corygrant/dingoPDM/docs/images/DingoPDM_v7_1_Case.png

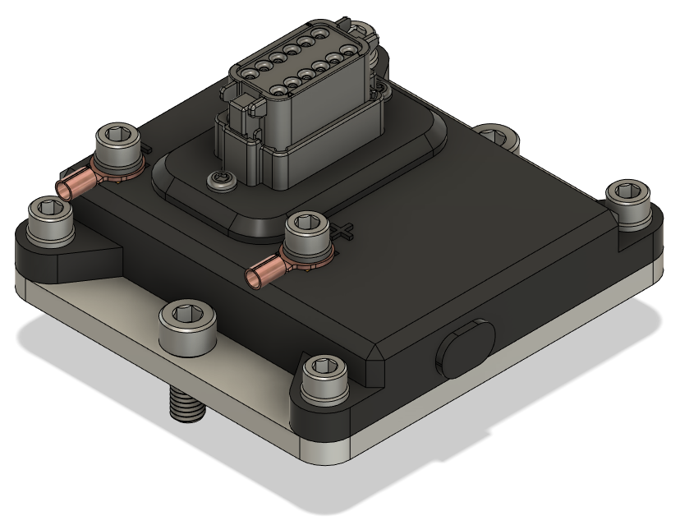
docs/images/DingoPDM_v7_1_Case.png
