corygrant/dingoPDM/docs/images/DingoPDM_v7_1_CaseBottom.png

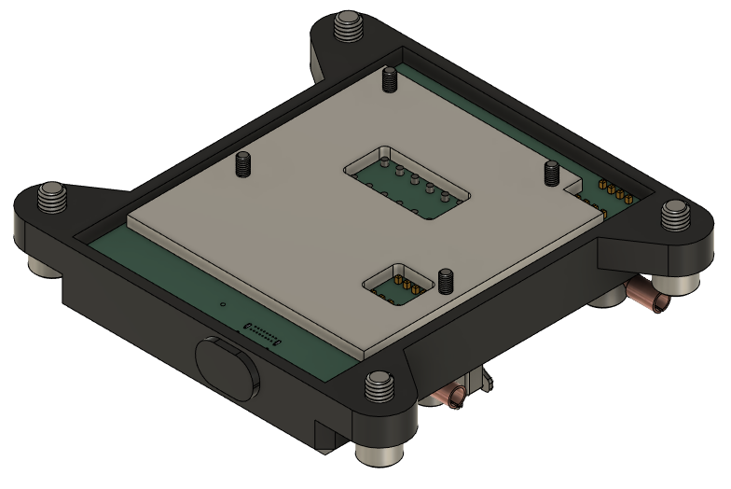
docs/images/DingoPDM_v7_1_CaseBottom.png
