corygrant/dingoPDM/docs/images/DingoPDMBottom_V7.png

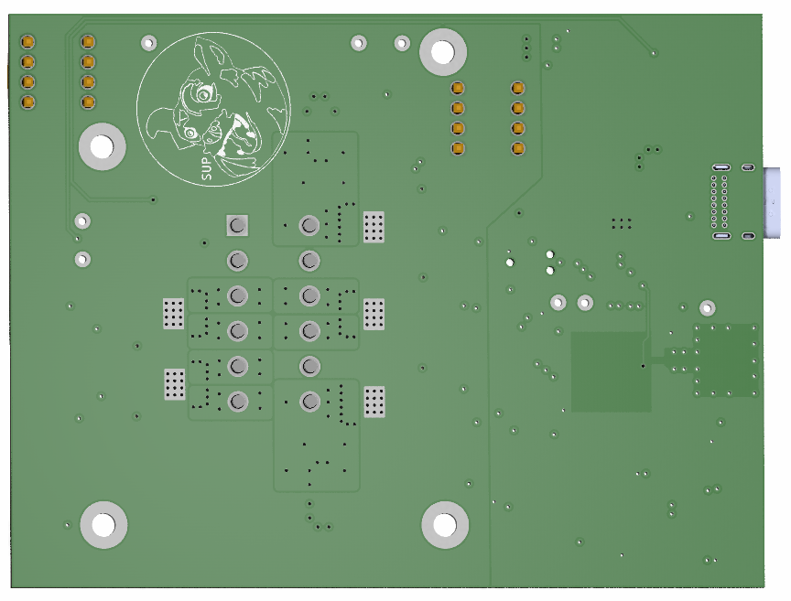
docs/images/DingoPDMBottom_V7.png
