corygrant/dingoPDM/docs/images/DingoPDMTop_V7_2.png

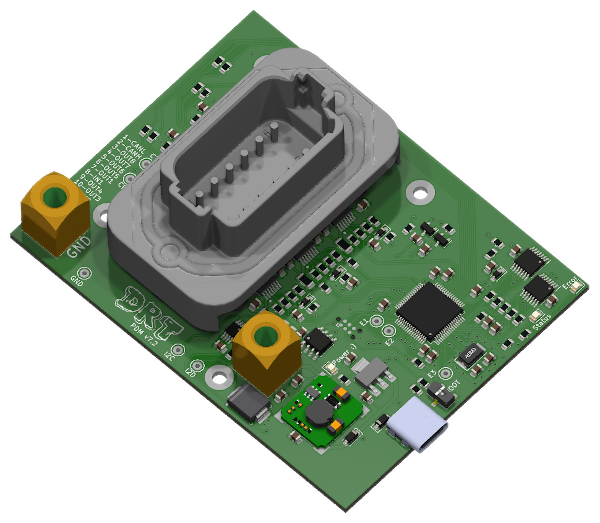
docs/images/DingoPDMTop_V7_2.png
