corygrant/dingoPDM/Export/V7.5/Case/Enclosure - paleppp/info.png

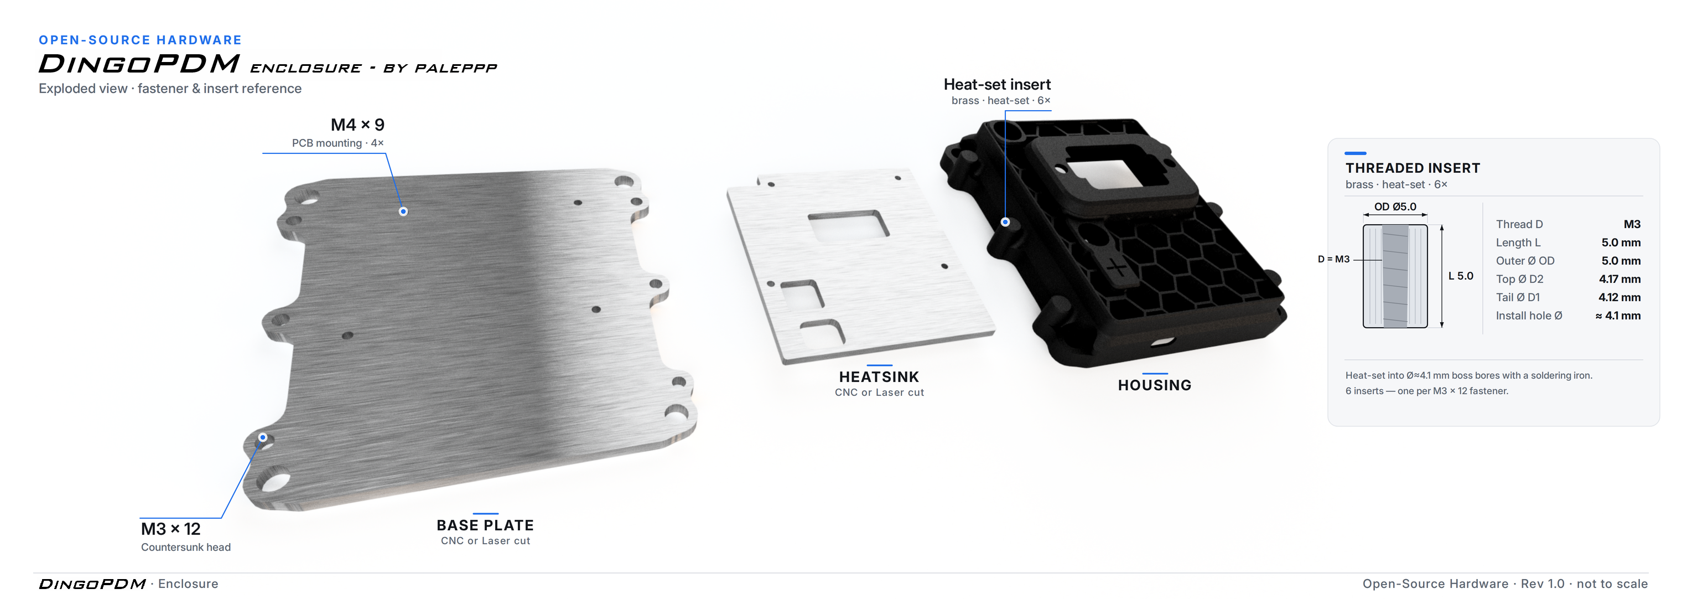
Export/V7.5/Case/Enclosure - paleppp/info.png
