corygrant/dingoPDM/DingoPDM/Models/User Library-DO-214AC SMA.STEP

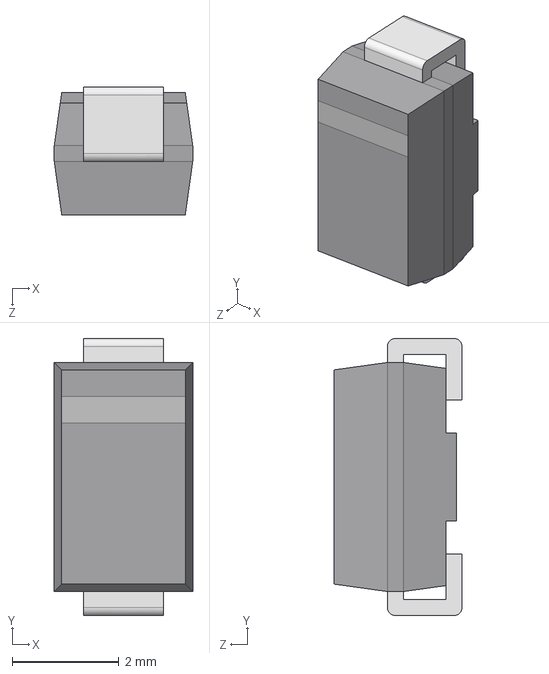
[picture p45: CAD file, 2023-09-12]
DingoPDM/Models/User Library-DO-214AC SMA.STEP
2.60 x 5.20 x 2.40 mm
