corygrant/dingoPDM/DingoPDM/Models/User Library-sot-223.STEP

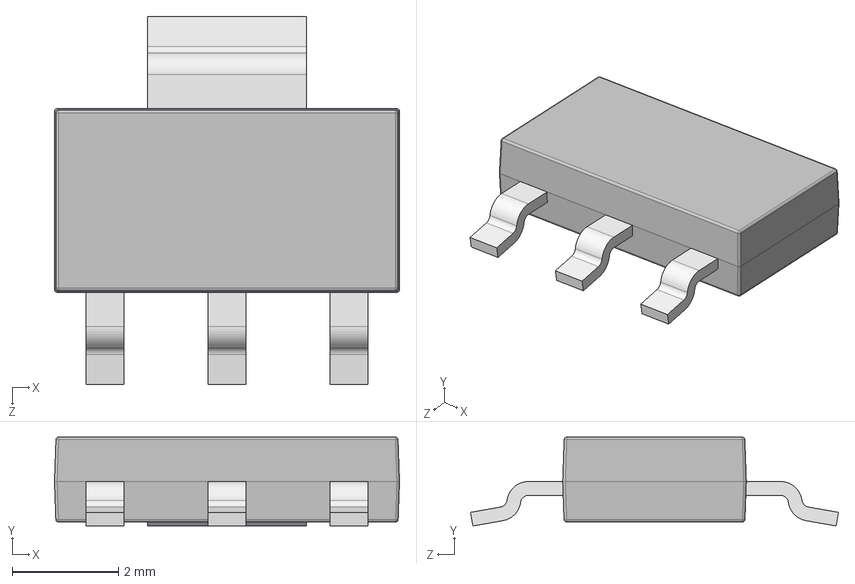
[picture p46: CAD file, 2023-09-12]
DingoPDM/Models/User Library-sot-223.STEP
6.50 x 1.67 x 6.93 mm
