corygrant/dingoPDM/DingoPDM/Models/USB4085-GF-A--3DModel-STEP-56544.STEP

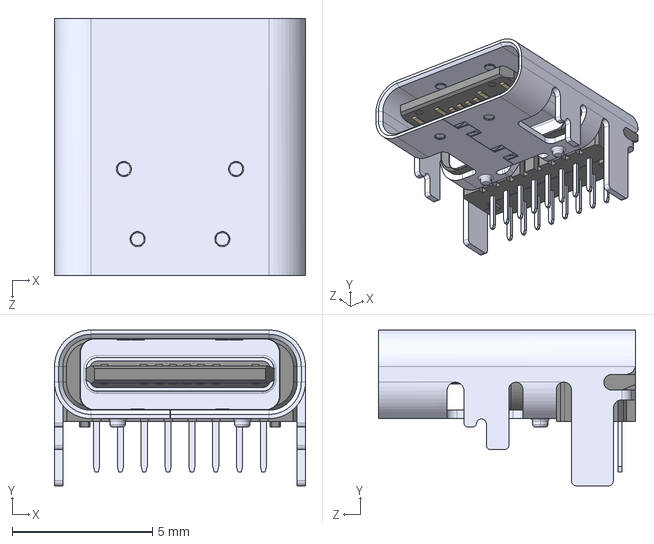
[picture p47: CAD file, 2023-09-12]
DingoPDM/Models/USB4085-GF-A--3DModel-STEP-56544.STEP
8.95 x 5.56 x 9.17 mm
