corygrant/dingoPDM/DingoPDM/Models/c-dt15-12pa-e-3d.stp

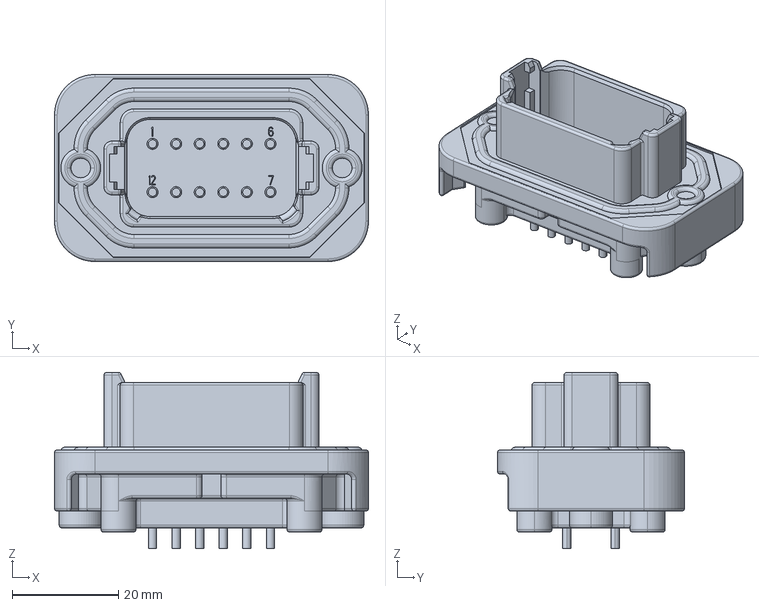
[picture p48: CAD file, 2023-09-12]
DingoPDM/Models/c-dt15-12pa-e-3d.stp
59.2 x 35.3 x 33.2 mm
