corygrant/dingoPDM/DingoPDM/Models/User Library-DO-214AB SMC.STEP

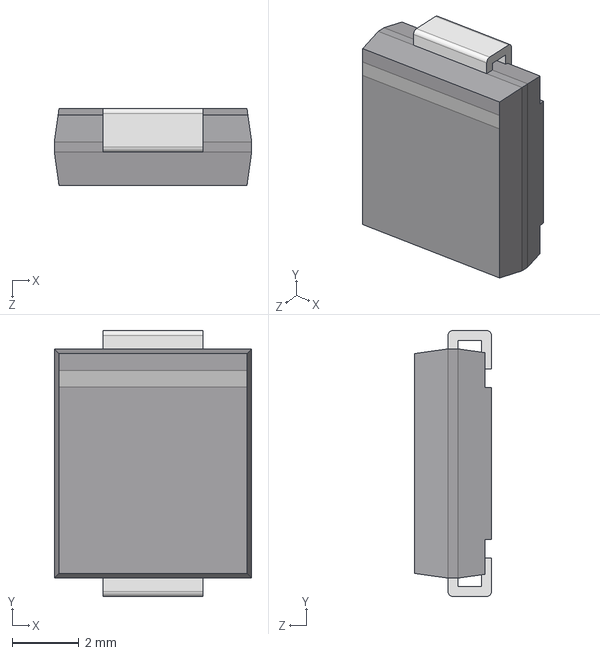
[picture p49: CAD file, 2023-09-12]
DingoPDM/Models/User Library-DO-214AB SMC.STEP
5.90 x 7.95 x 2.30 mm
