corygrant/dingoPDM/DingoPDM/Models/User Library-SOT23-3.step

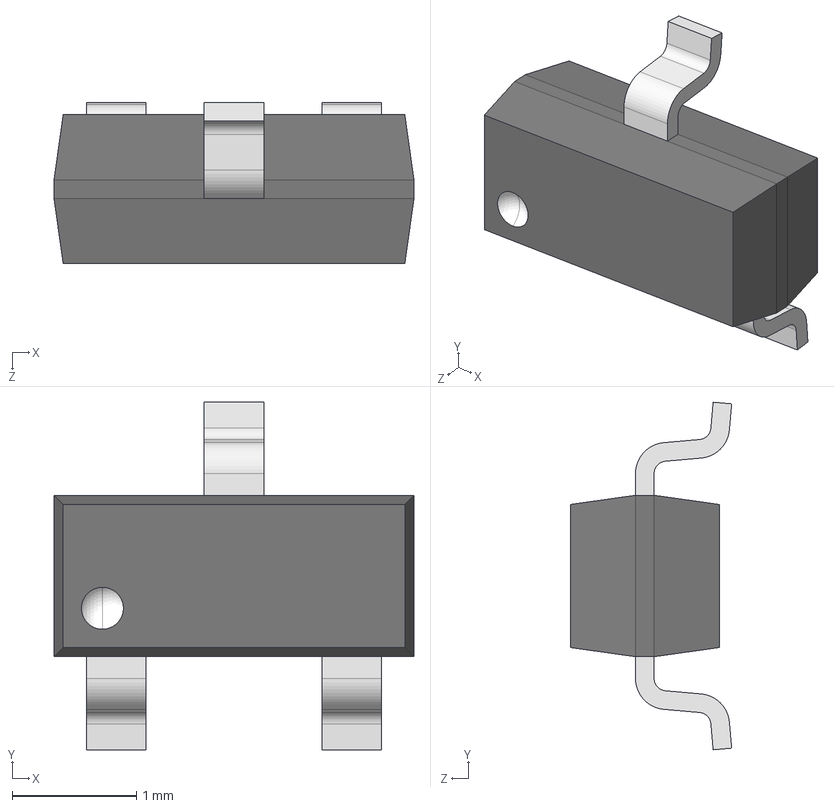
[picture p50: CAD file, 2023-09-12]
DingoPDM/Models/User Library-SOT23-3.step
2.90 x 2.80 x 1.30 mm
