corygrant/dingoPDM/Export/V7/DingoPDM_HW_V7_Dark.pdf

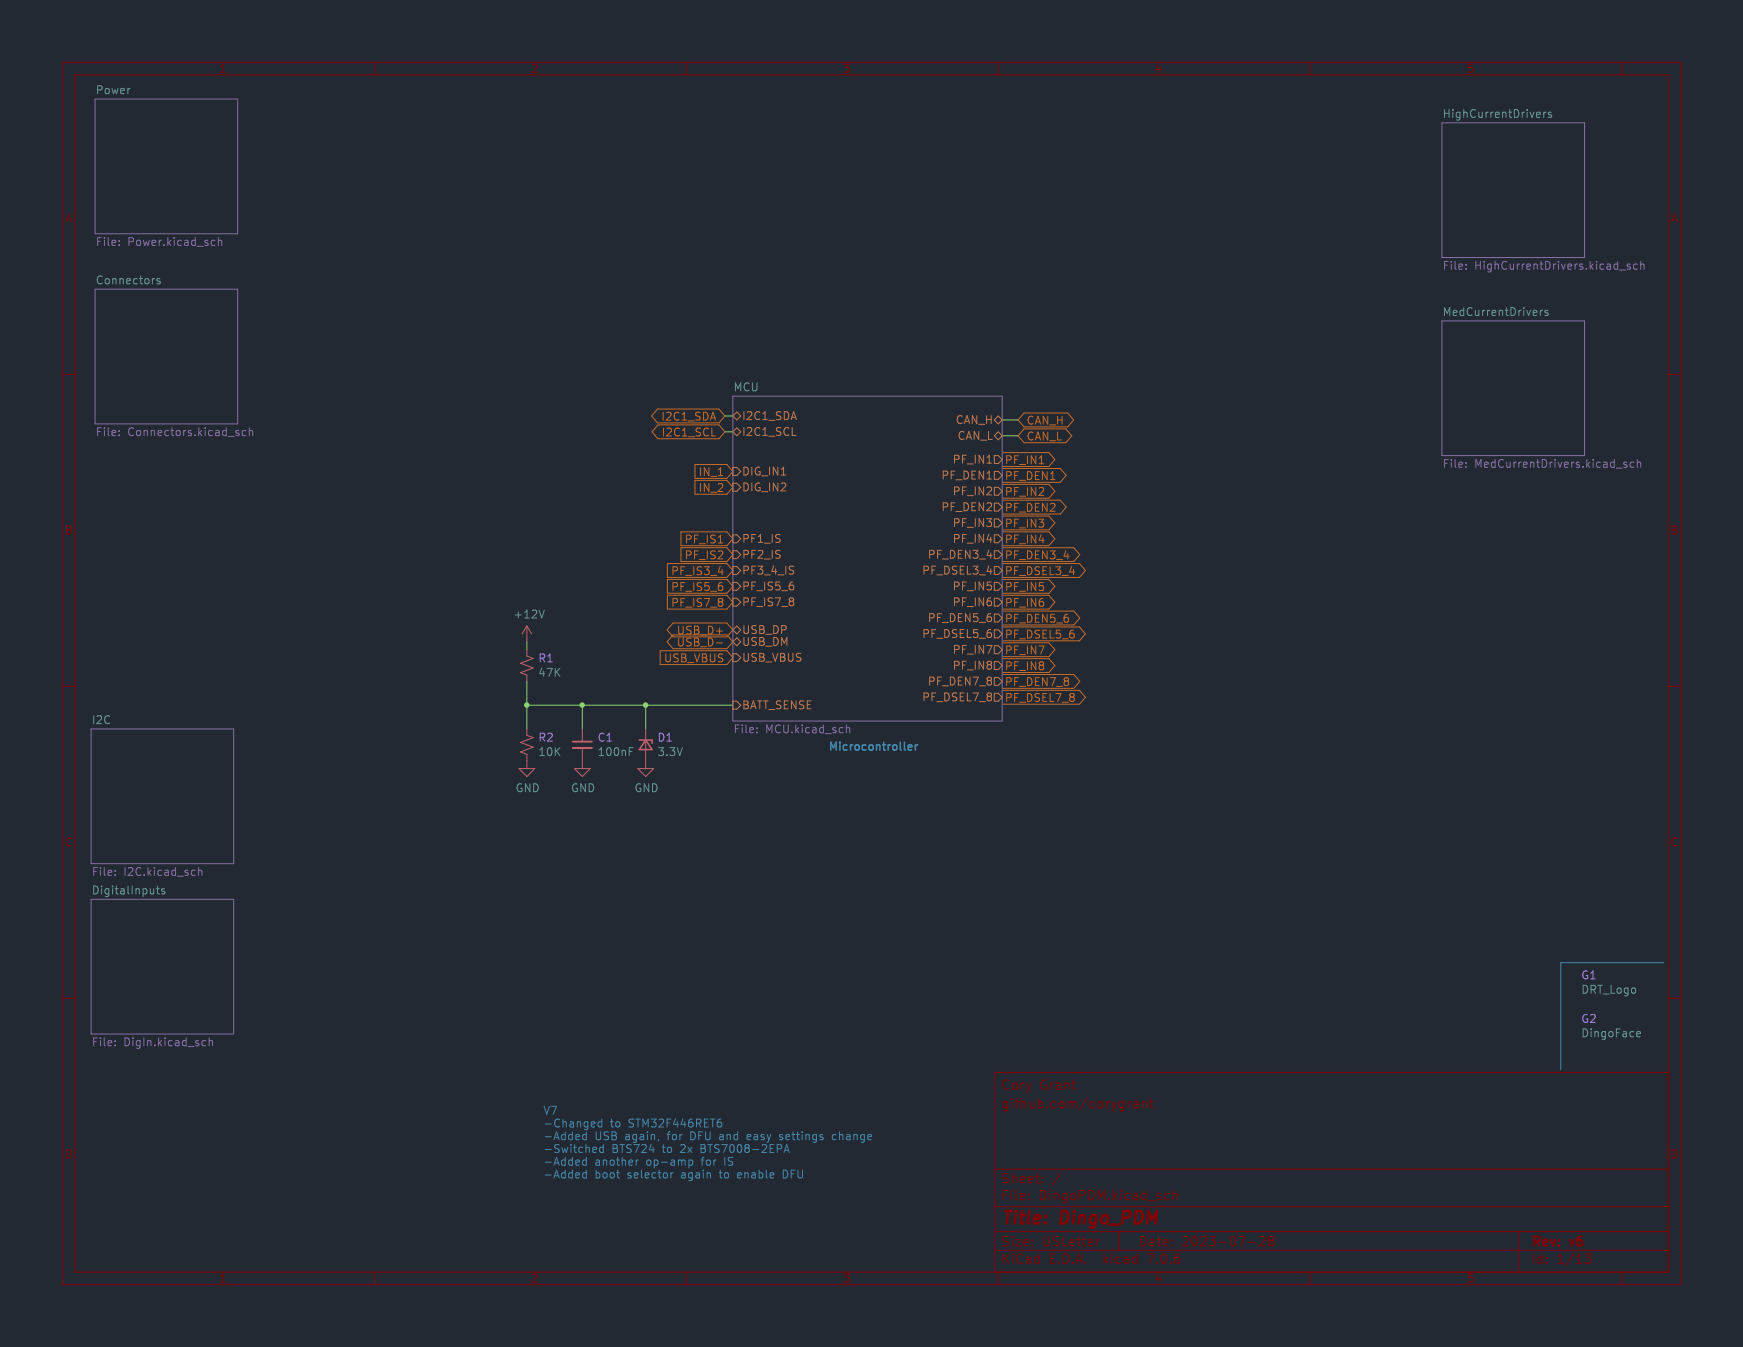
[picture p165: page 1]

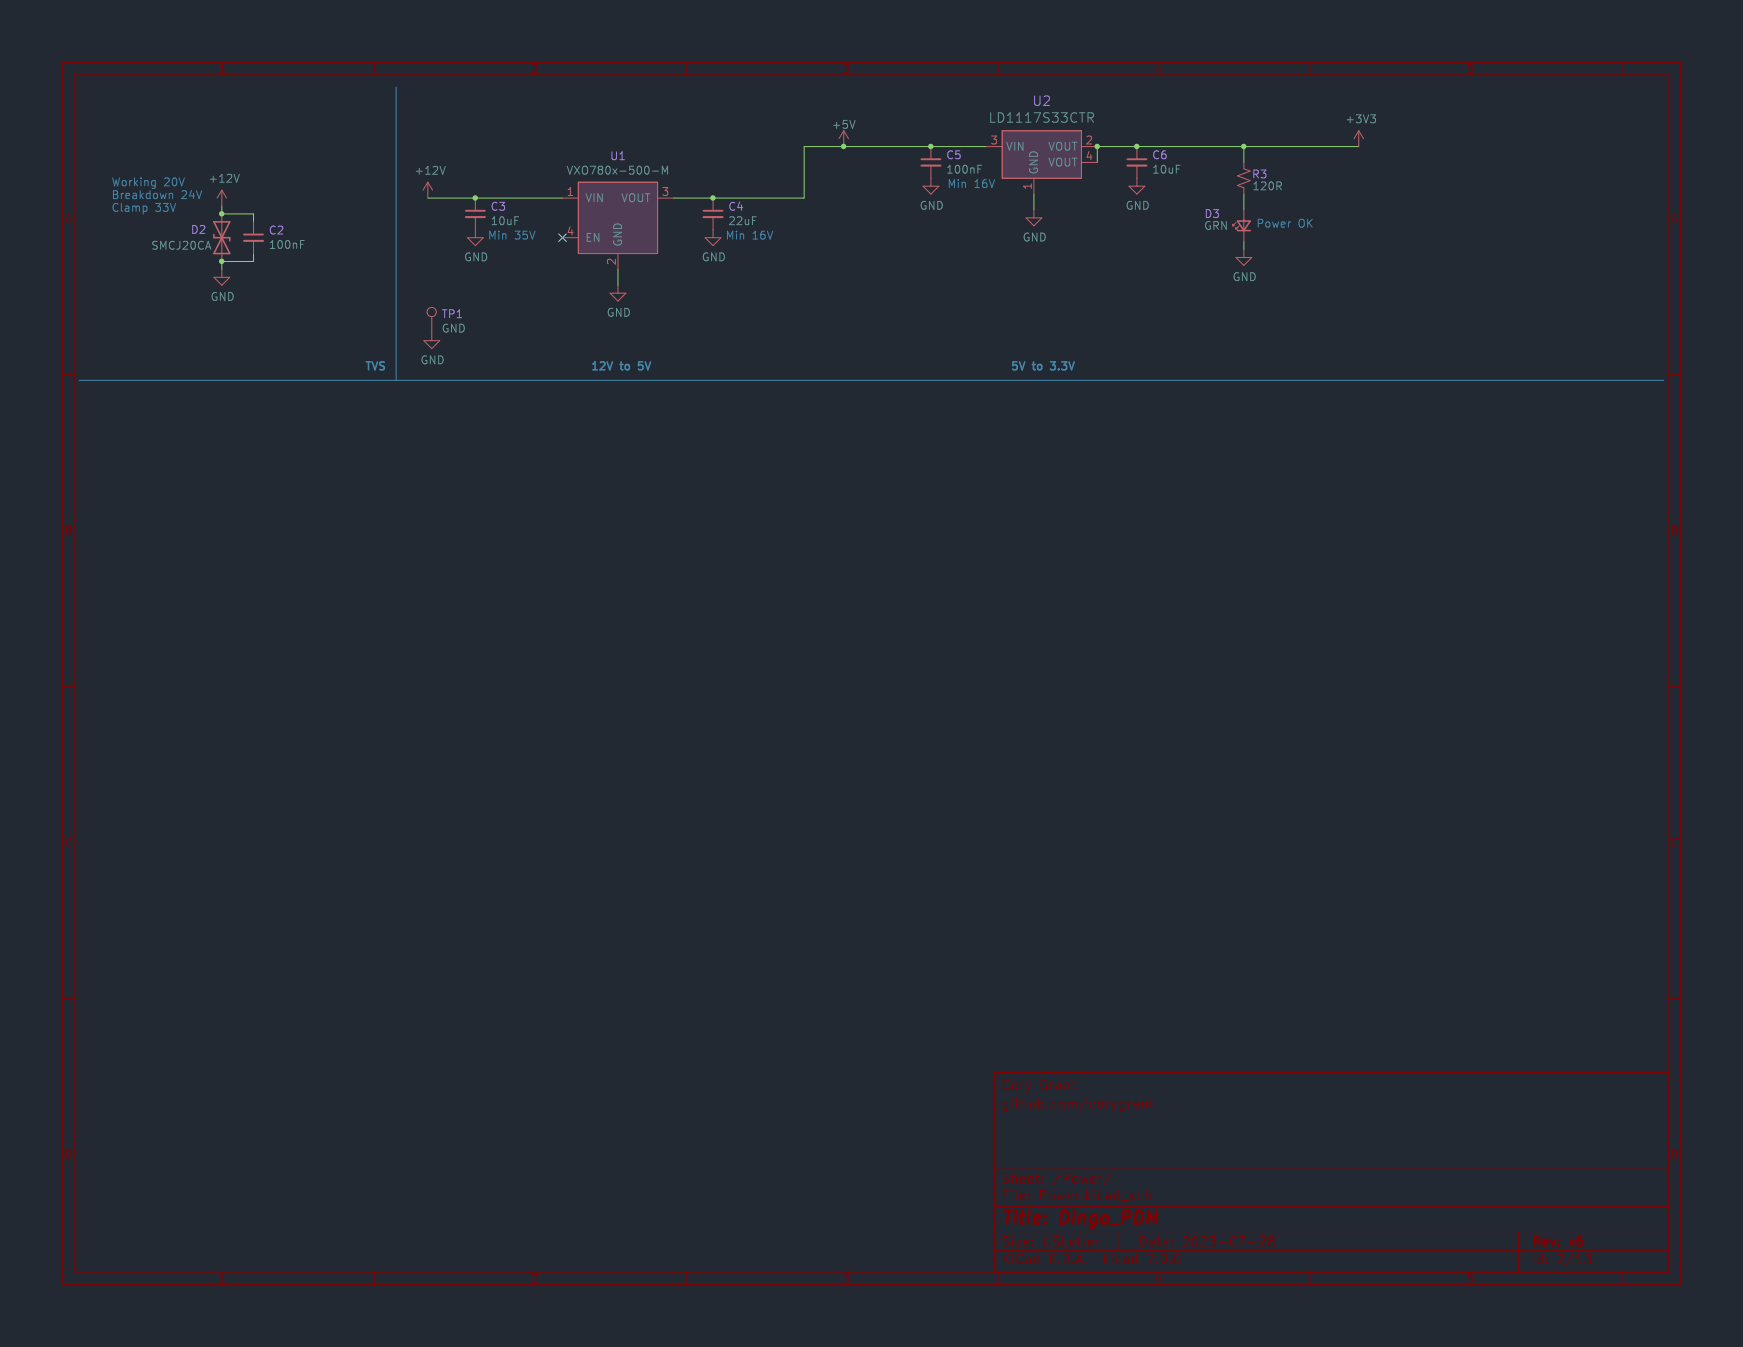
[picture p166: page 2]

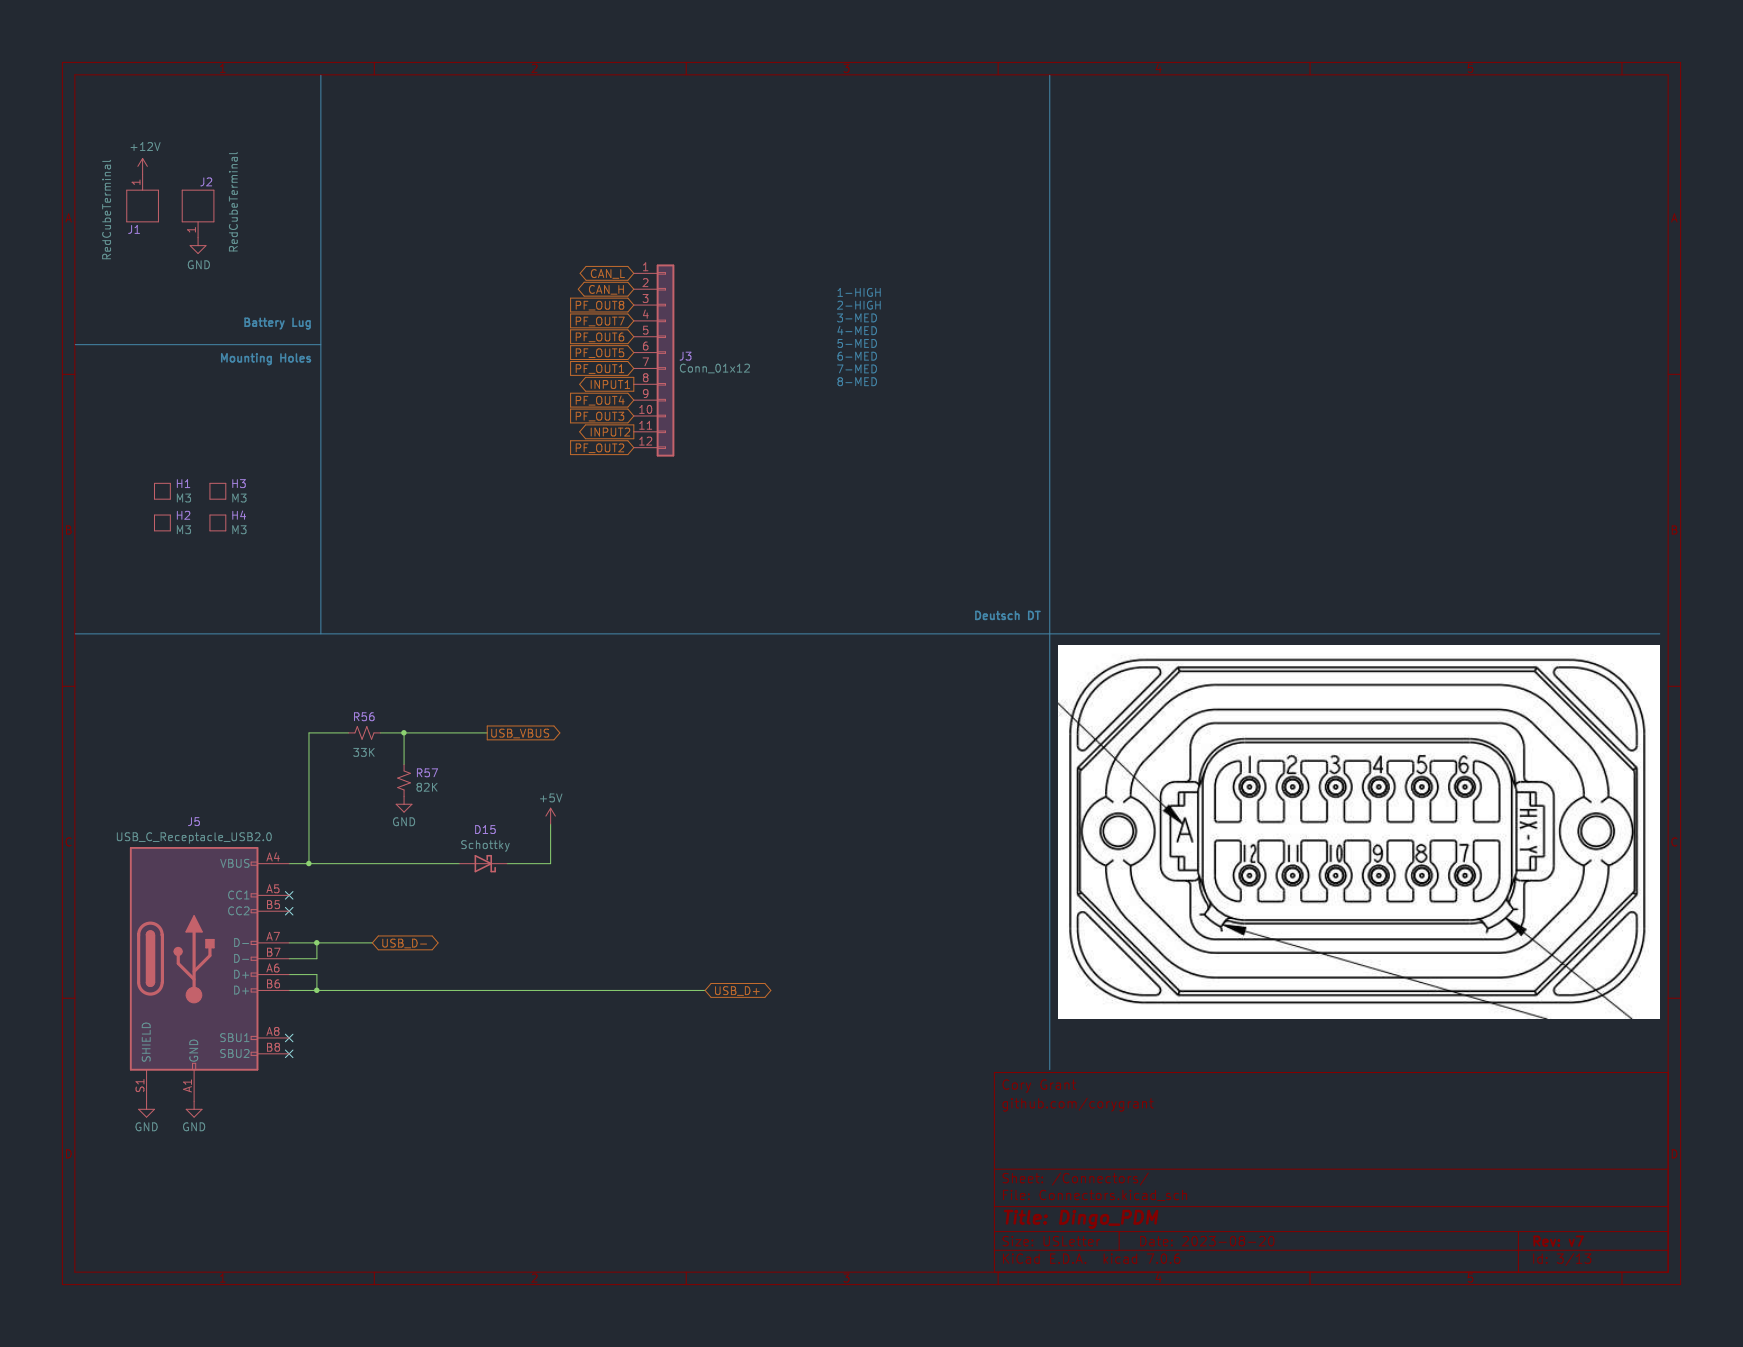
[picture p167: page 3]

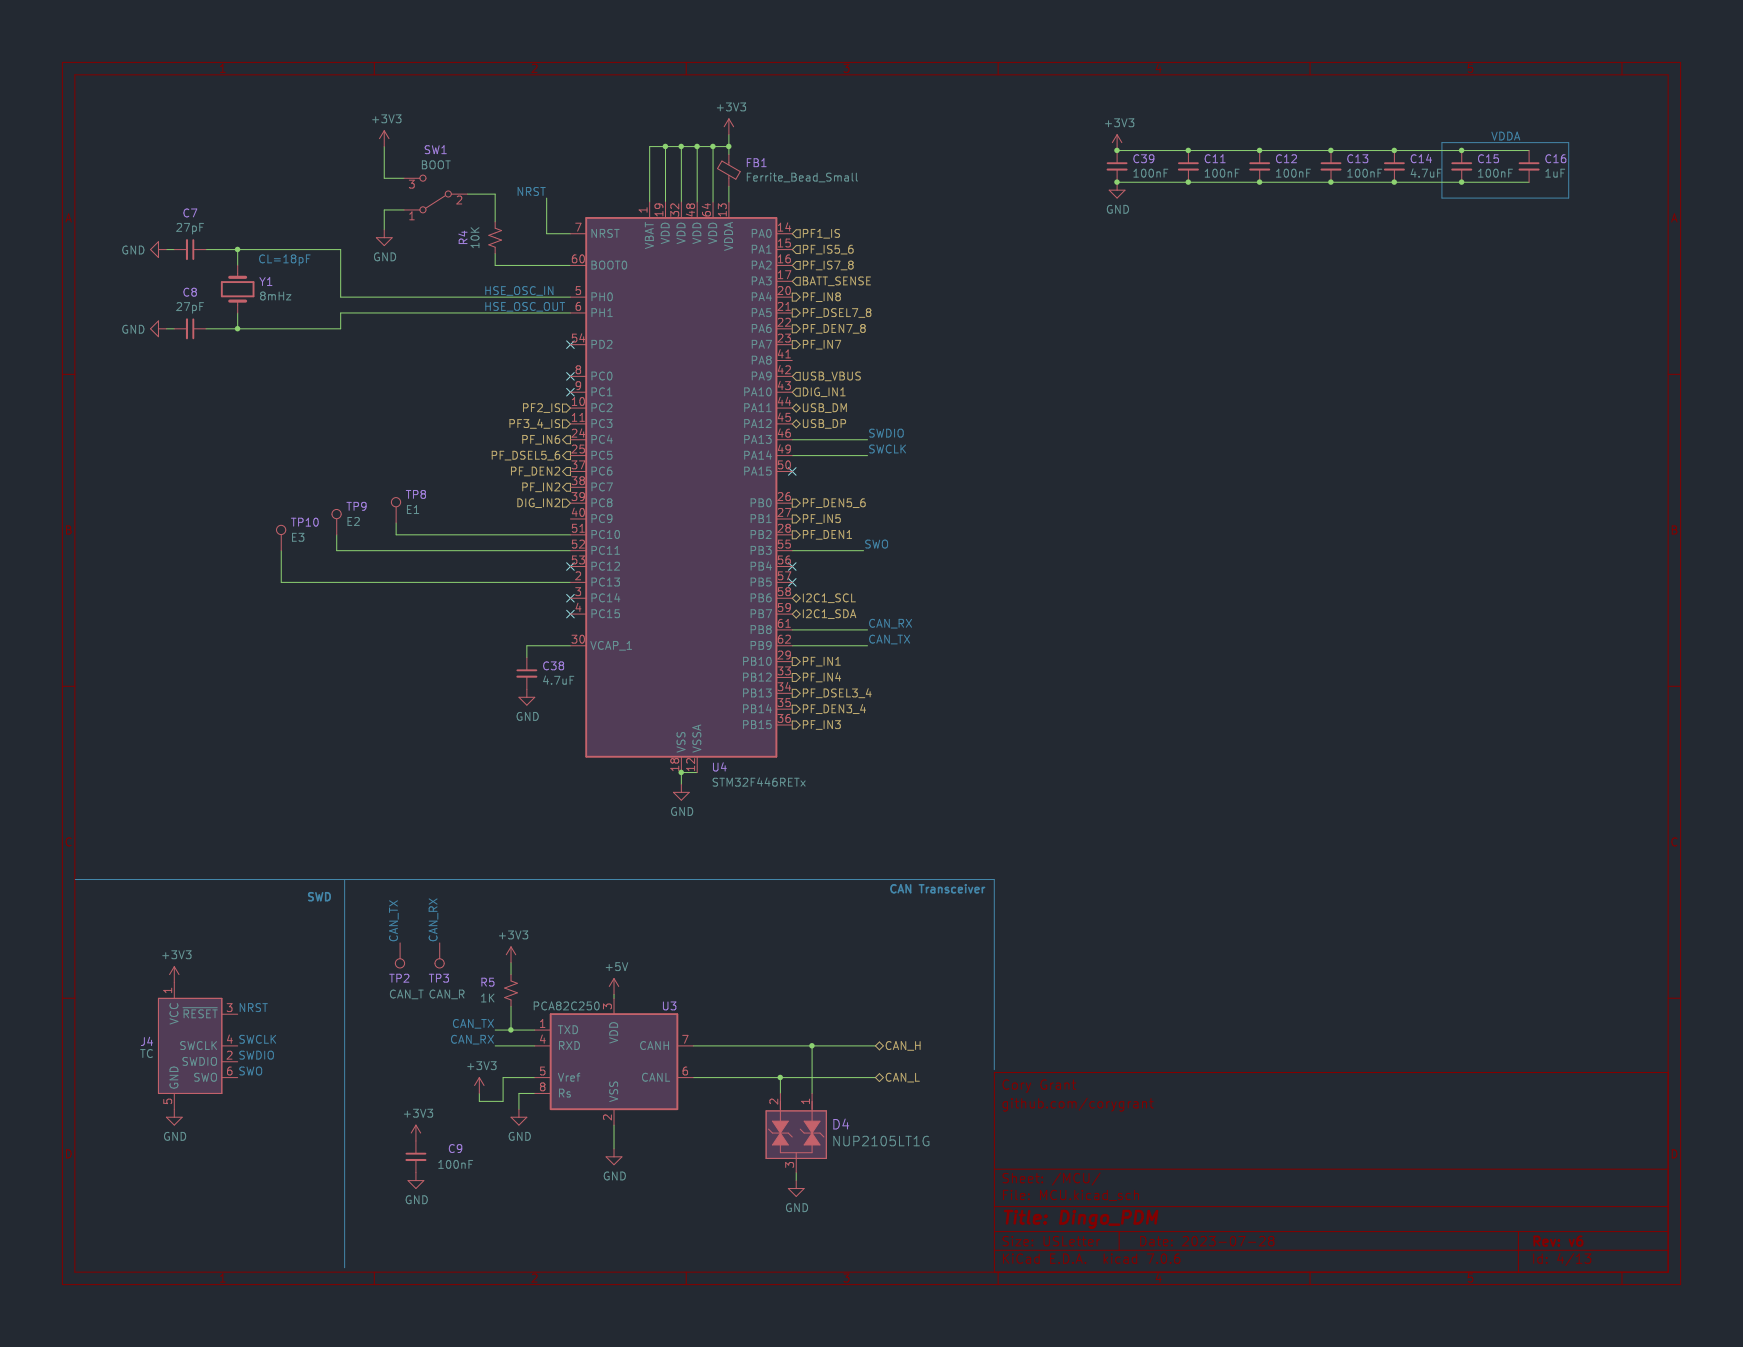
[picture p168: page 4]

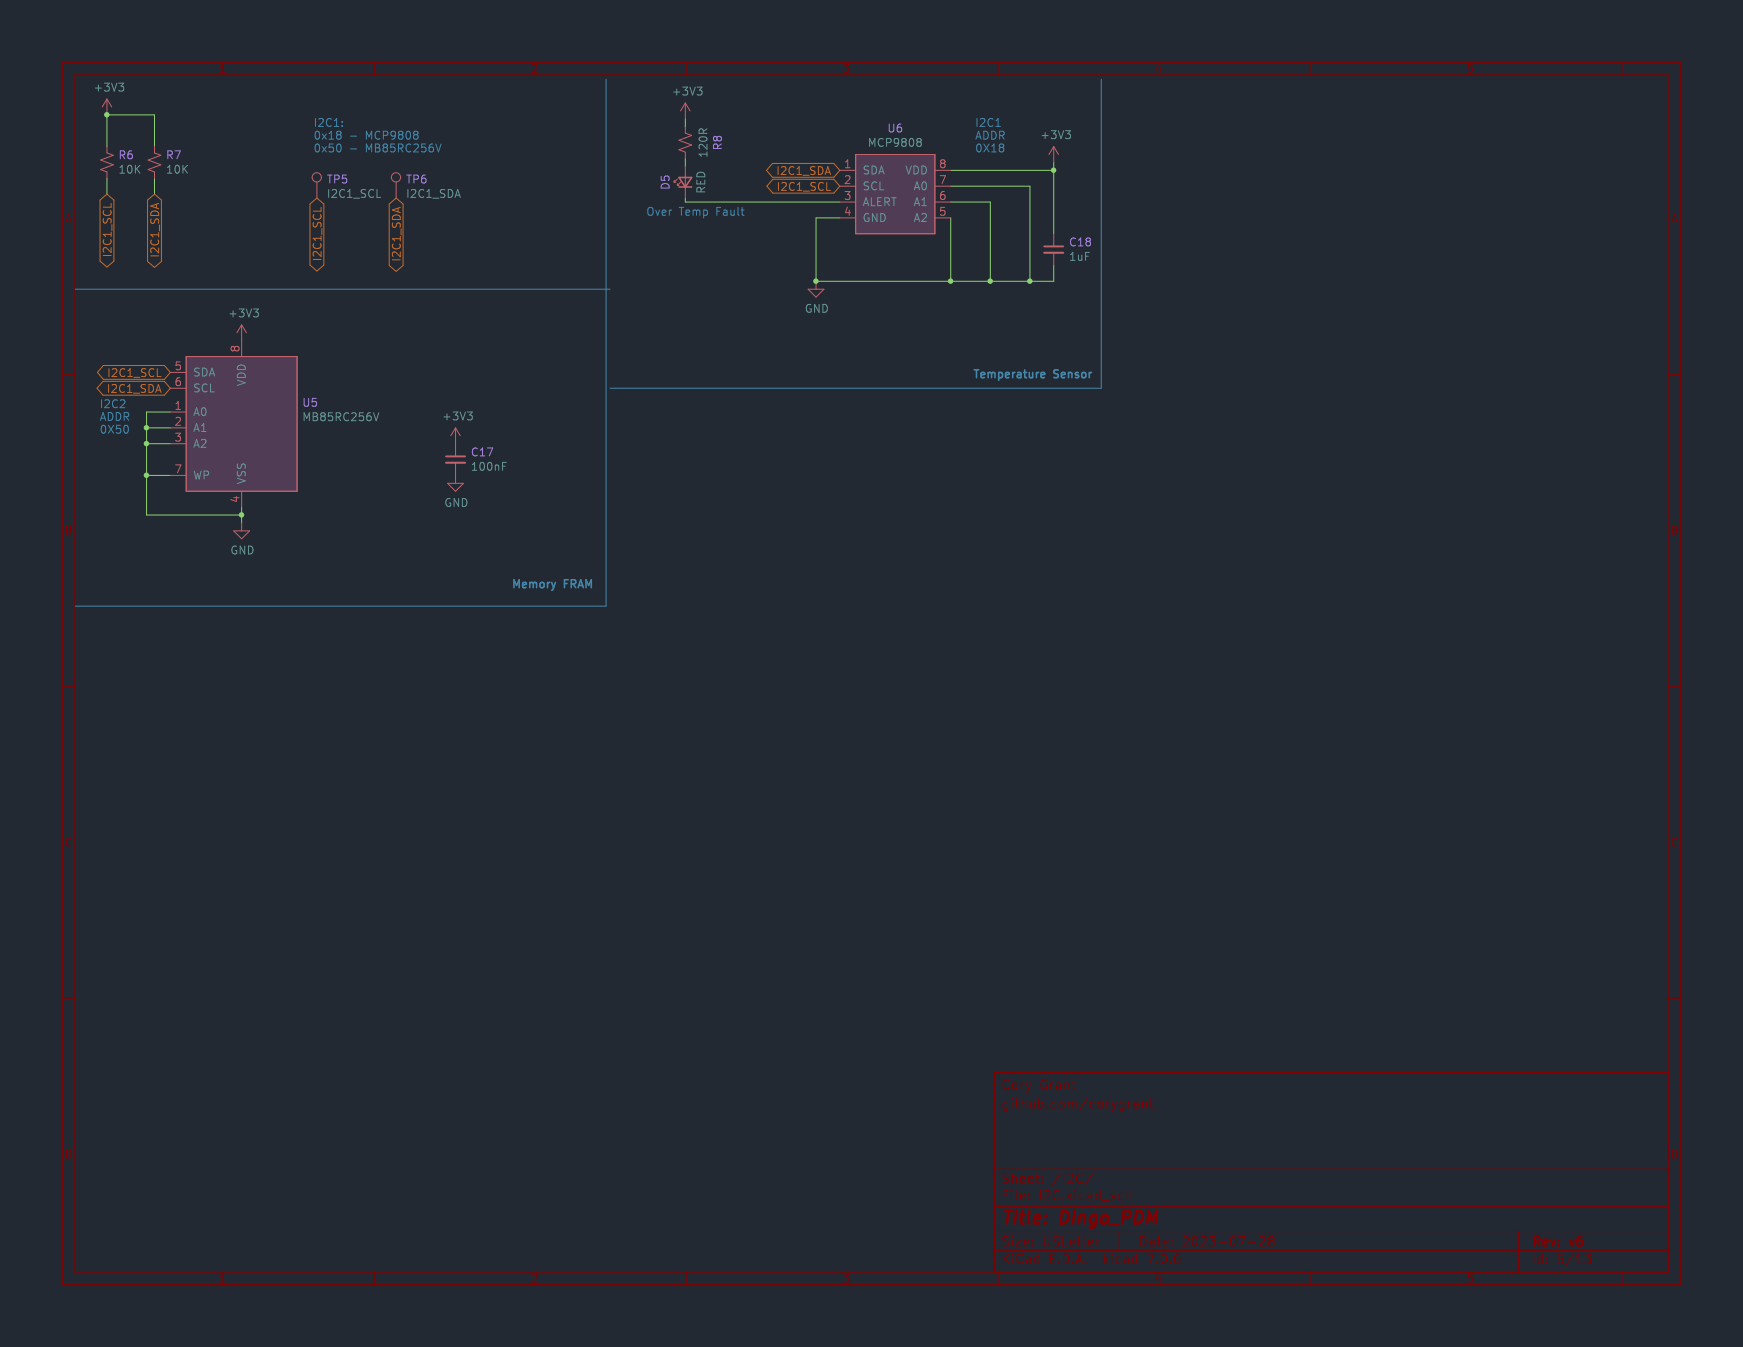
[picture p169: page 5]

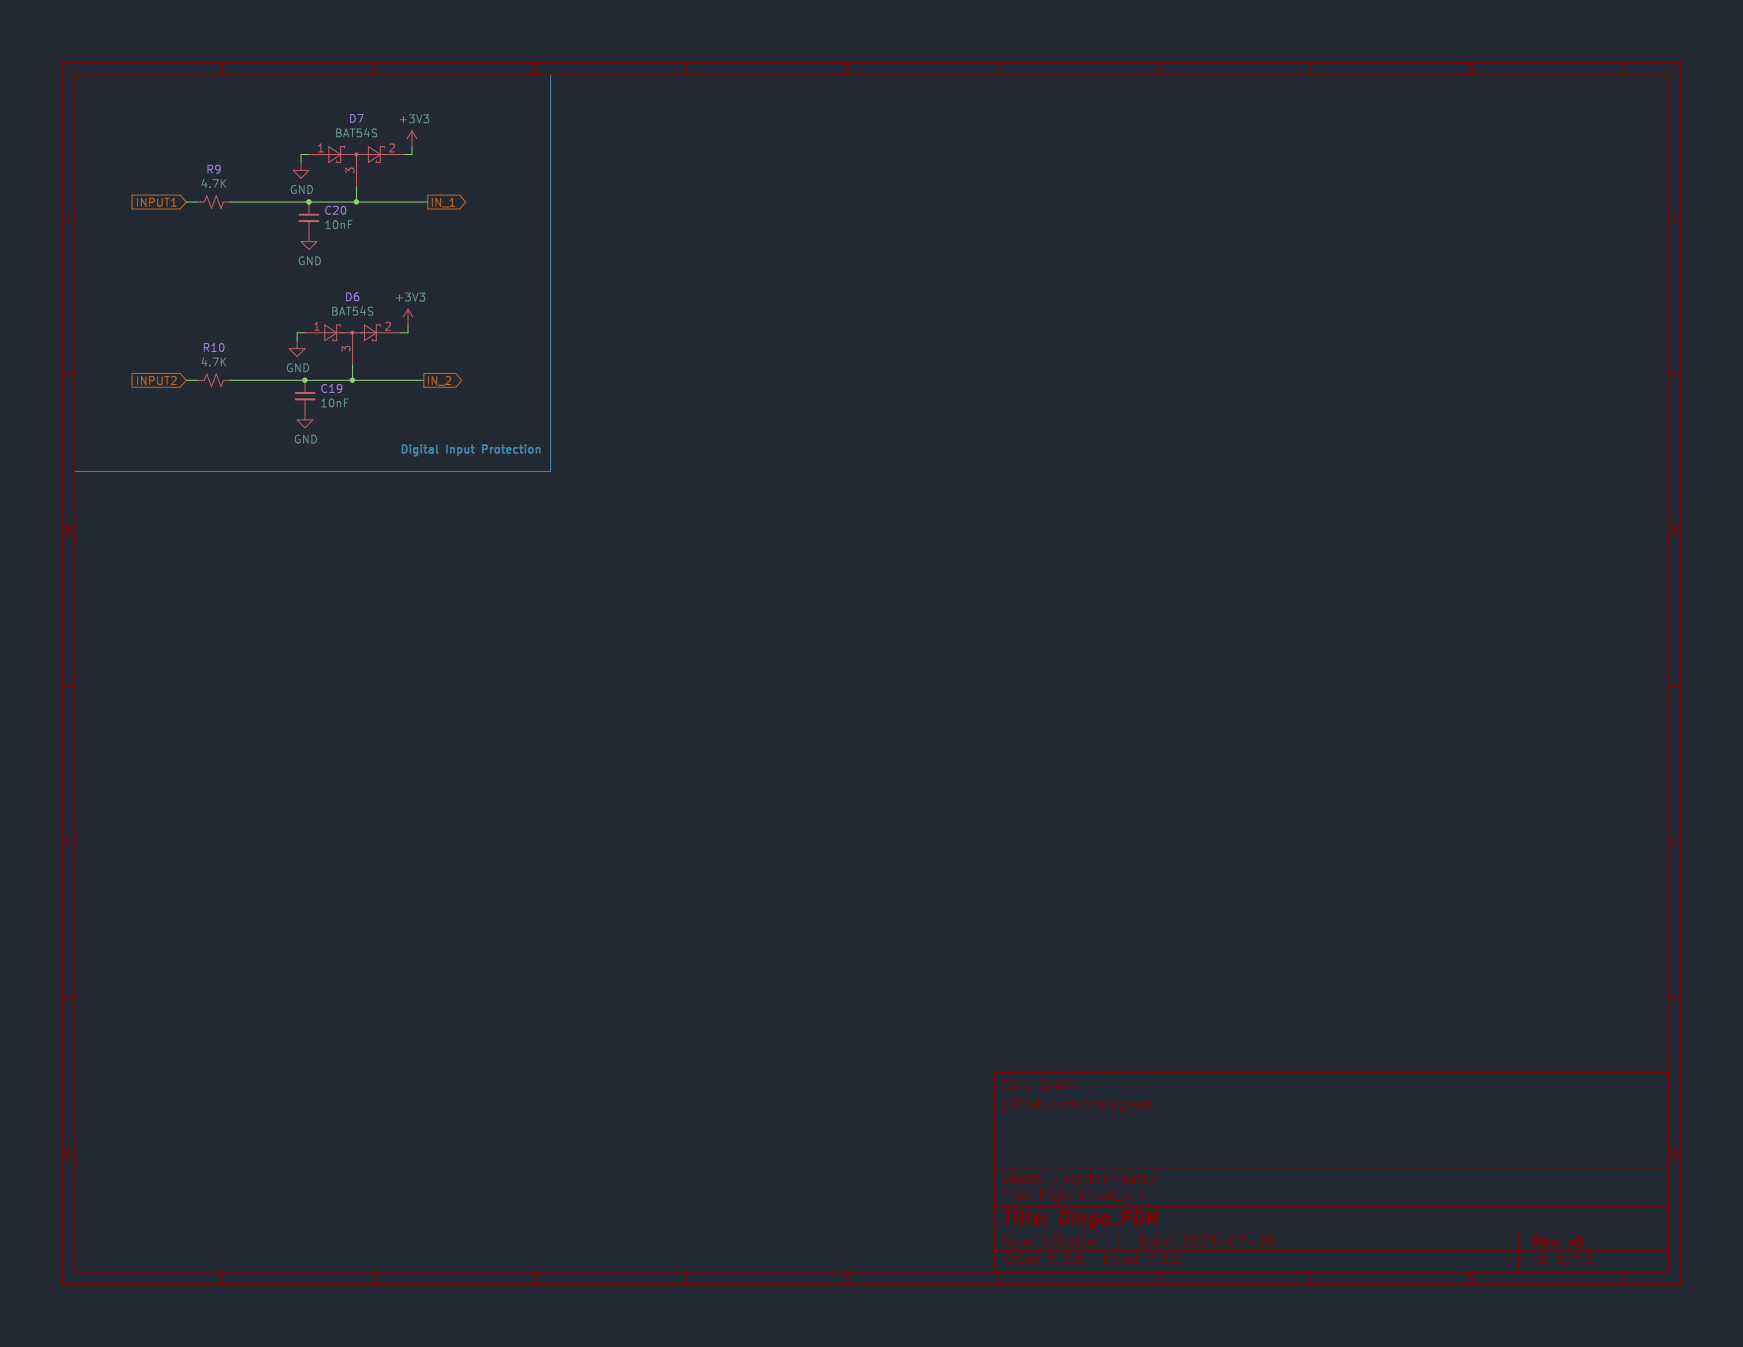
[picture p170: page 6]

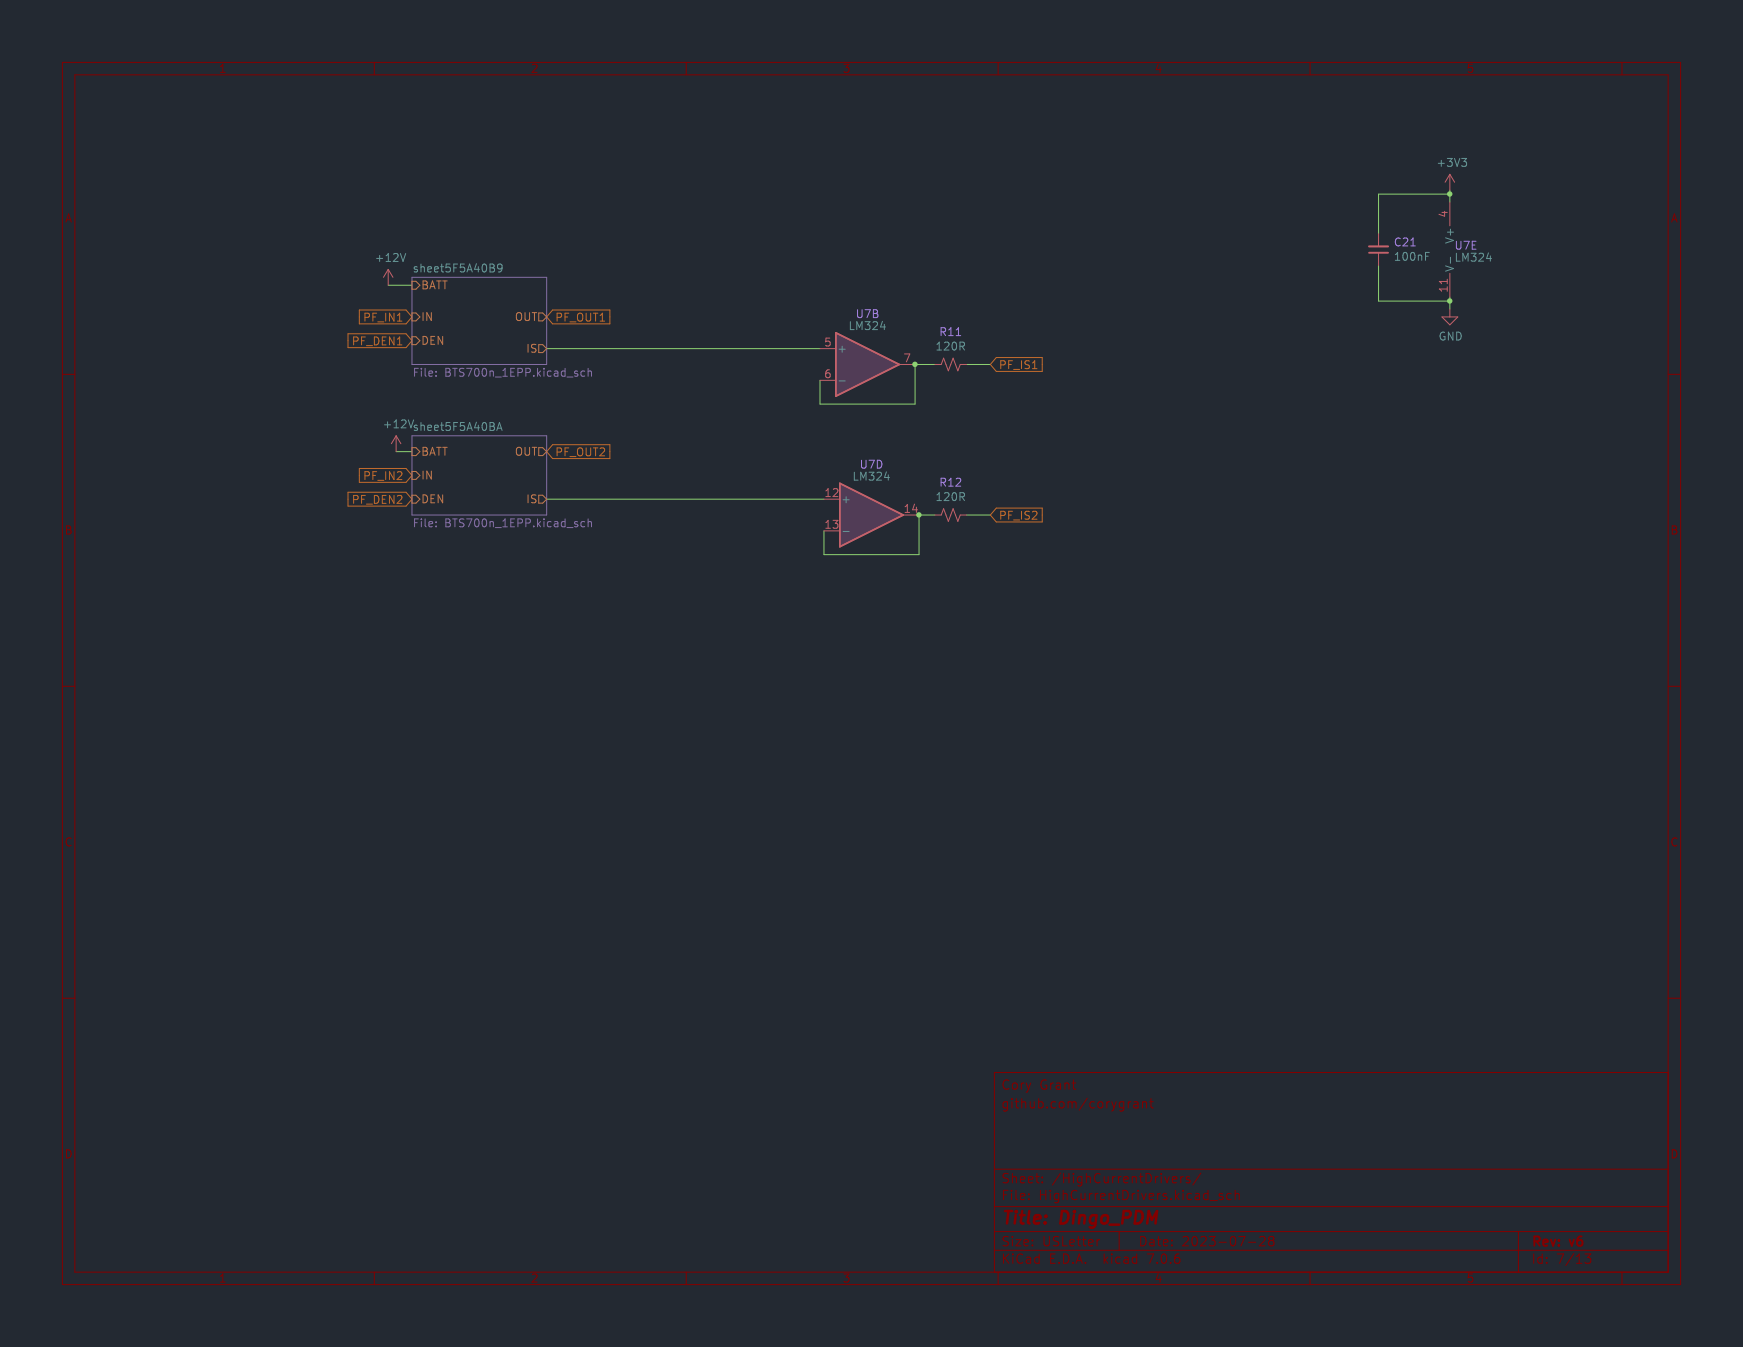
[picture p171: page 7]

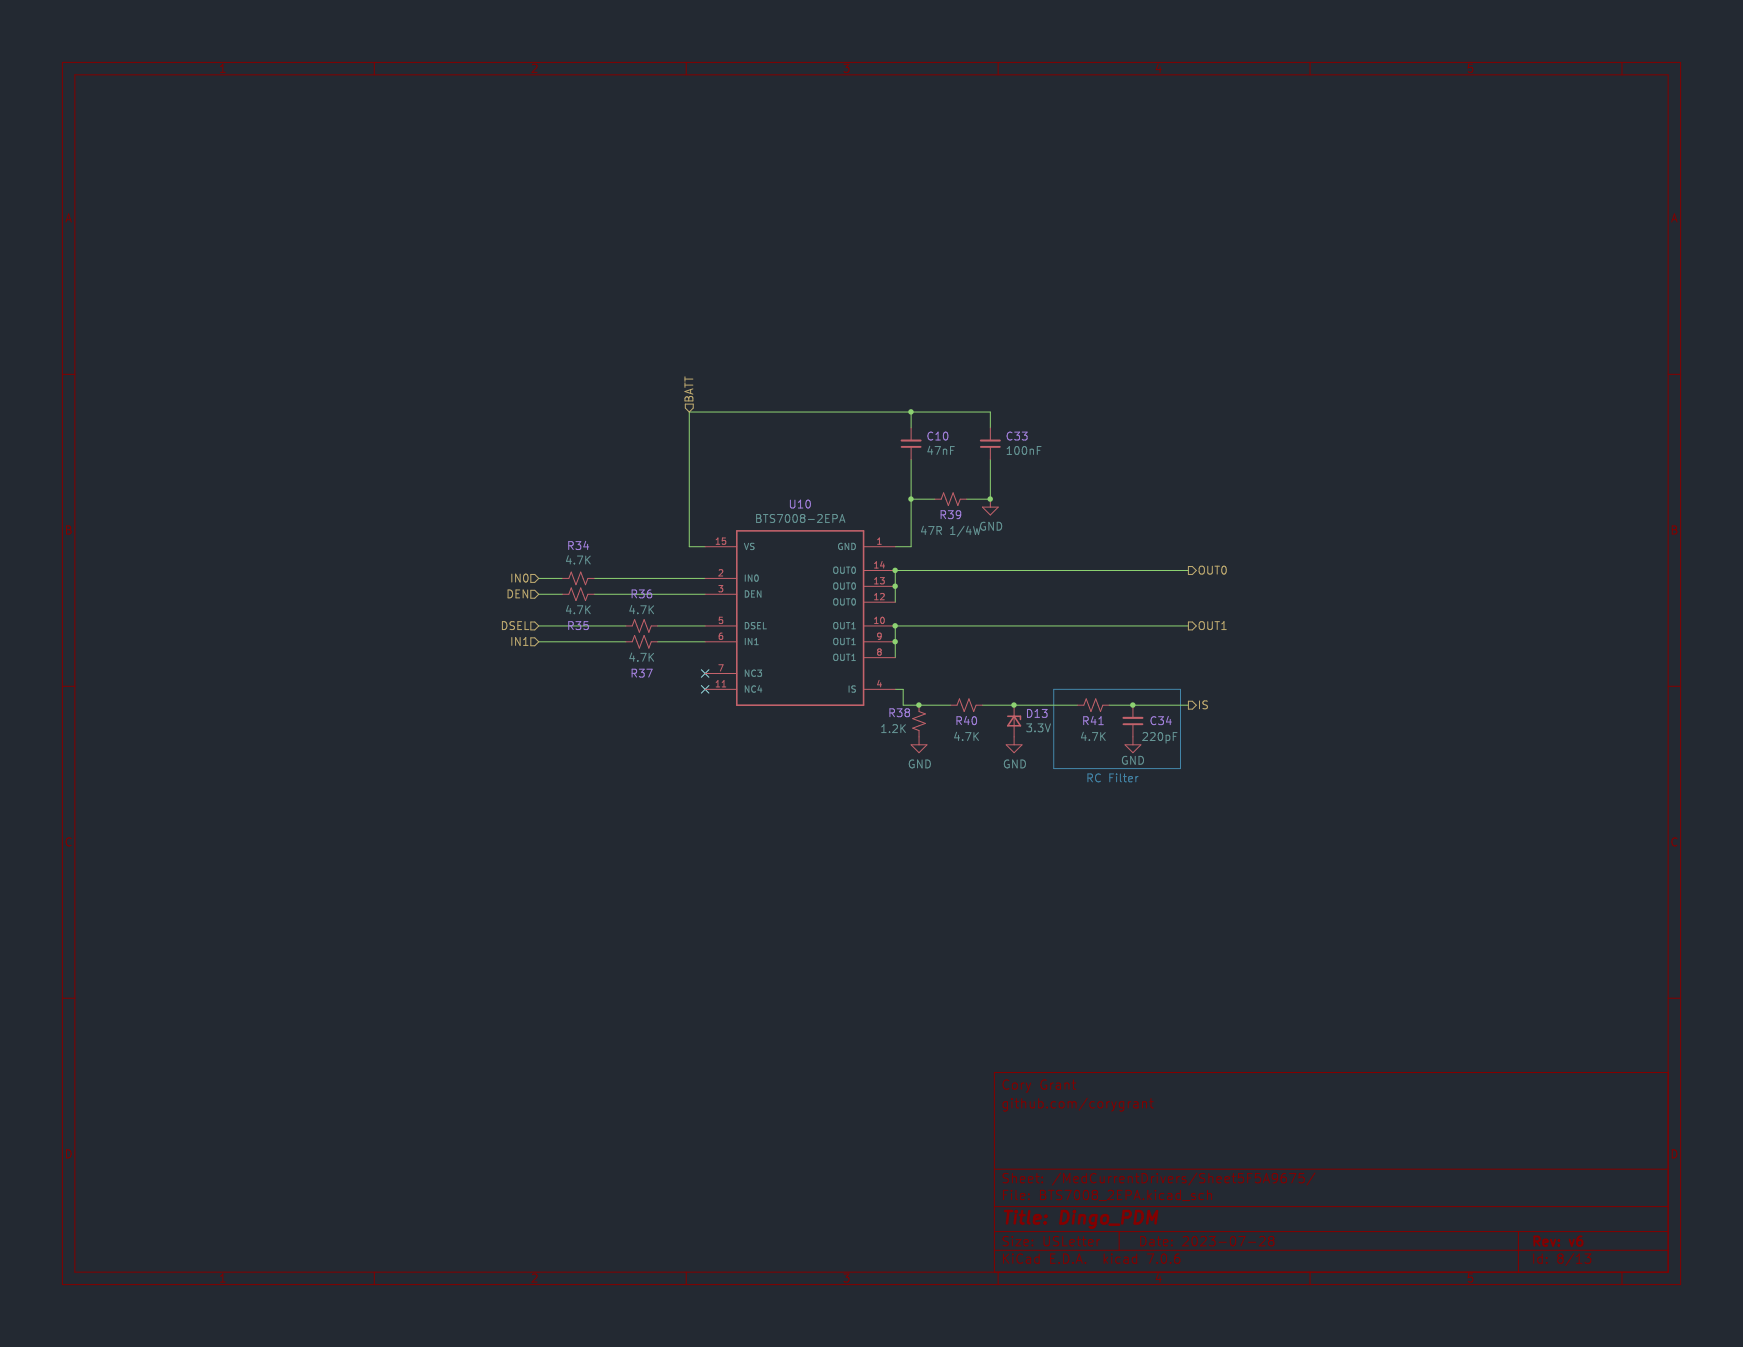
[picture p172: page 8]

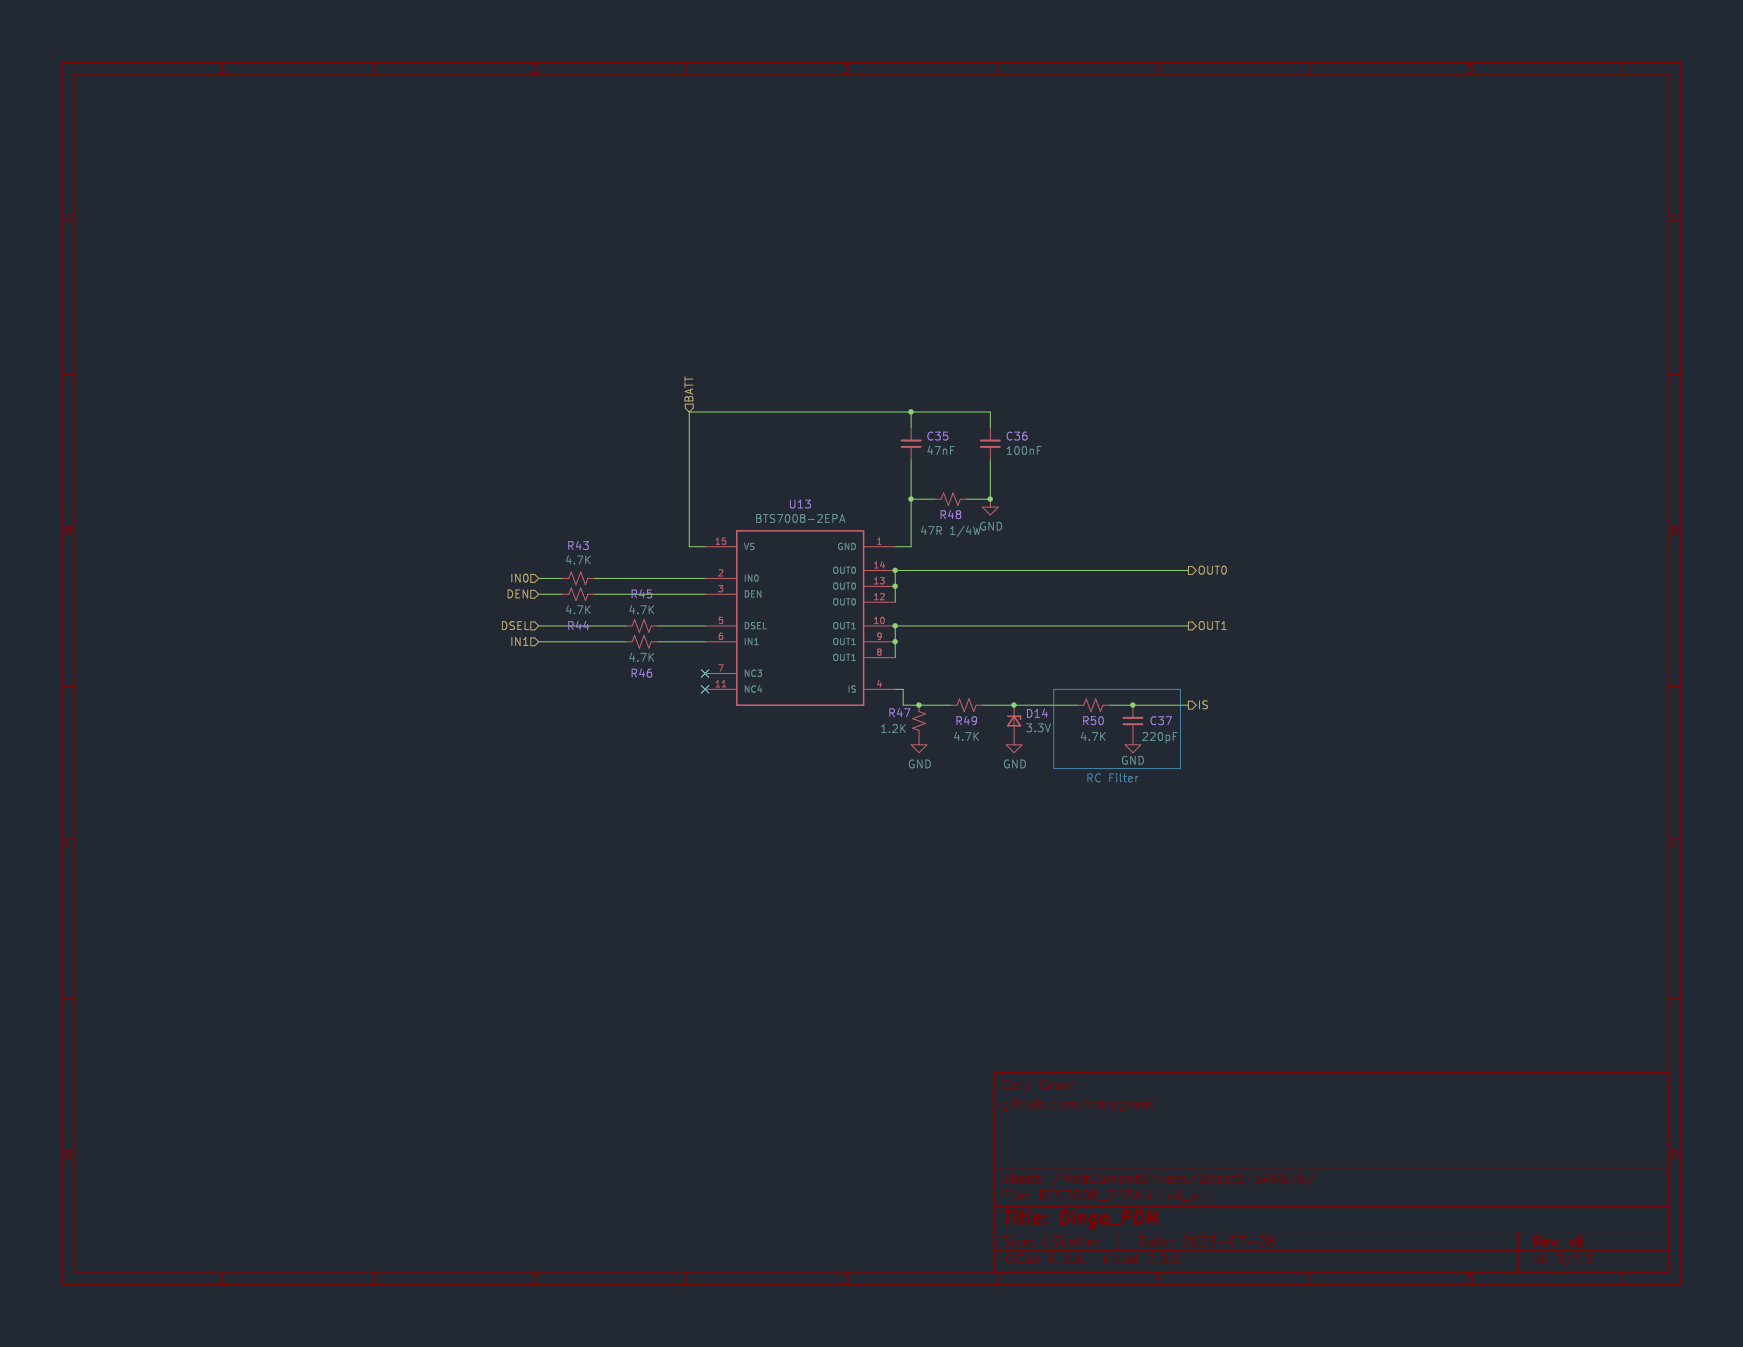
[picture p173: page 9]

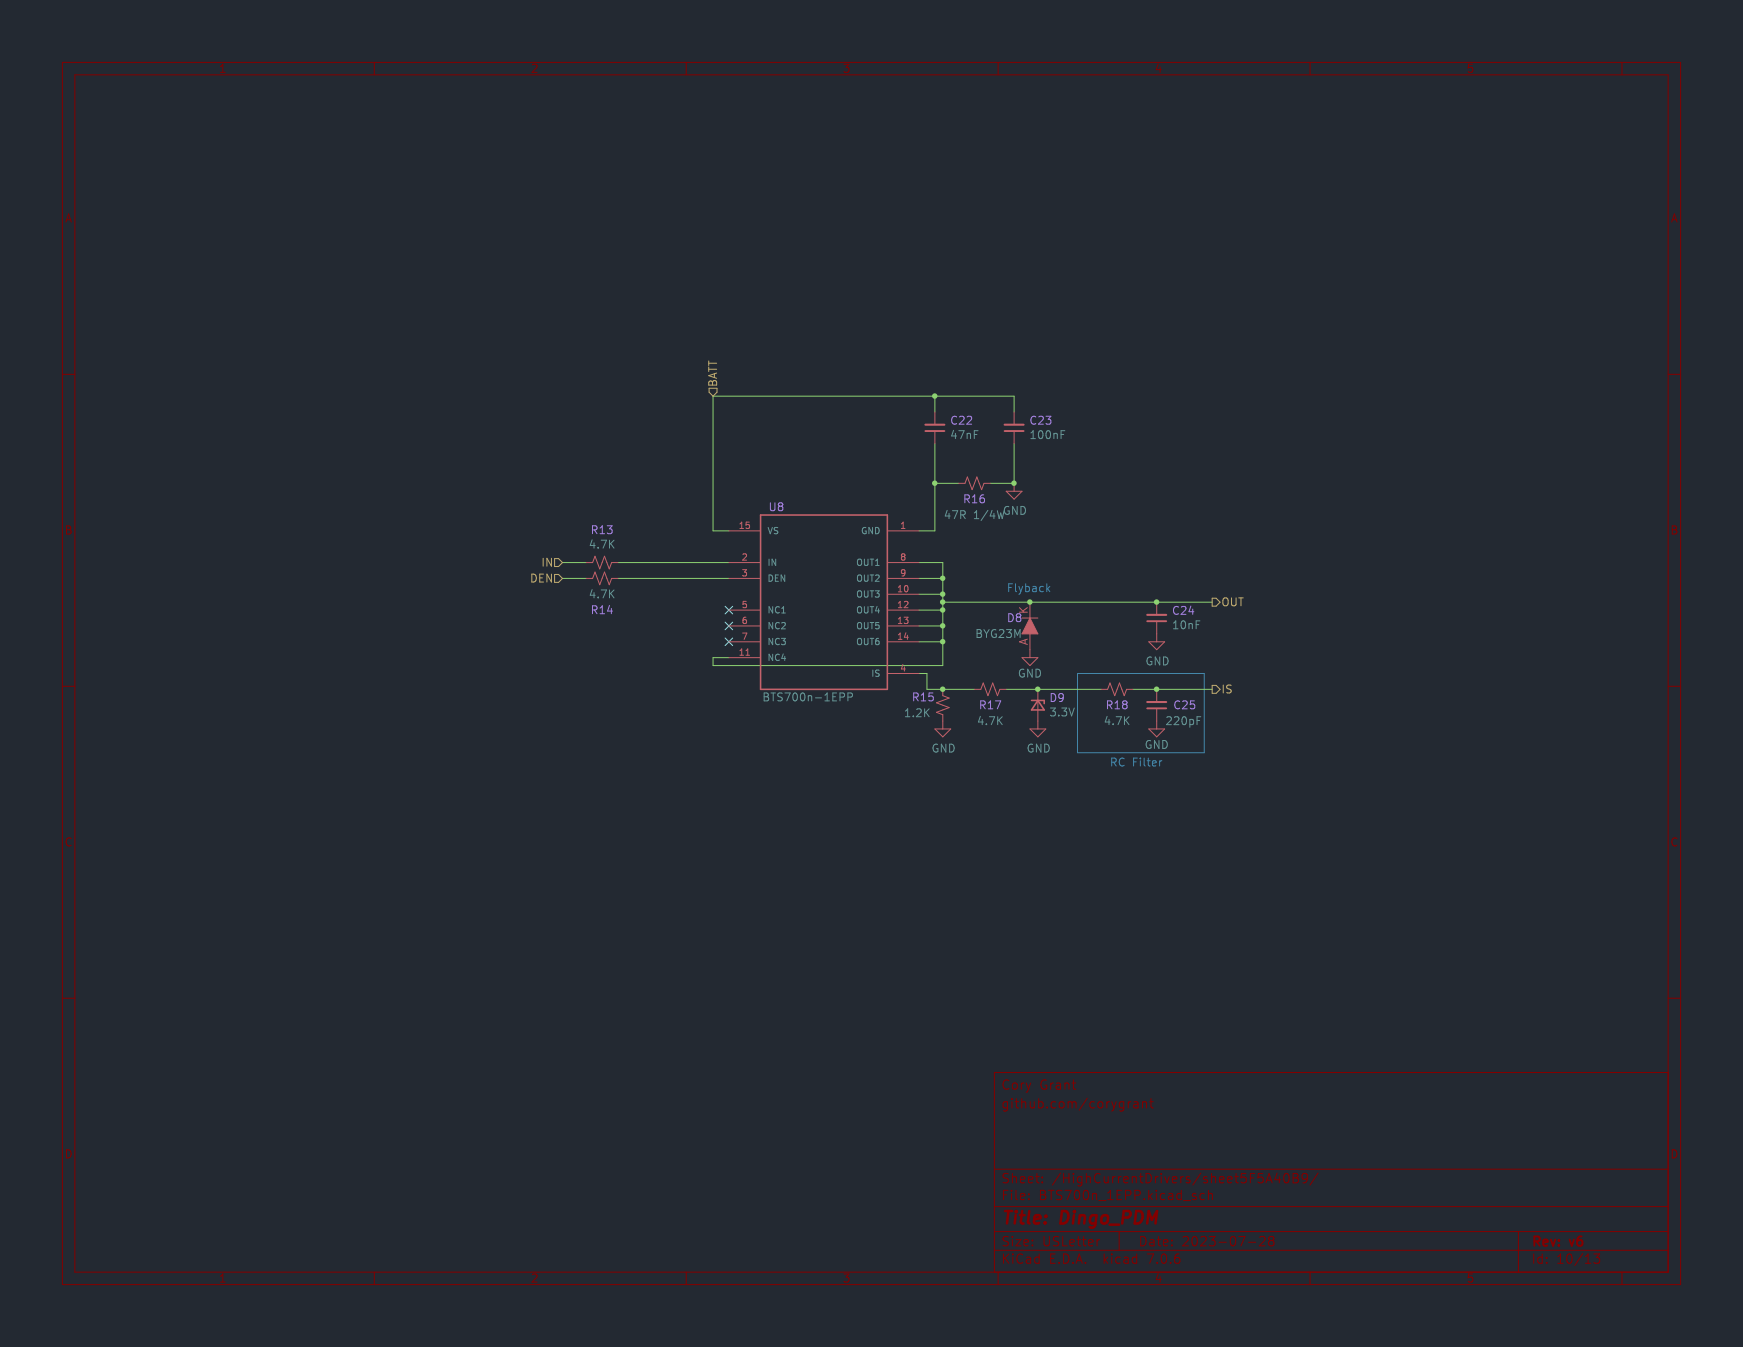
[picture p174: page 10]

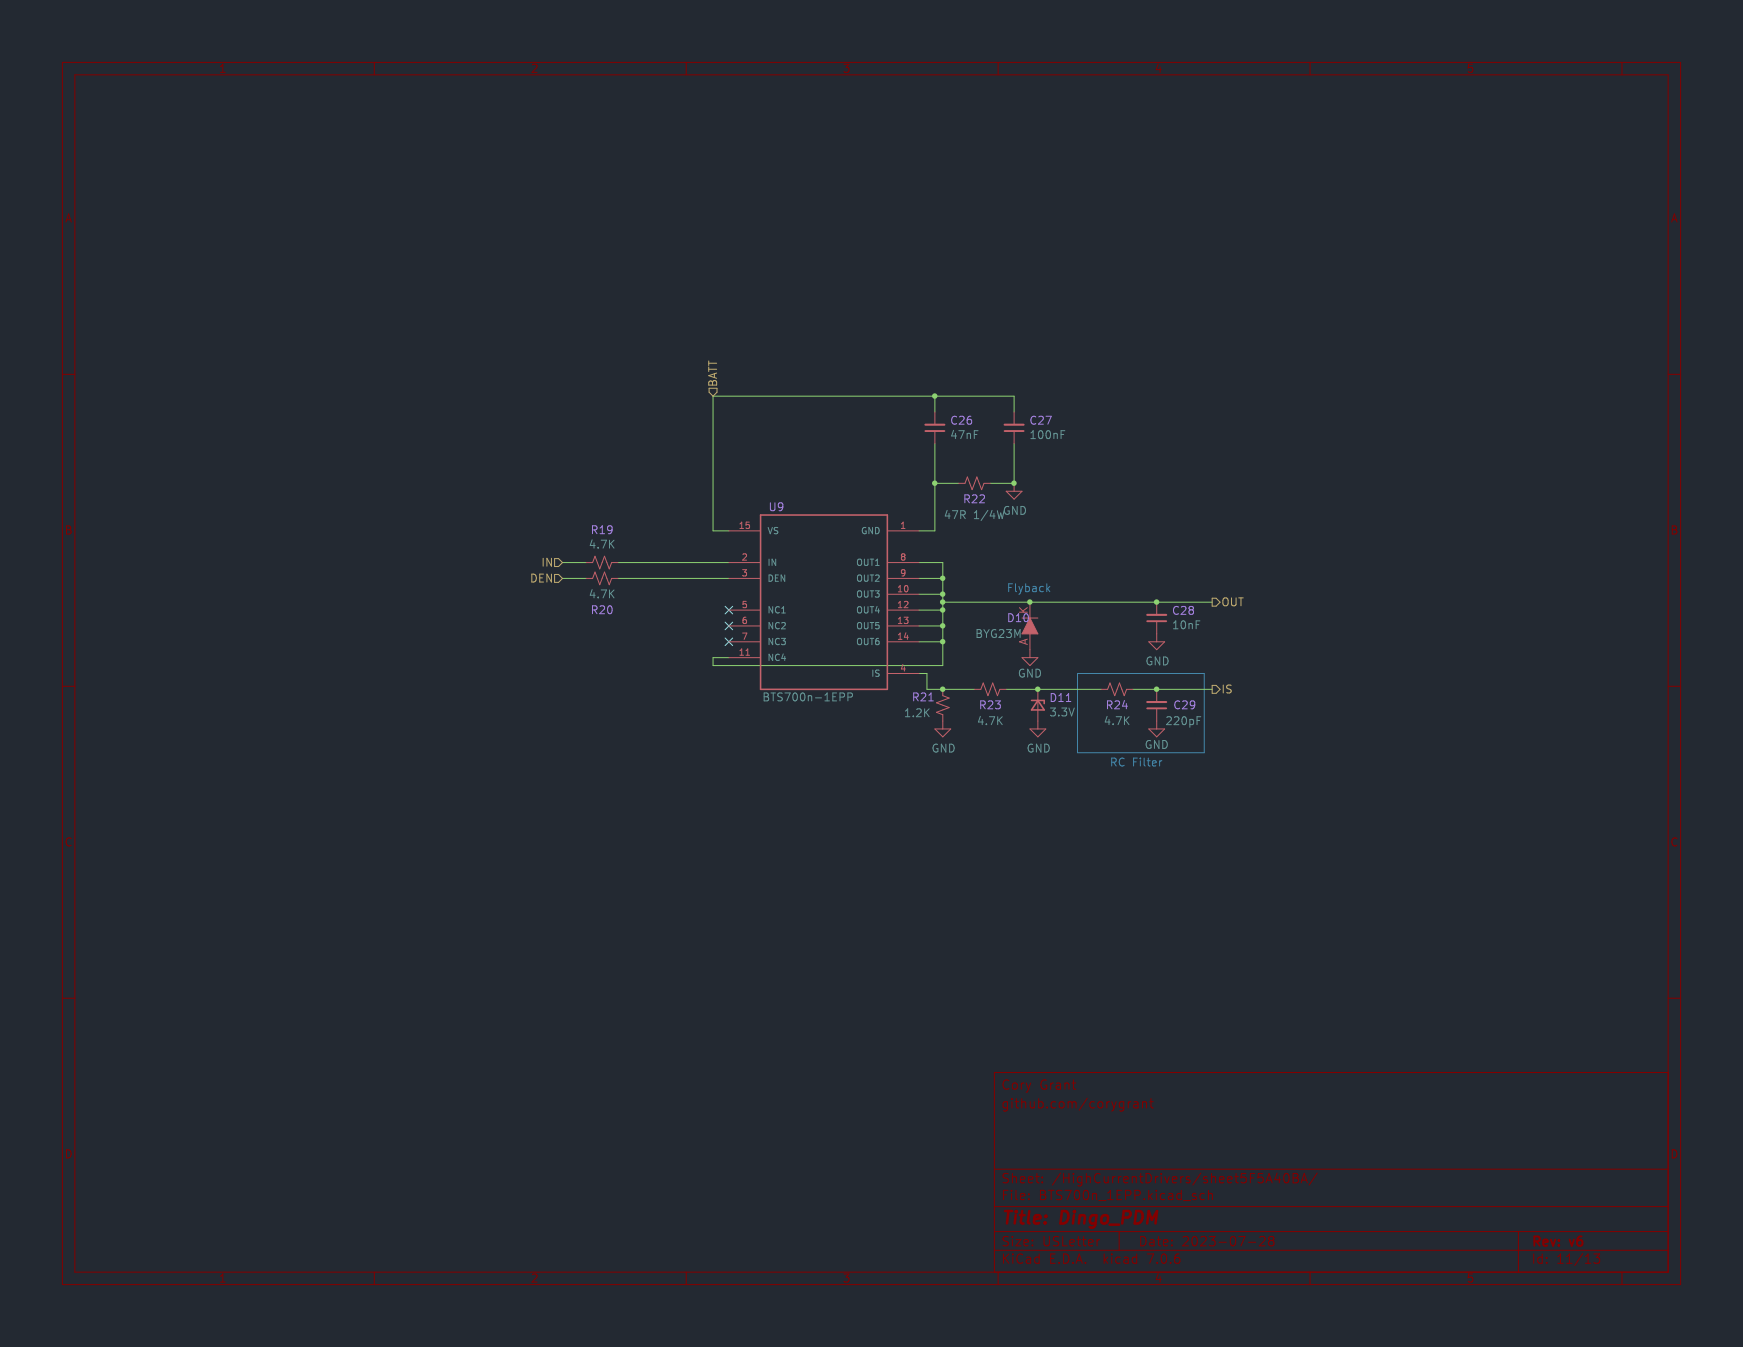
[picture p175: page 11]

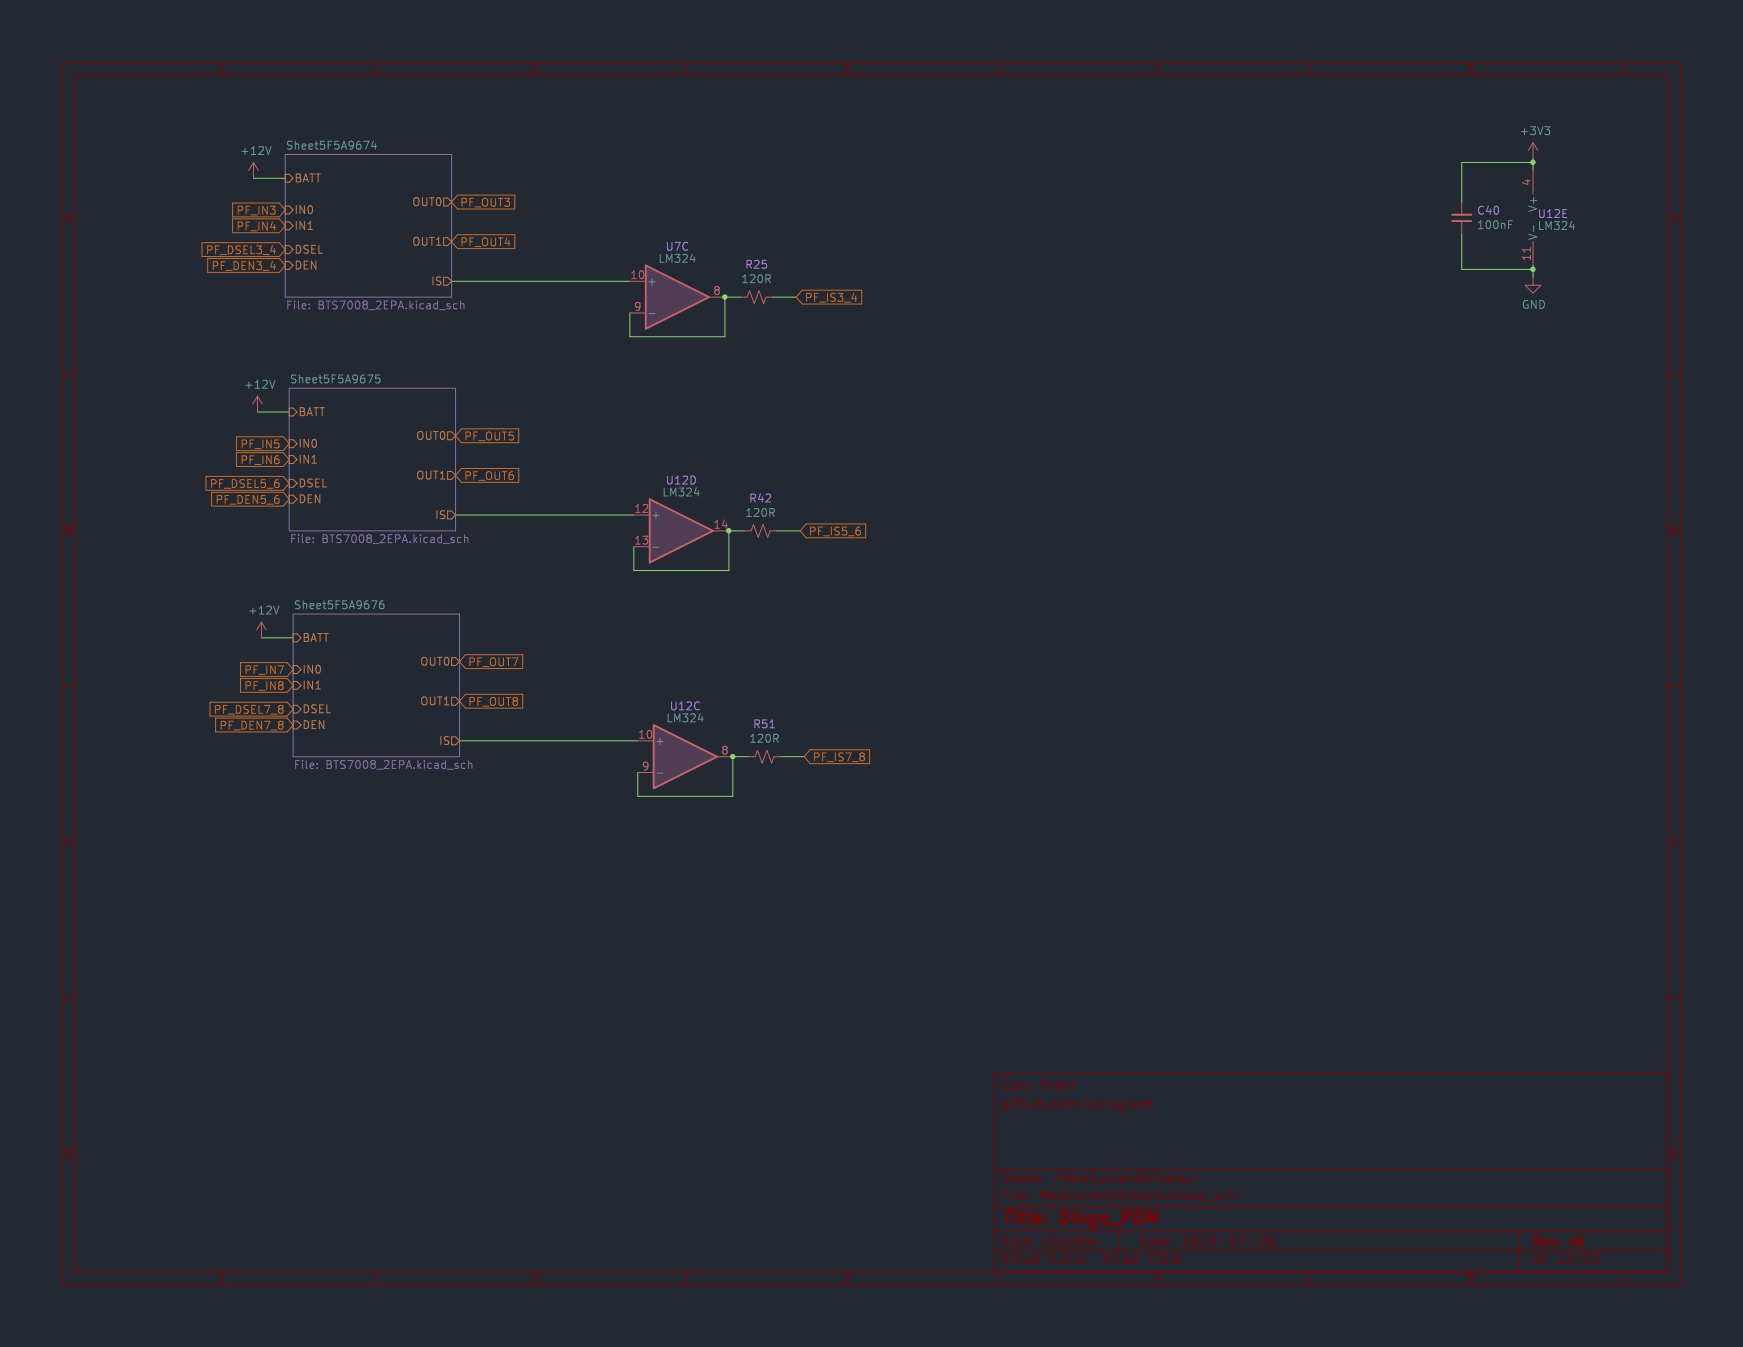
[picture p176: page 12]

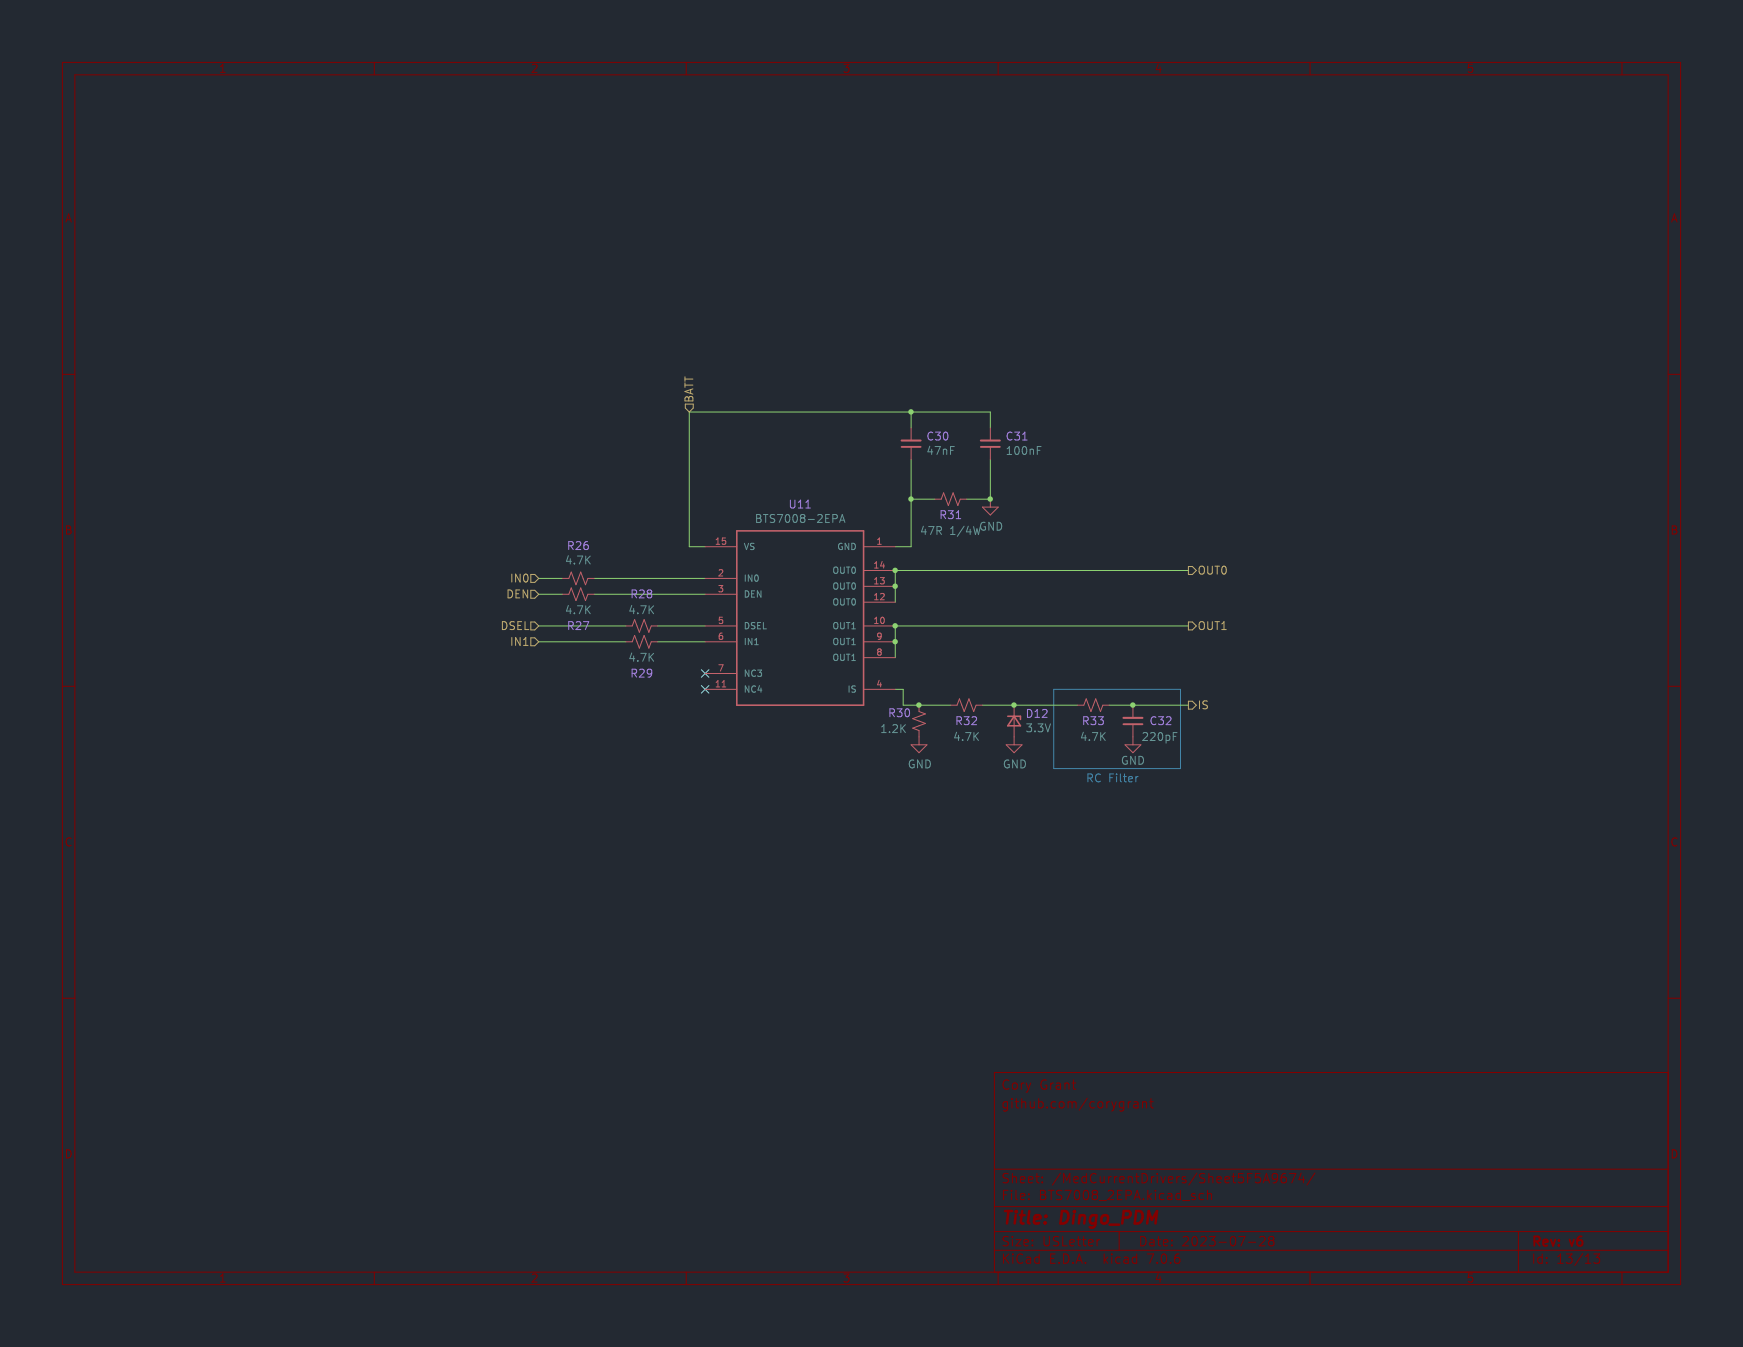
[picture p177: page 13]
