corygrant/dingoPDM/Export/V6/DingoPDM_HW_V6.pdf

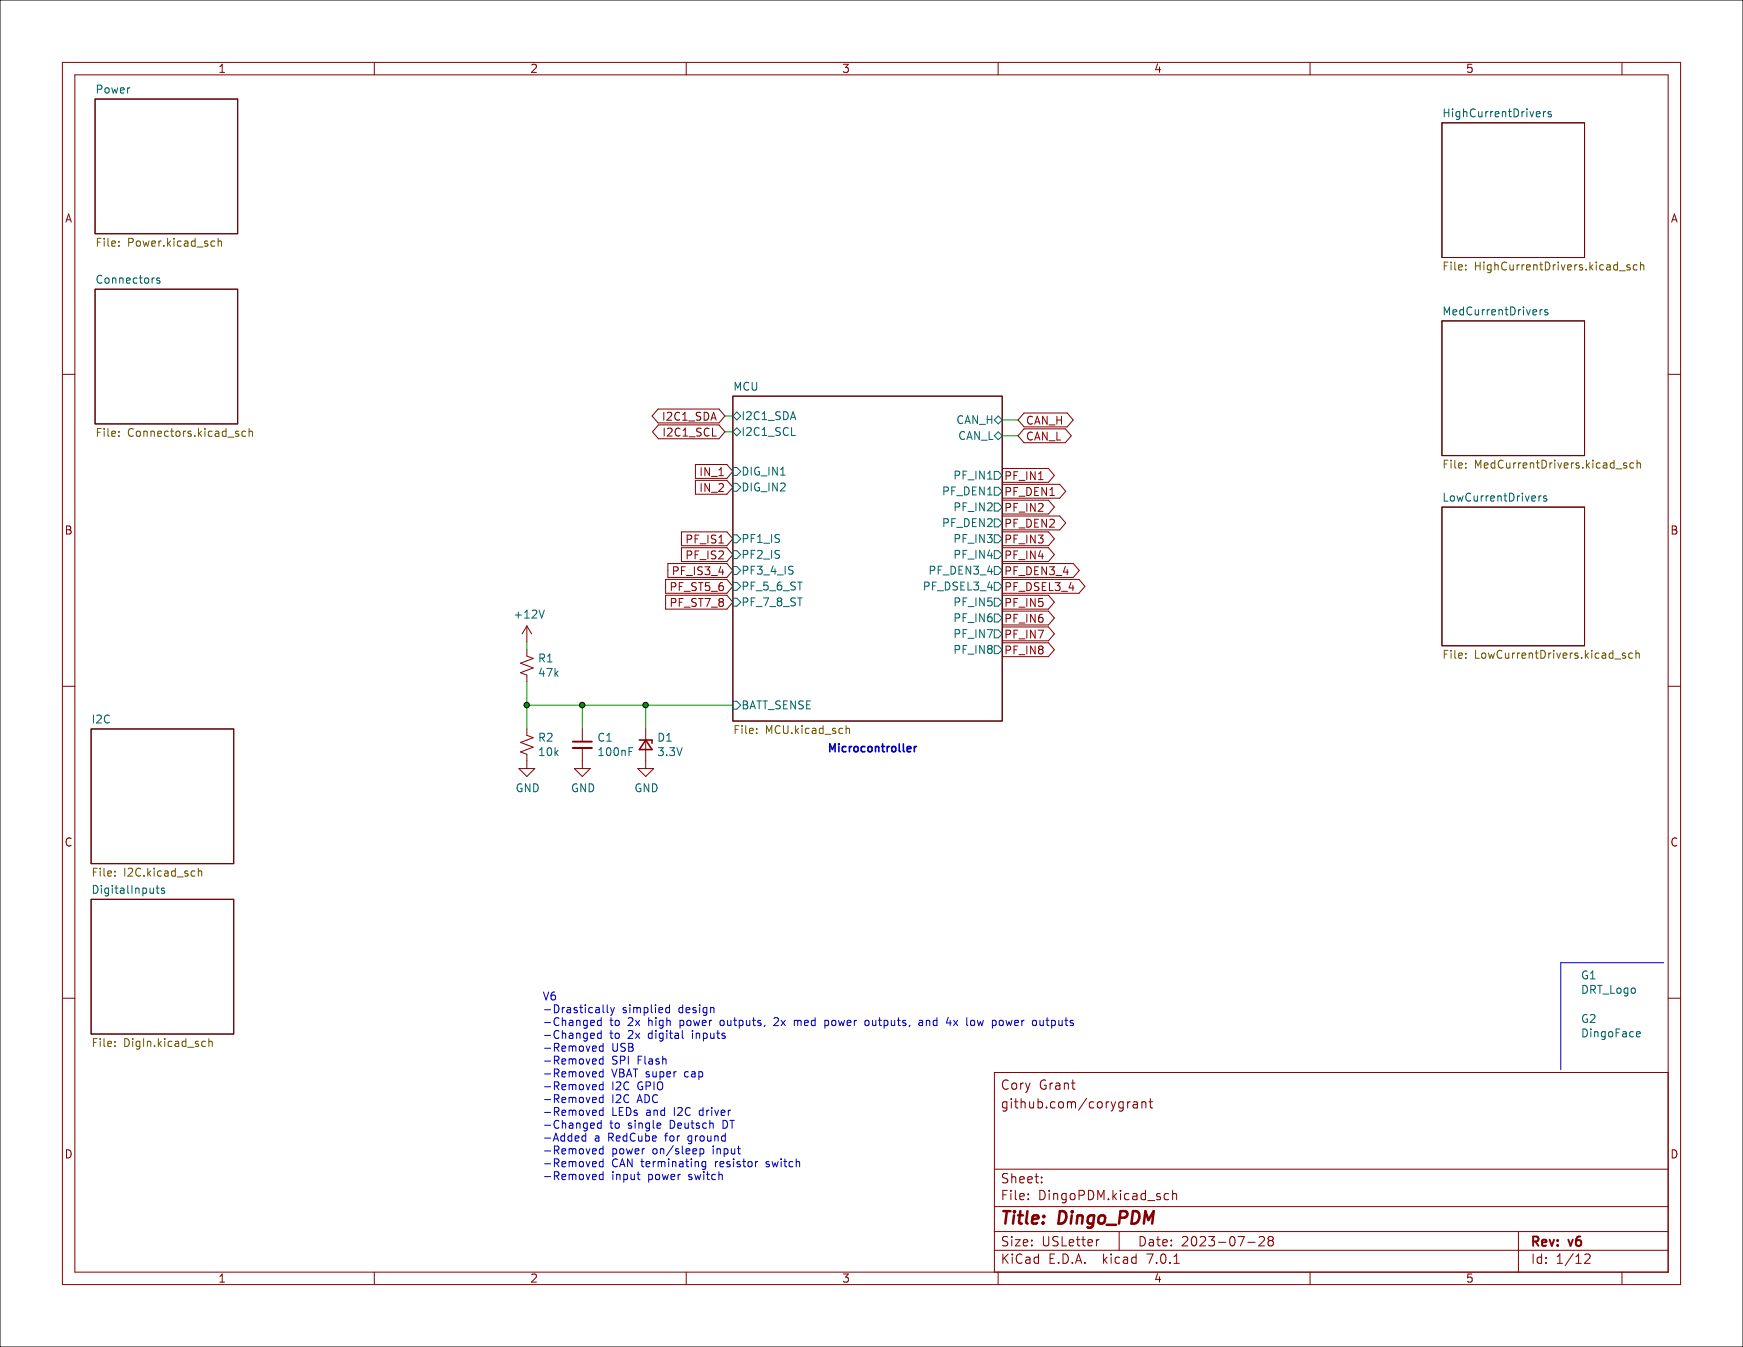
[picture p178: page 1]

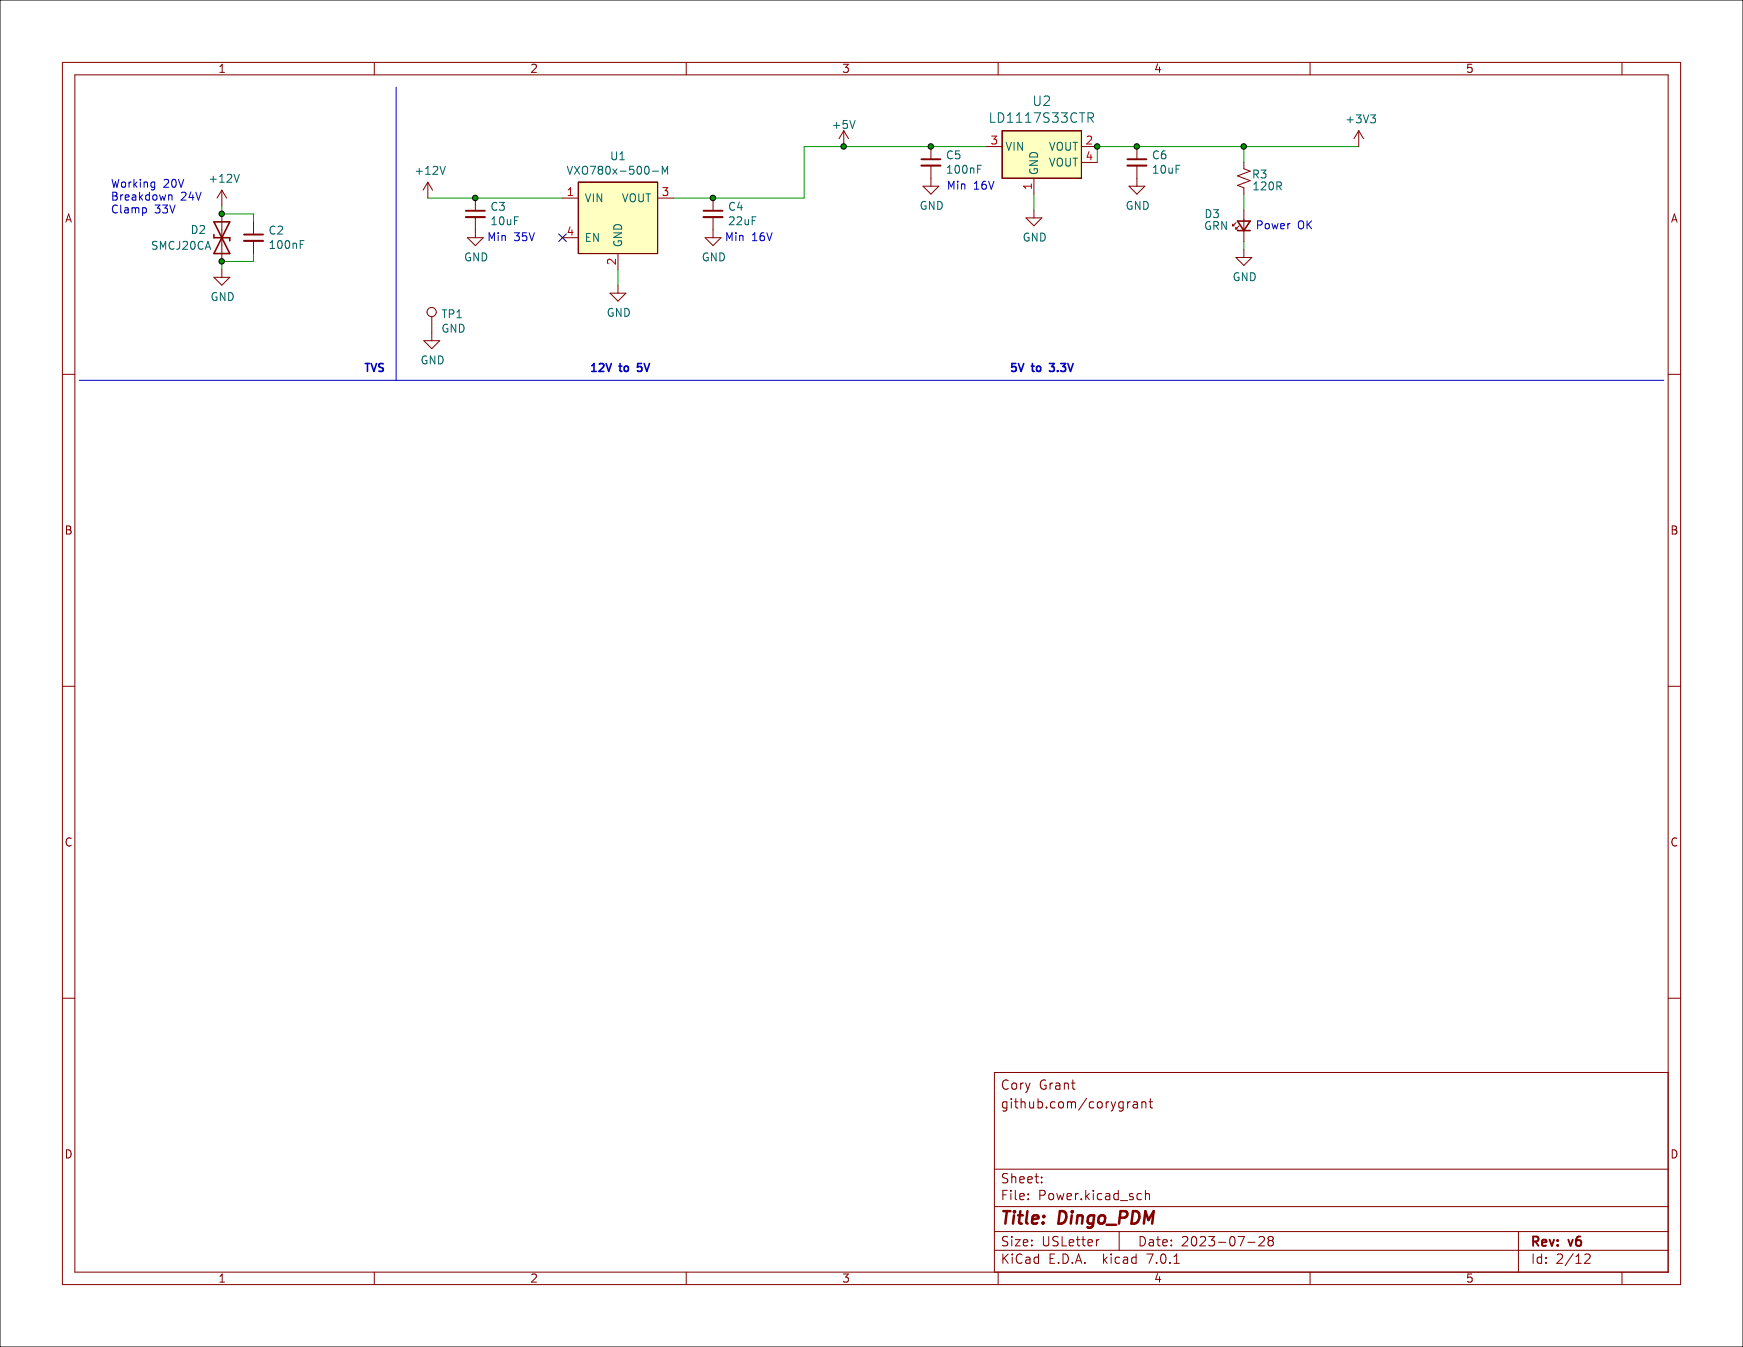
[picture p179: page 2]

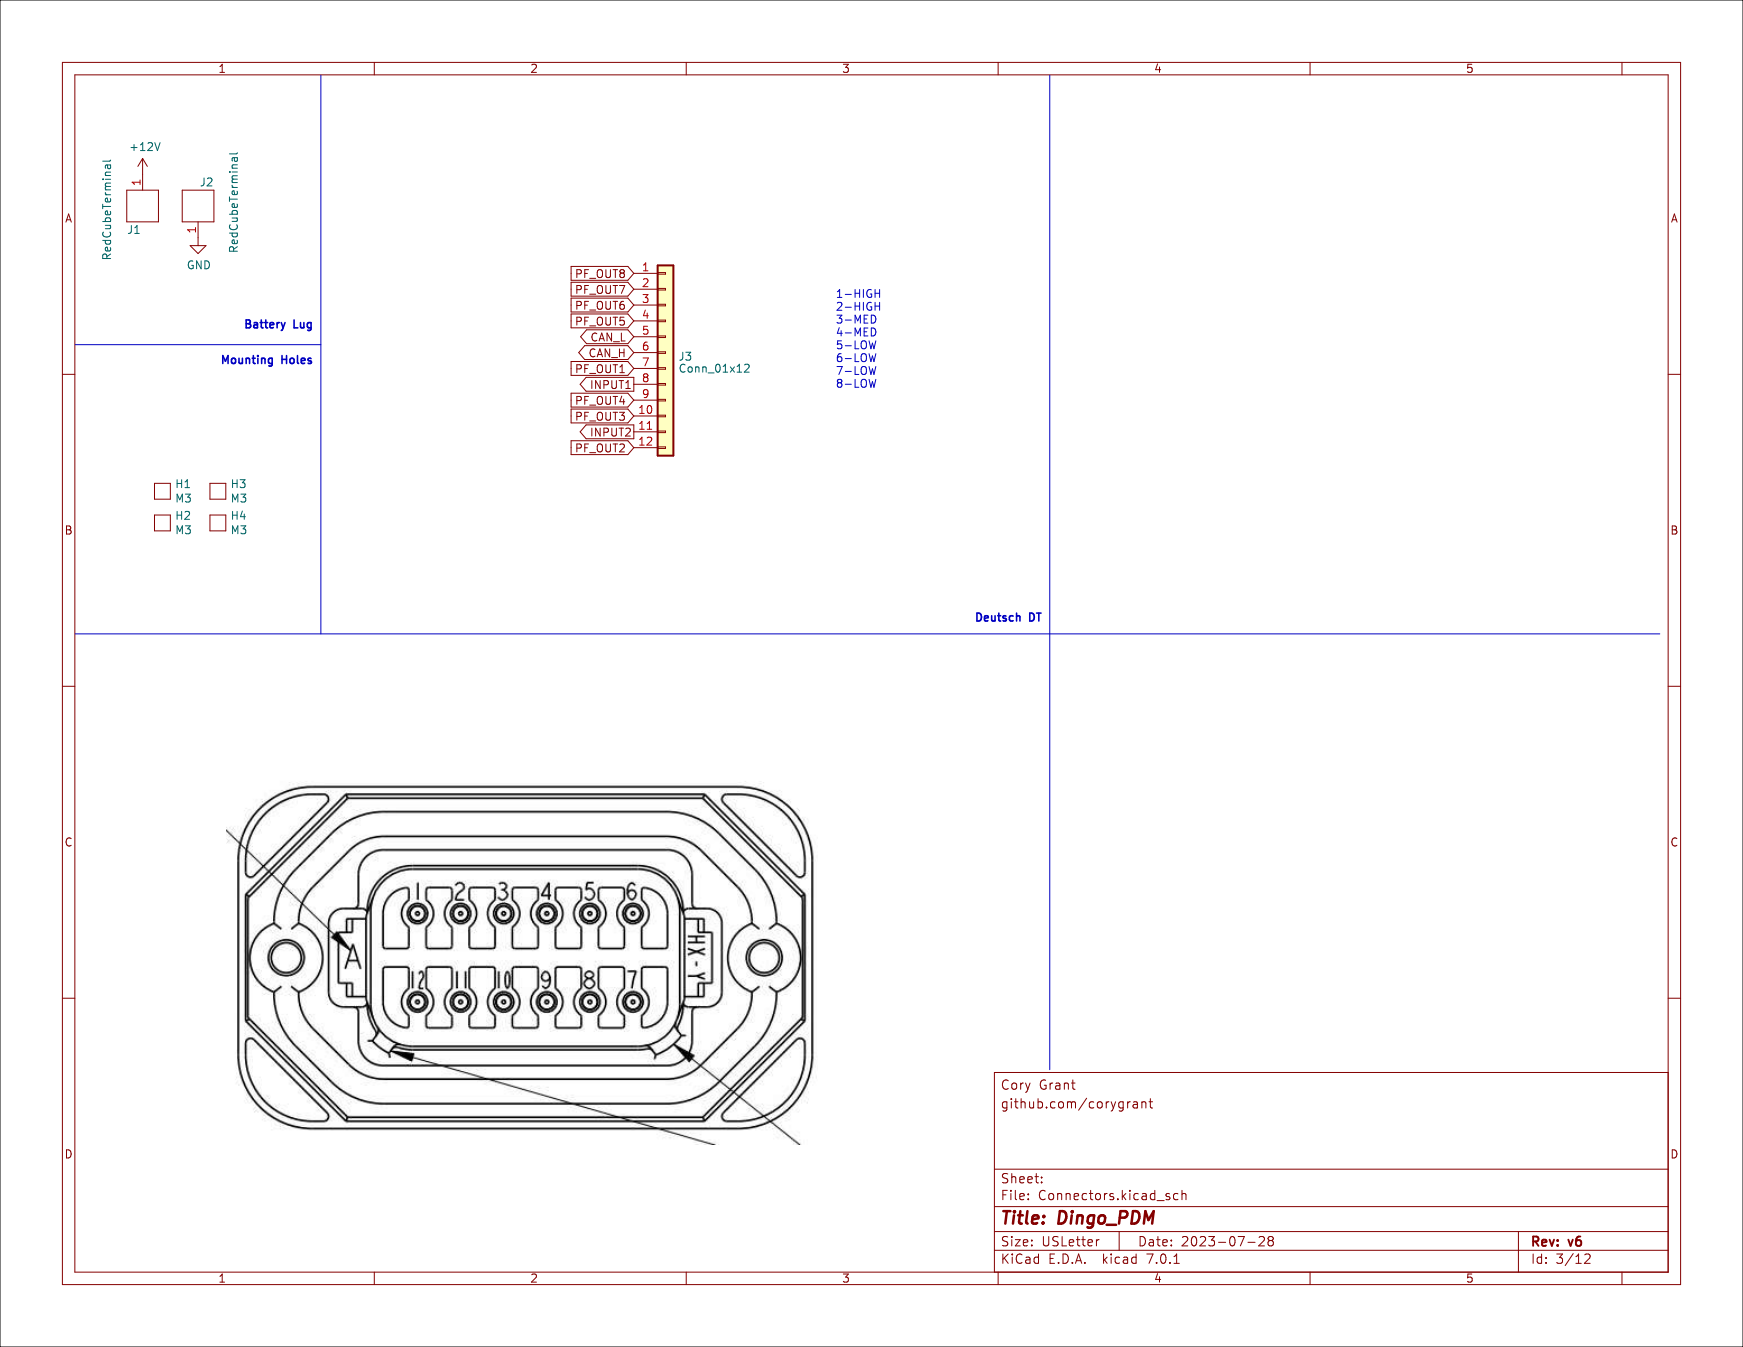
[picture p180: page 3]

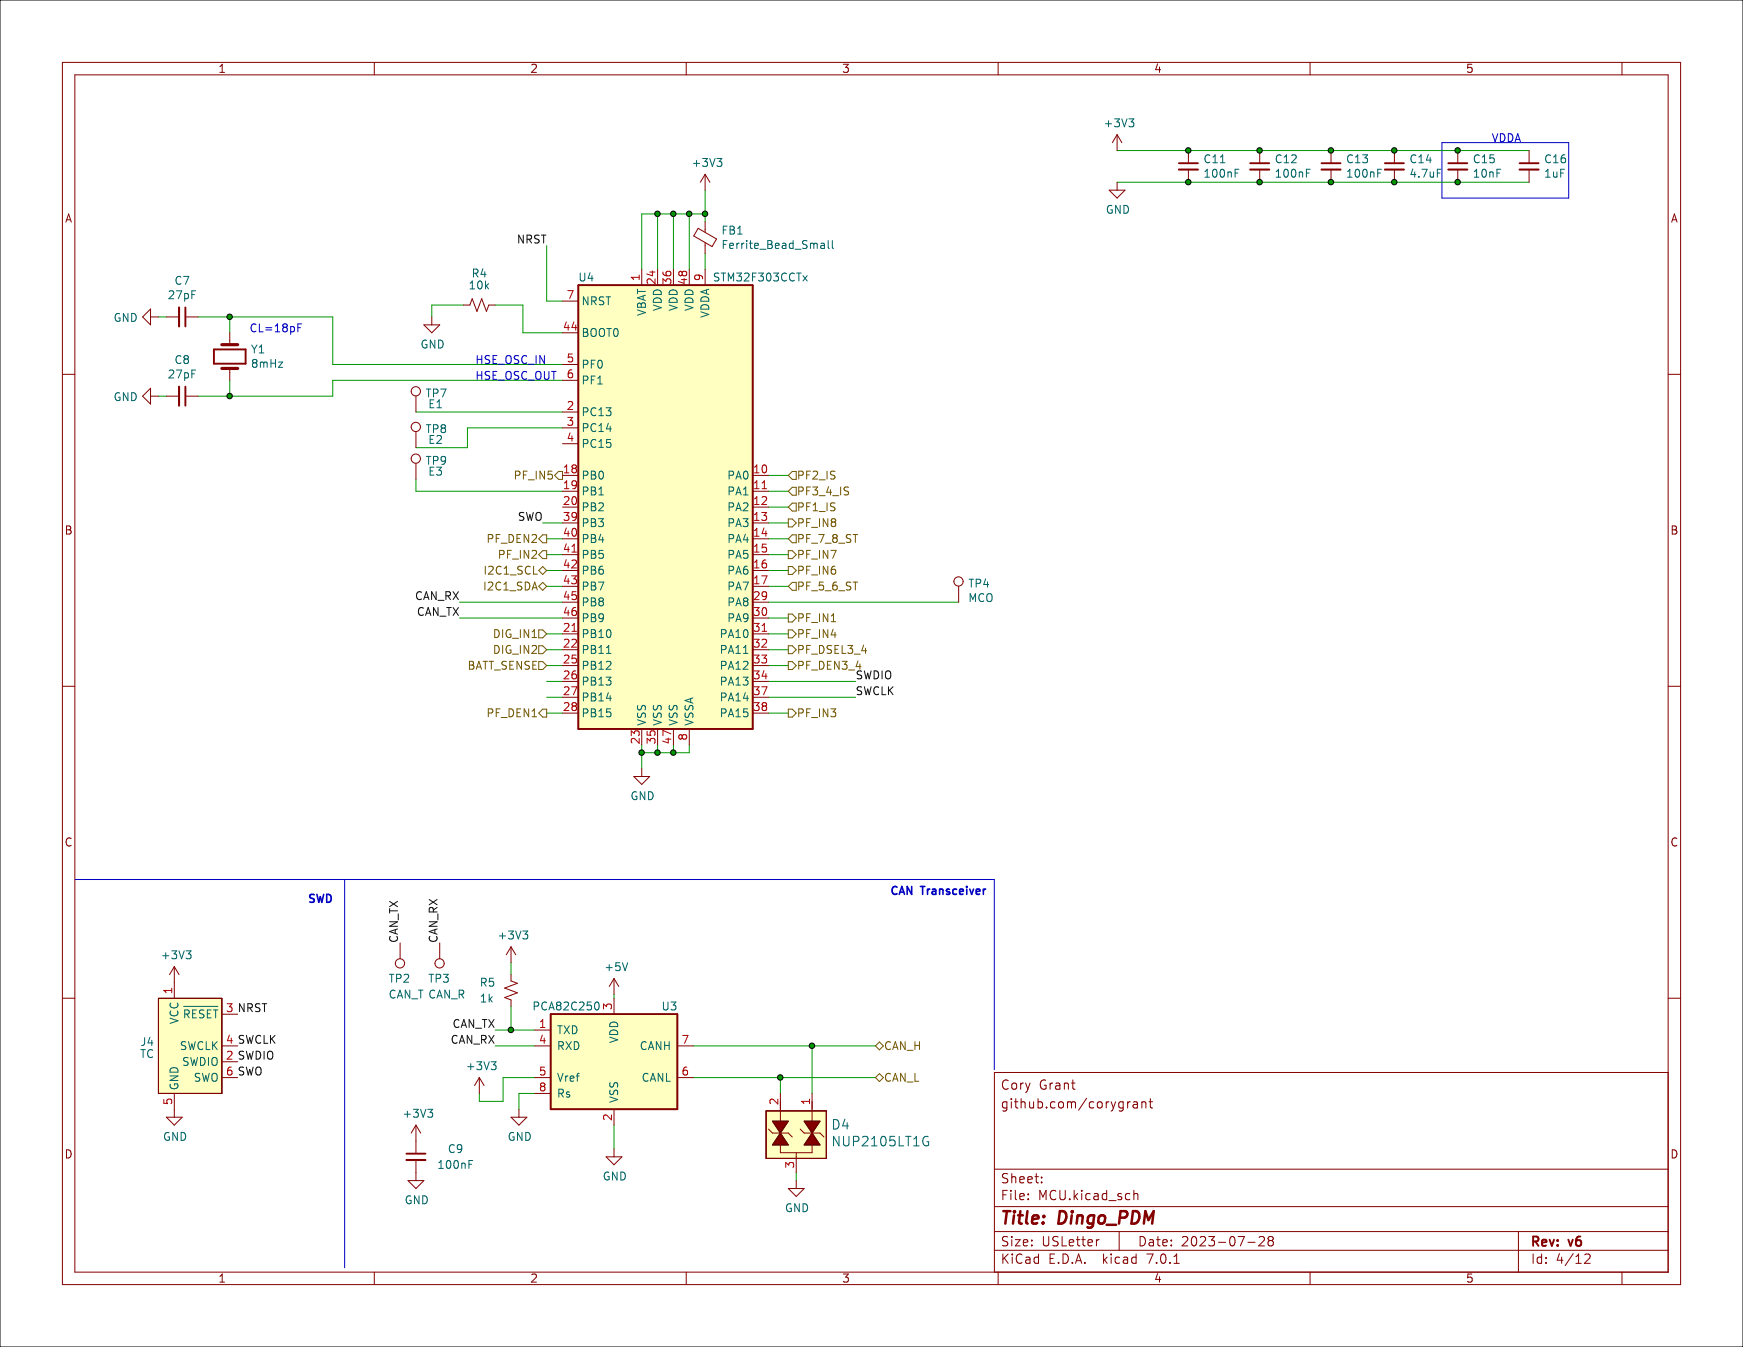
[picture p181: page 4]

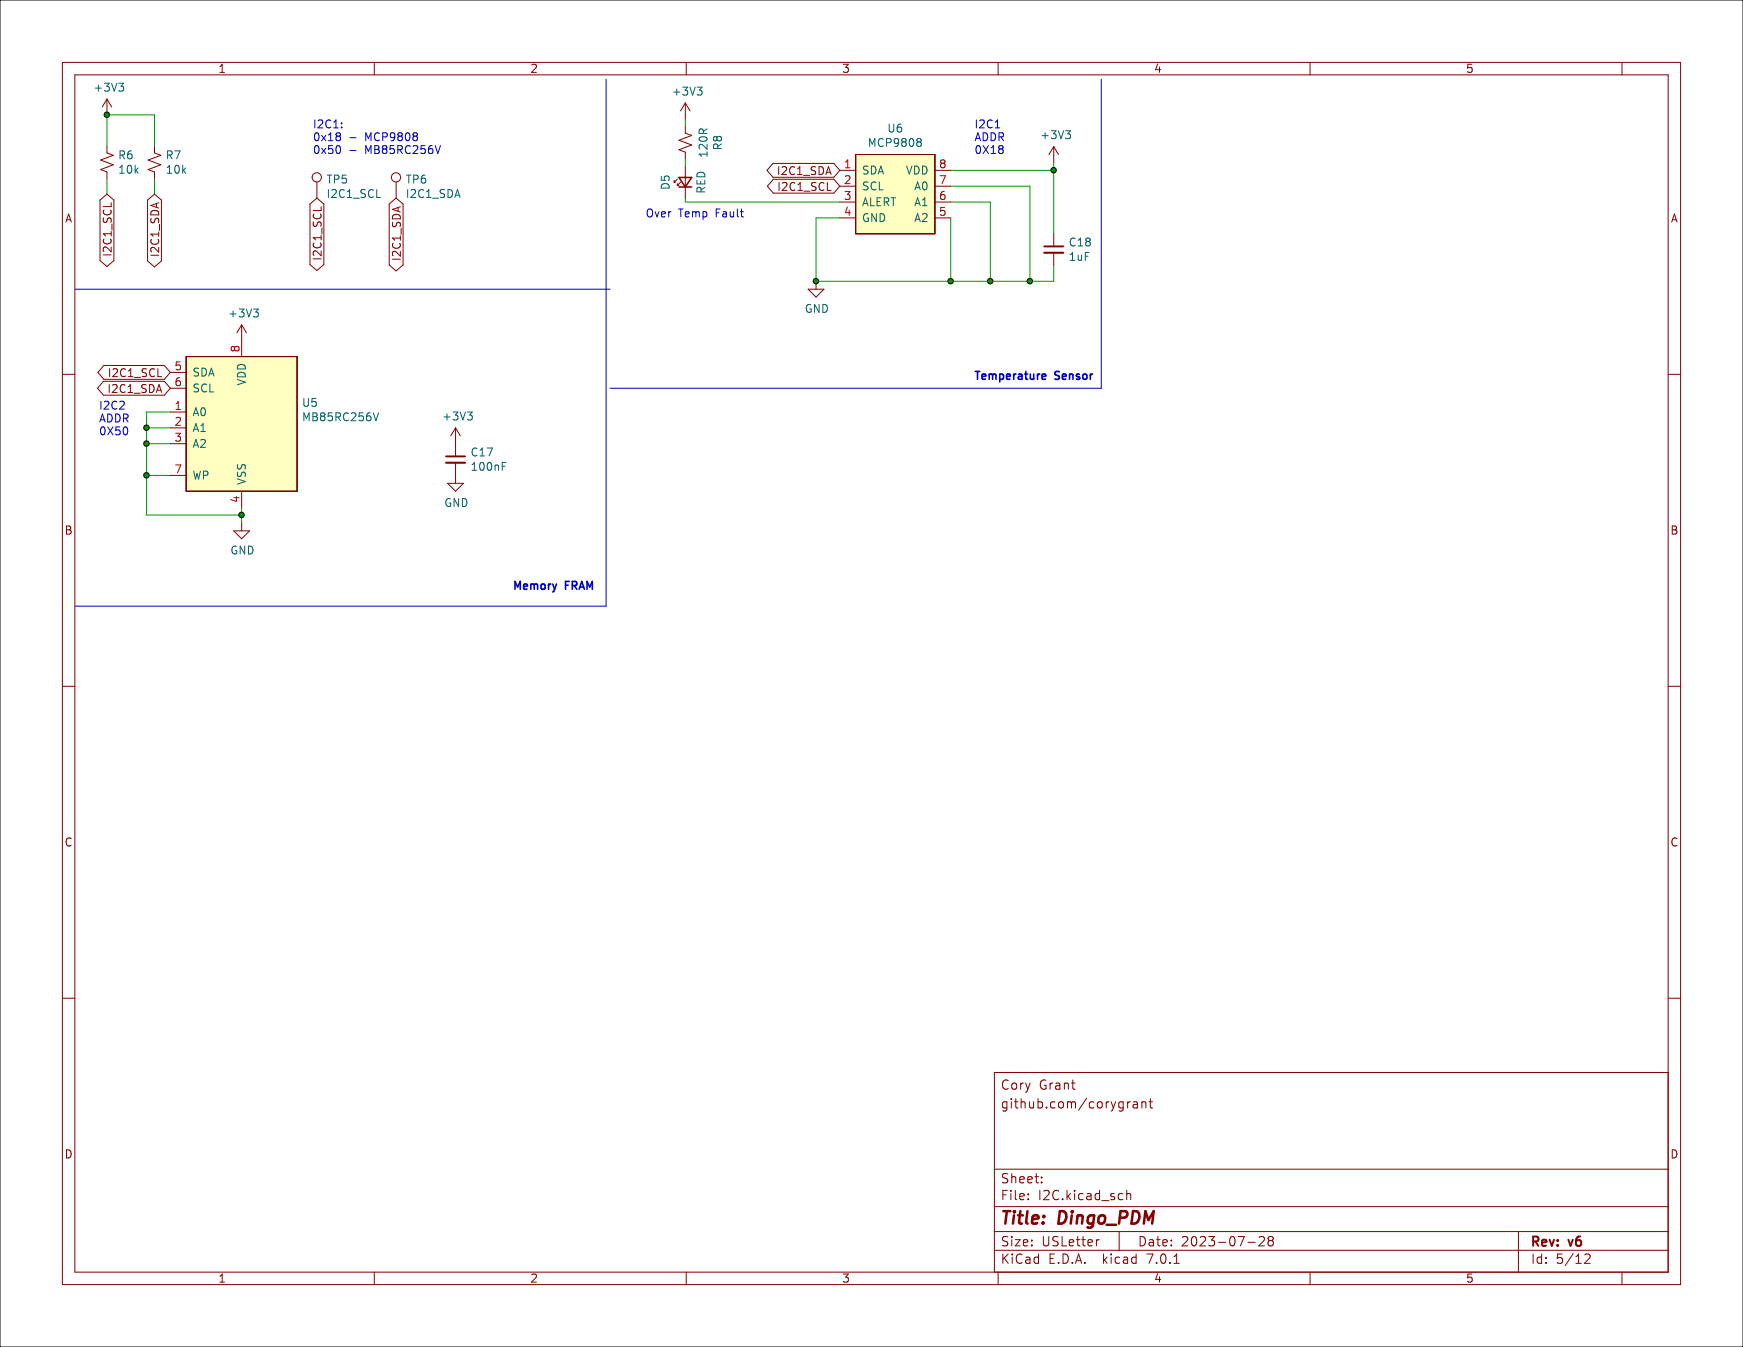
[picture p182: page 5]

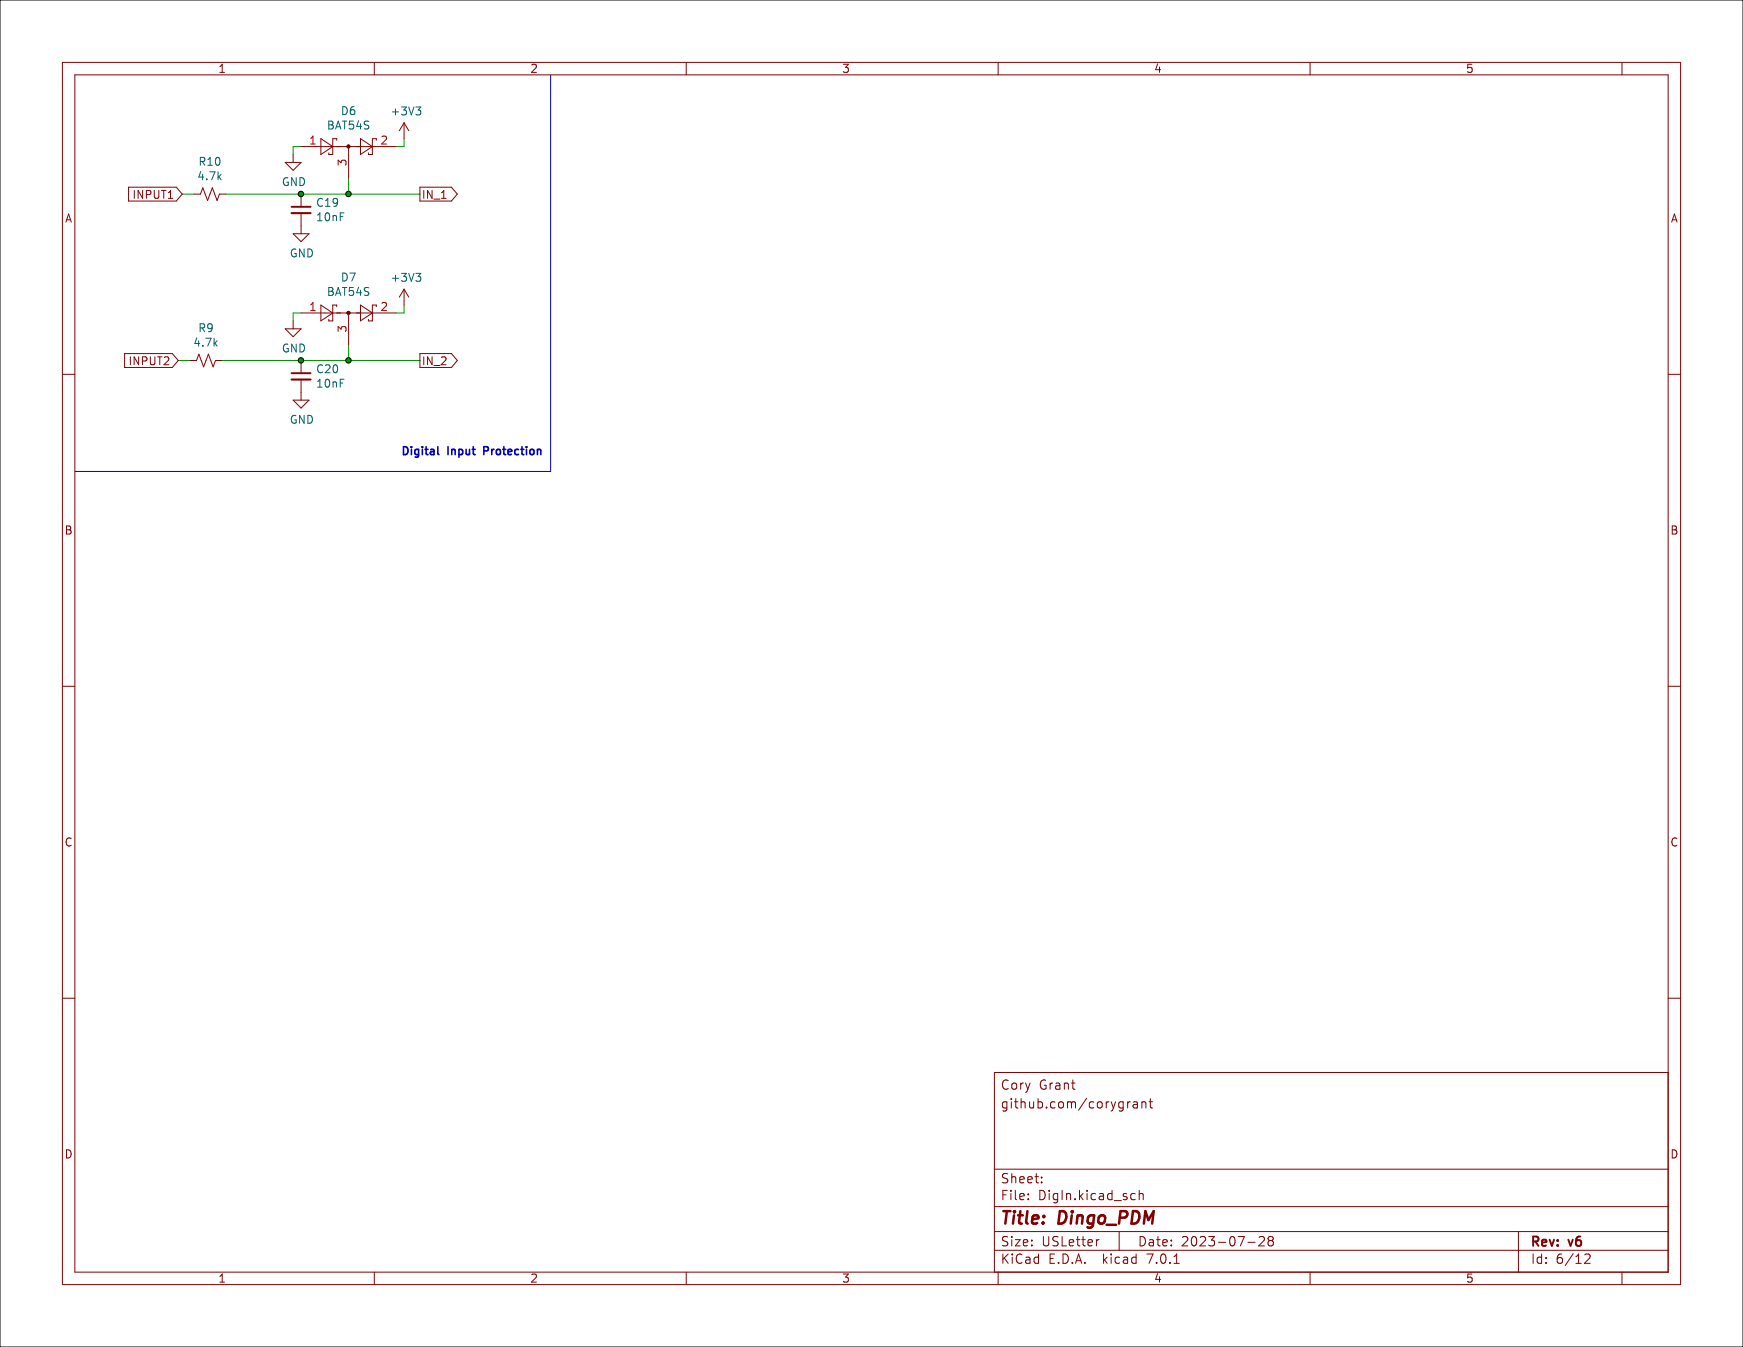
[picture p183: page 6]

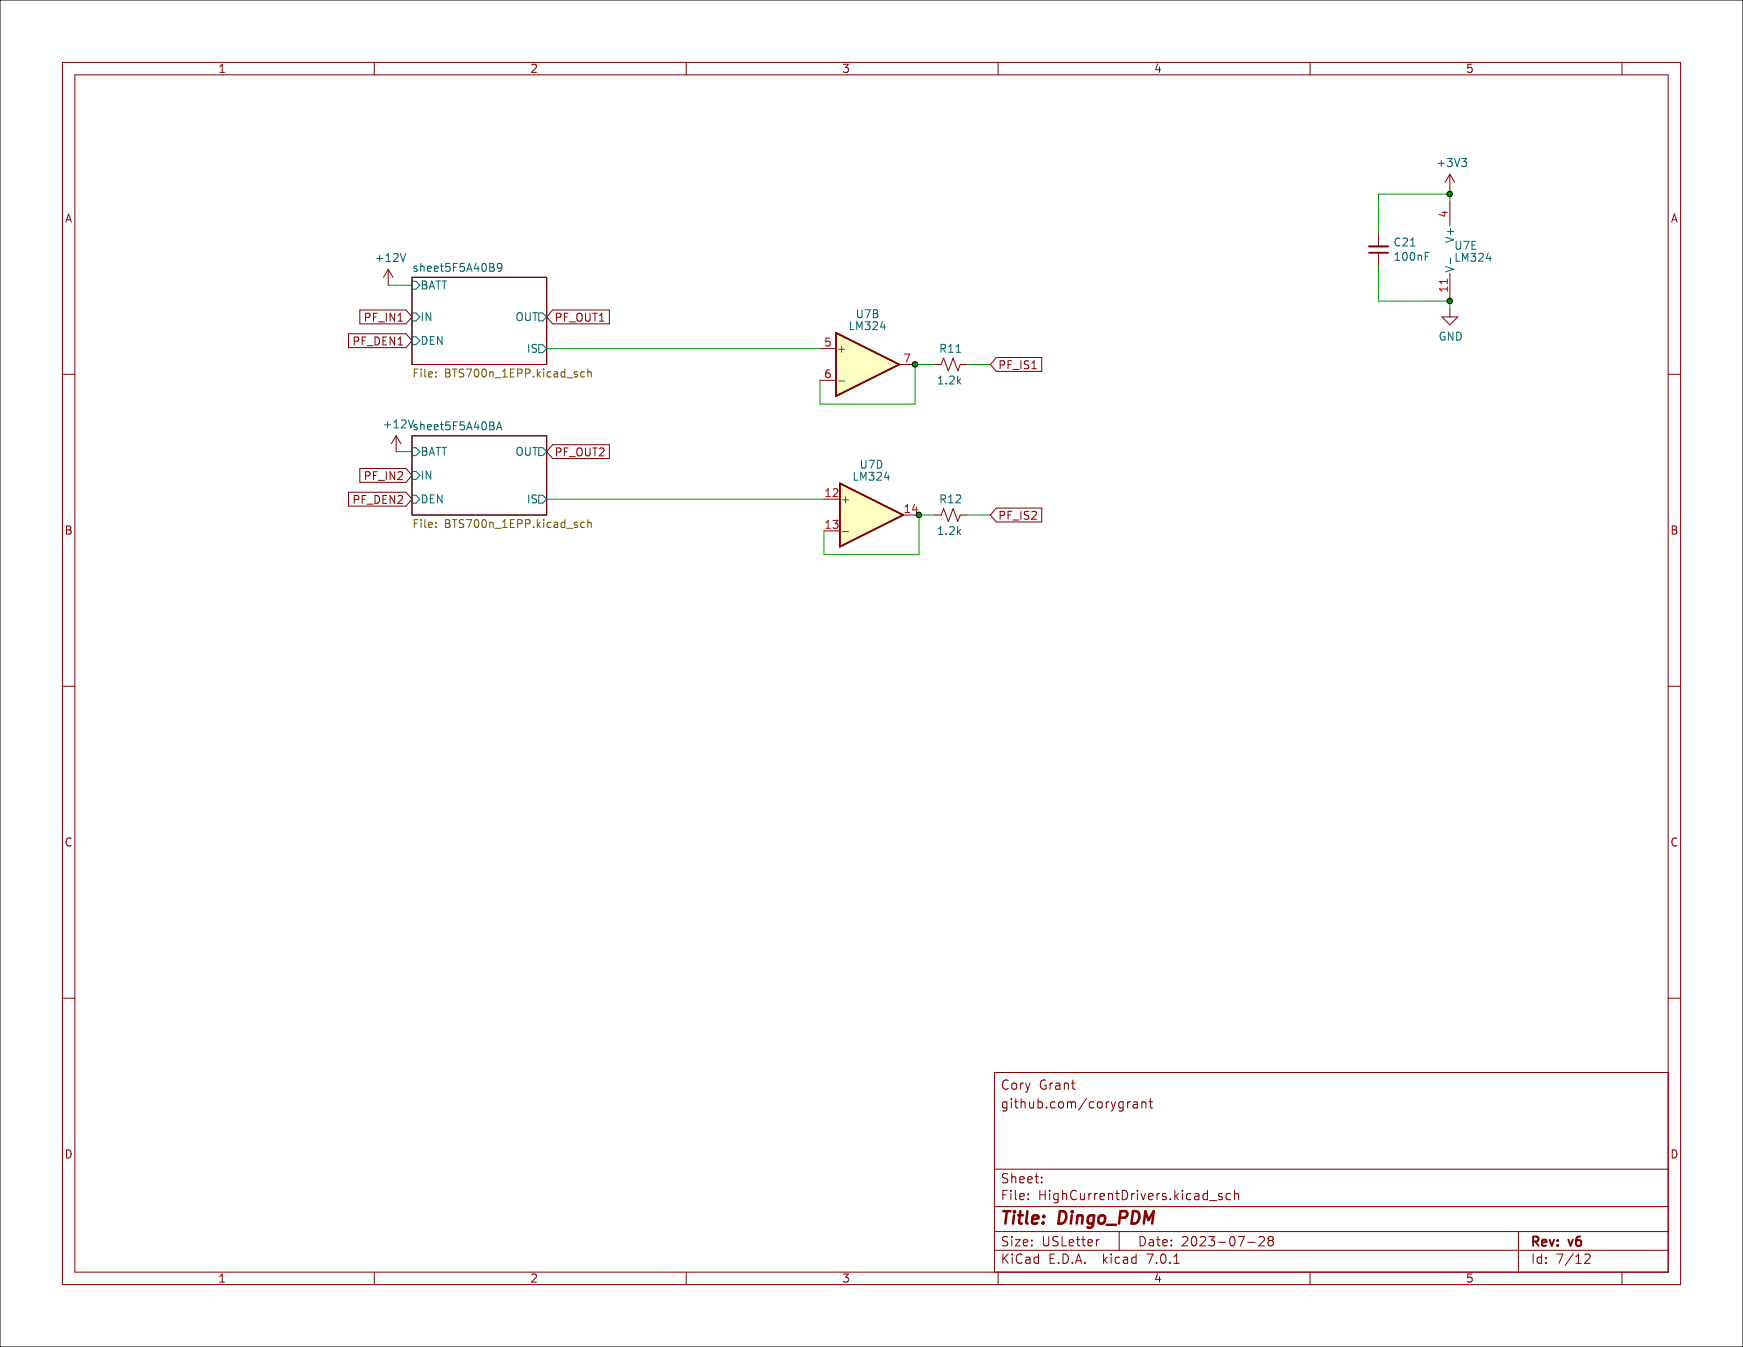
[picture p184: page 7]

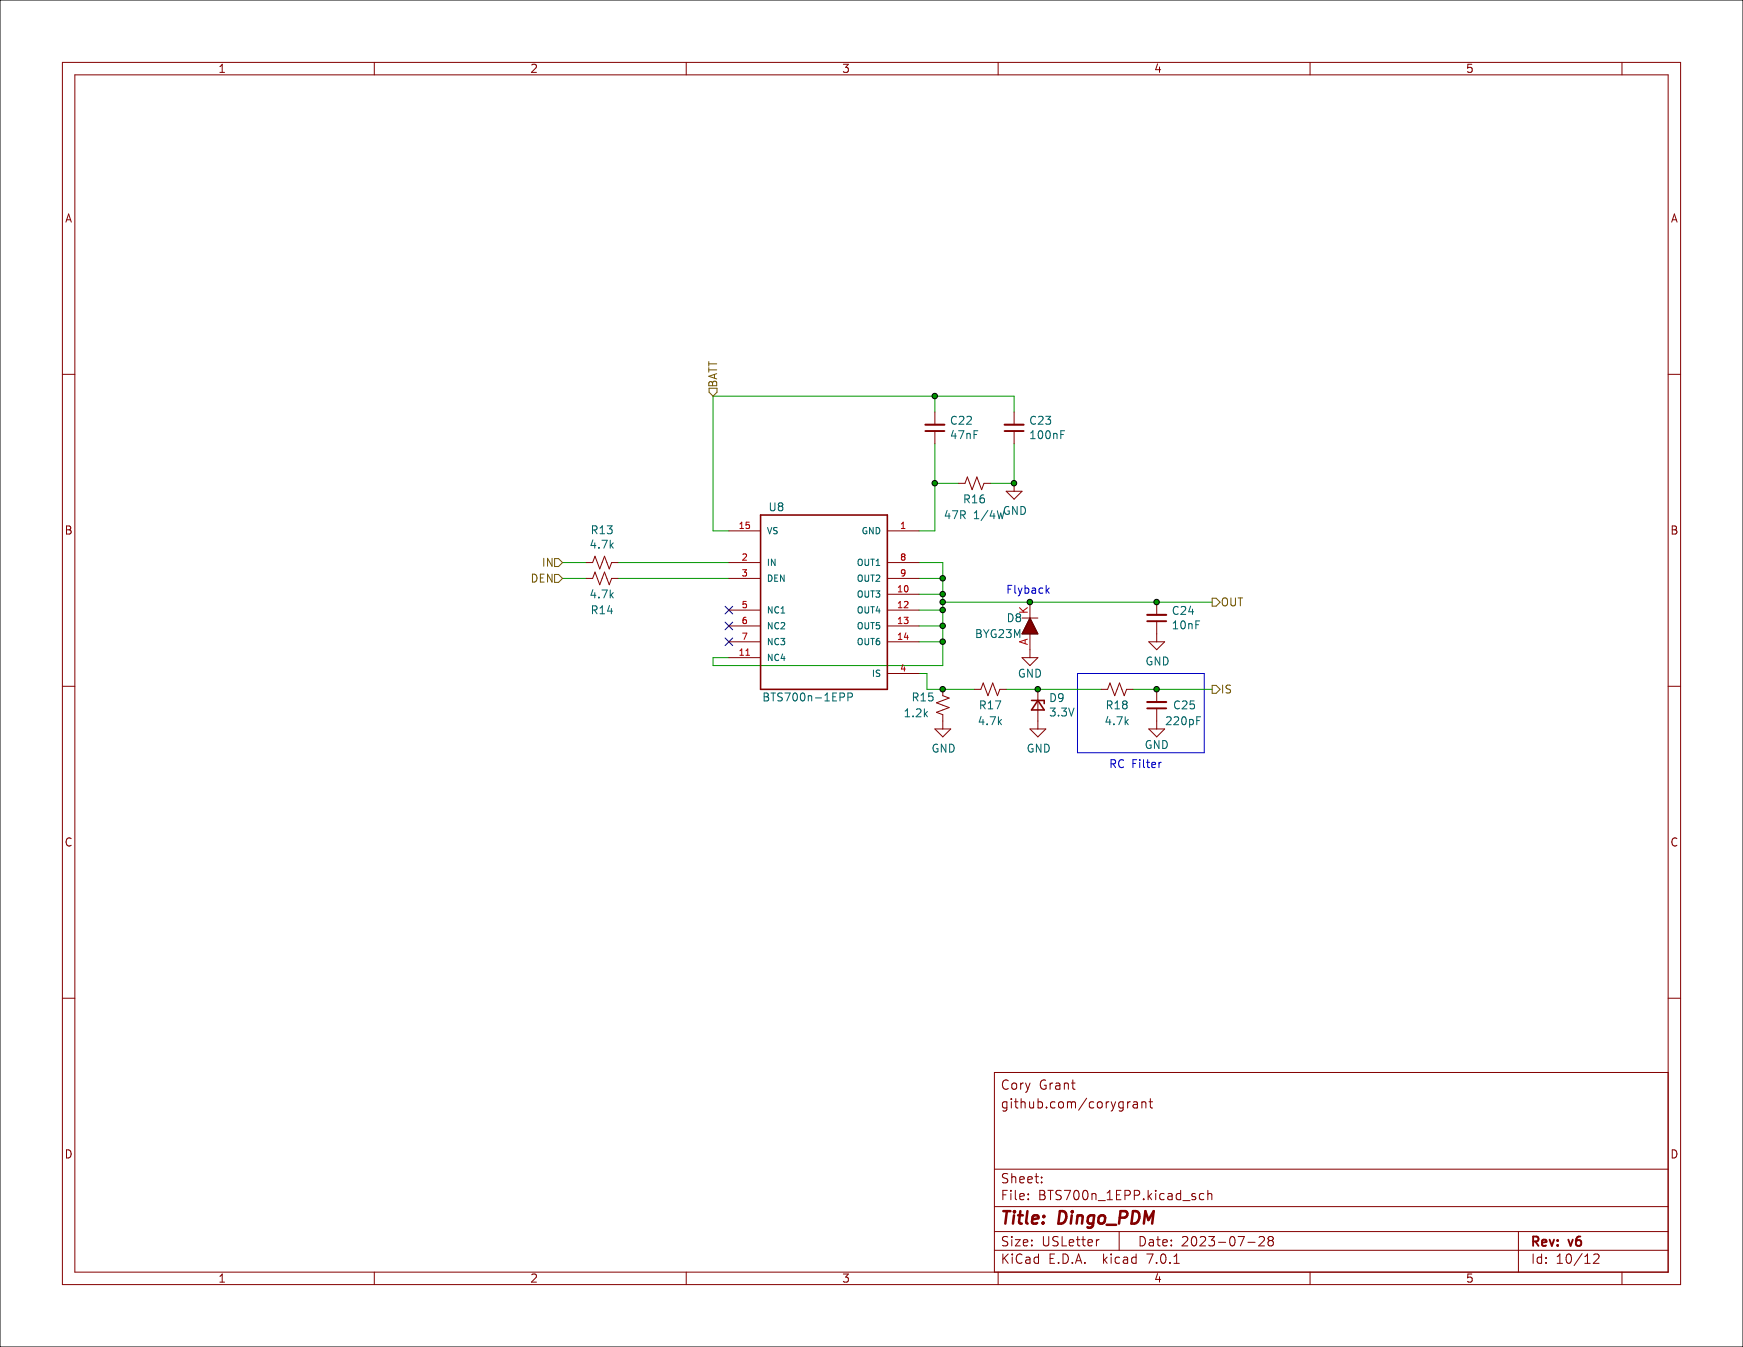
[picture p185: page 8]

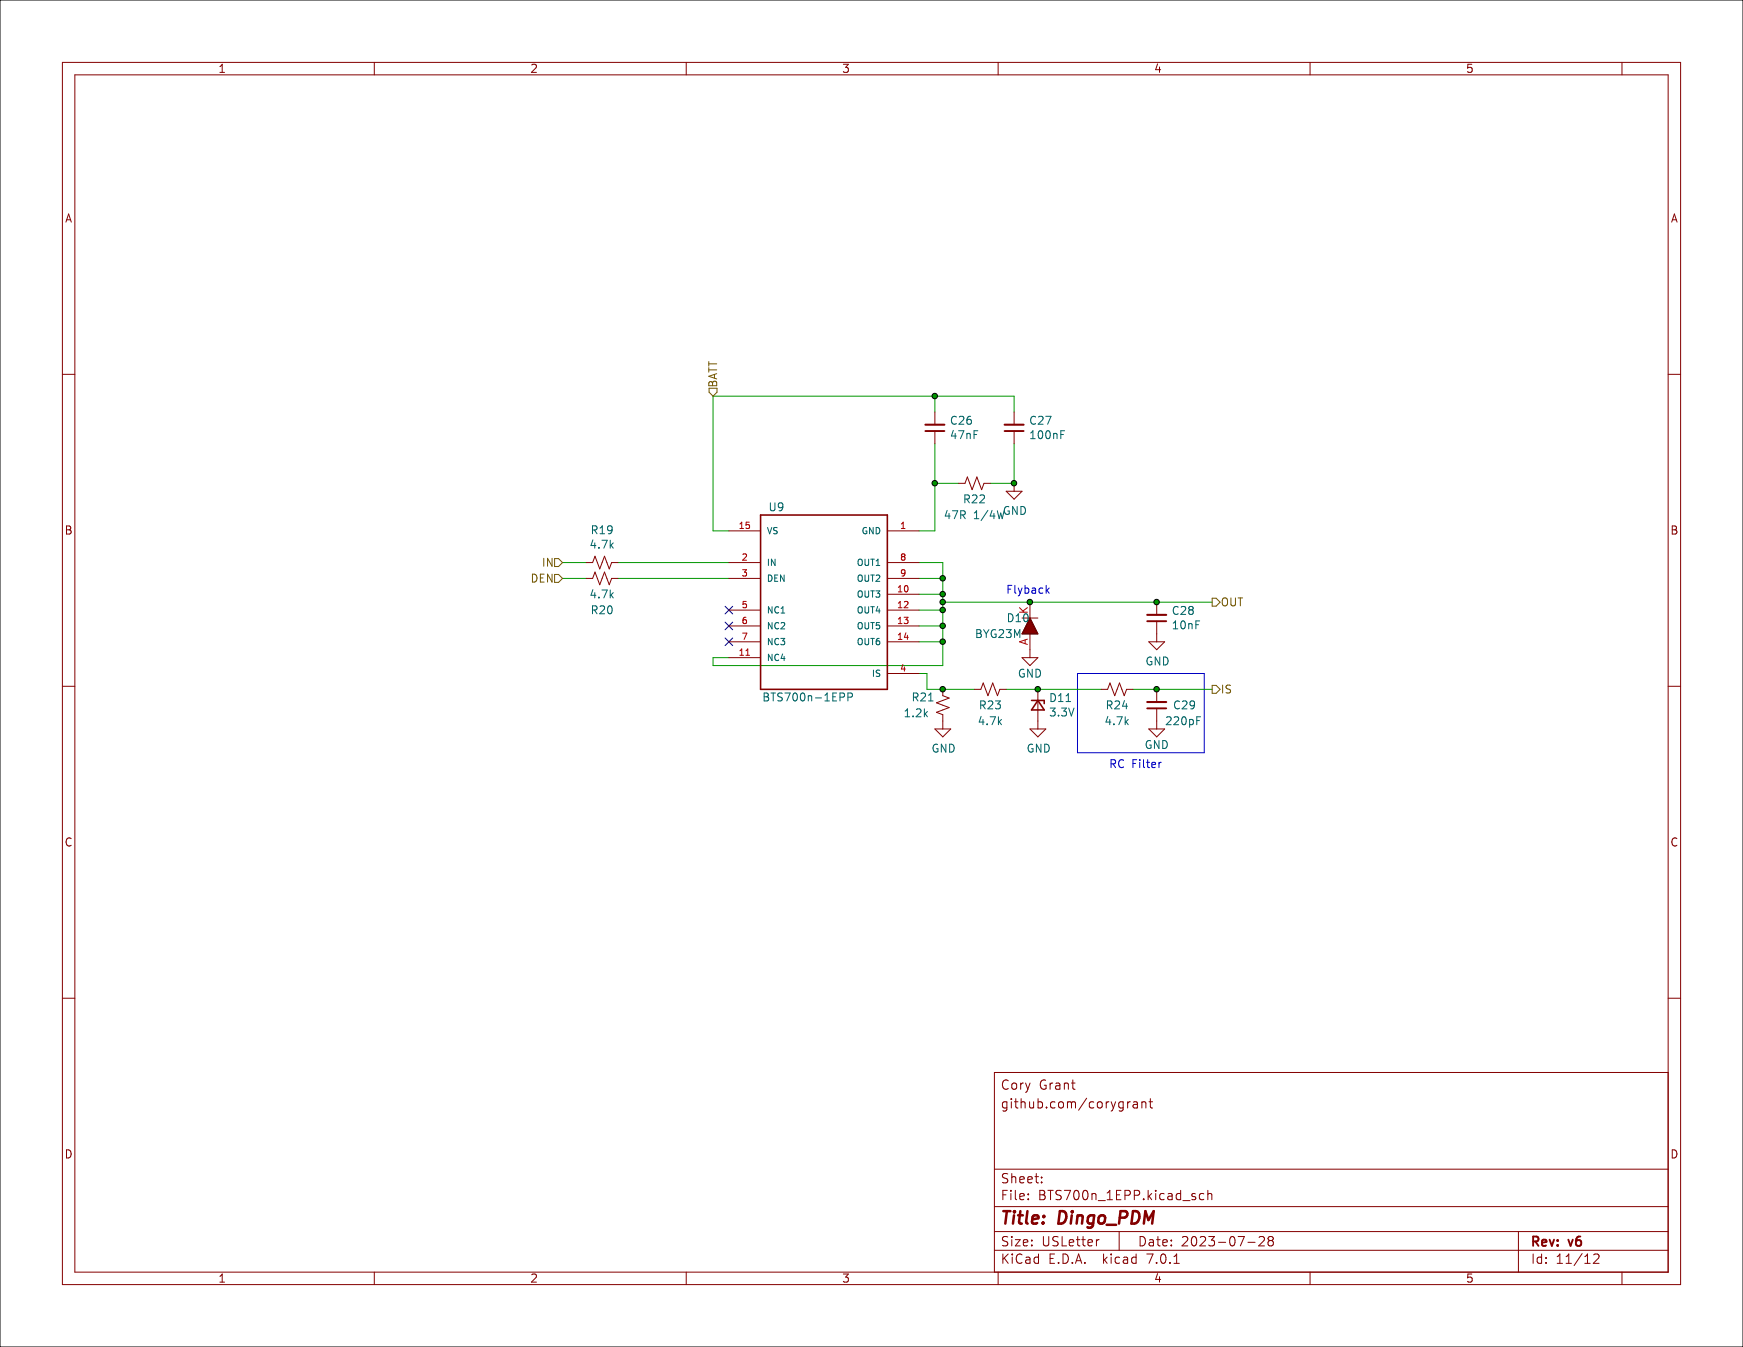
[picture p186: page 9]

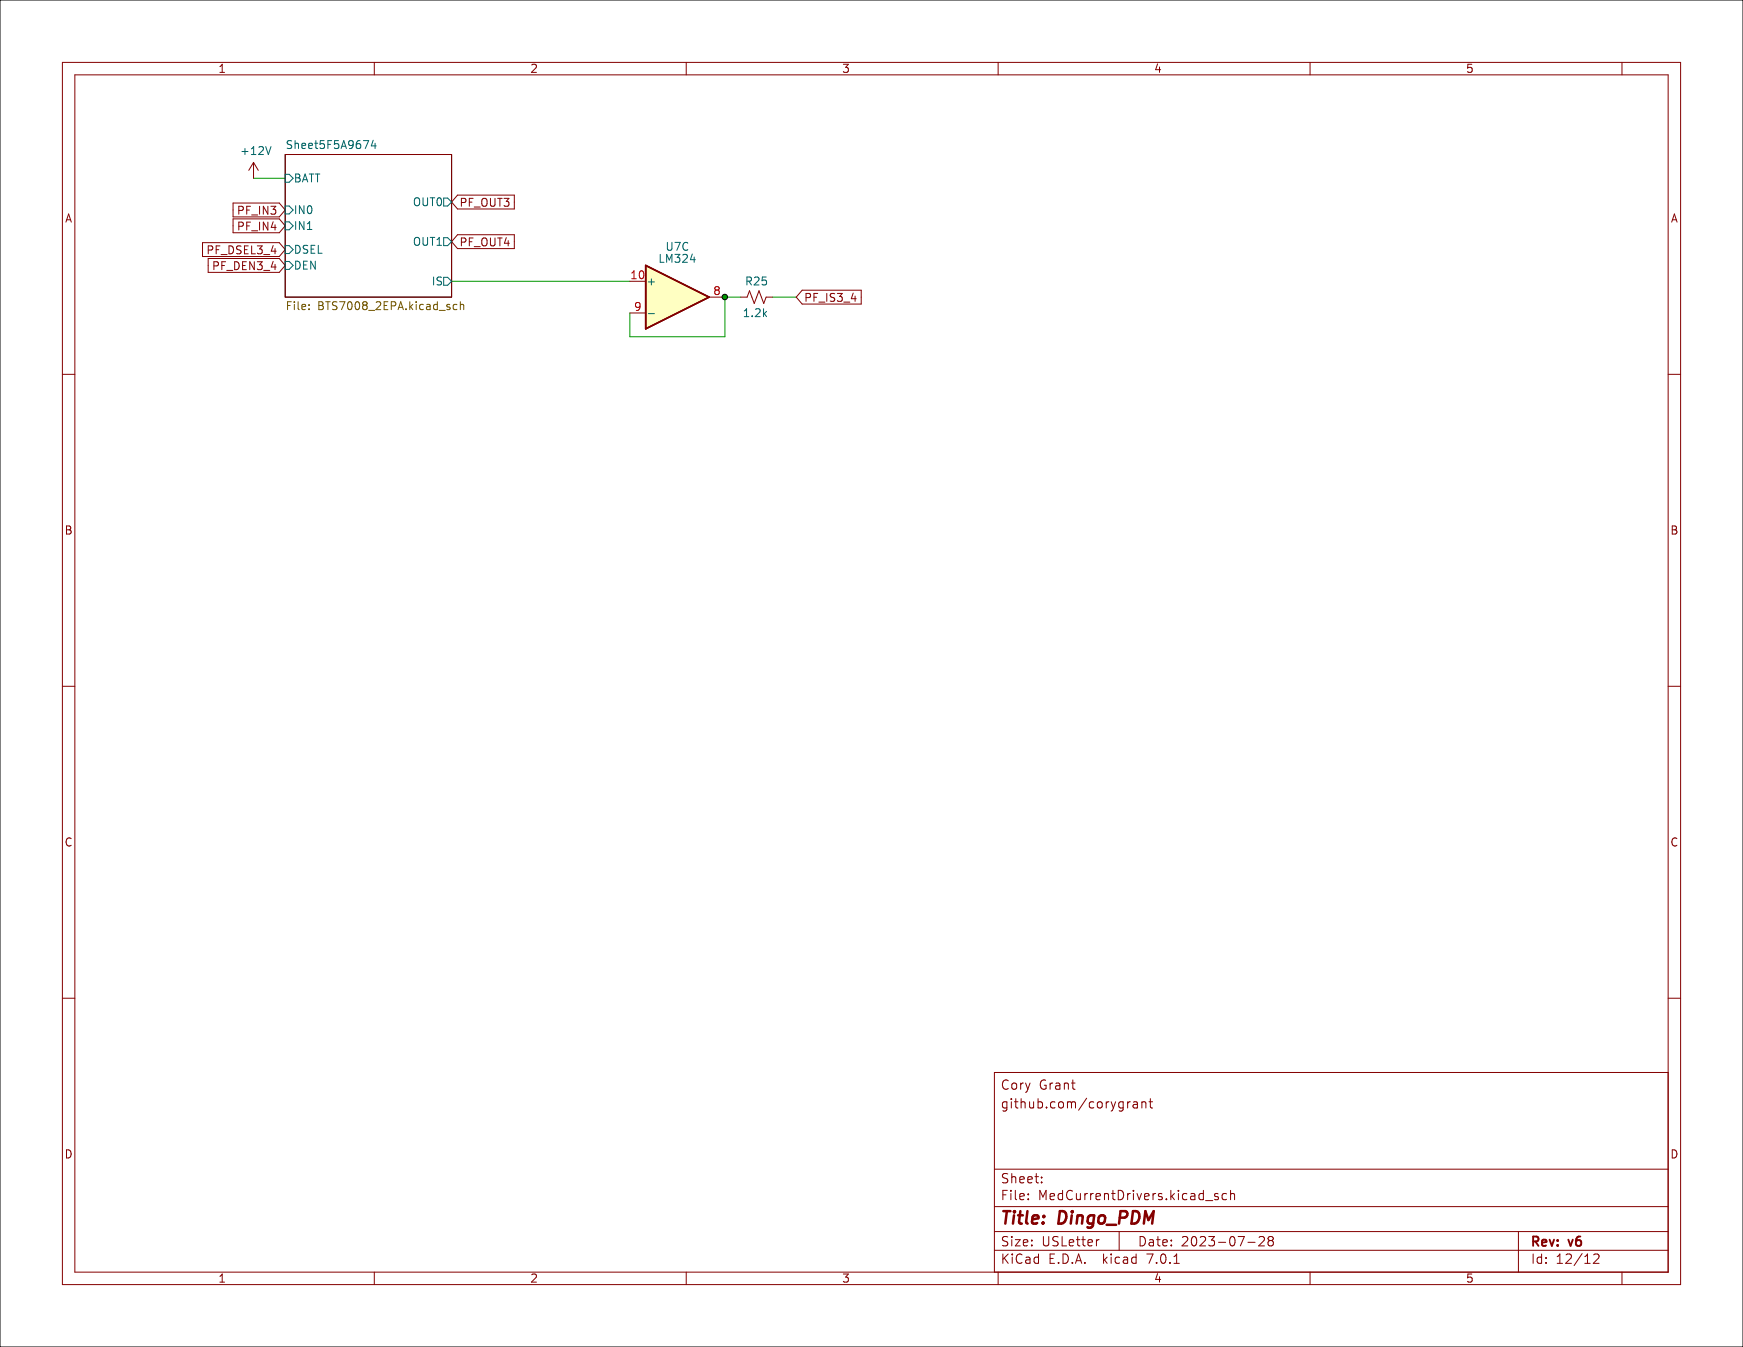
[picture p187: page 10]

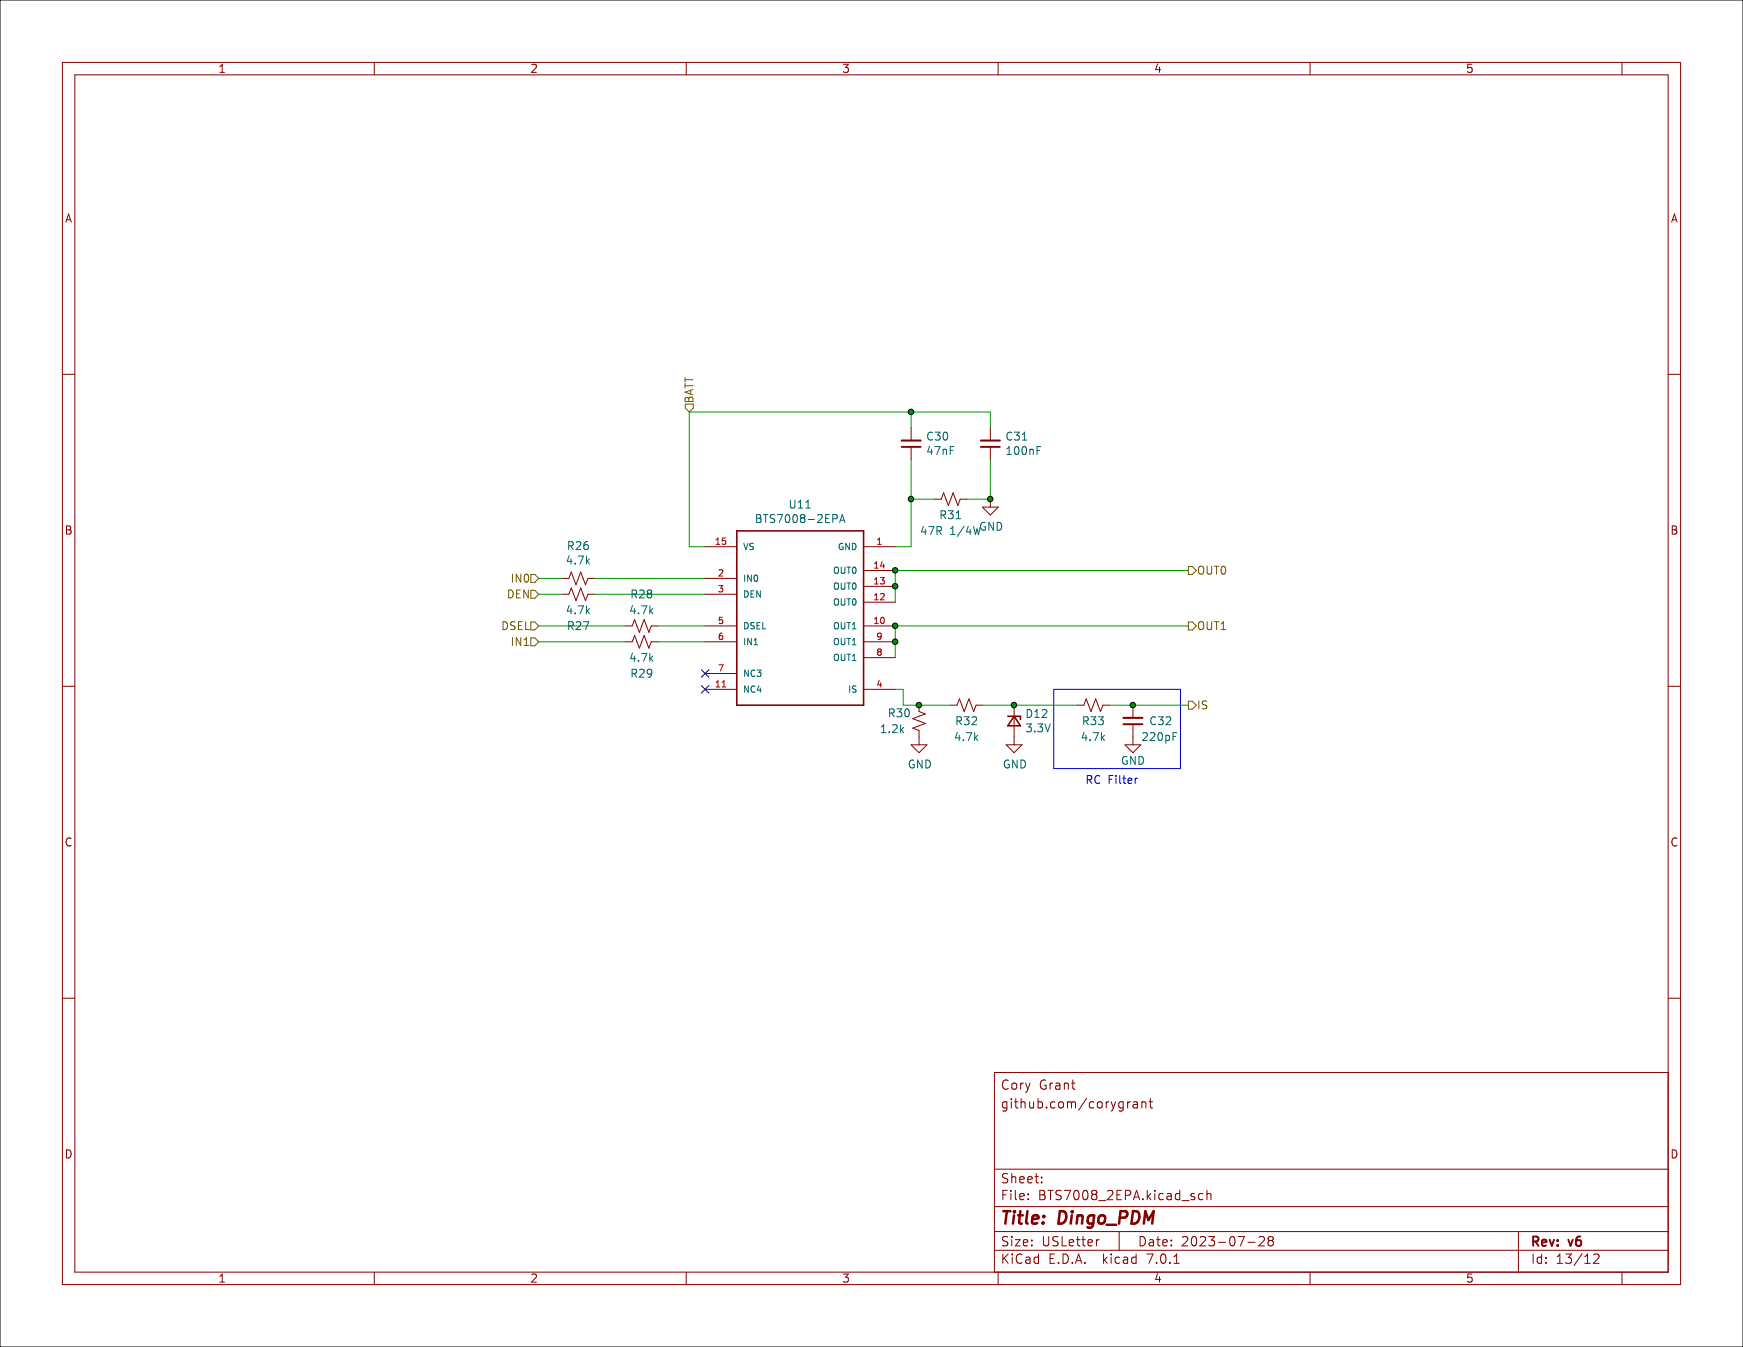
[picture p188: page 11]

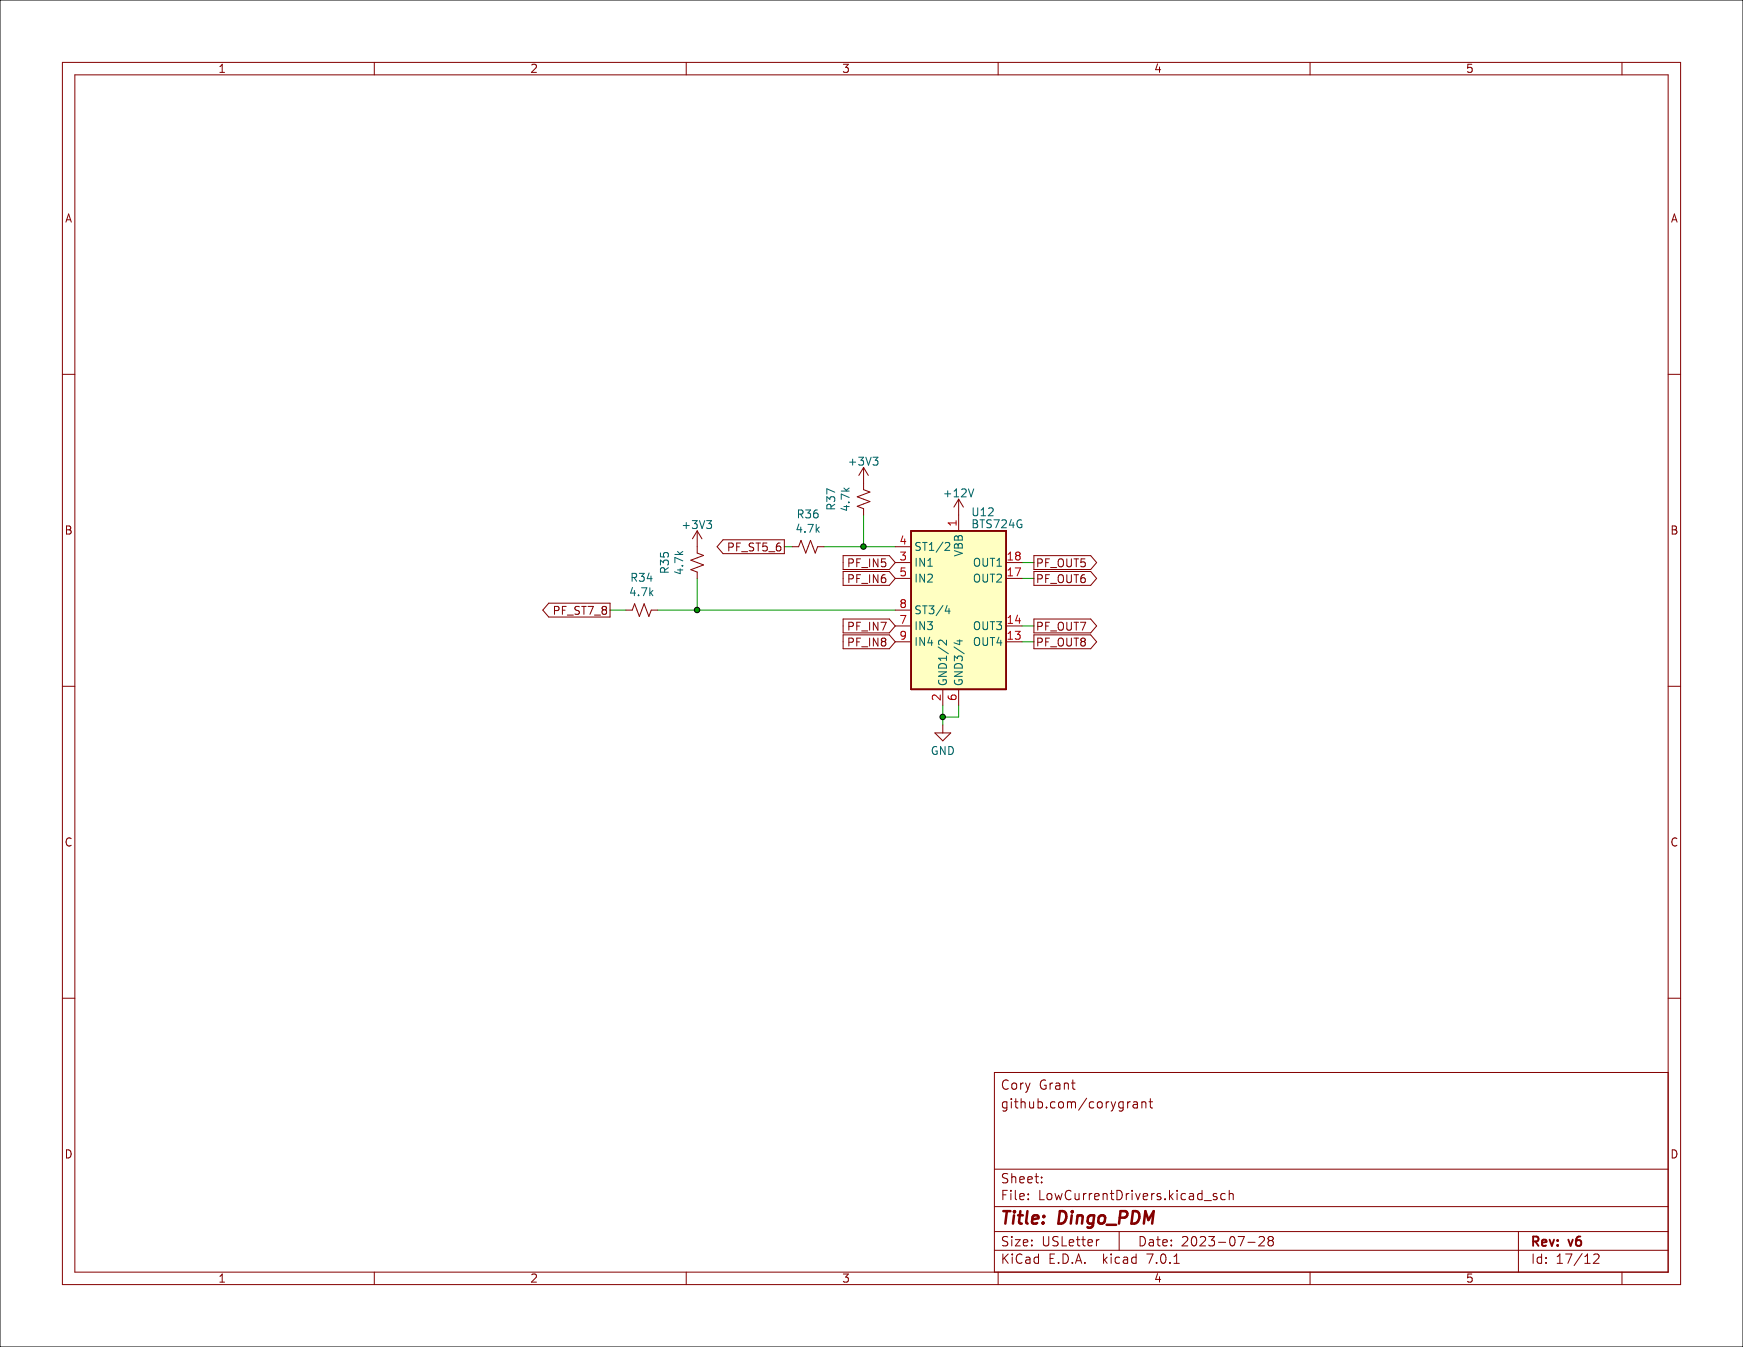
[picture p189: page 12]
