corygrant/dingoPDM/Export/V6/DingoPDM_HW_V6_Dark.pdf

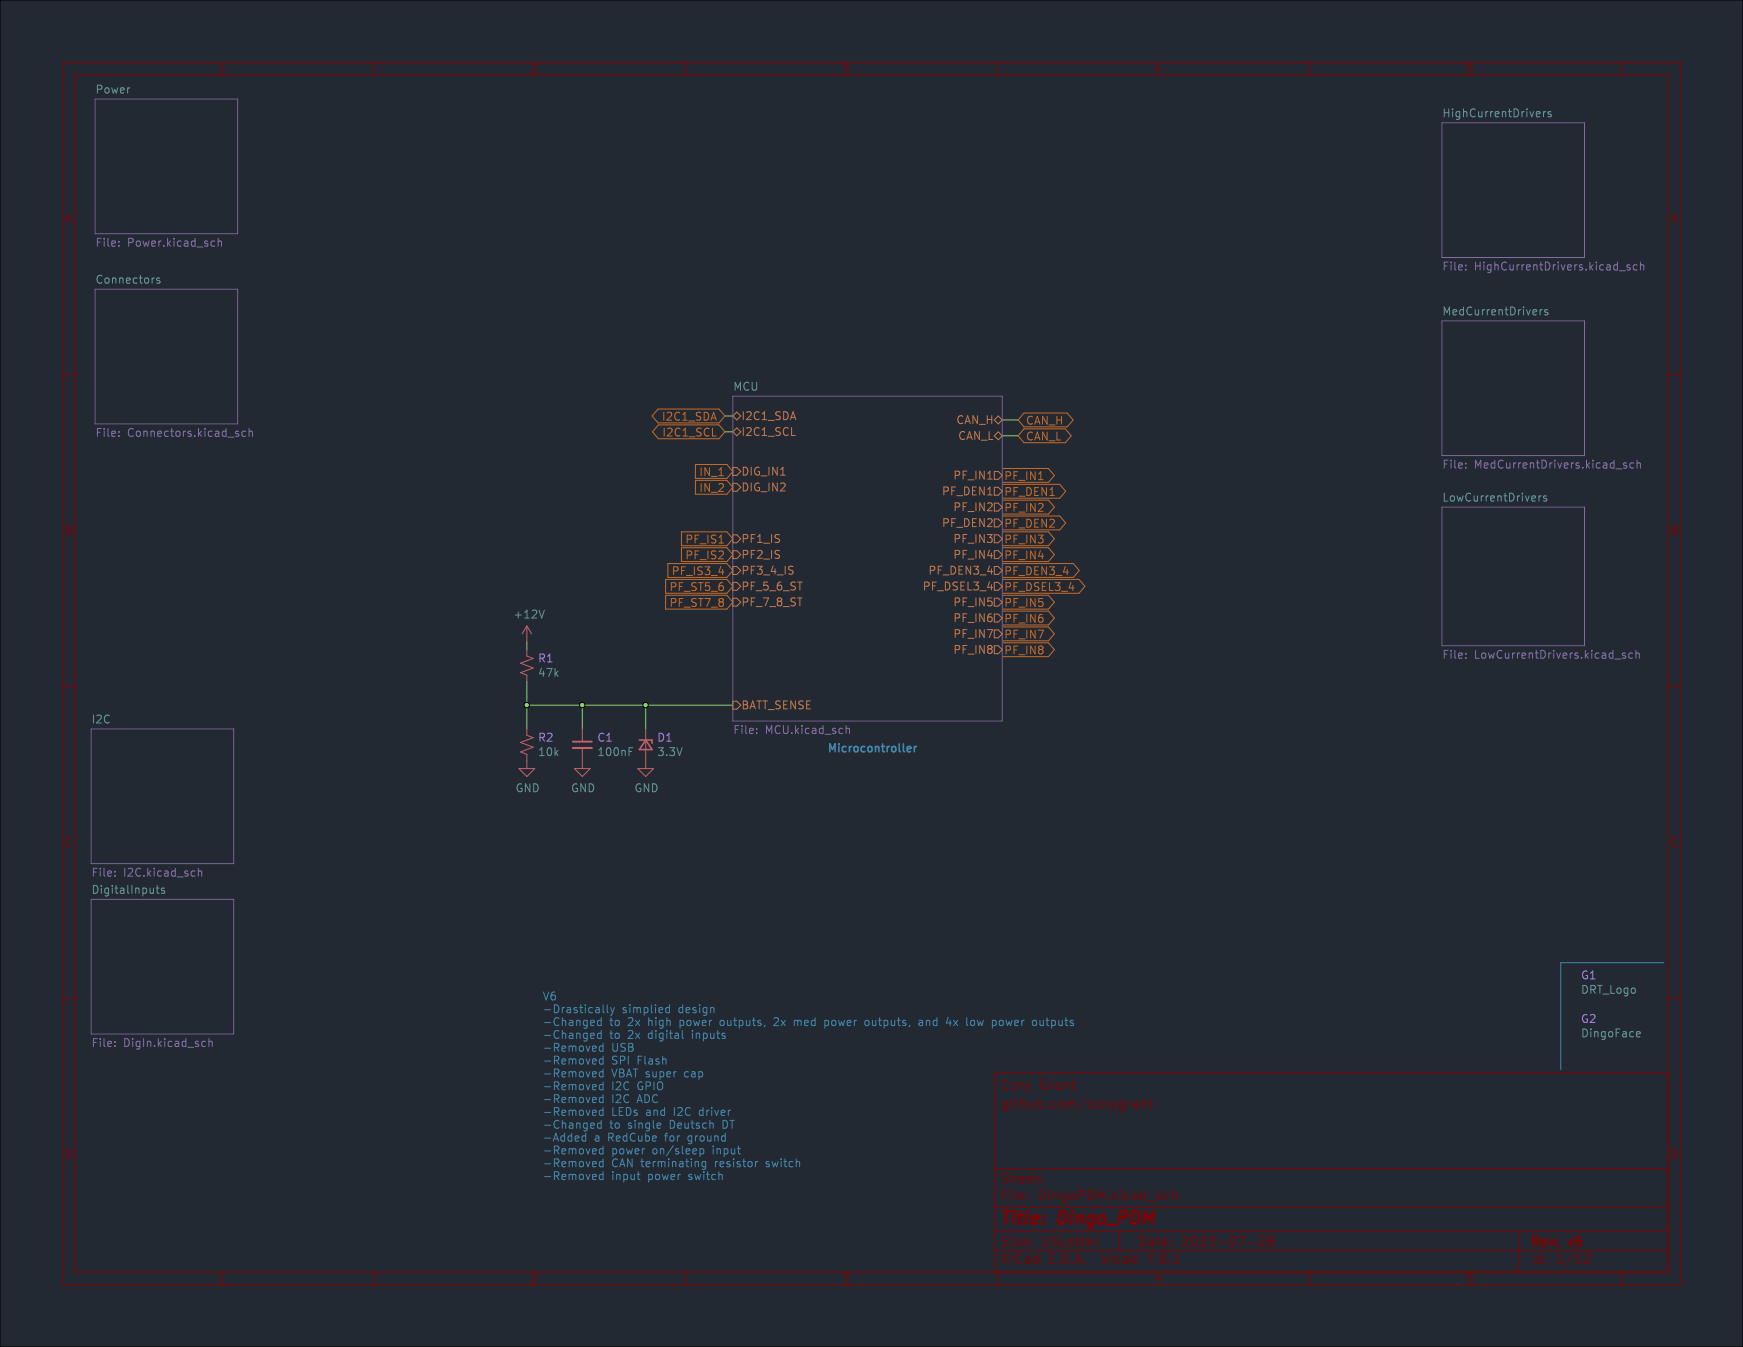
[picture p190: page 1]

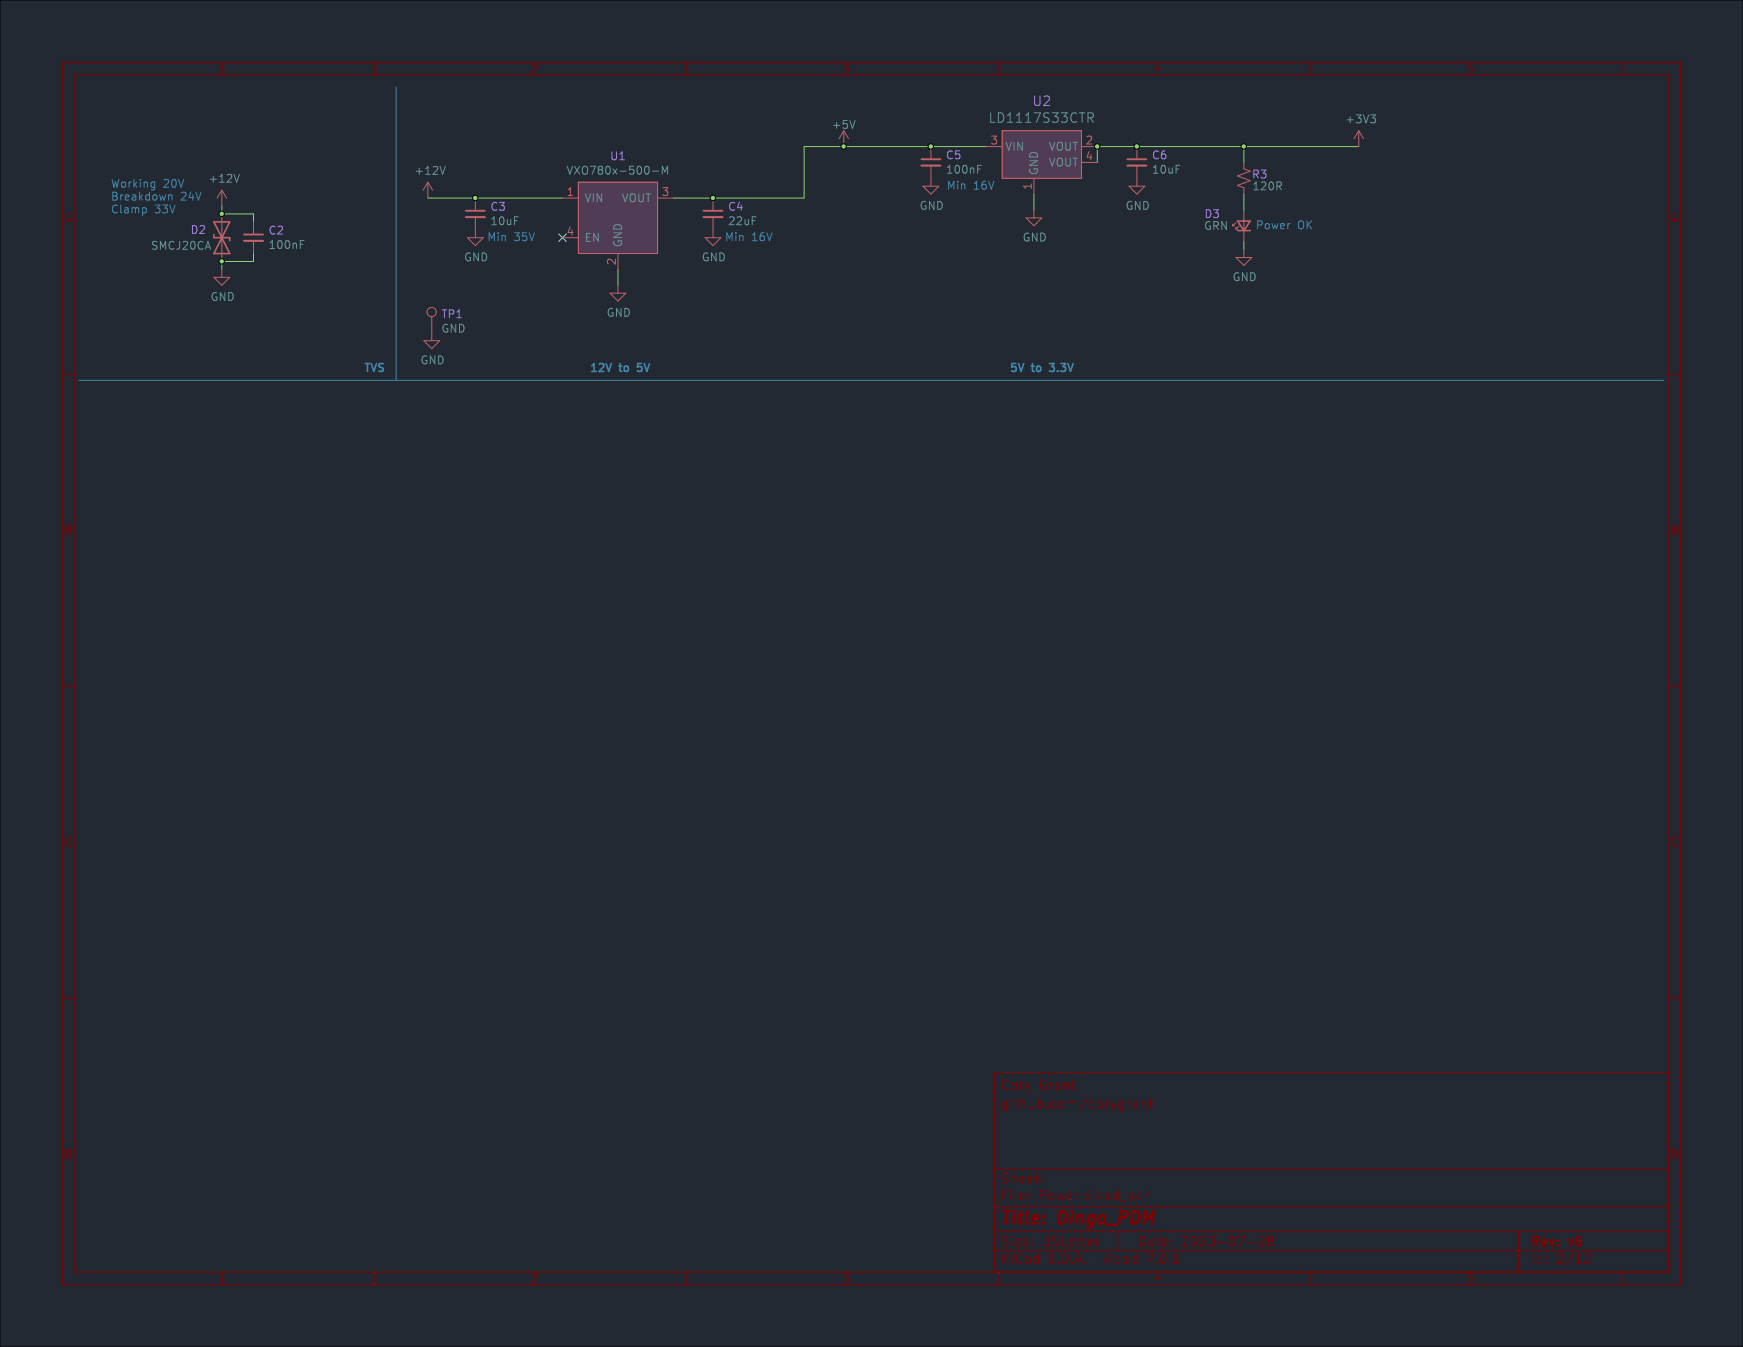
[picture p191: page 2]

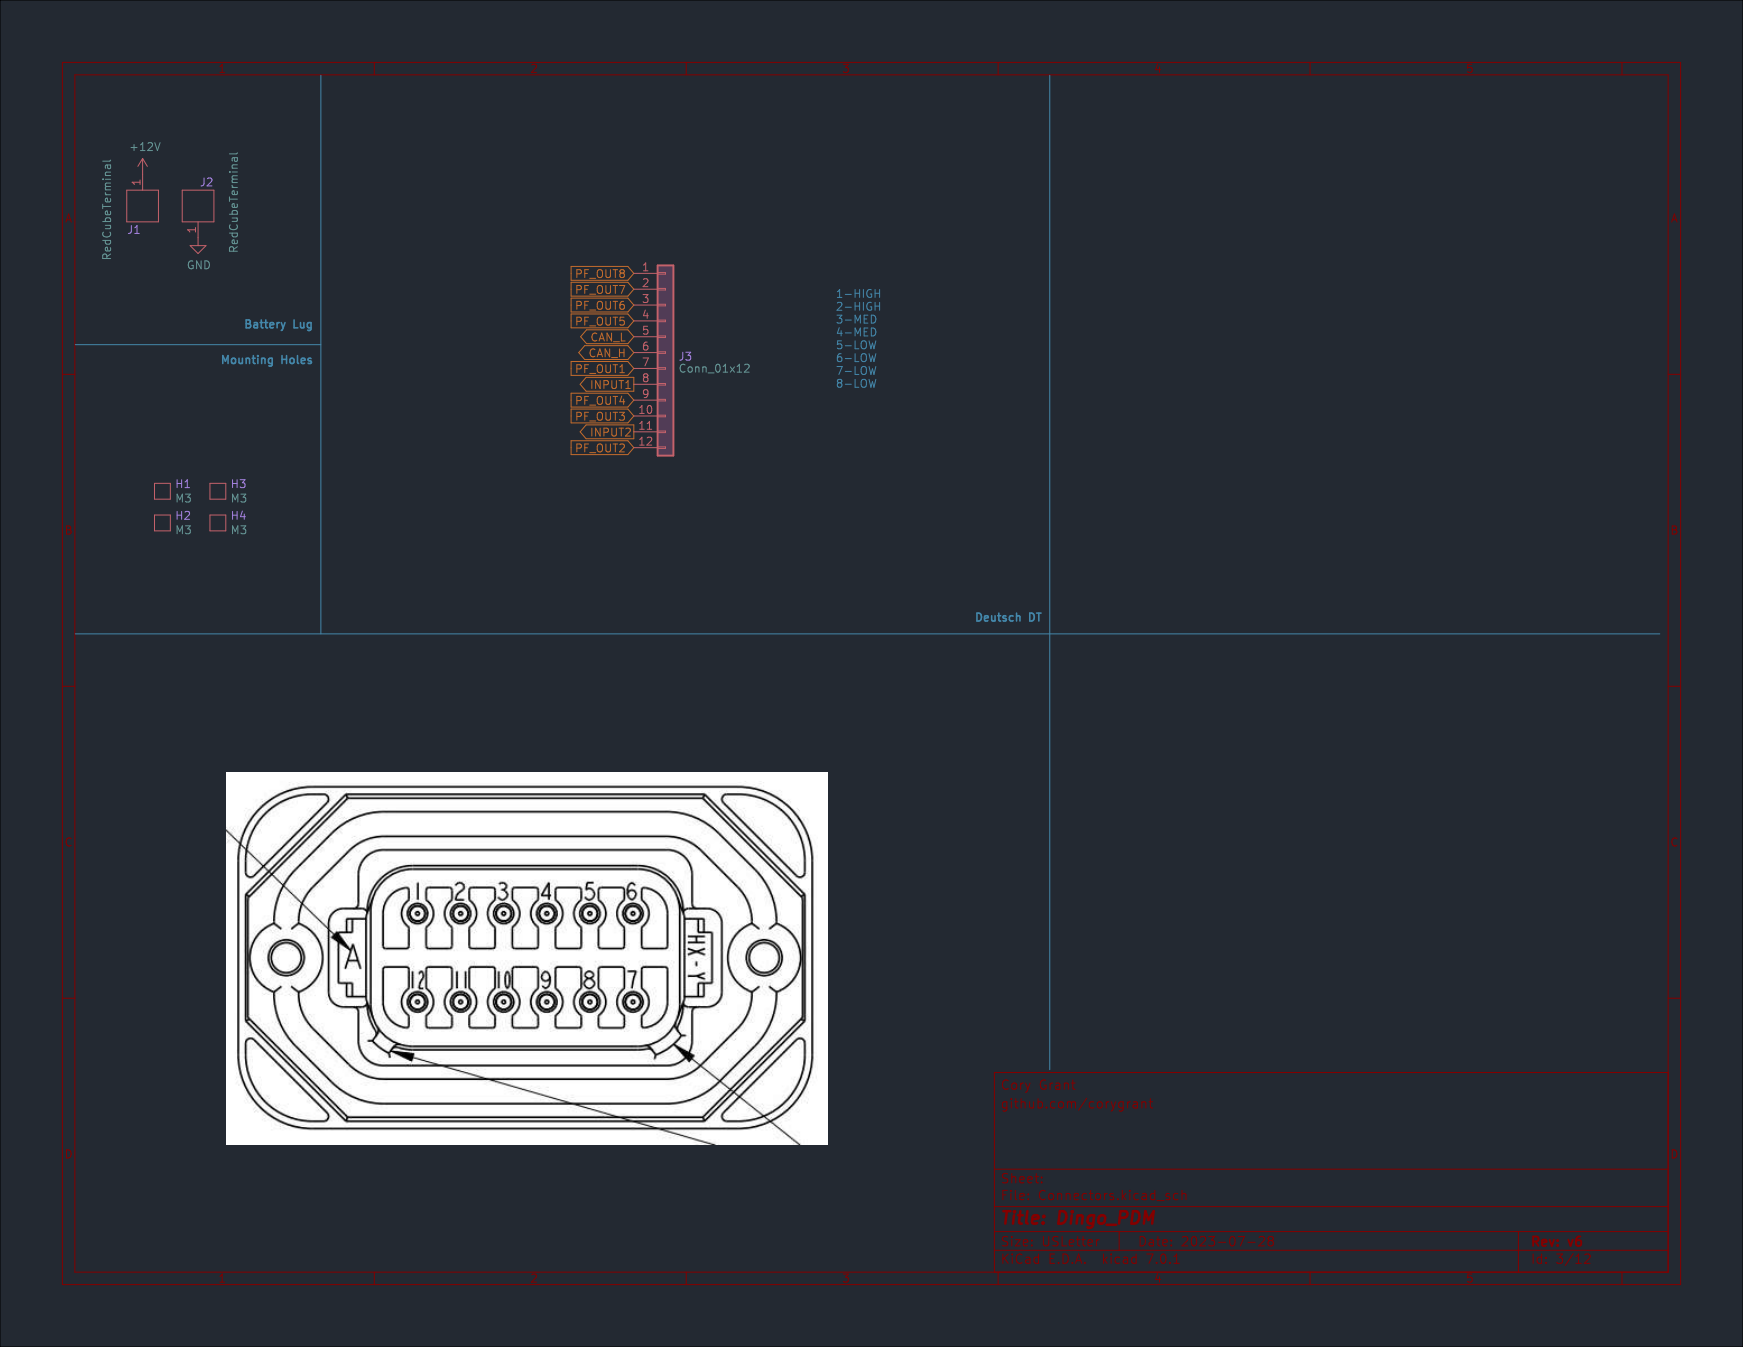
[picture p192: page 3]

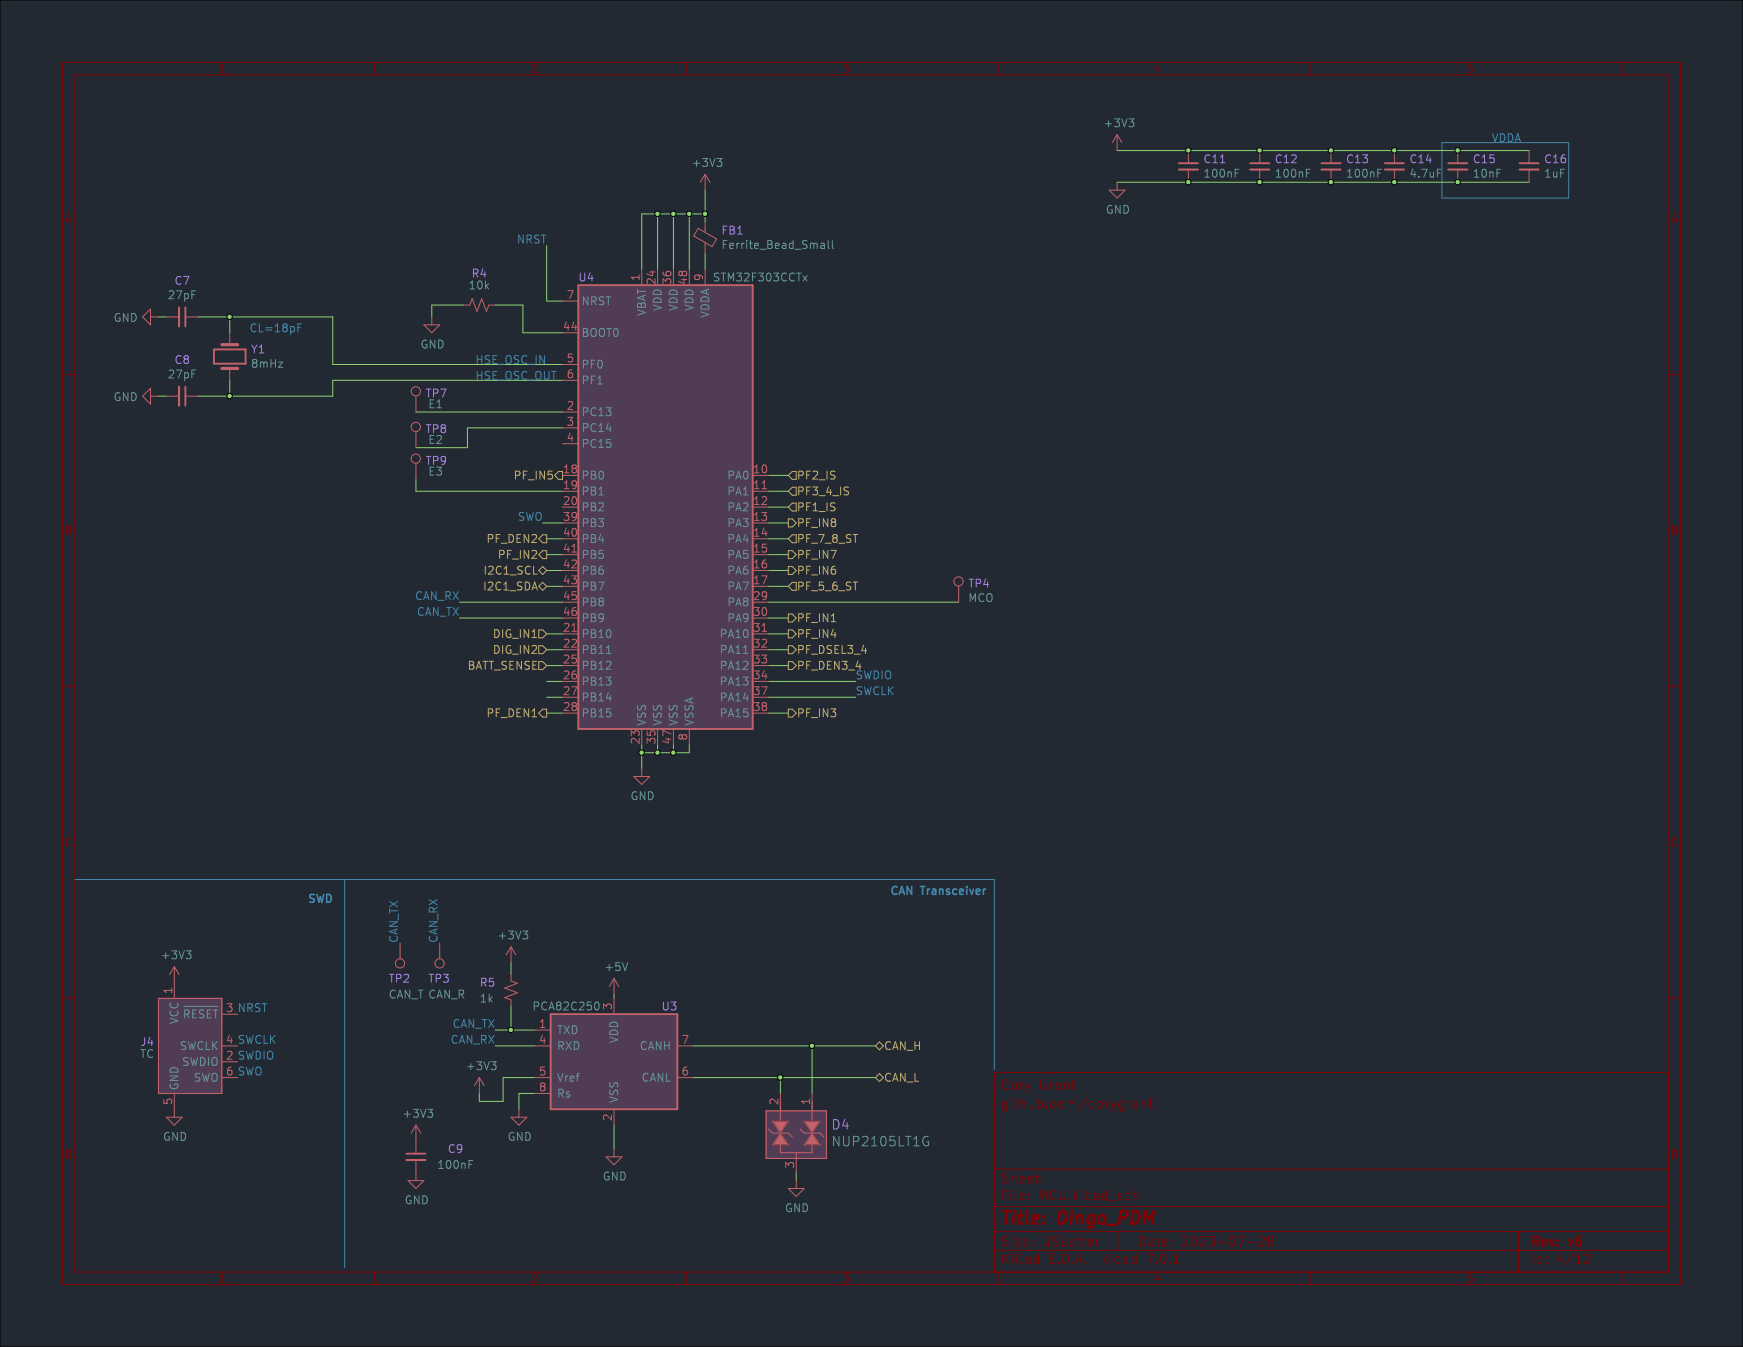
[picture p193: page 4]

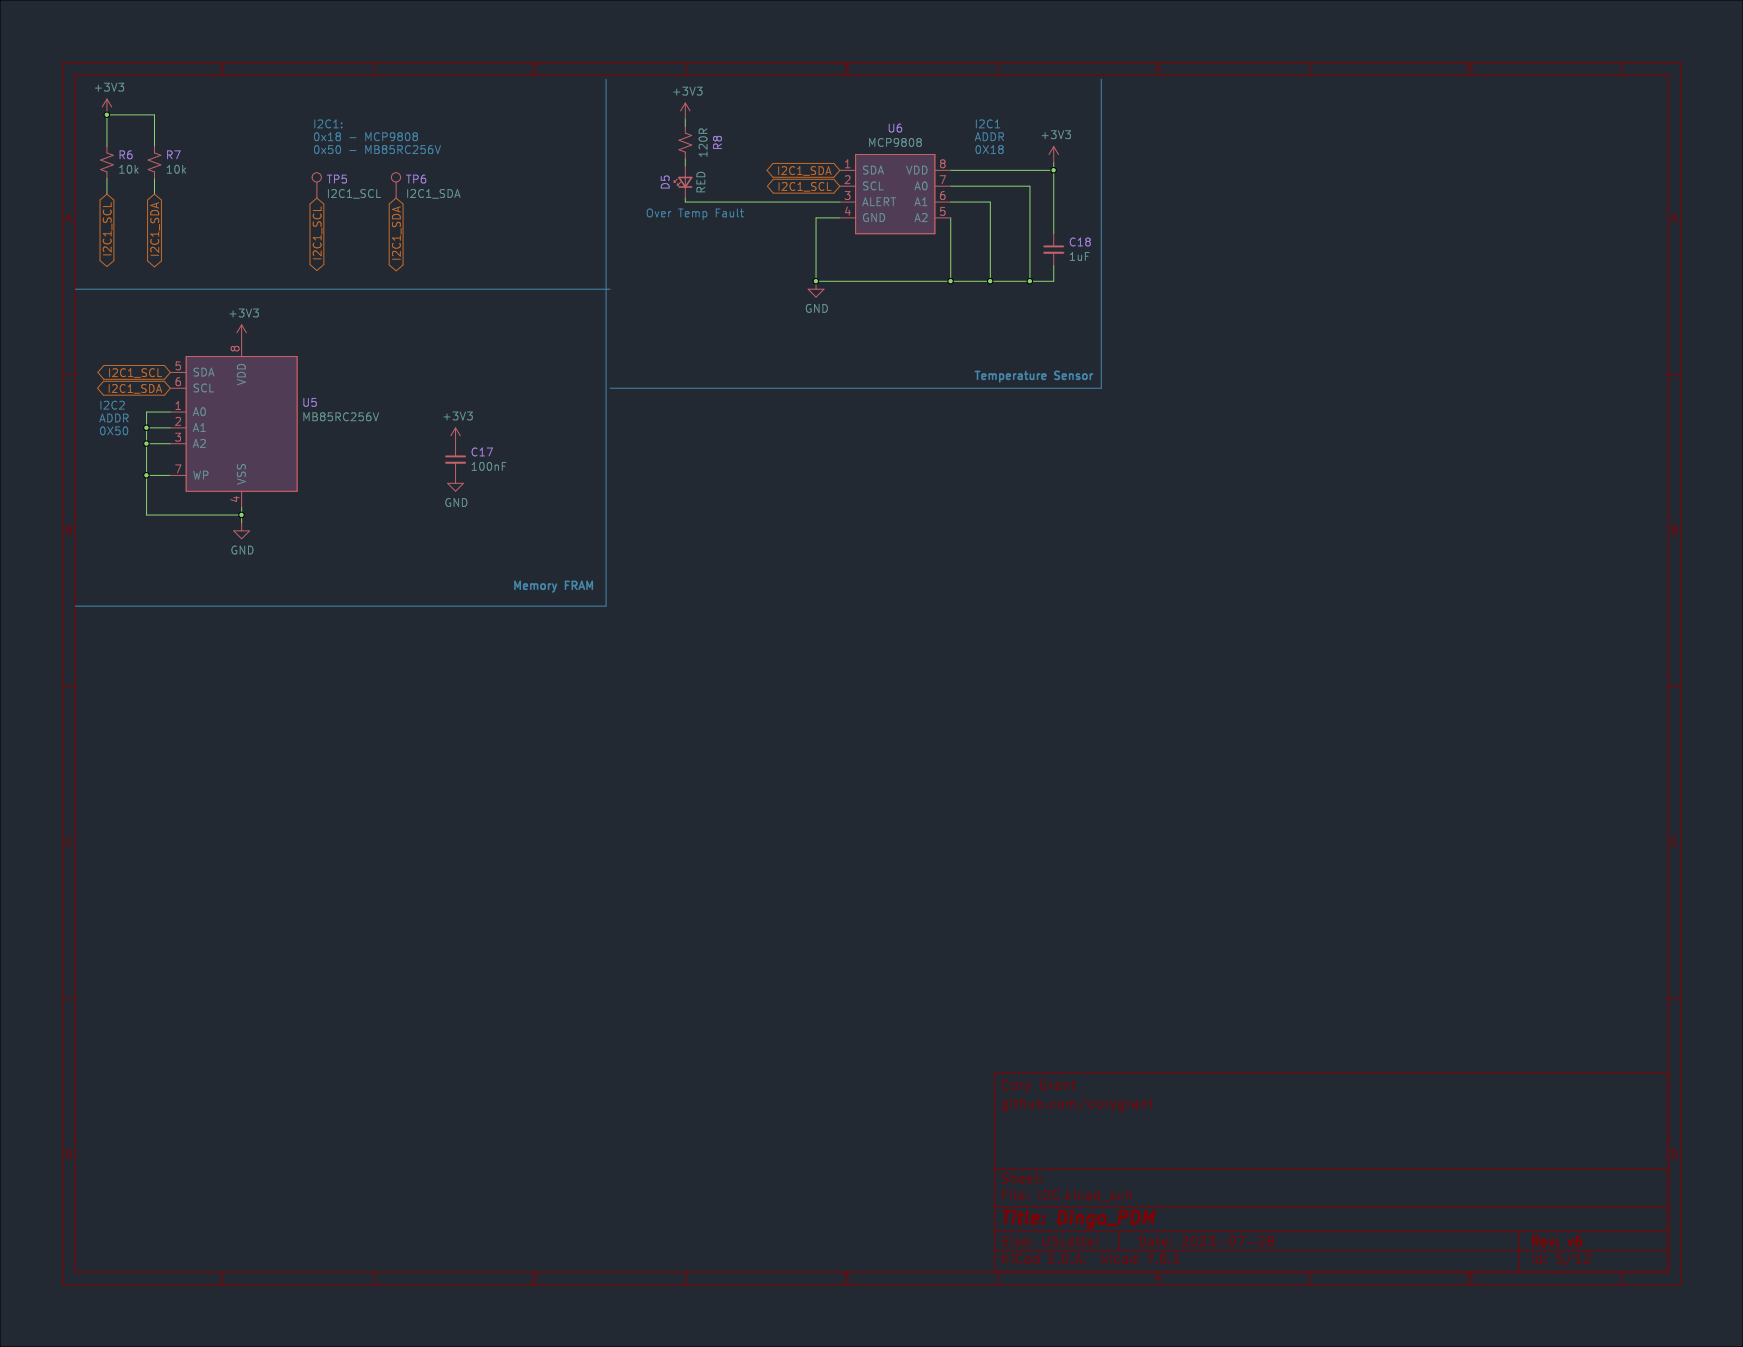
[picture p194: page 5]

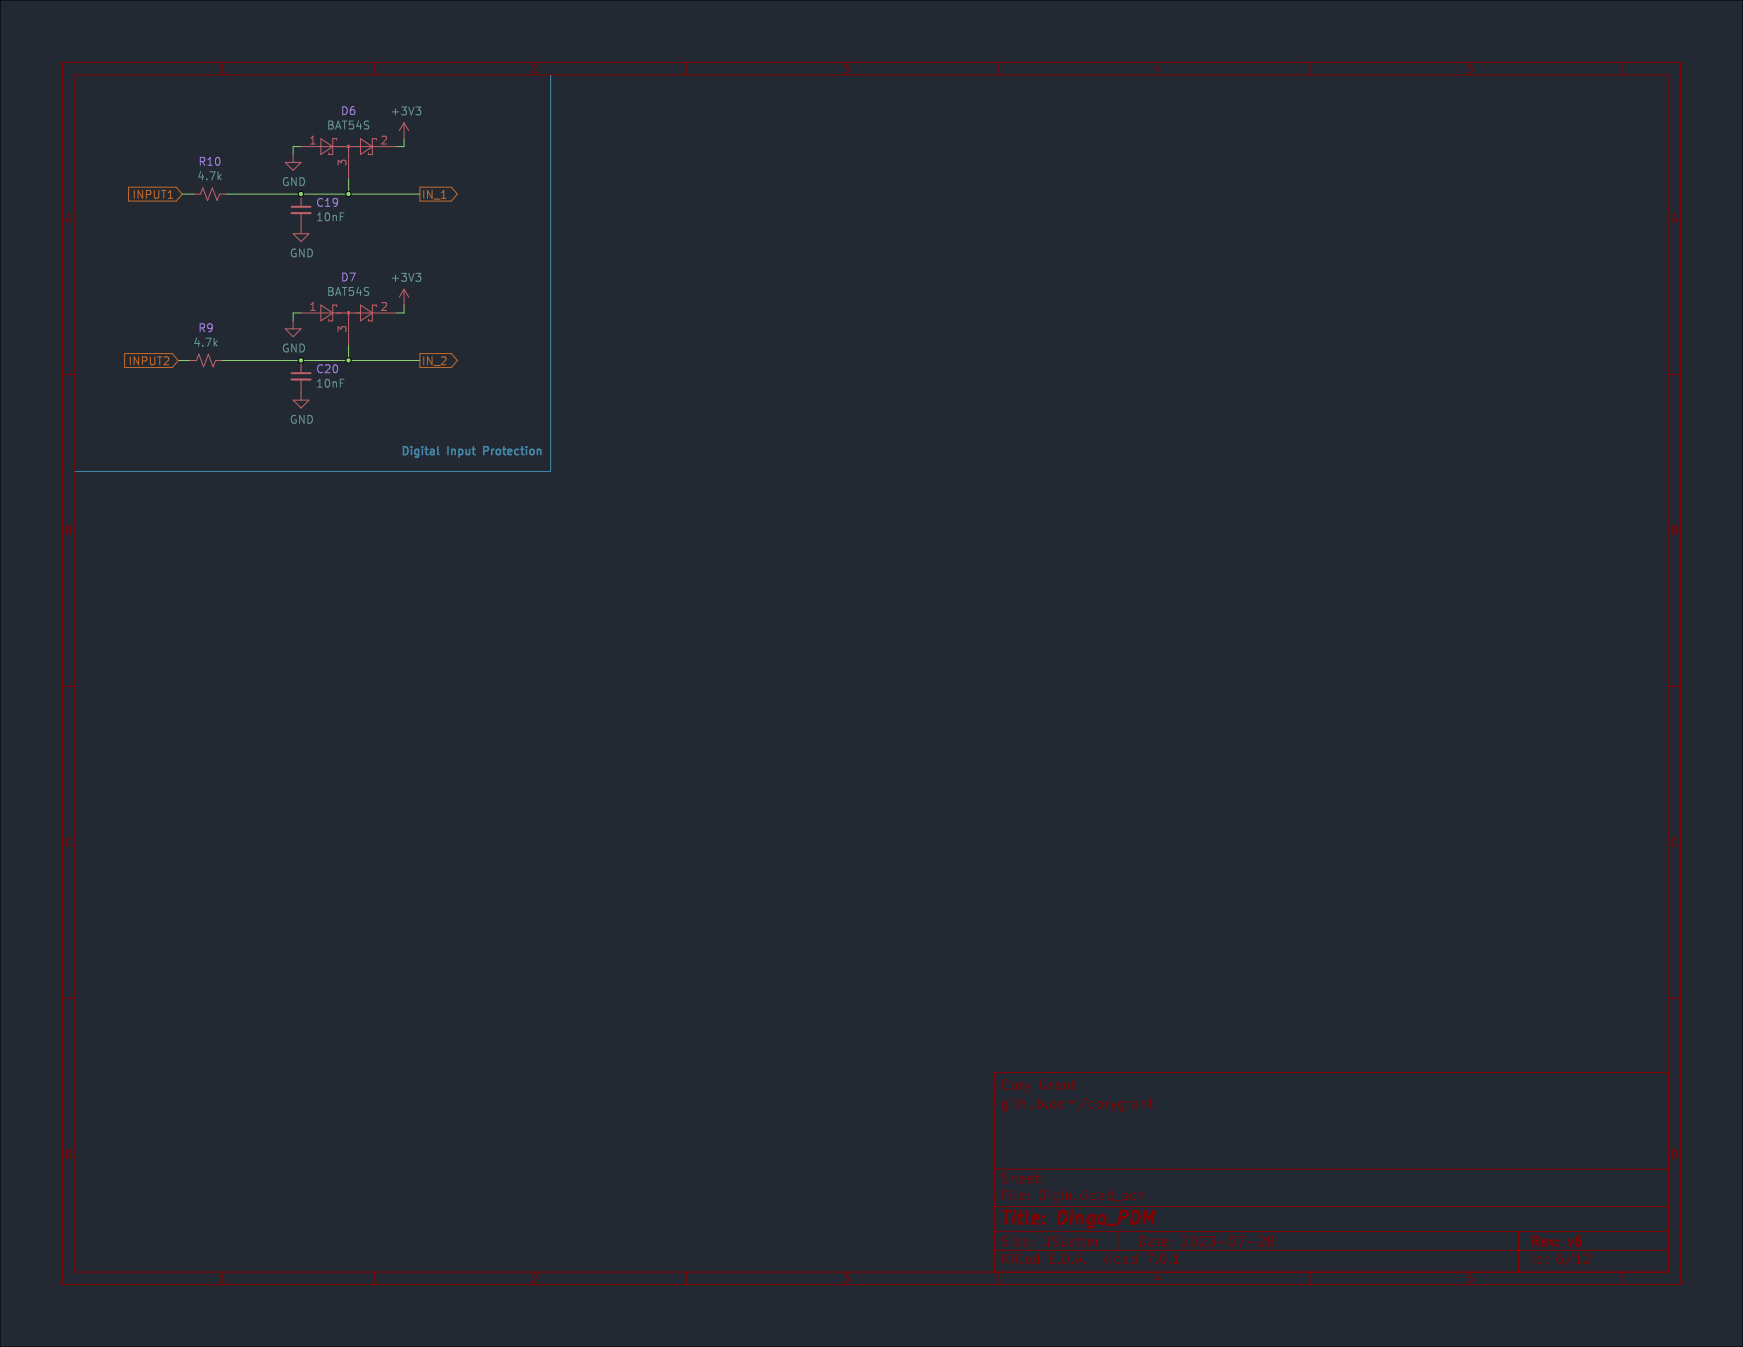
[picture p195: page 6]

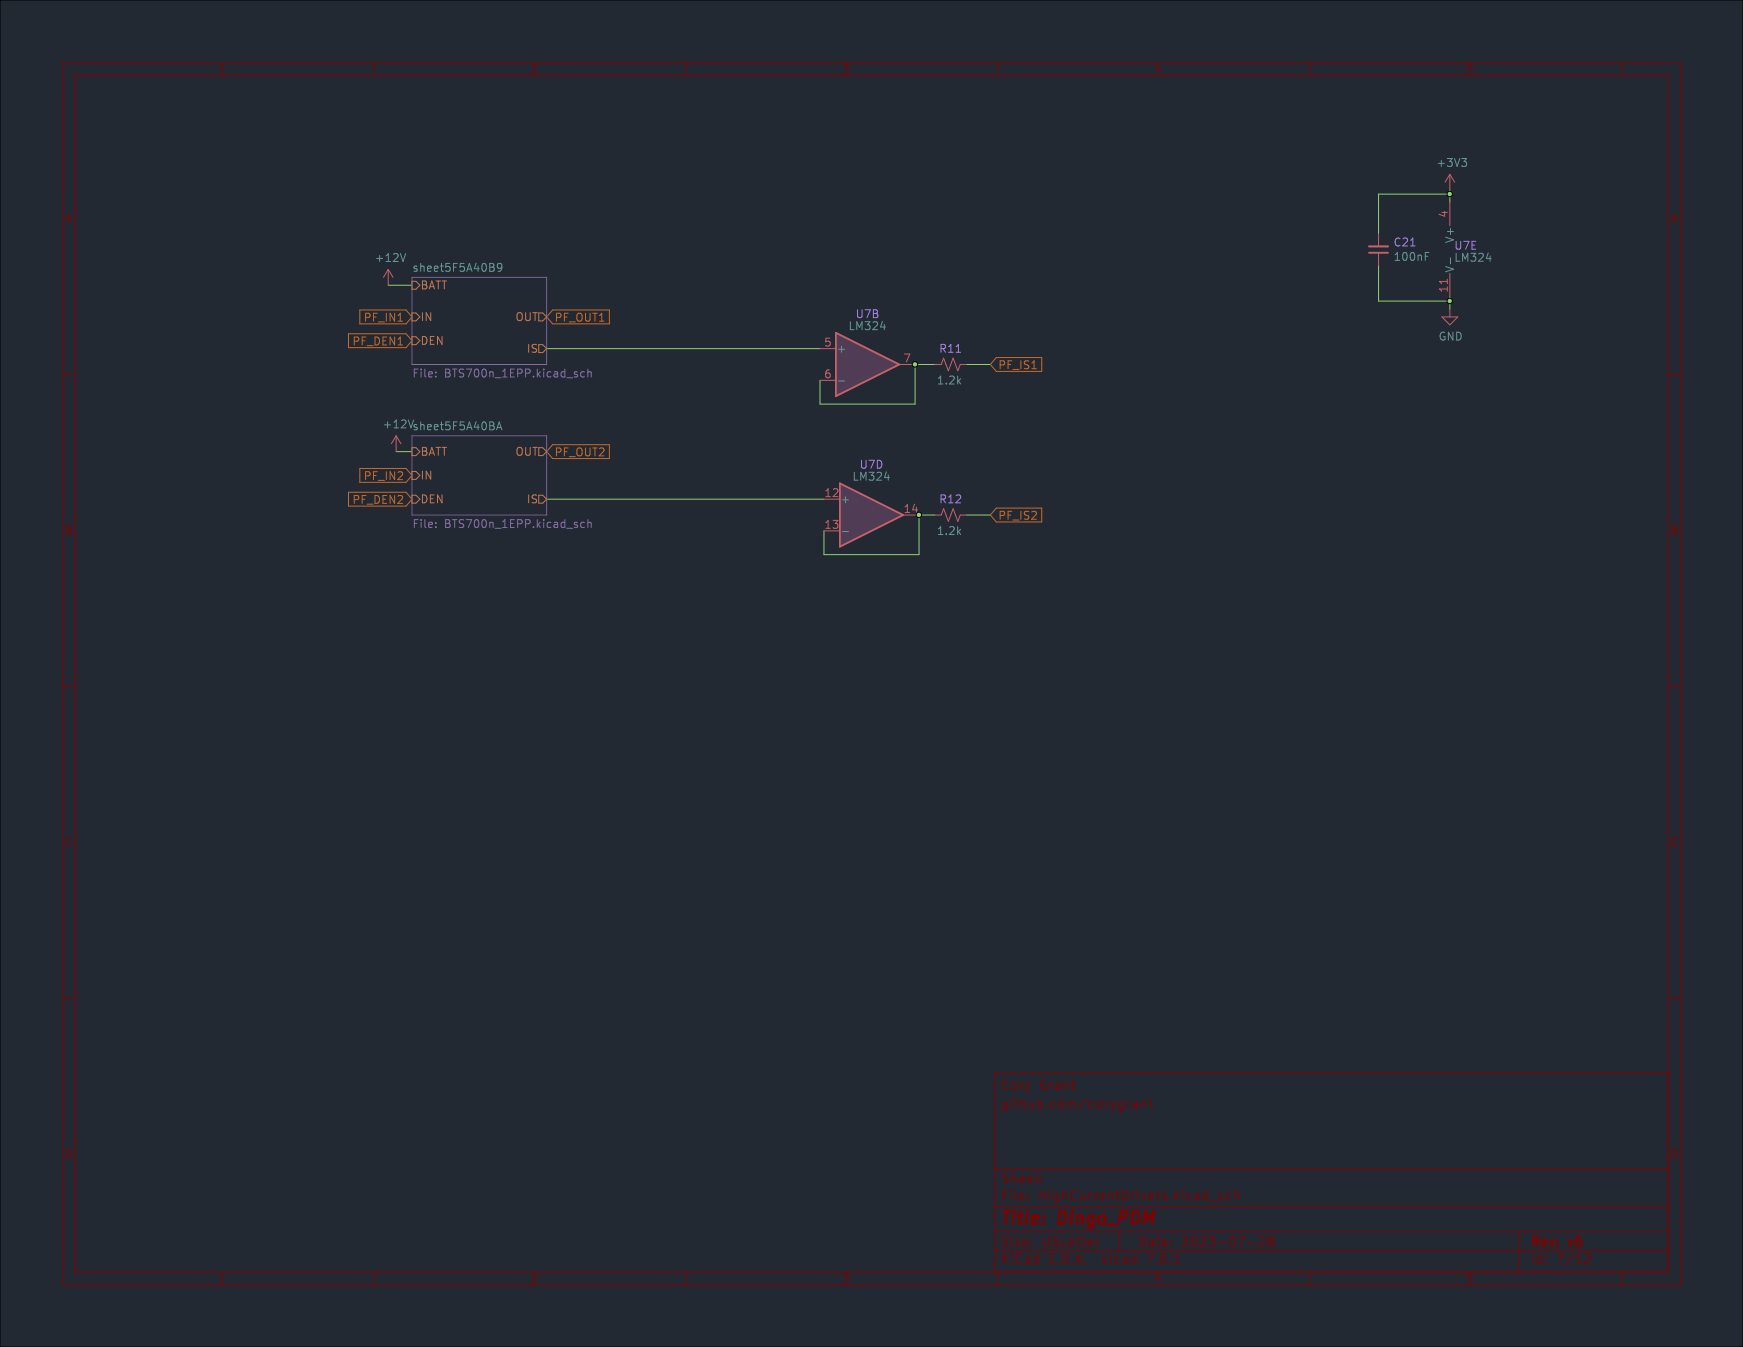
[picture p196: page 7]

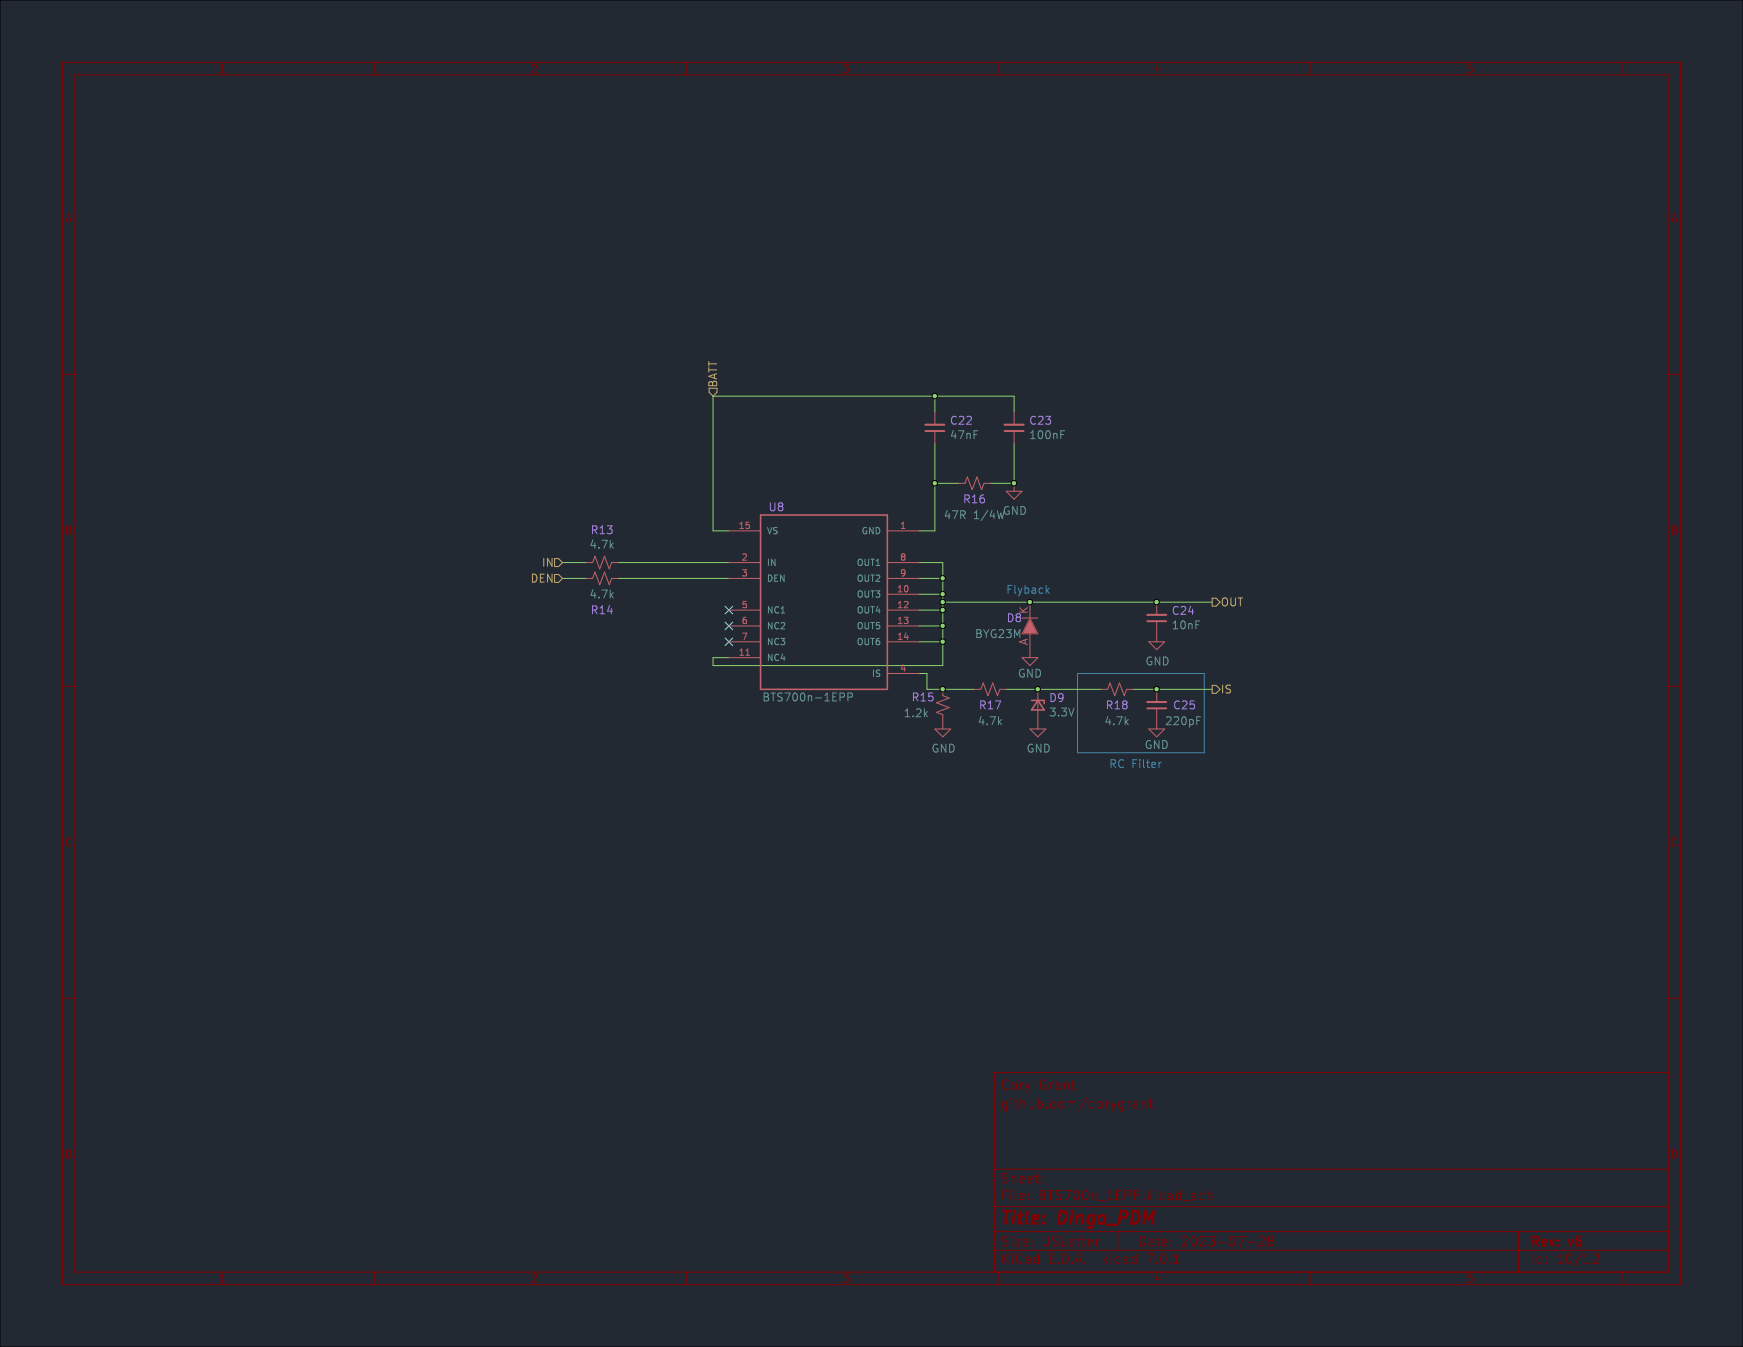
[picture p197: page 8]

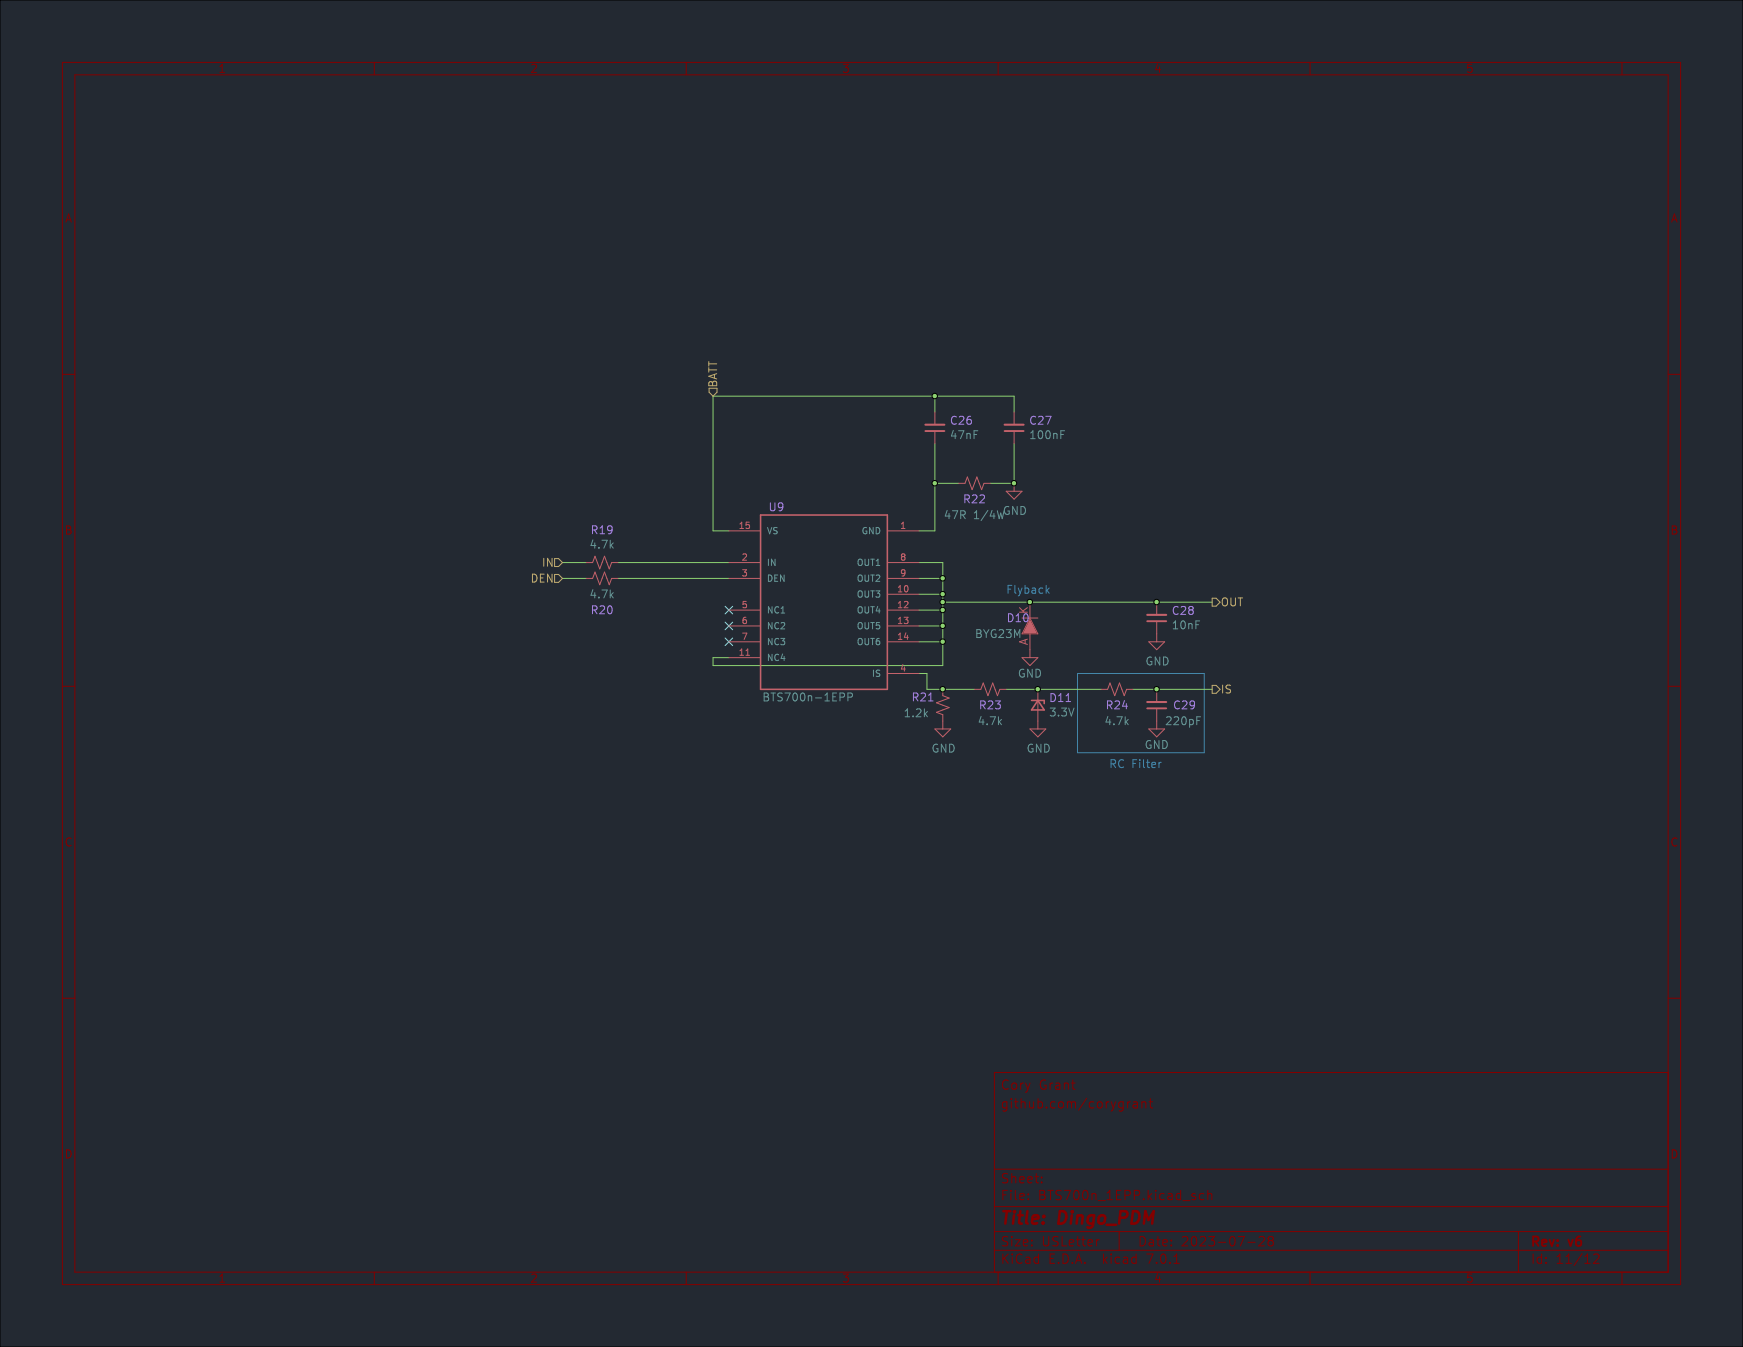
[picture p198: page 9]

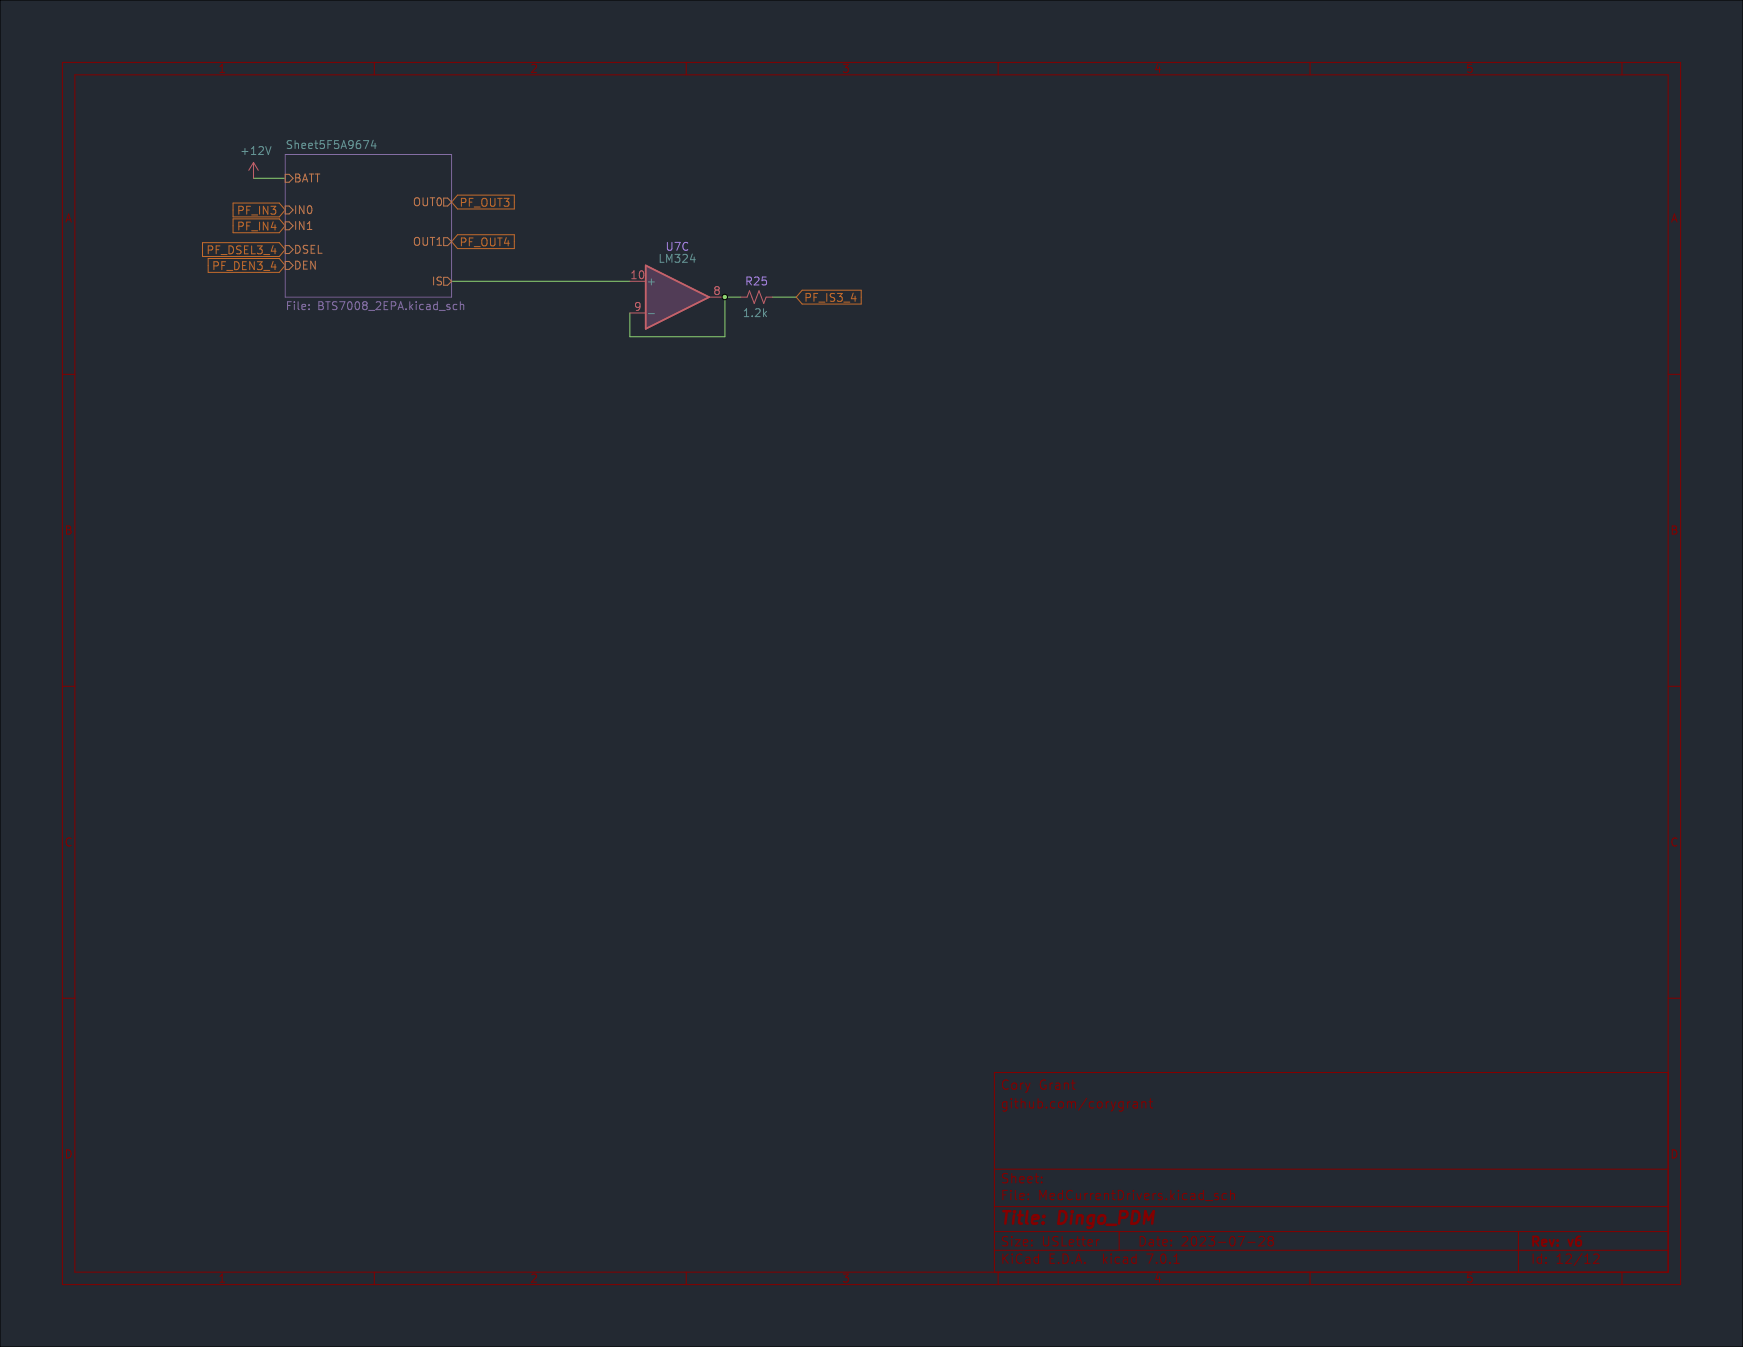
[picture p199: page 10]

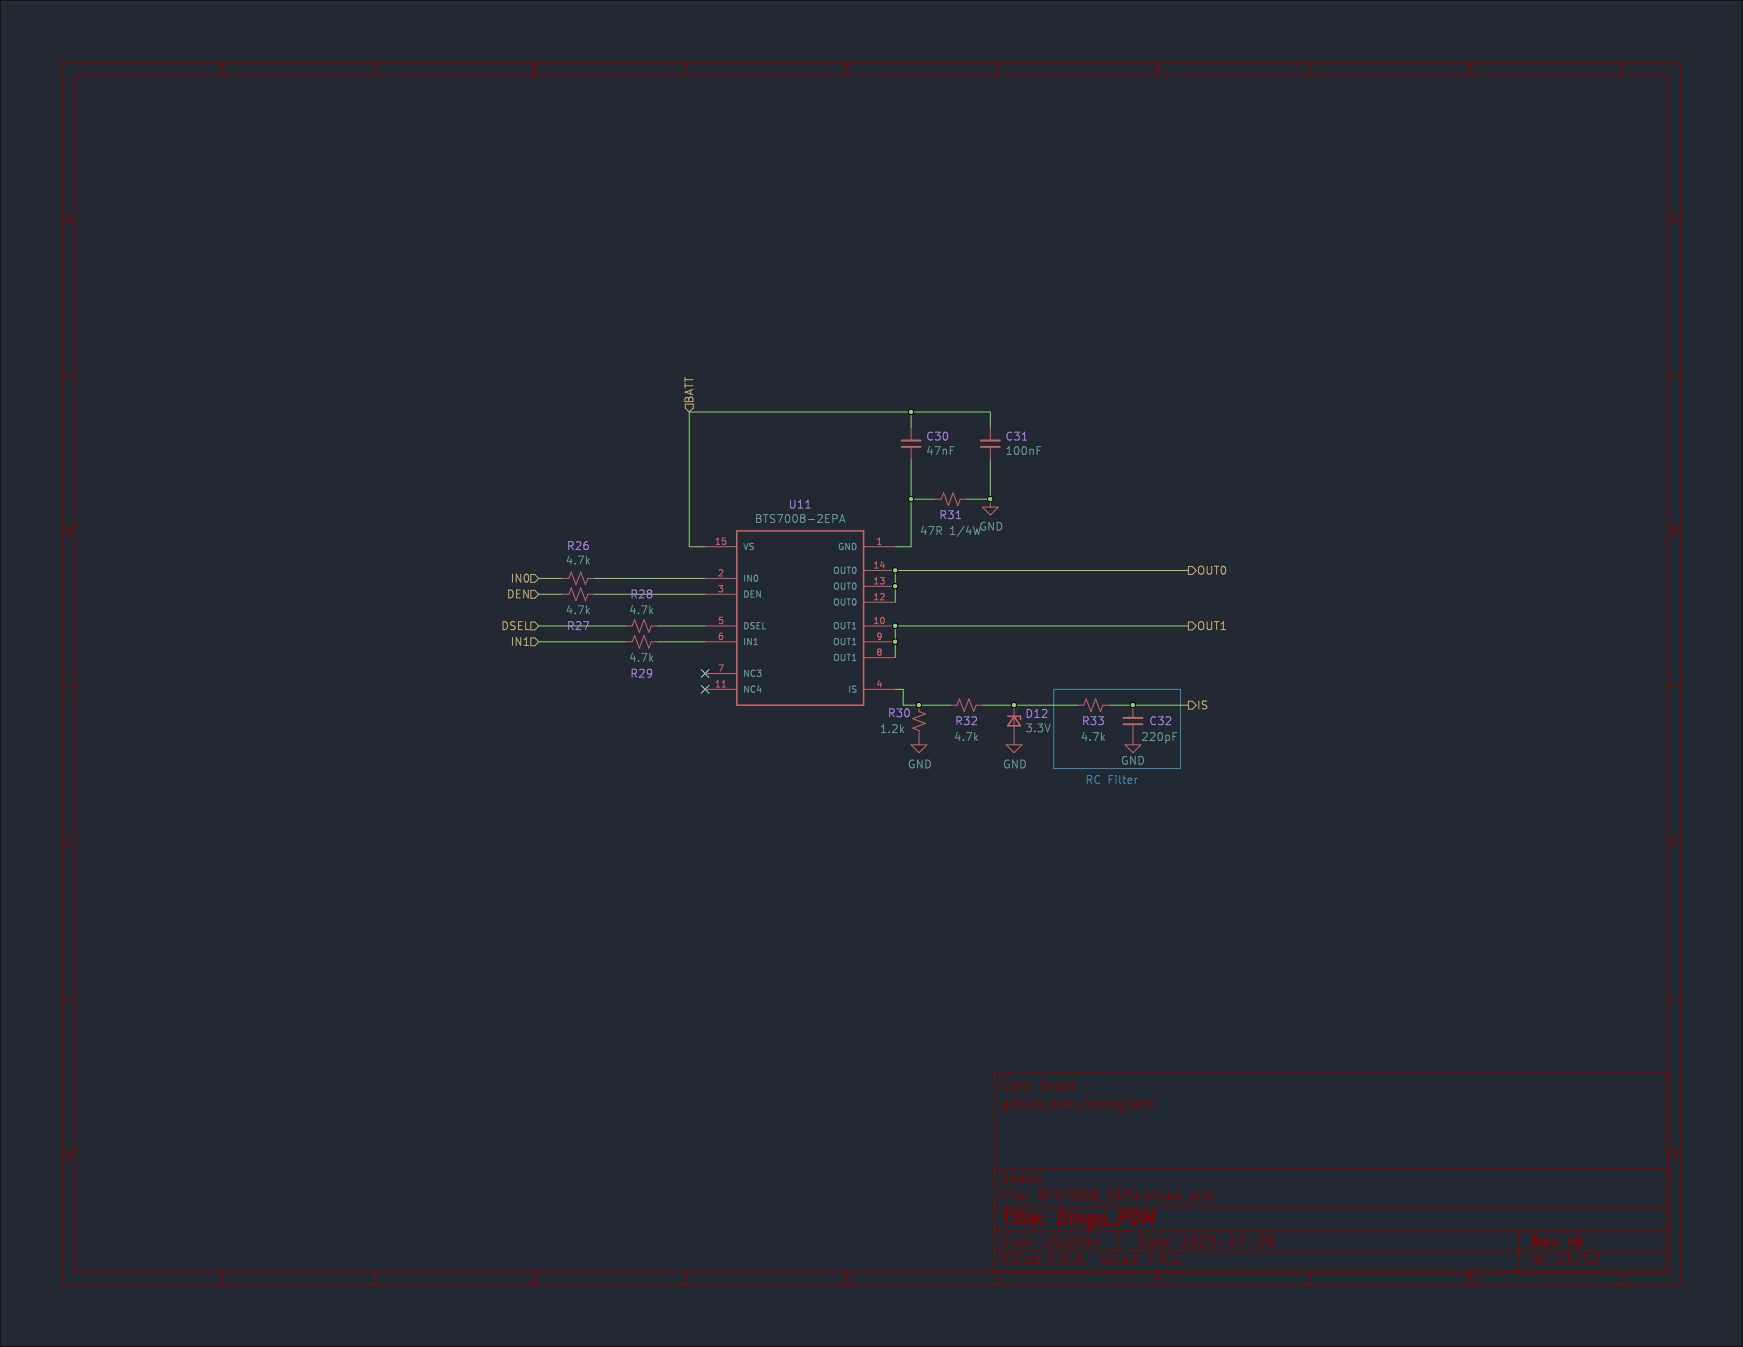
[picture p200: page 11]

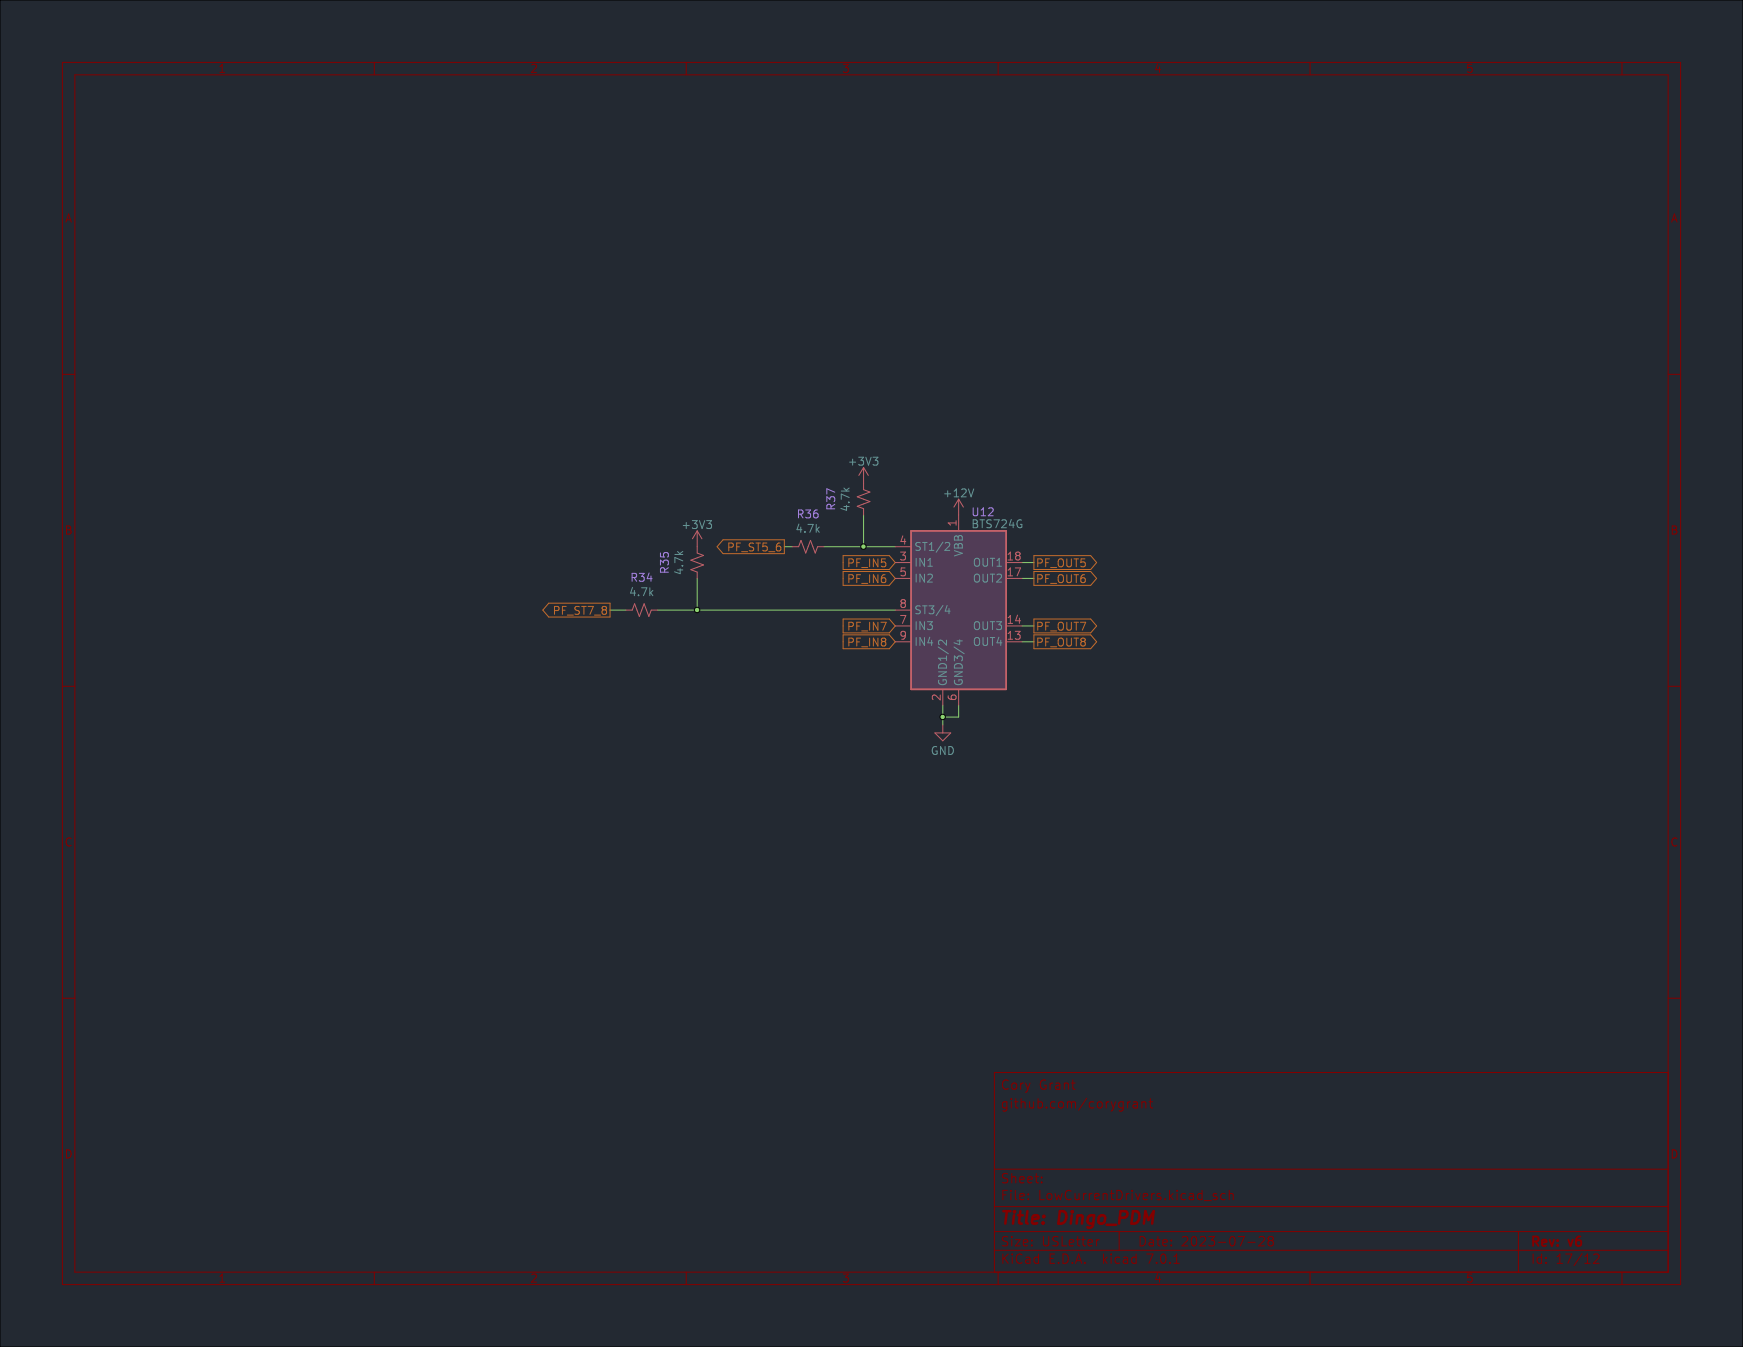
[picture p201: page 12]
