corygrant/dingoPDM/Export/V5/DingoPDM_HW_V5.pdf

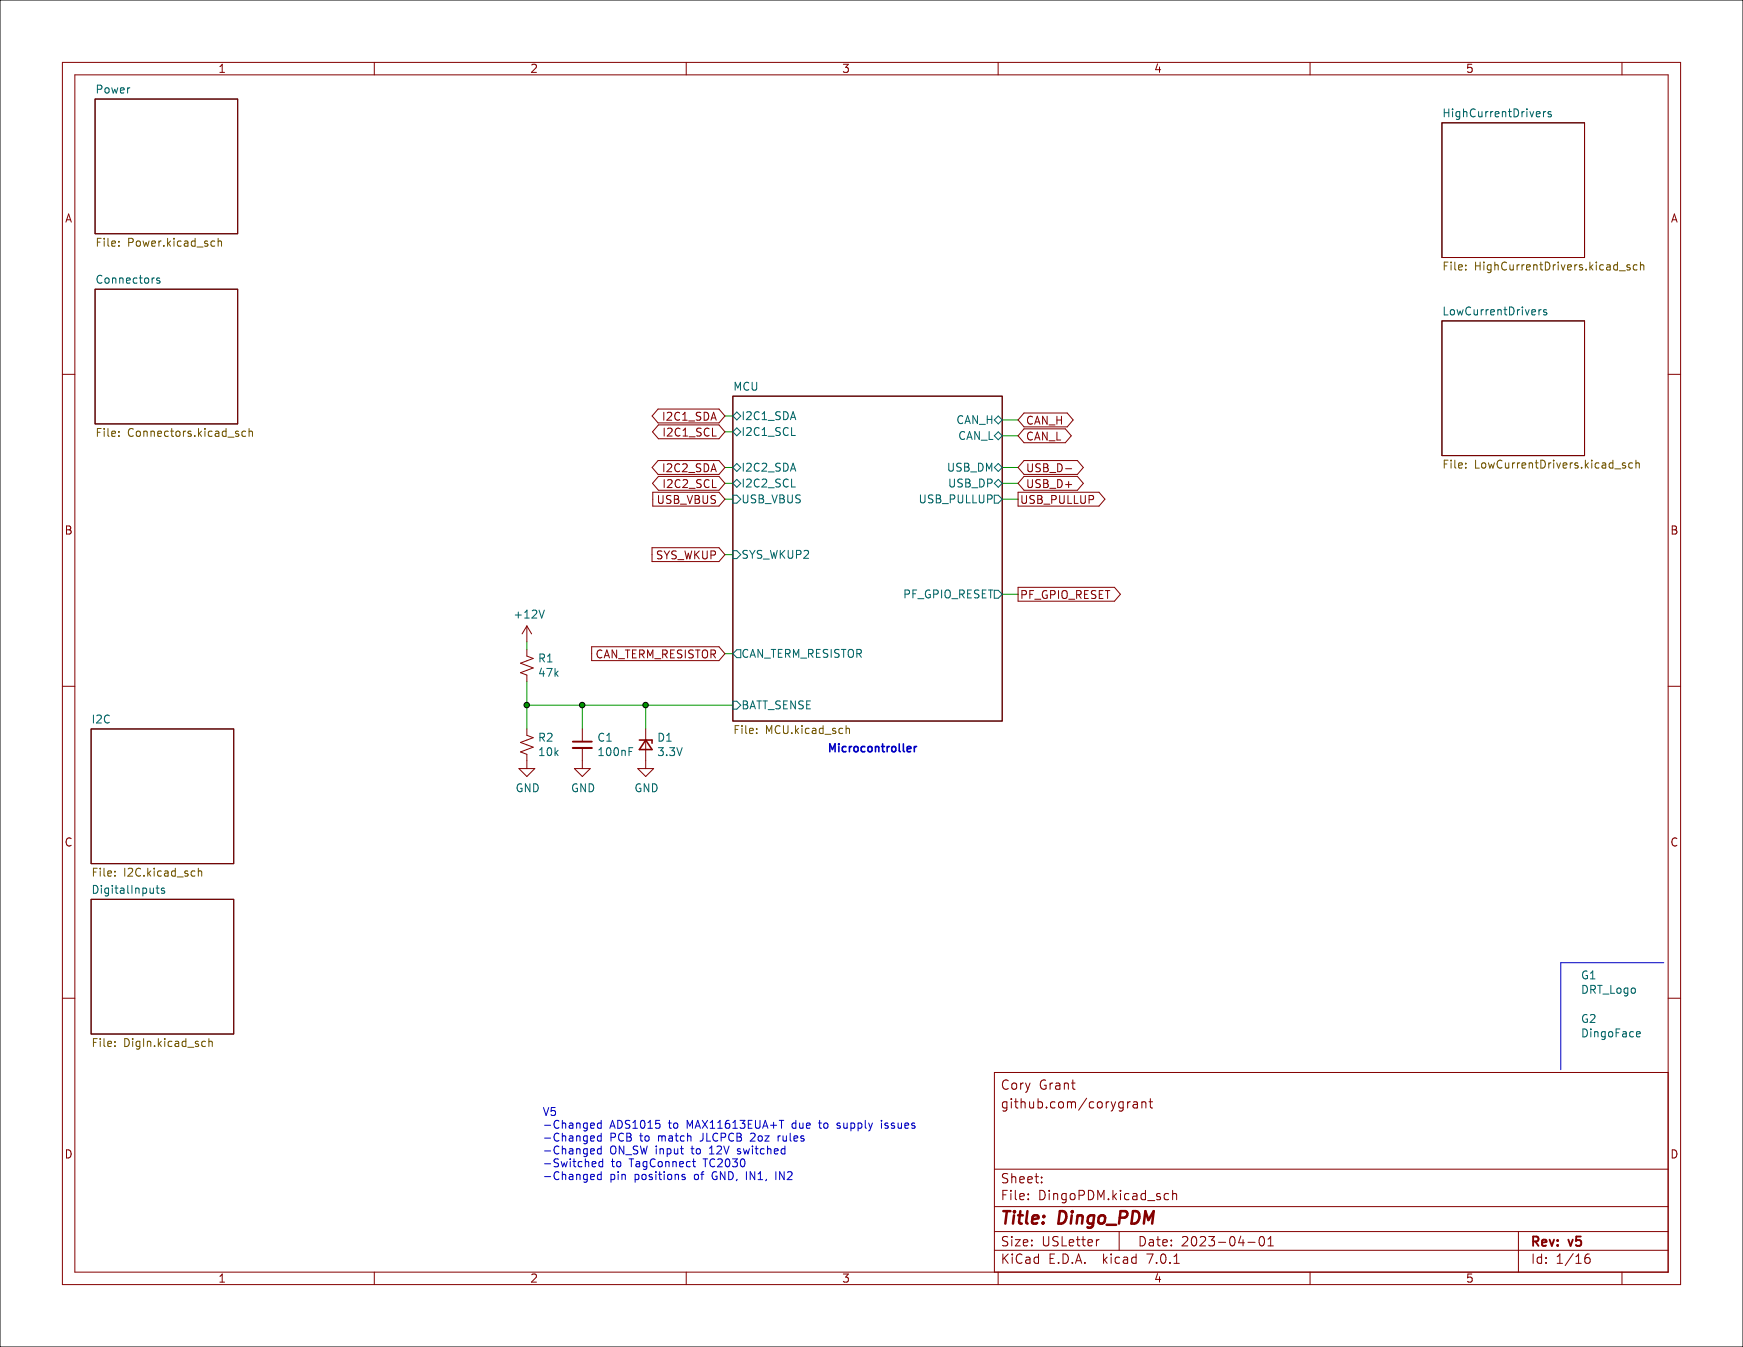
[picture p202: page 1]

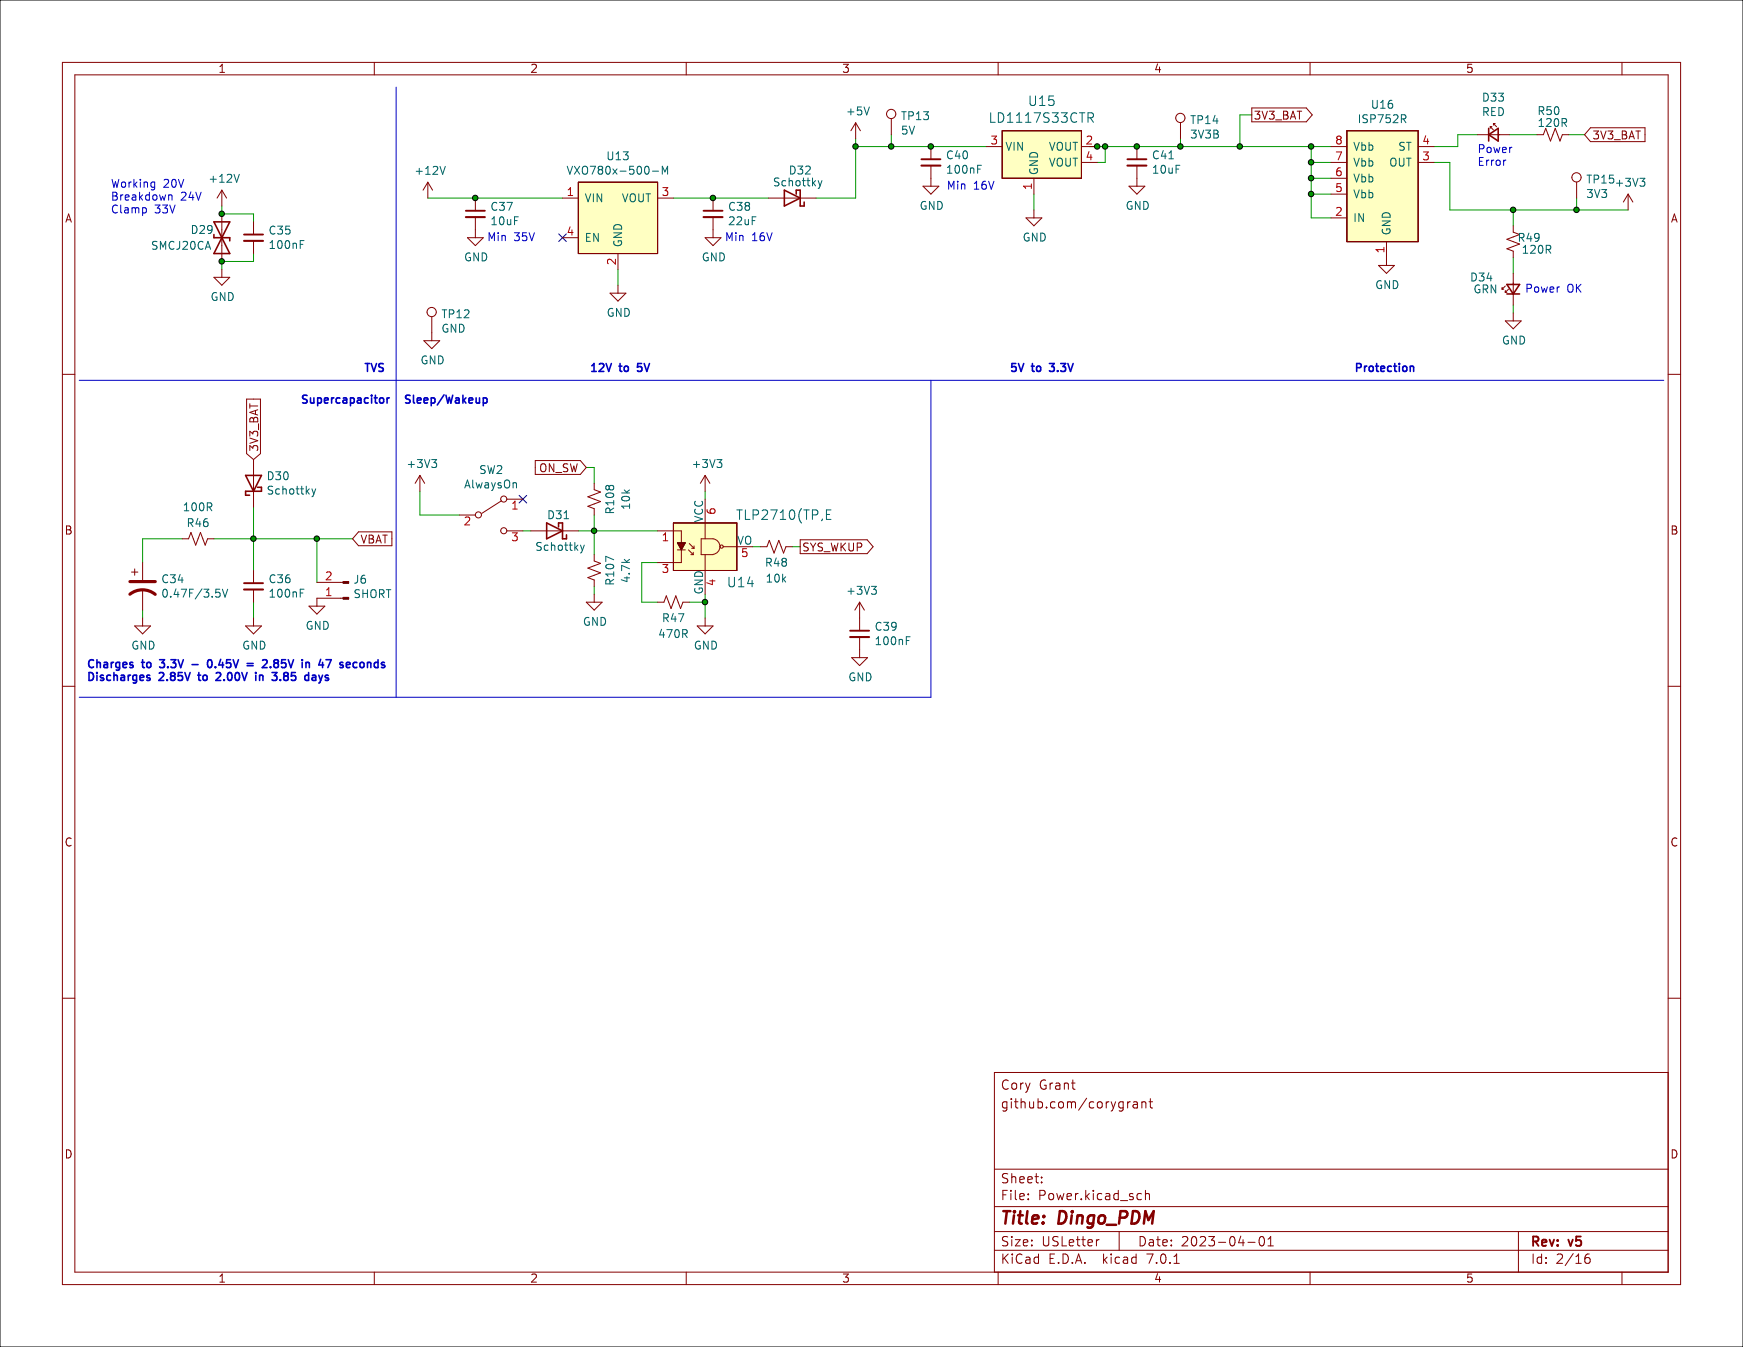
[picture p203: page 2]

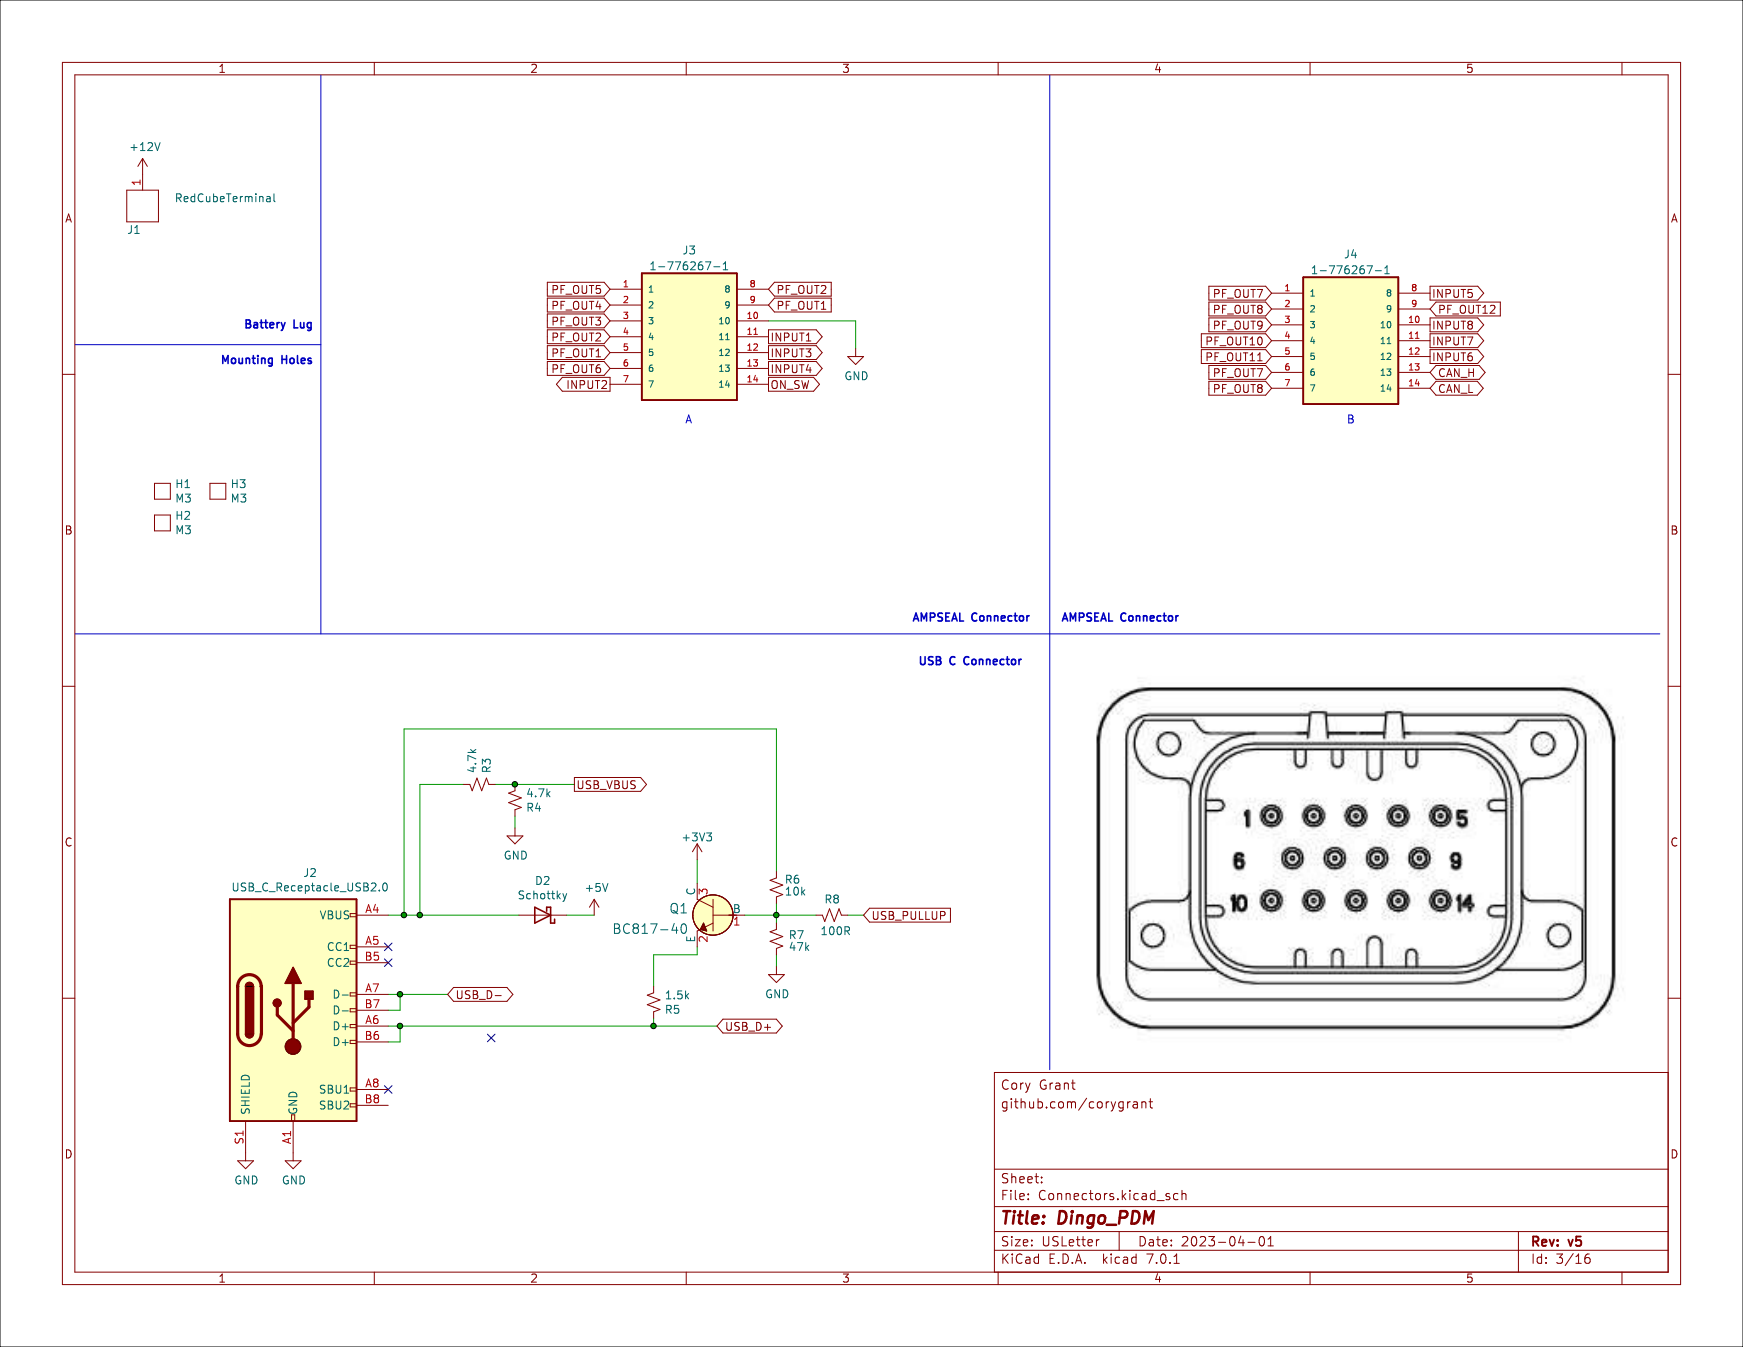
[picture p204: page 3]

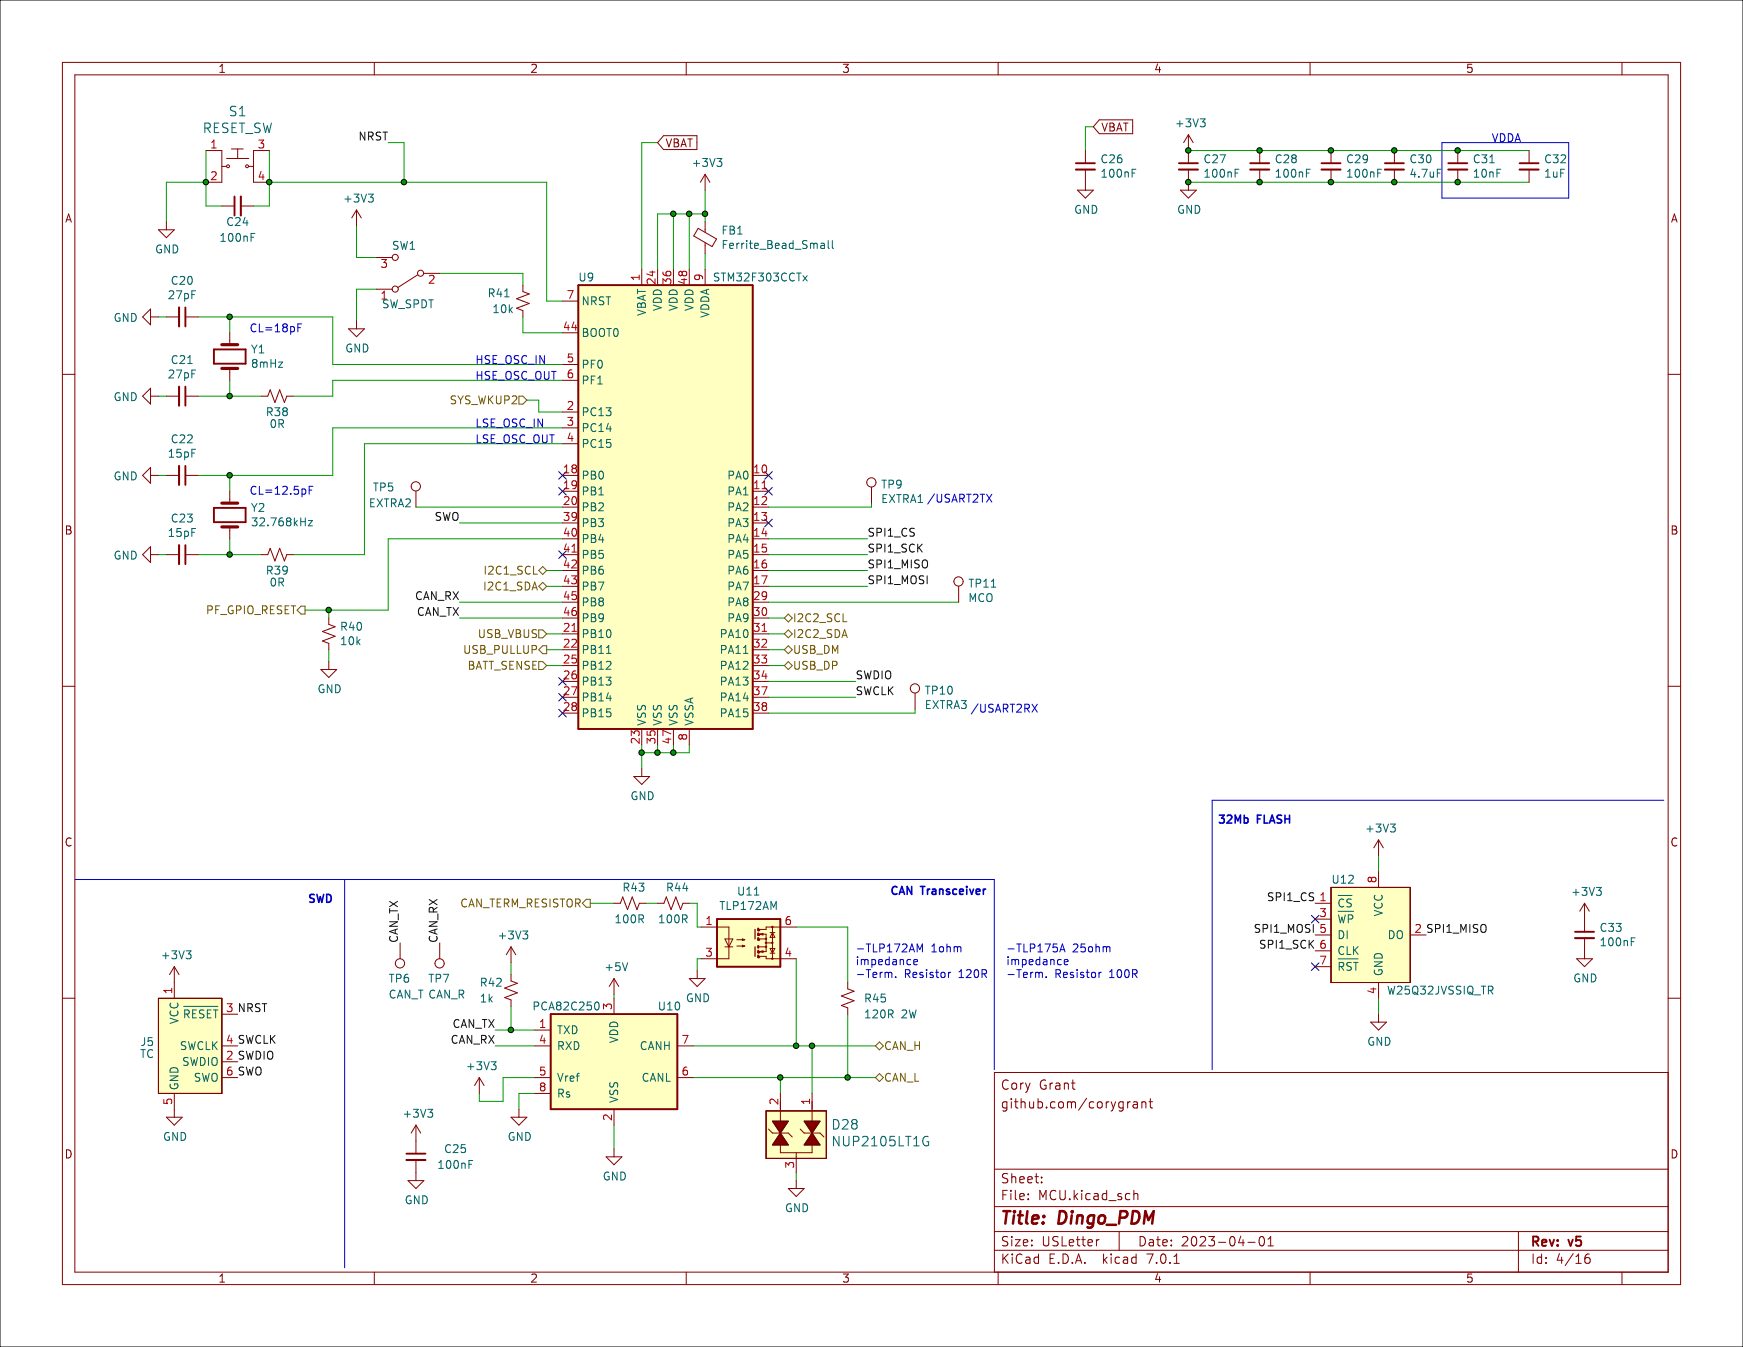
[picture p205: page 4]

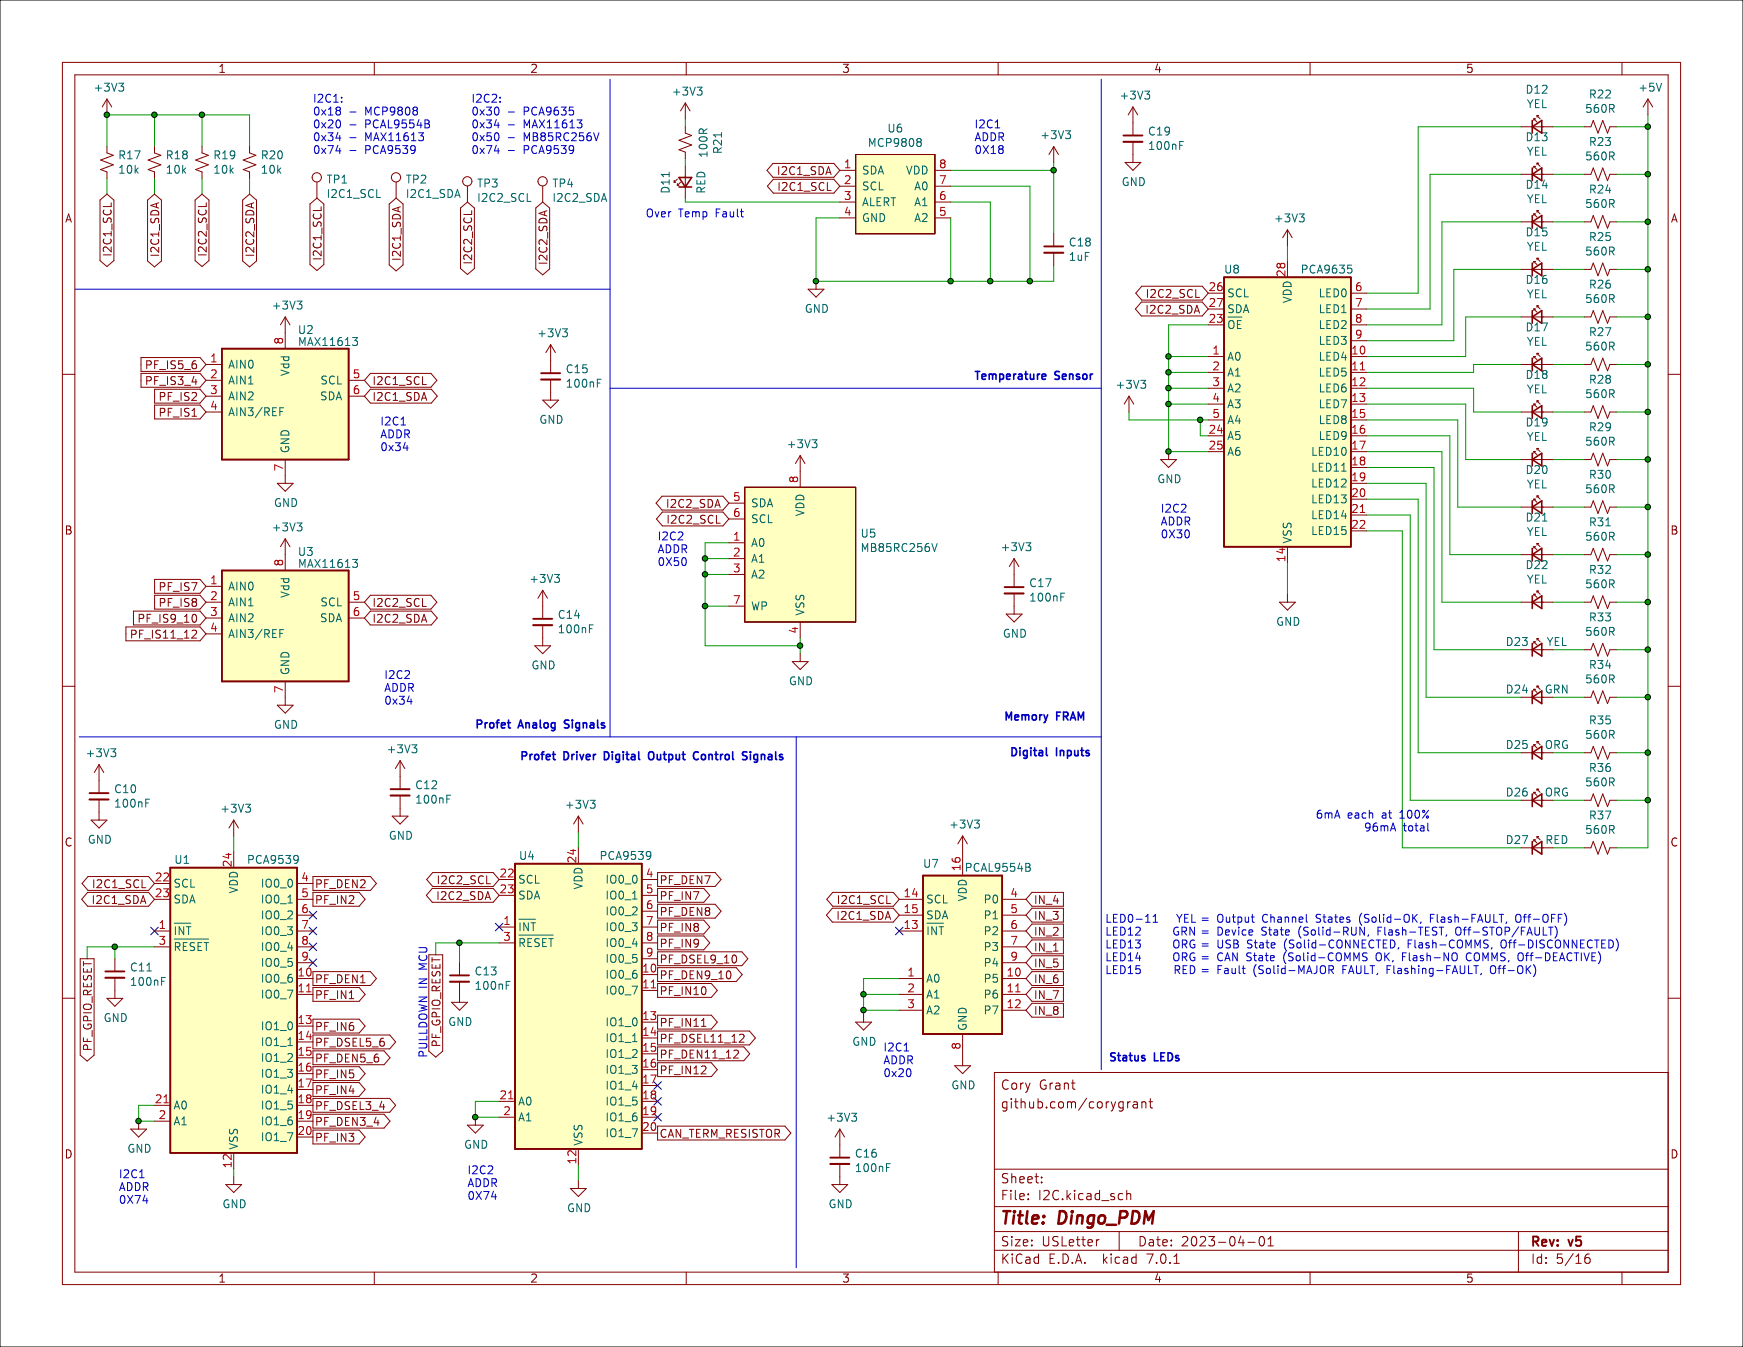
[picture p206: page 5]

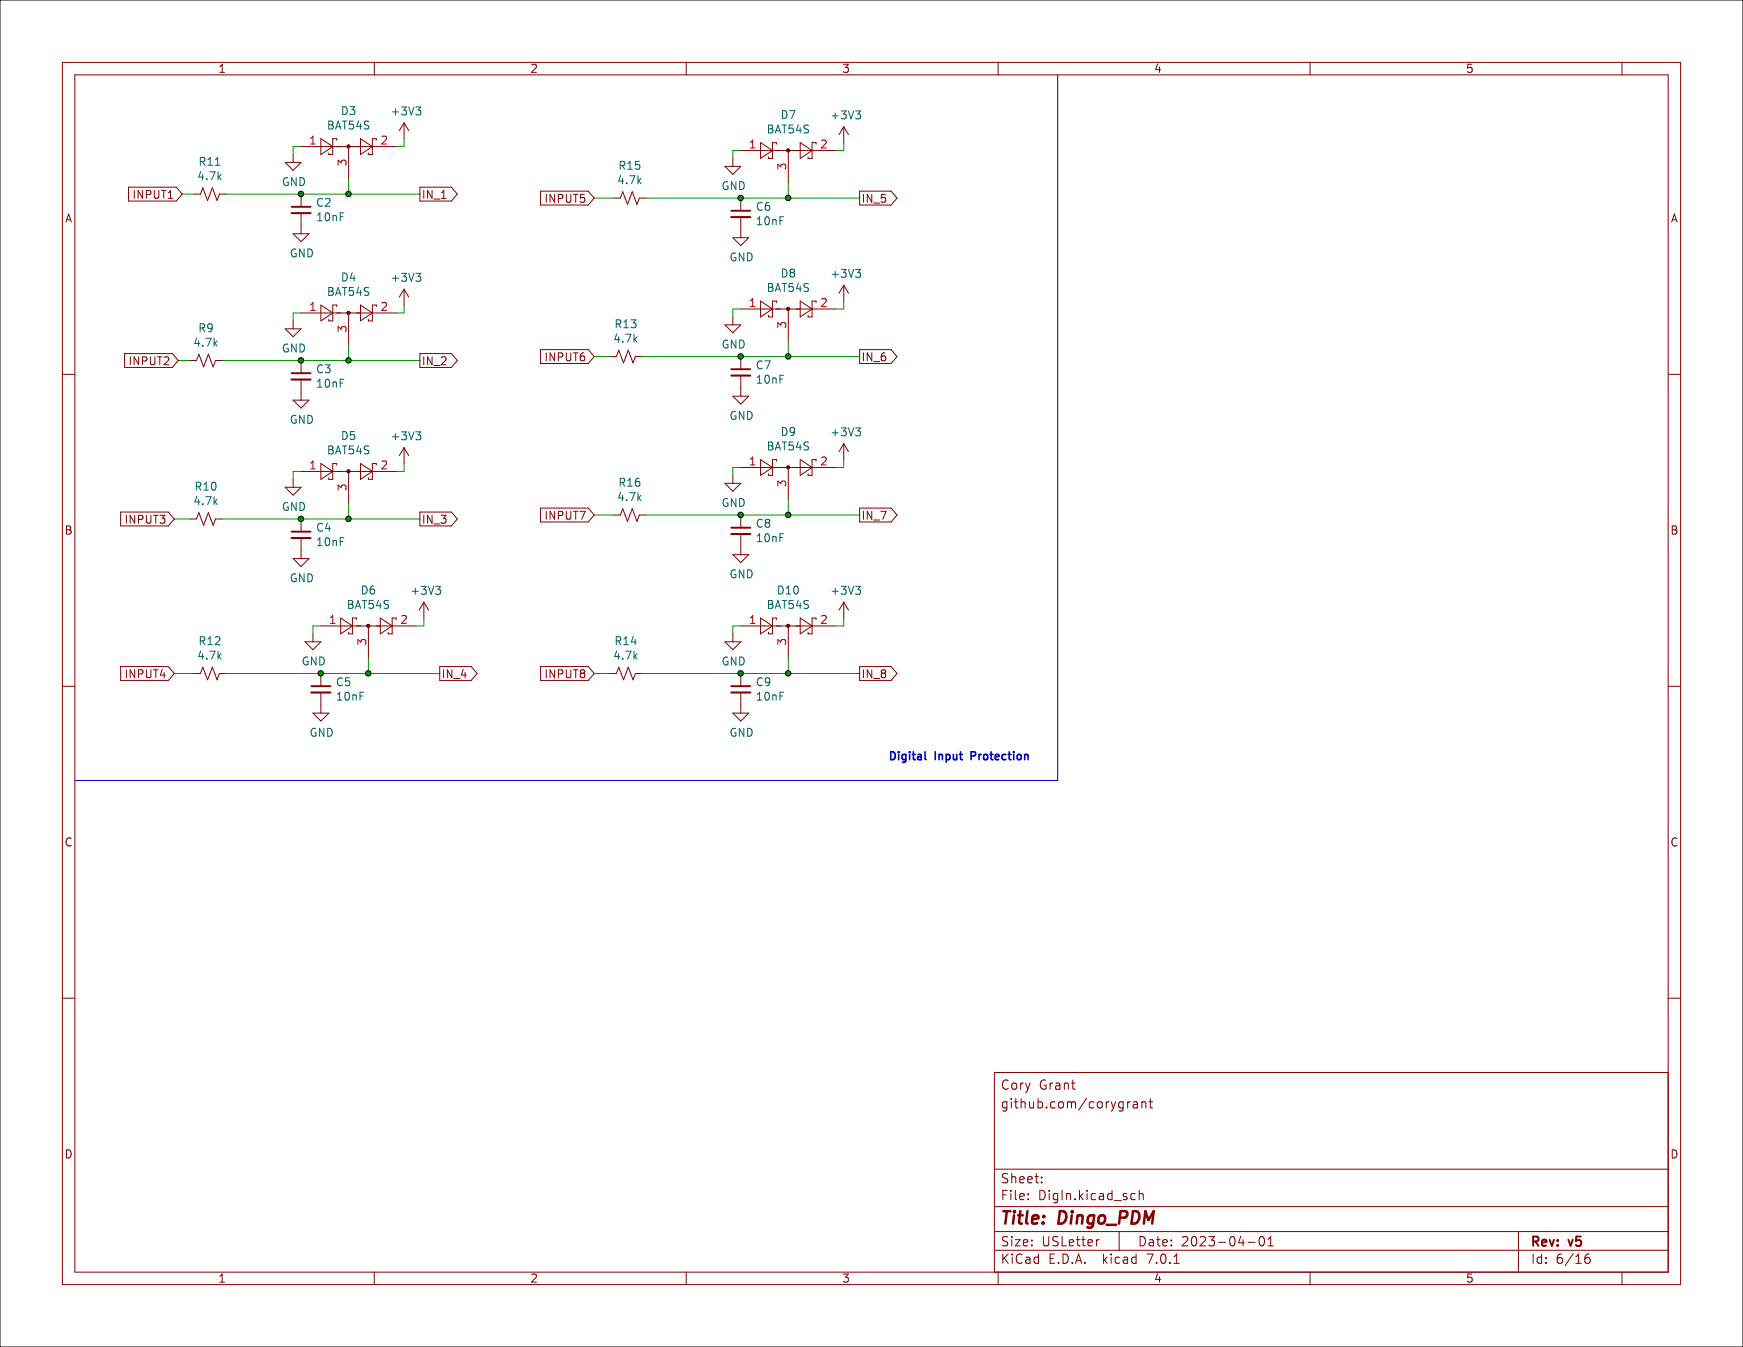
[picture p207: page 6]

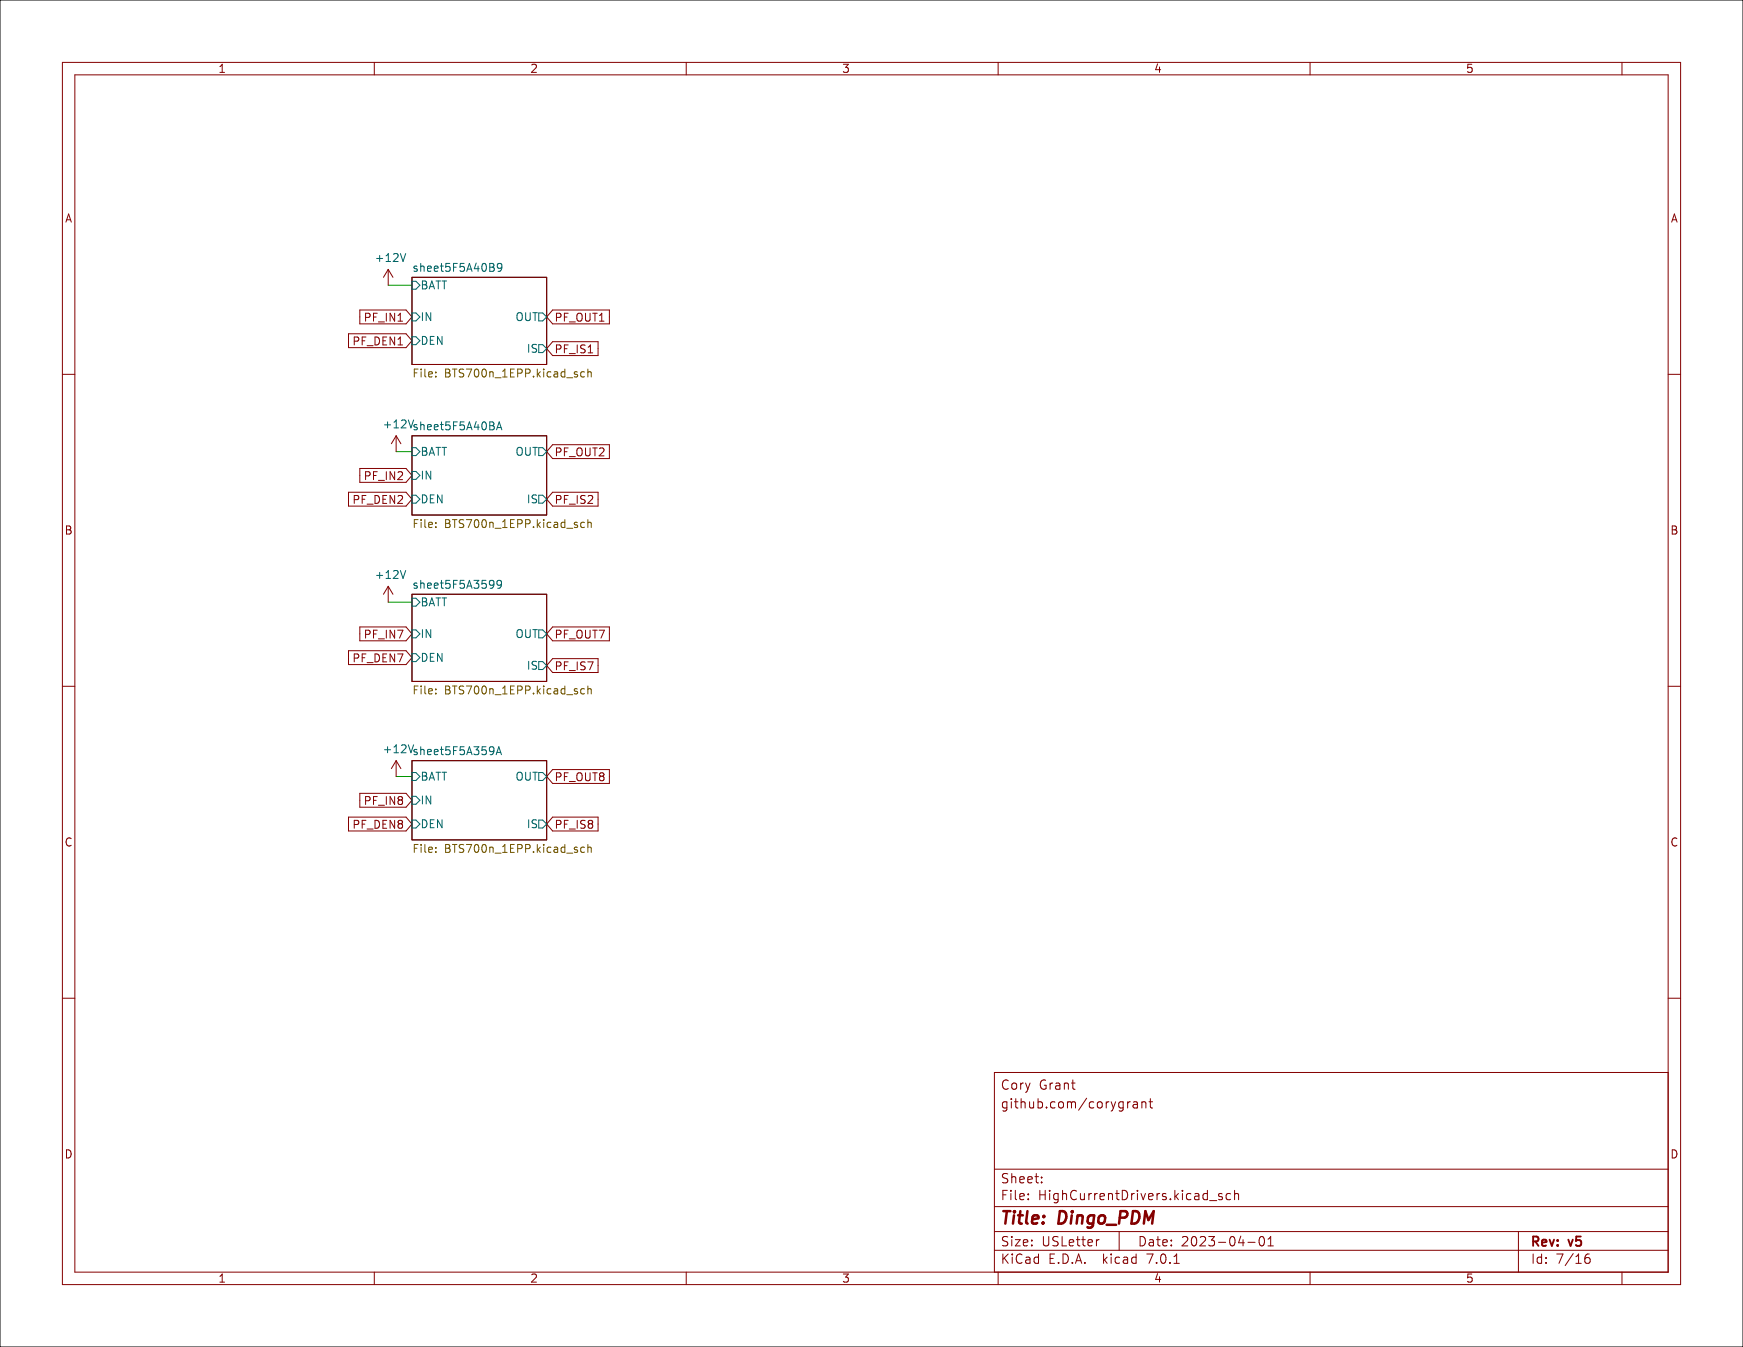
[picture p208: page 7]

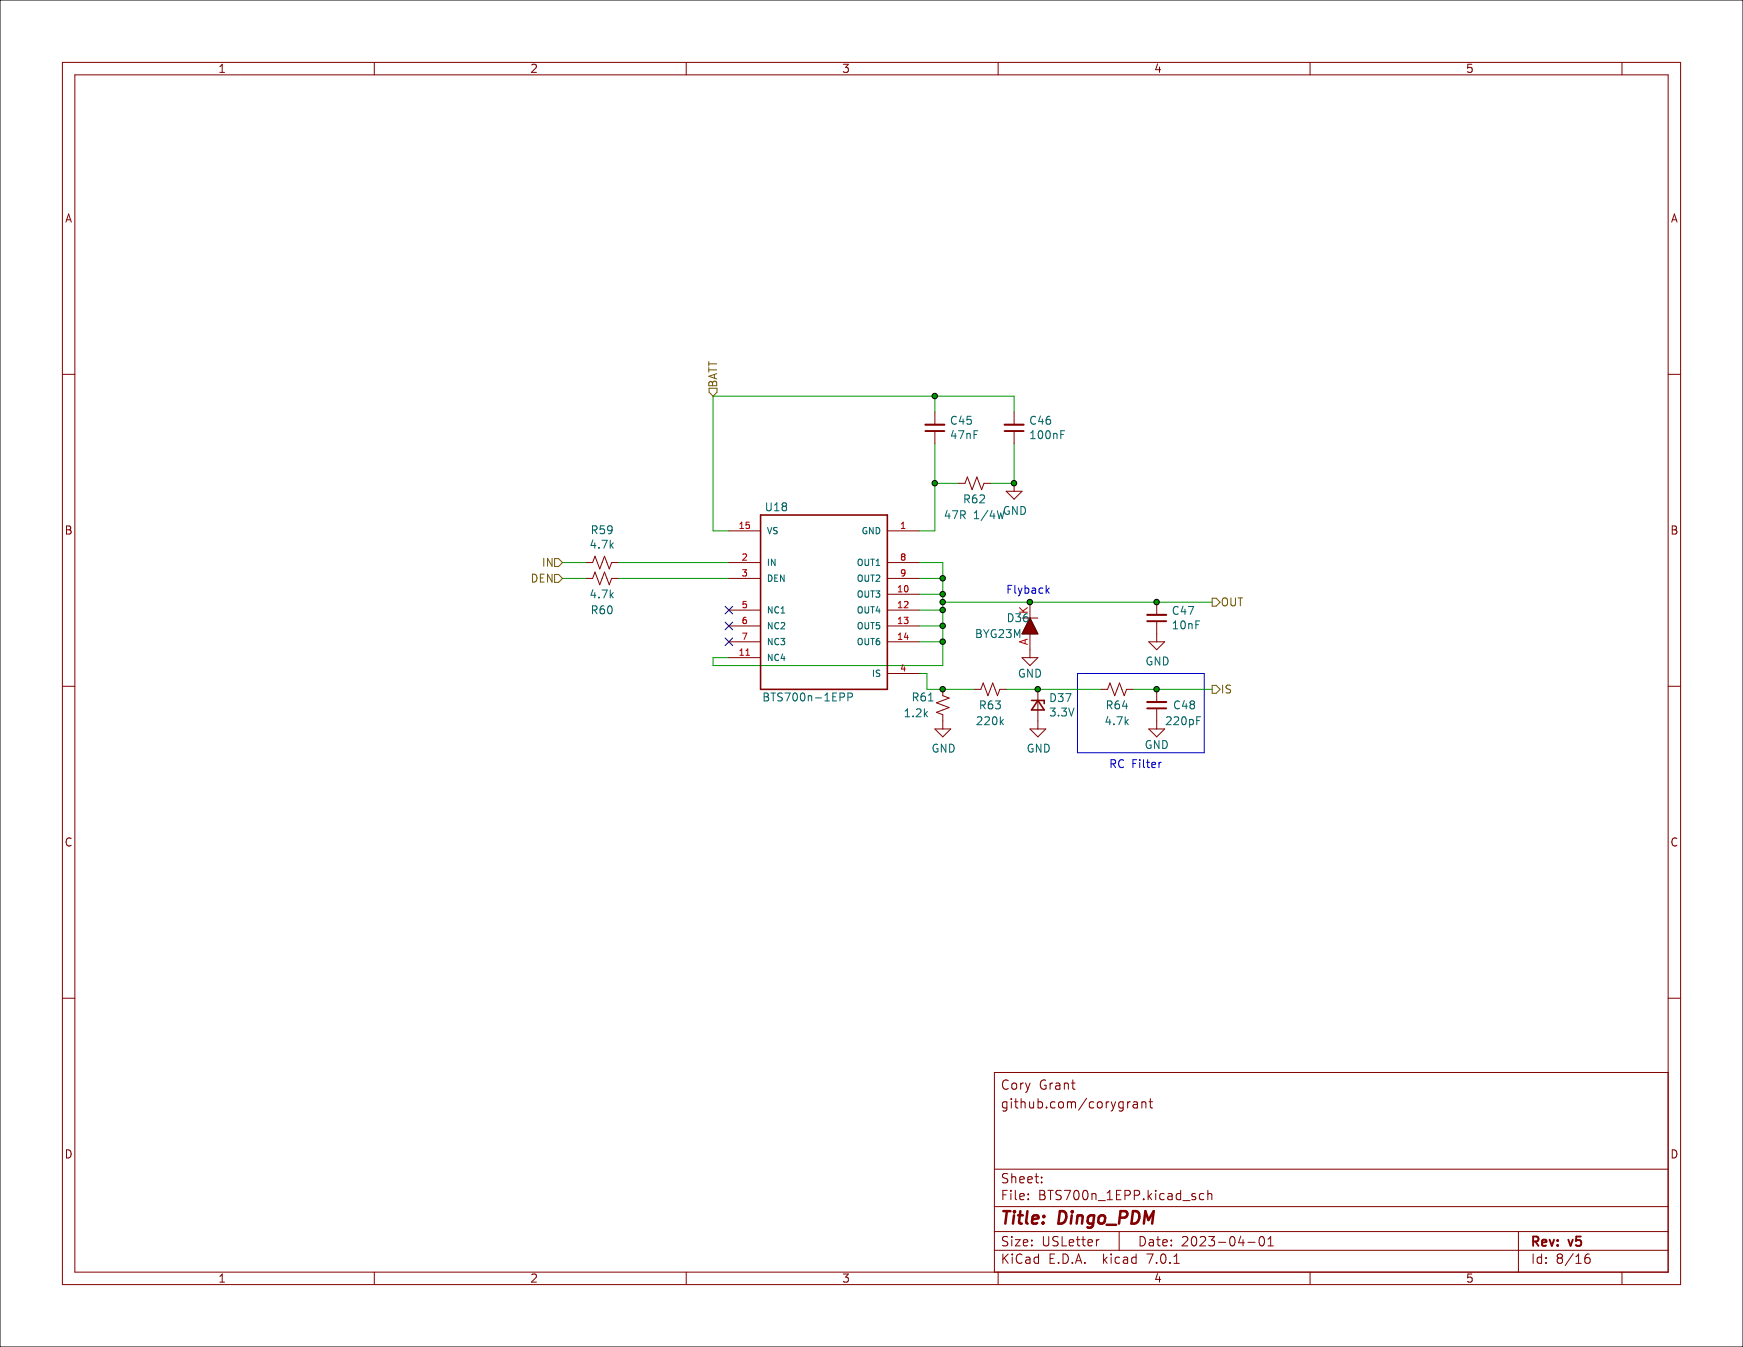
[picture p209: page 8]

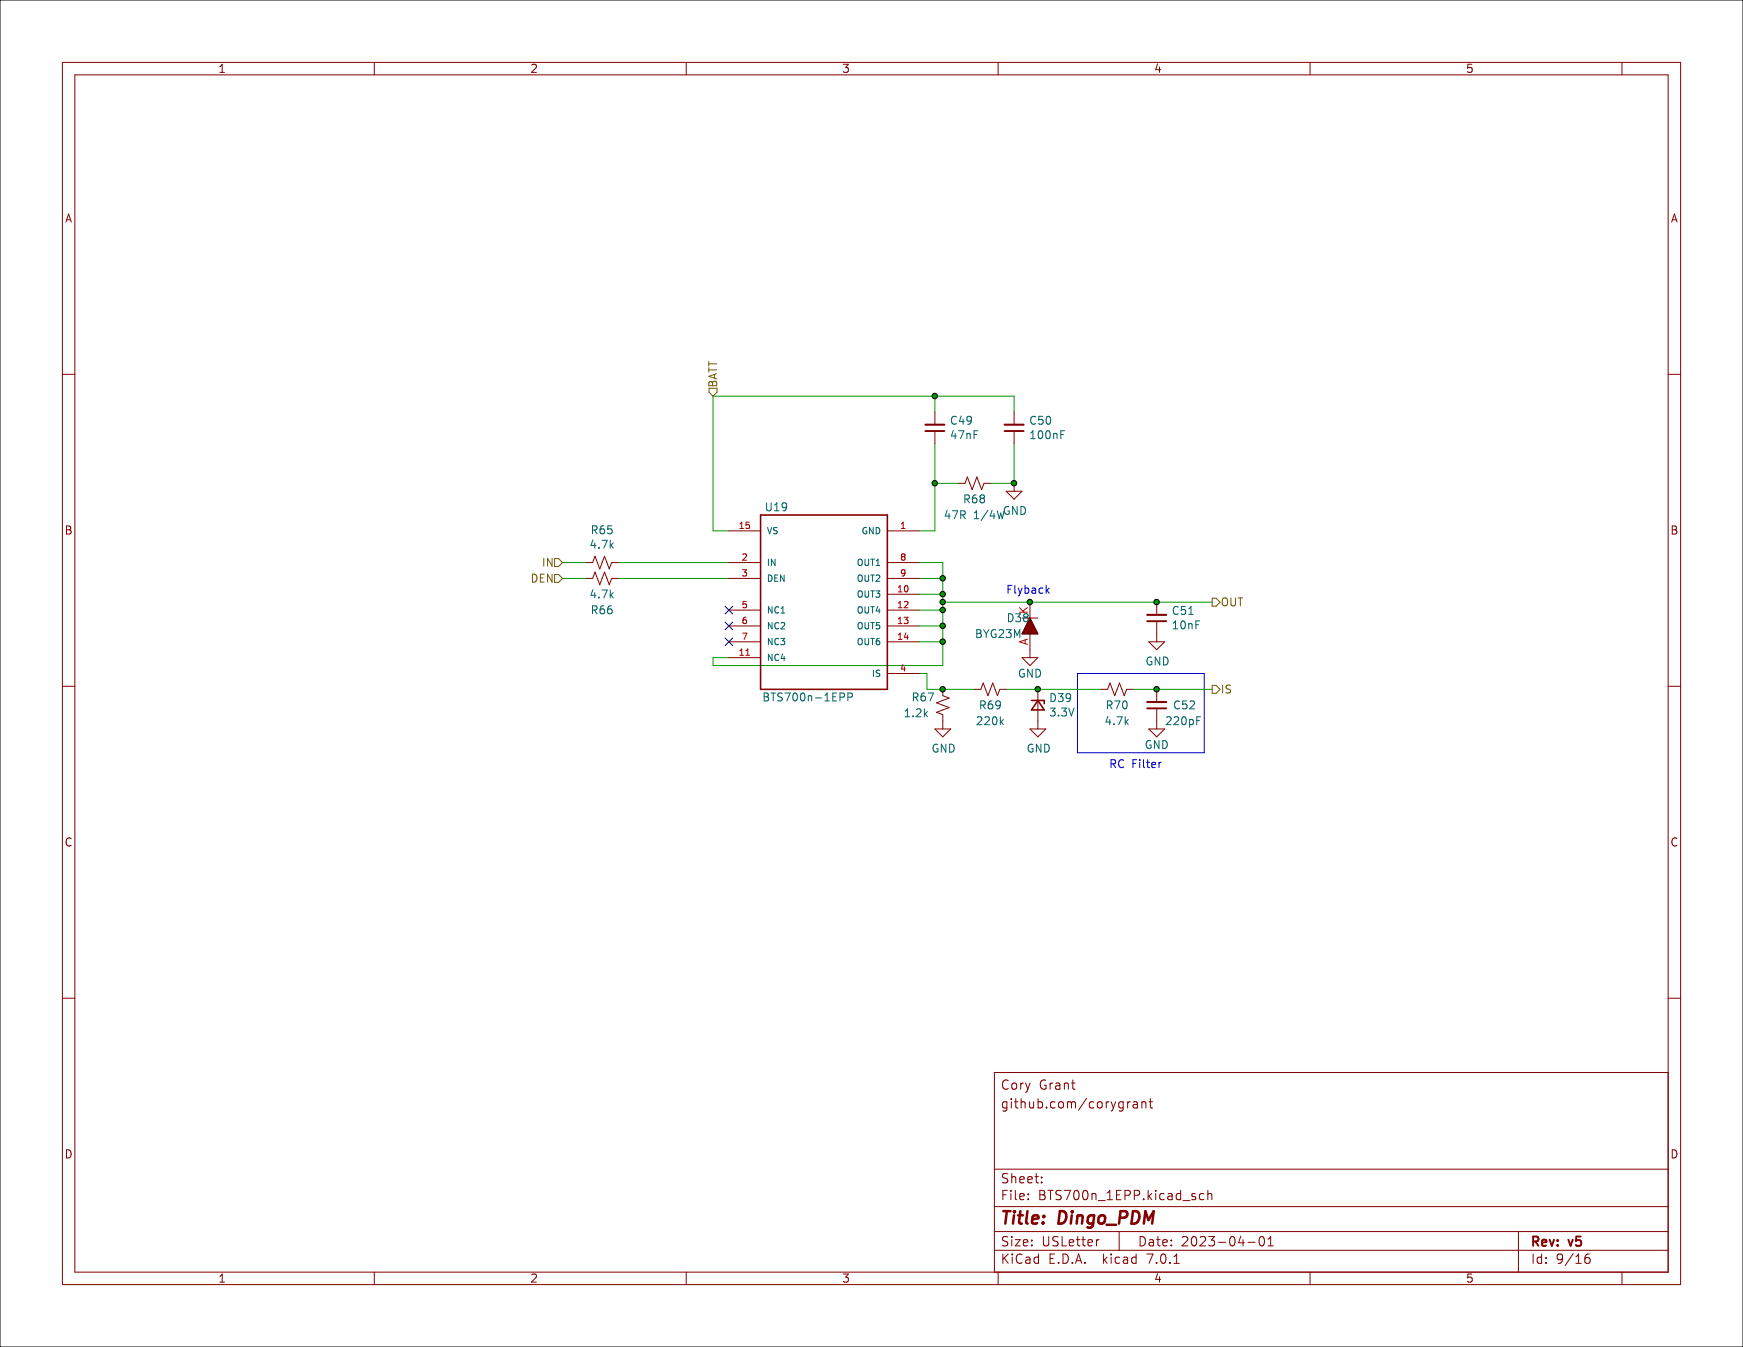
[picture p210: page 9]

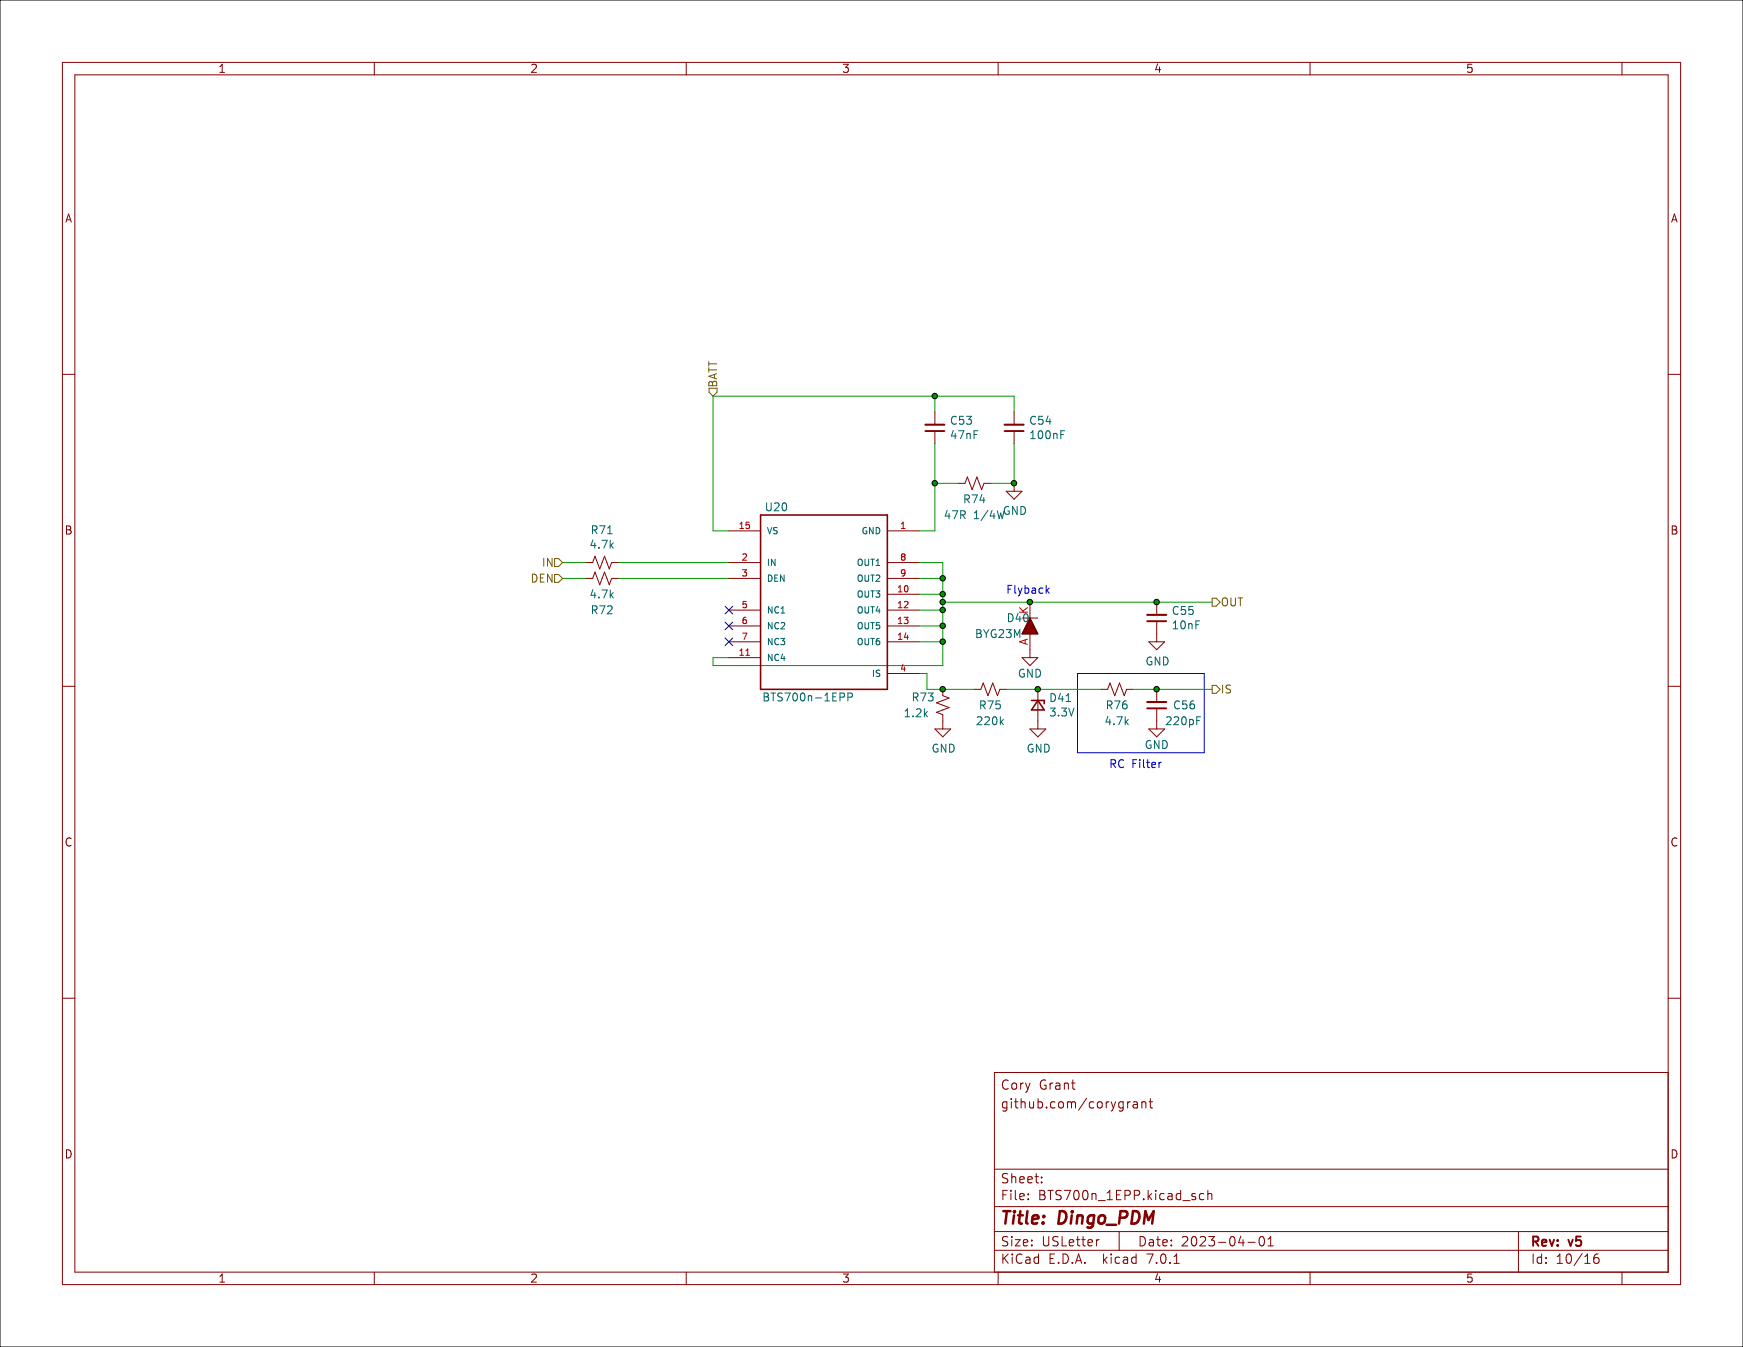
[picture p211: page 10]

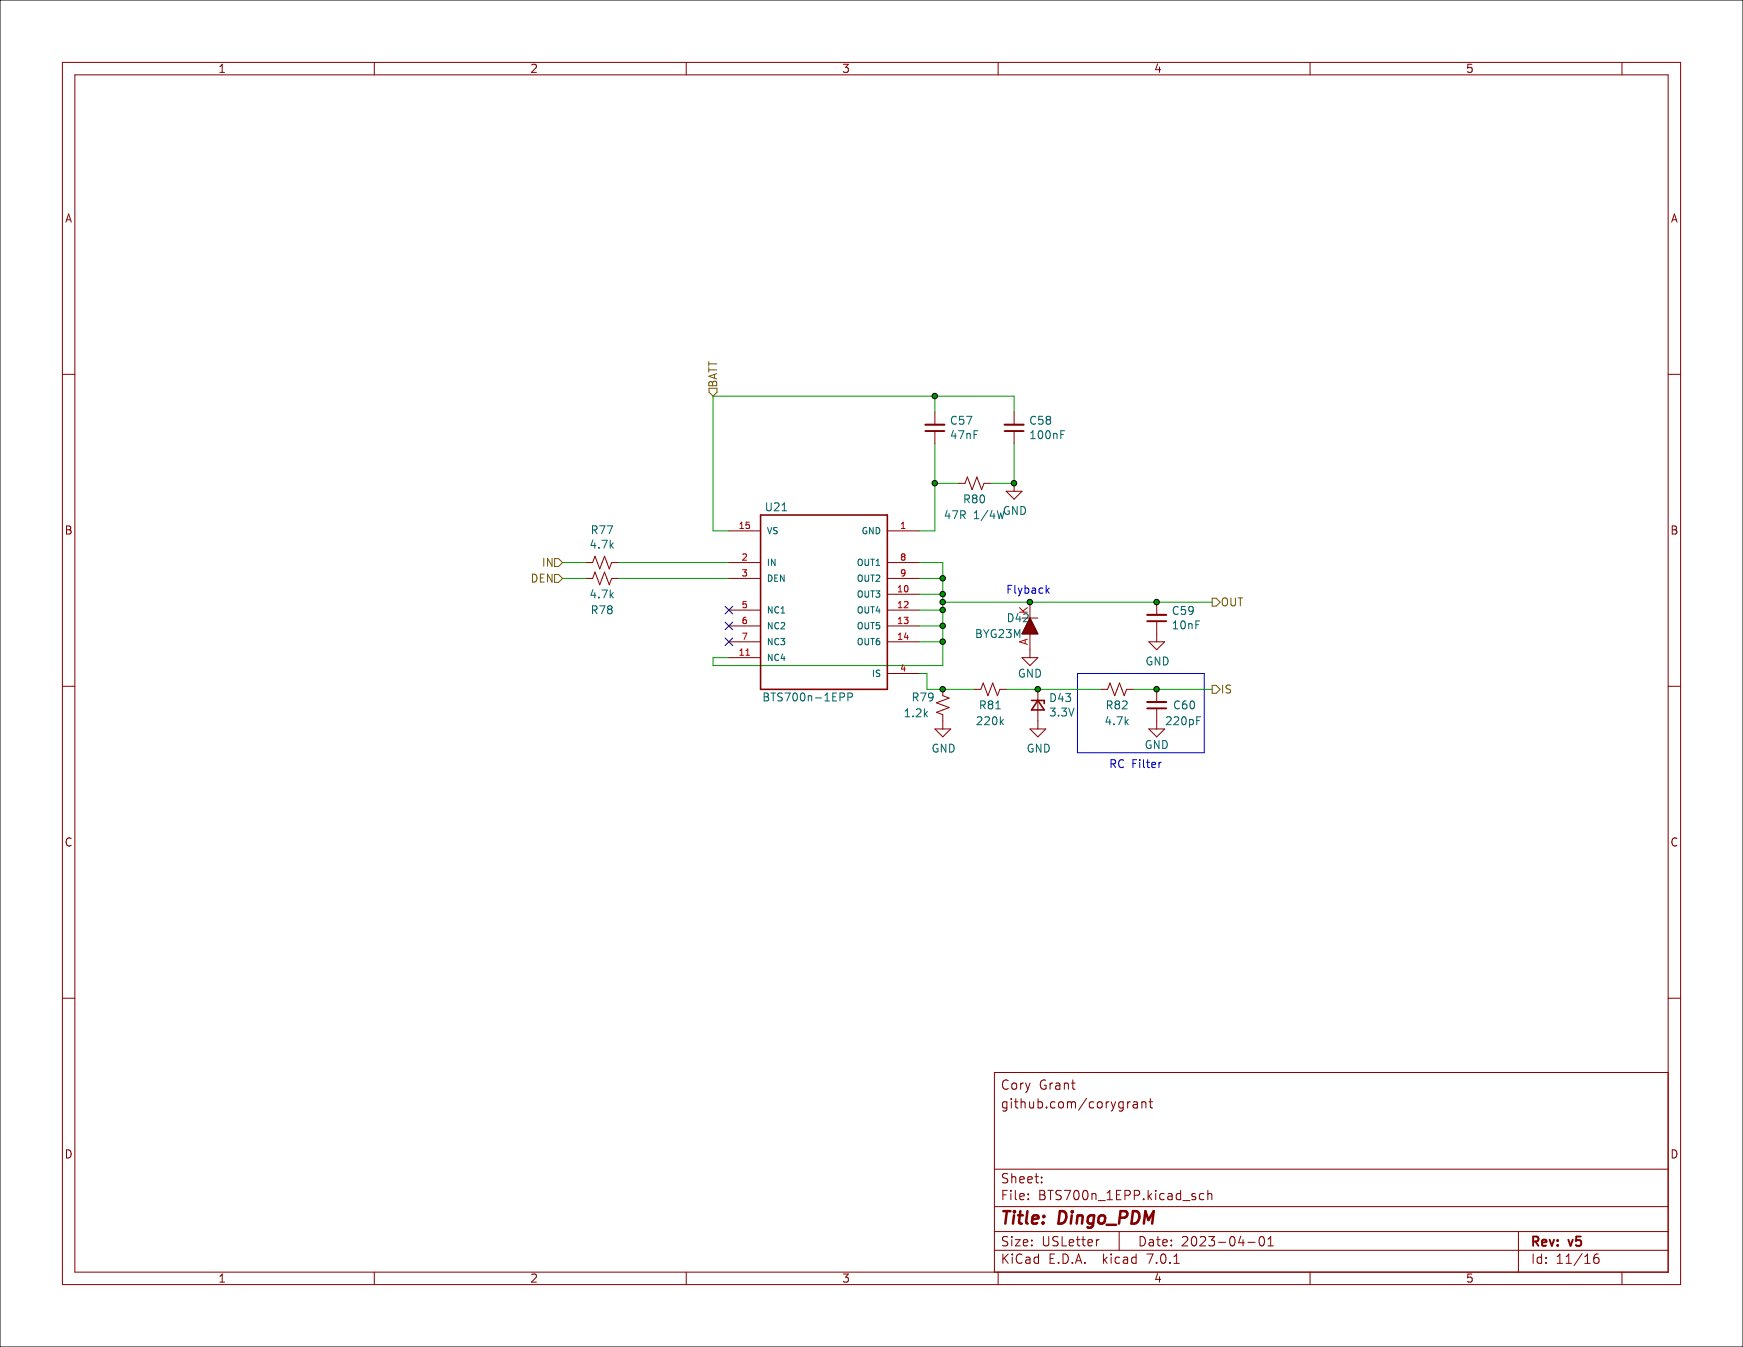
[picture p212: page 11]

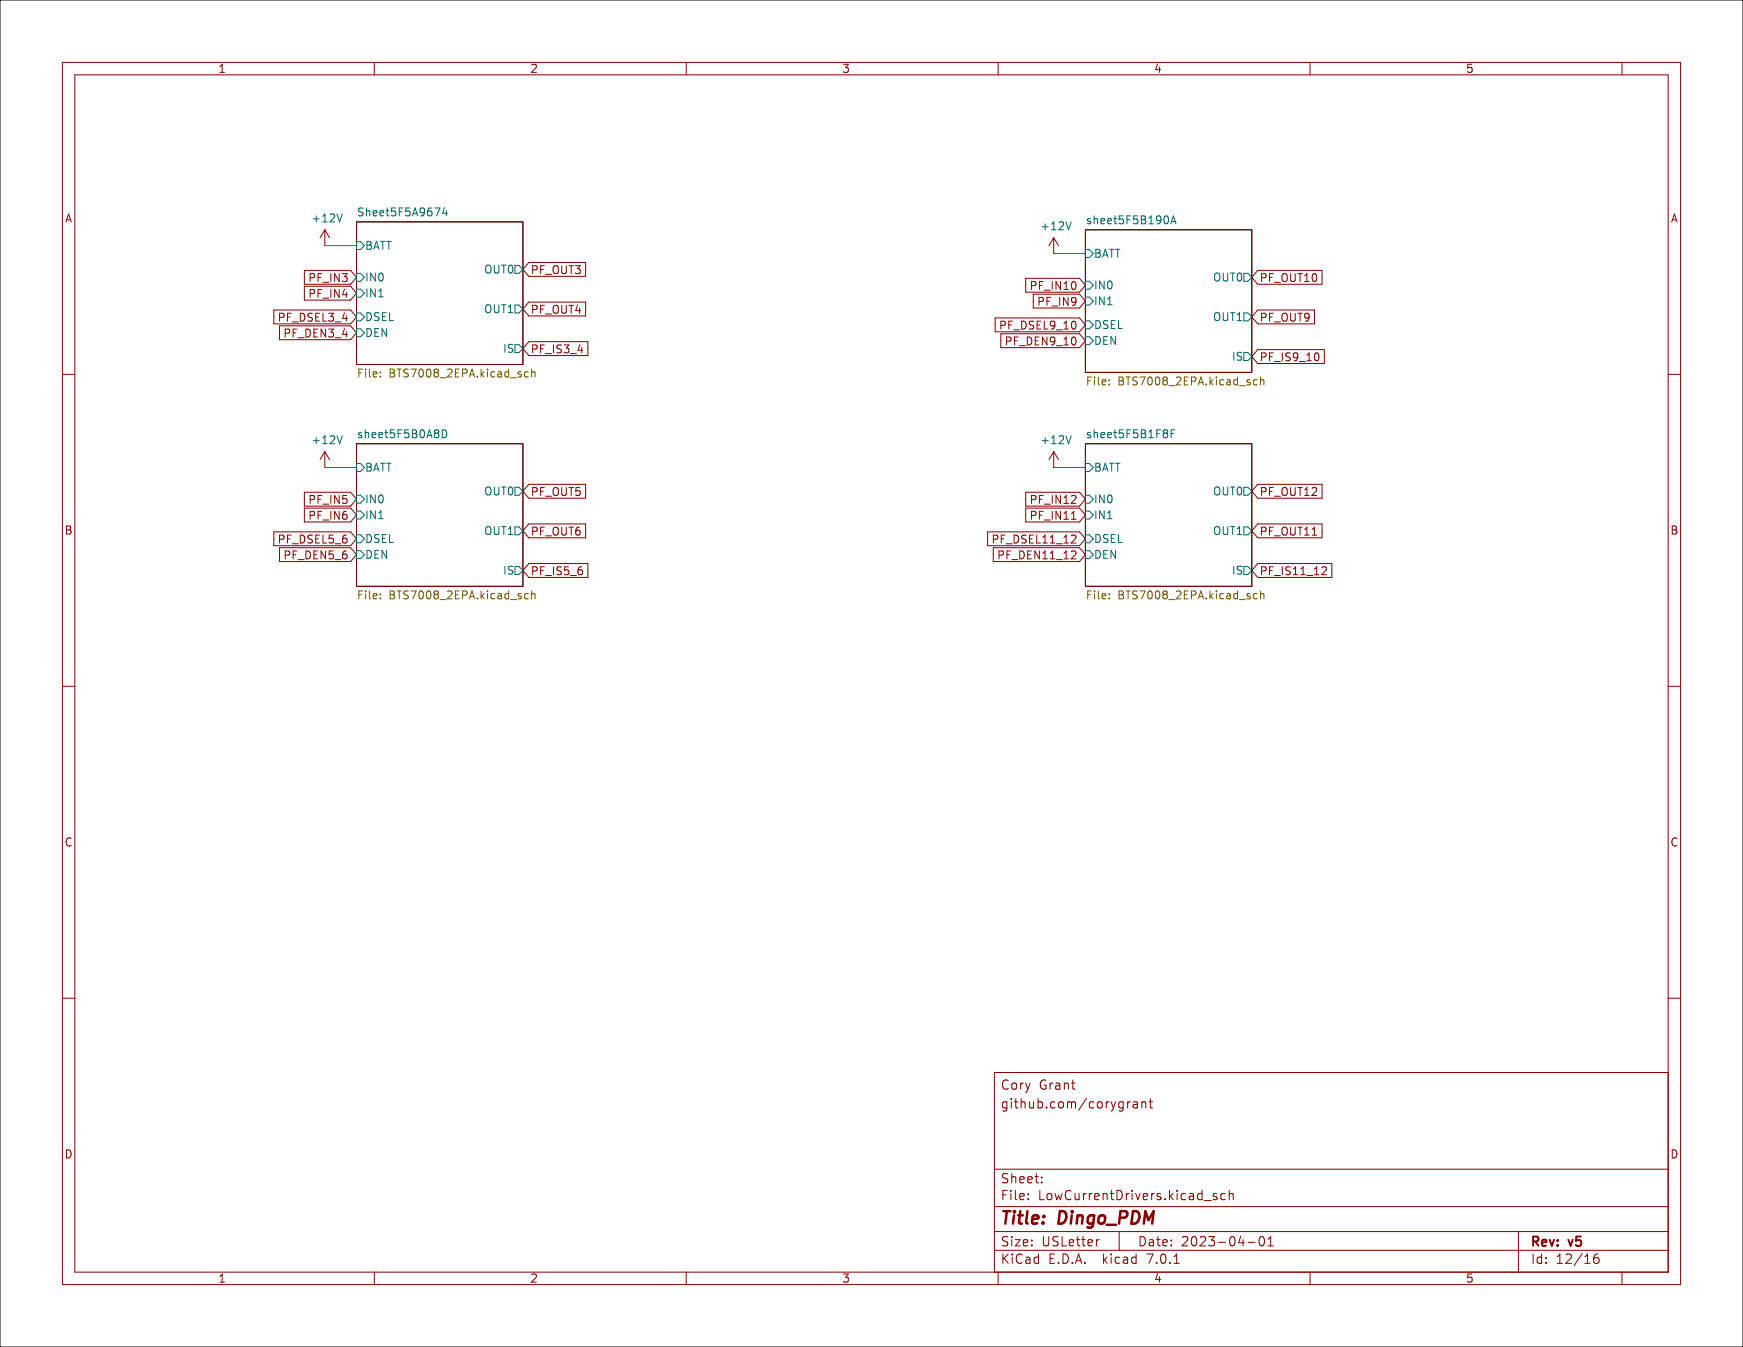
[picture p213: page 12]

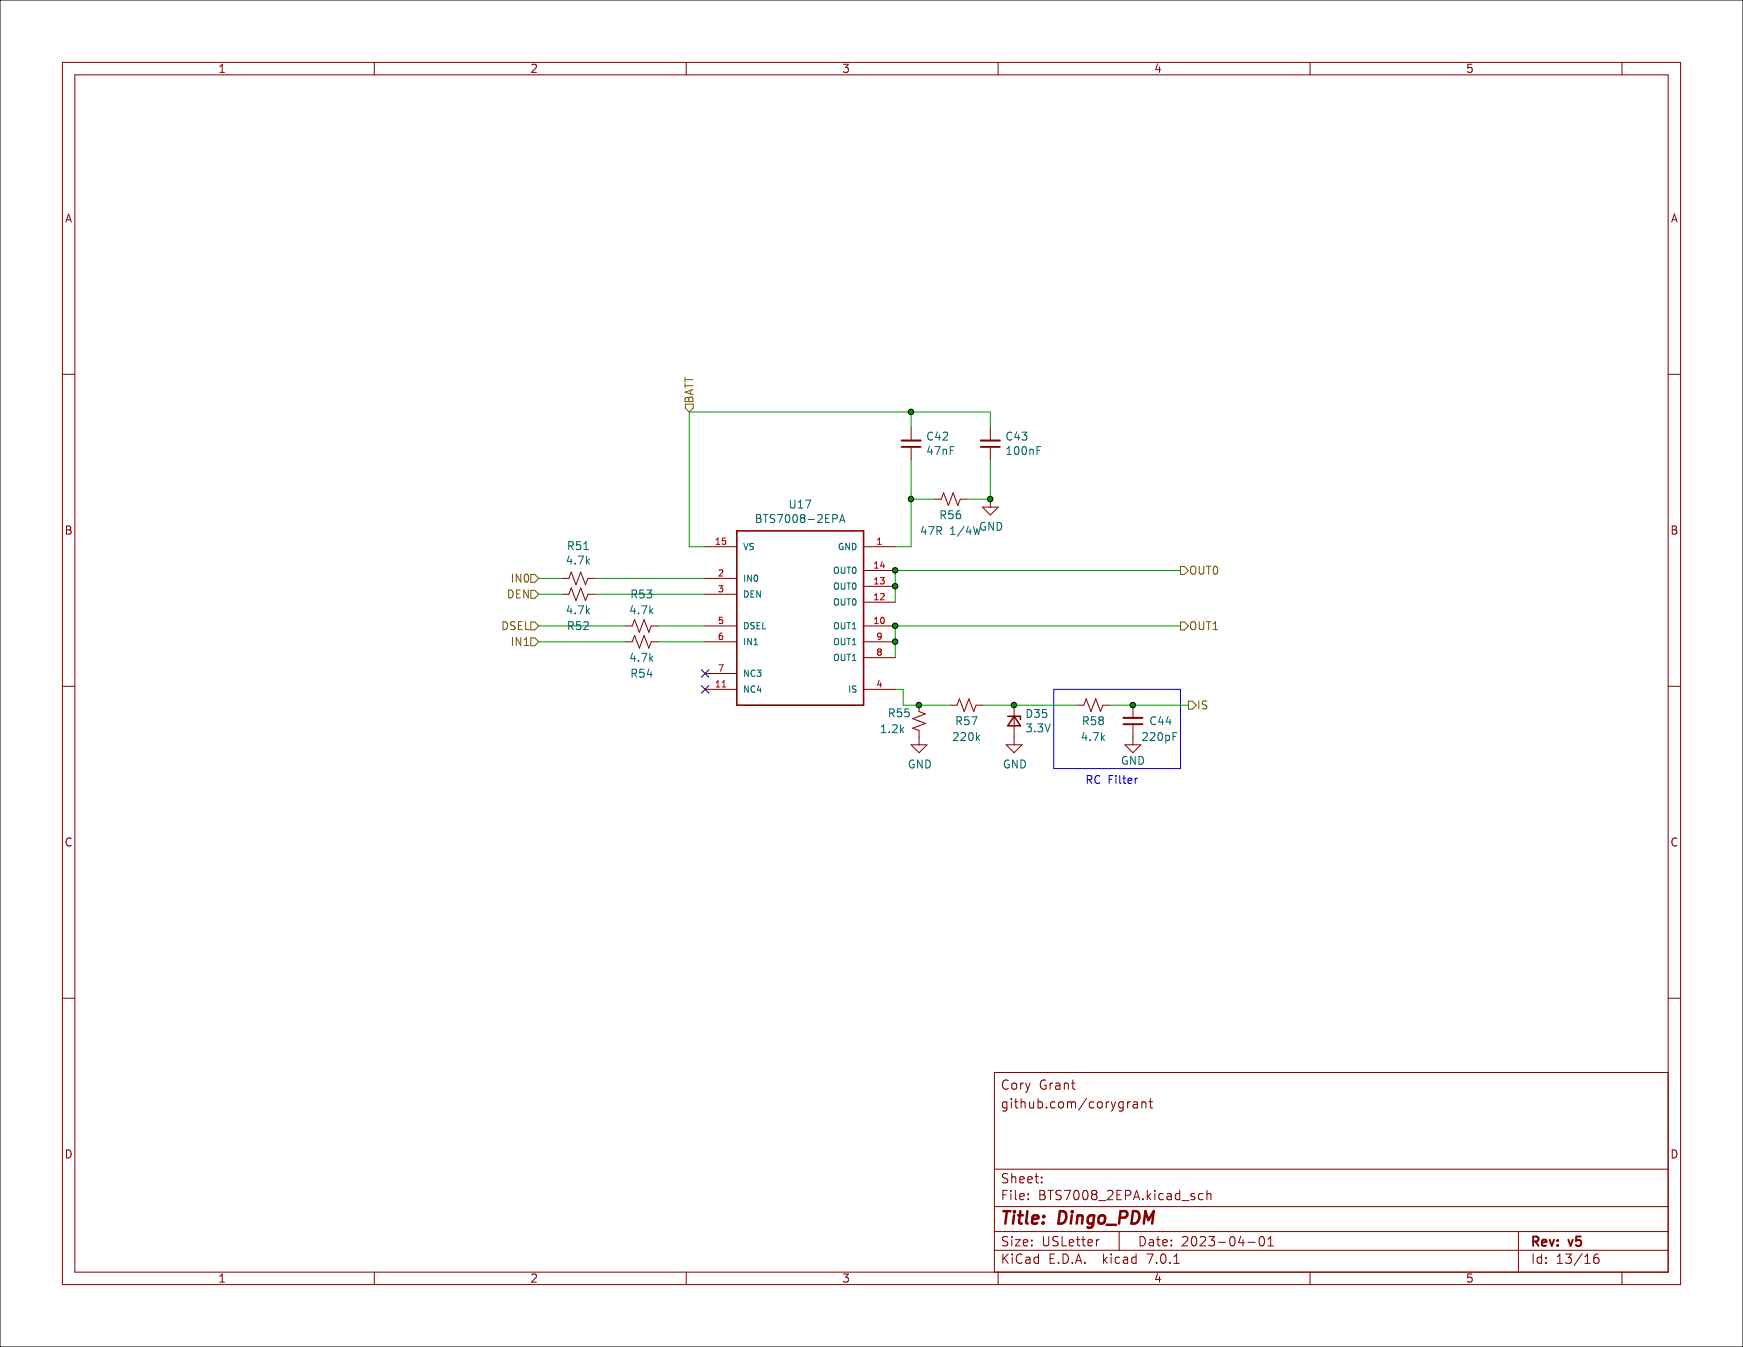
[picture p214: page 13]

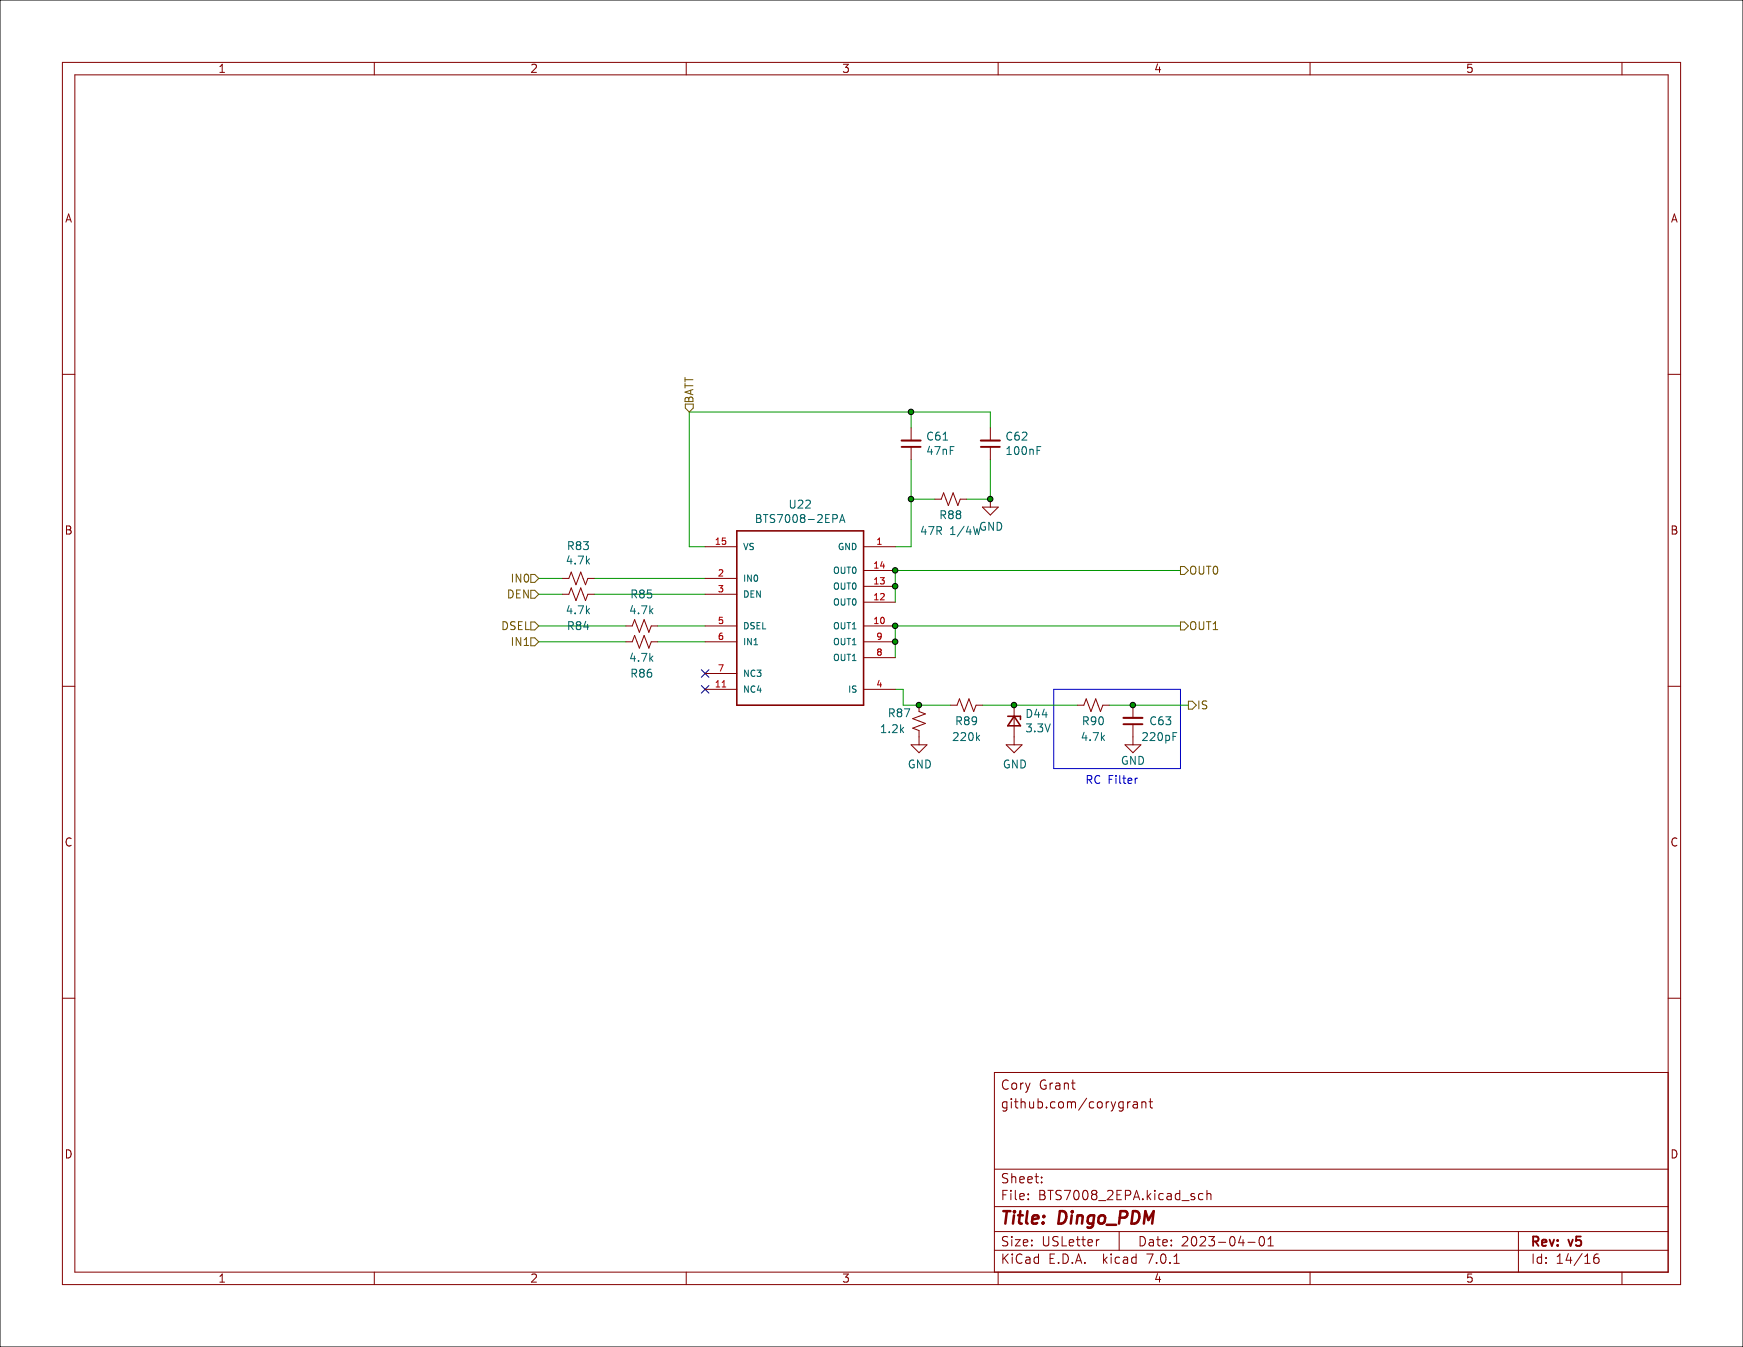
[picture p215: page 14]

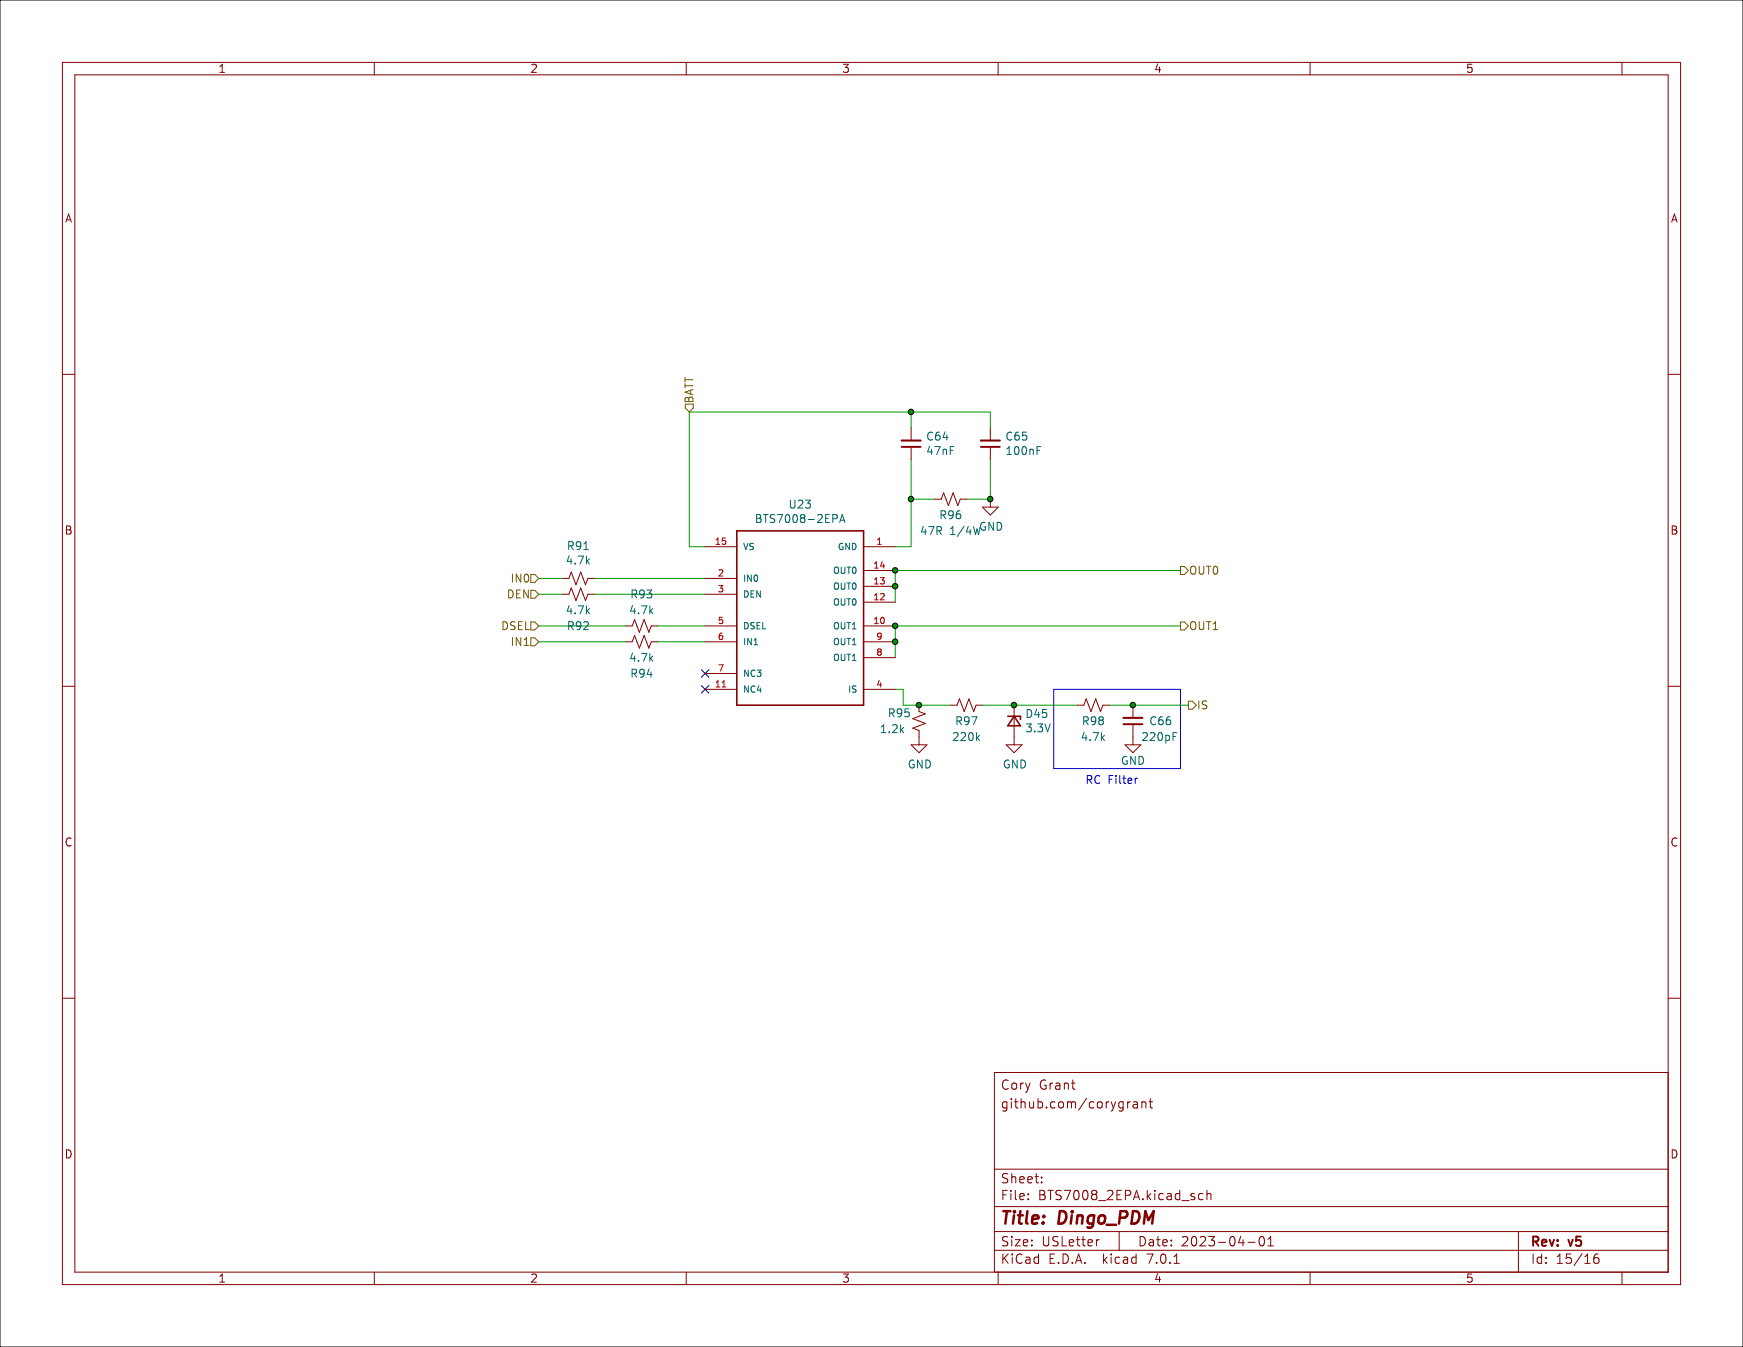
[picture p216: page 15]

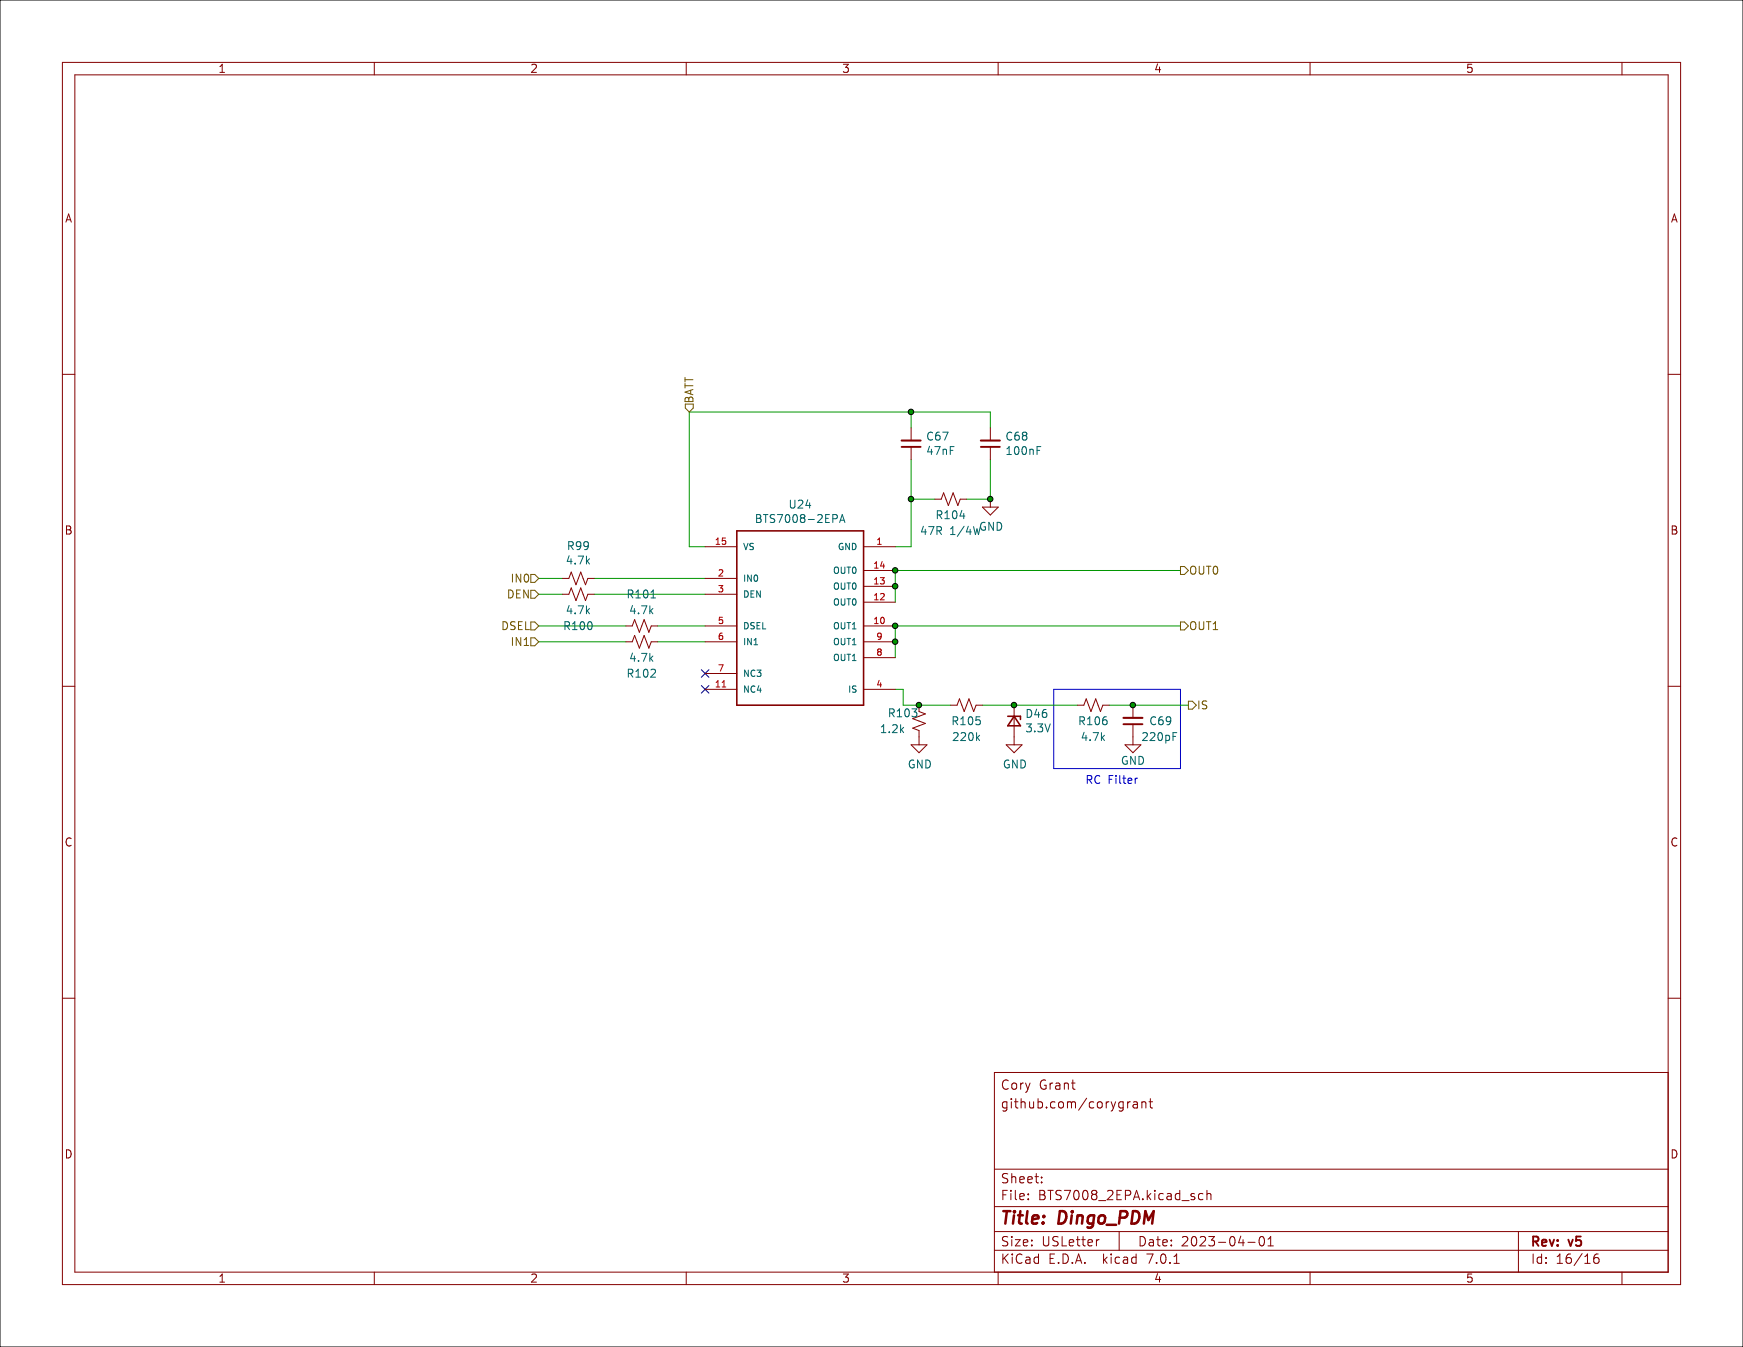
[picture p217: page 16]
