corygrant/dingoPDM/Export/V5/DingoPDM_HW_V5_BW.pdf

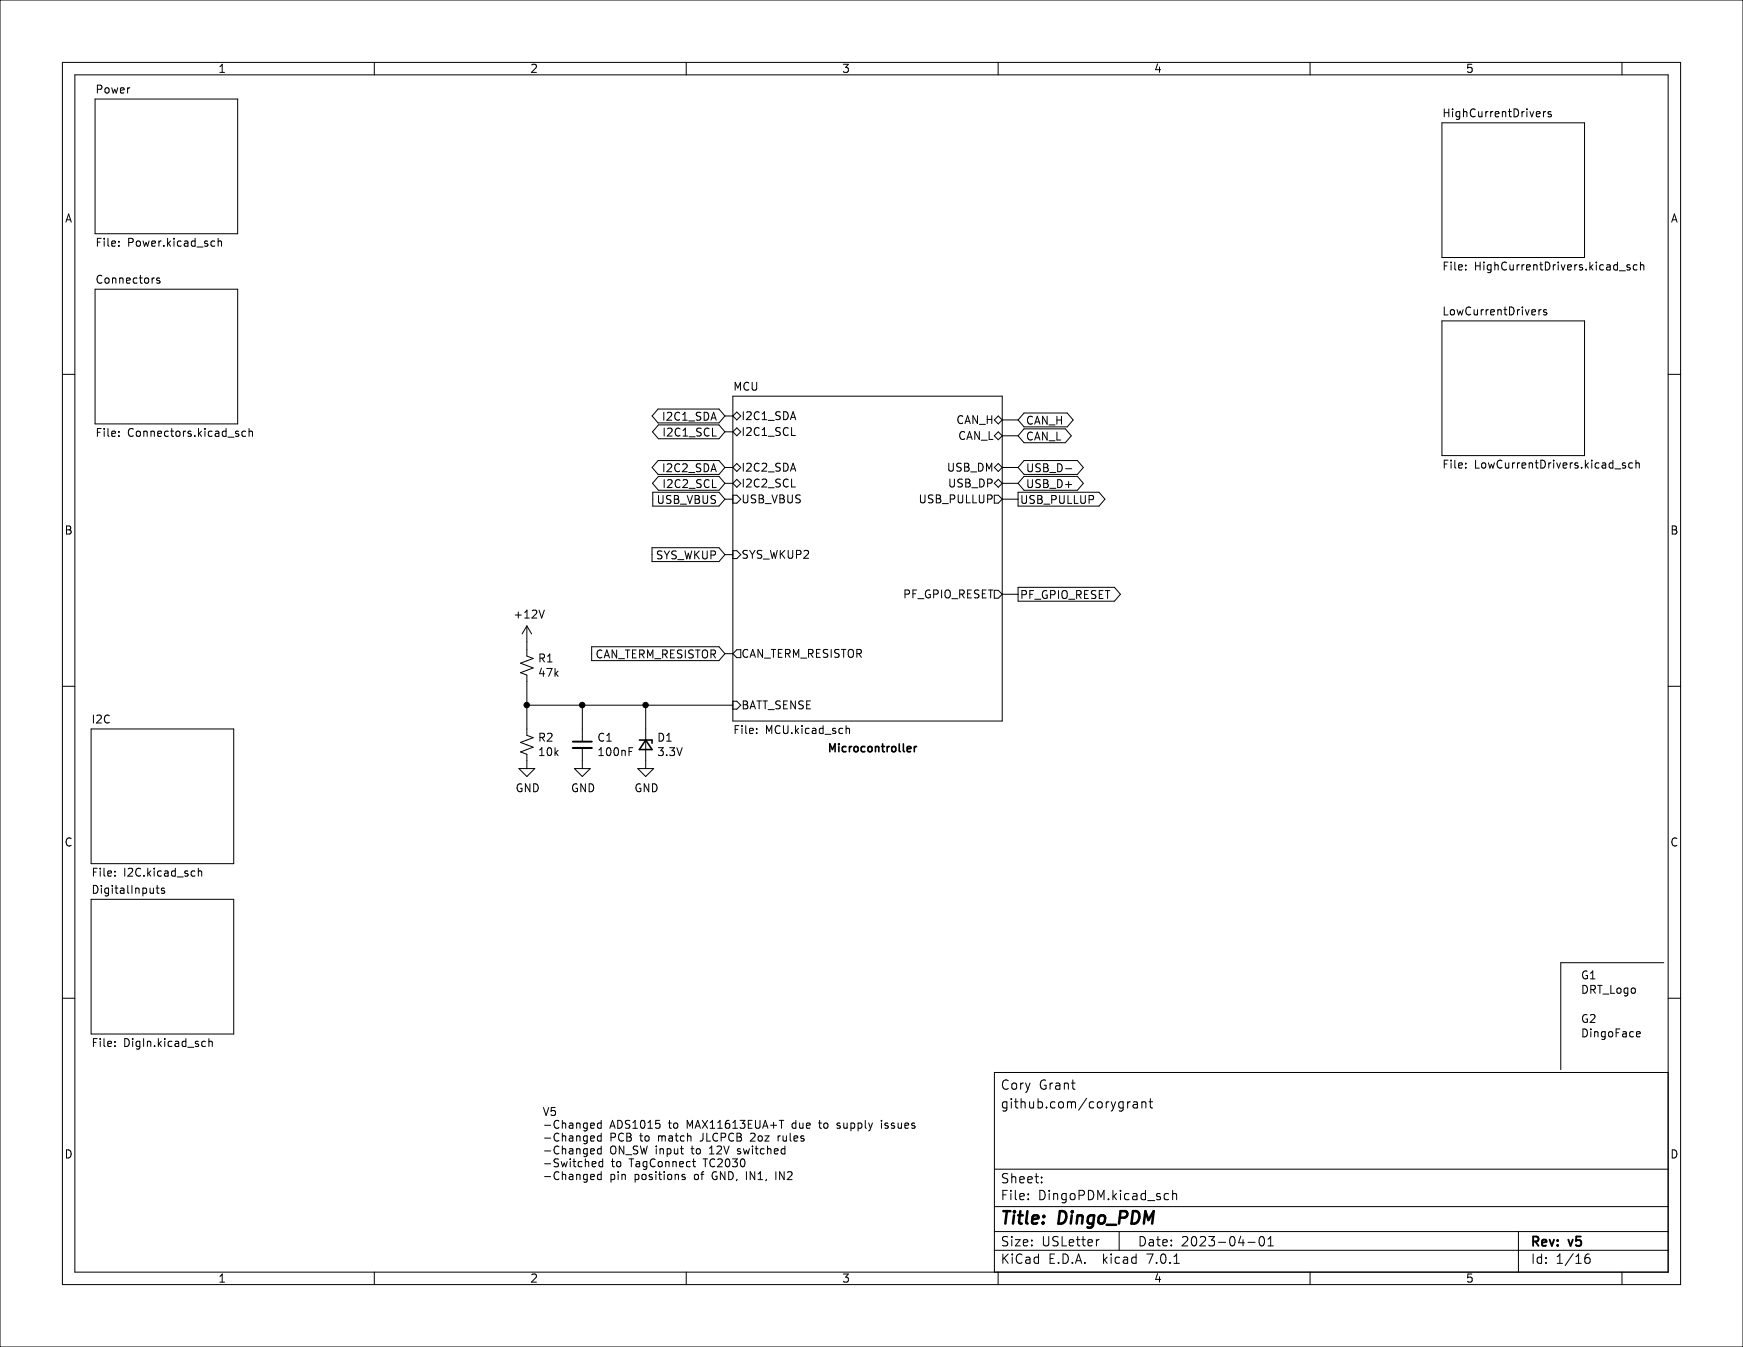
[picture p218: page 1]

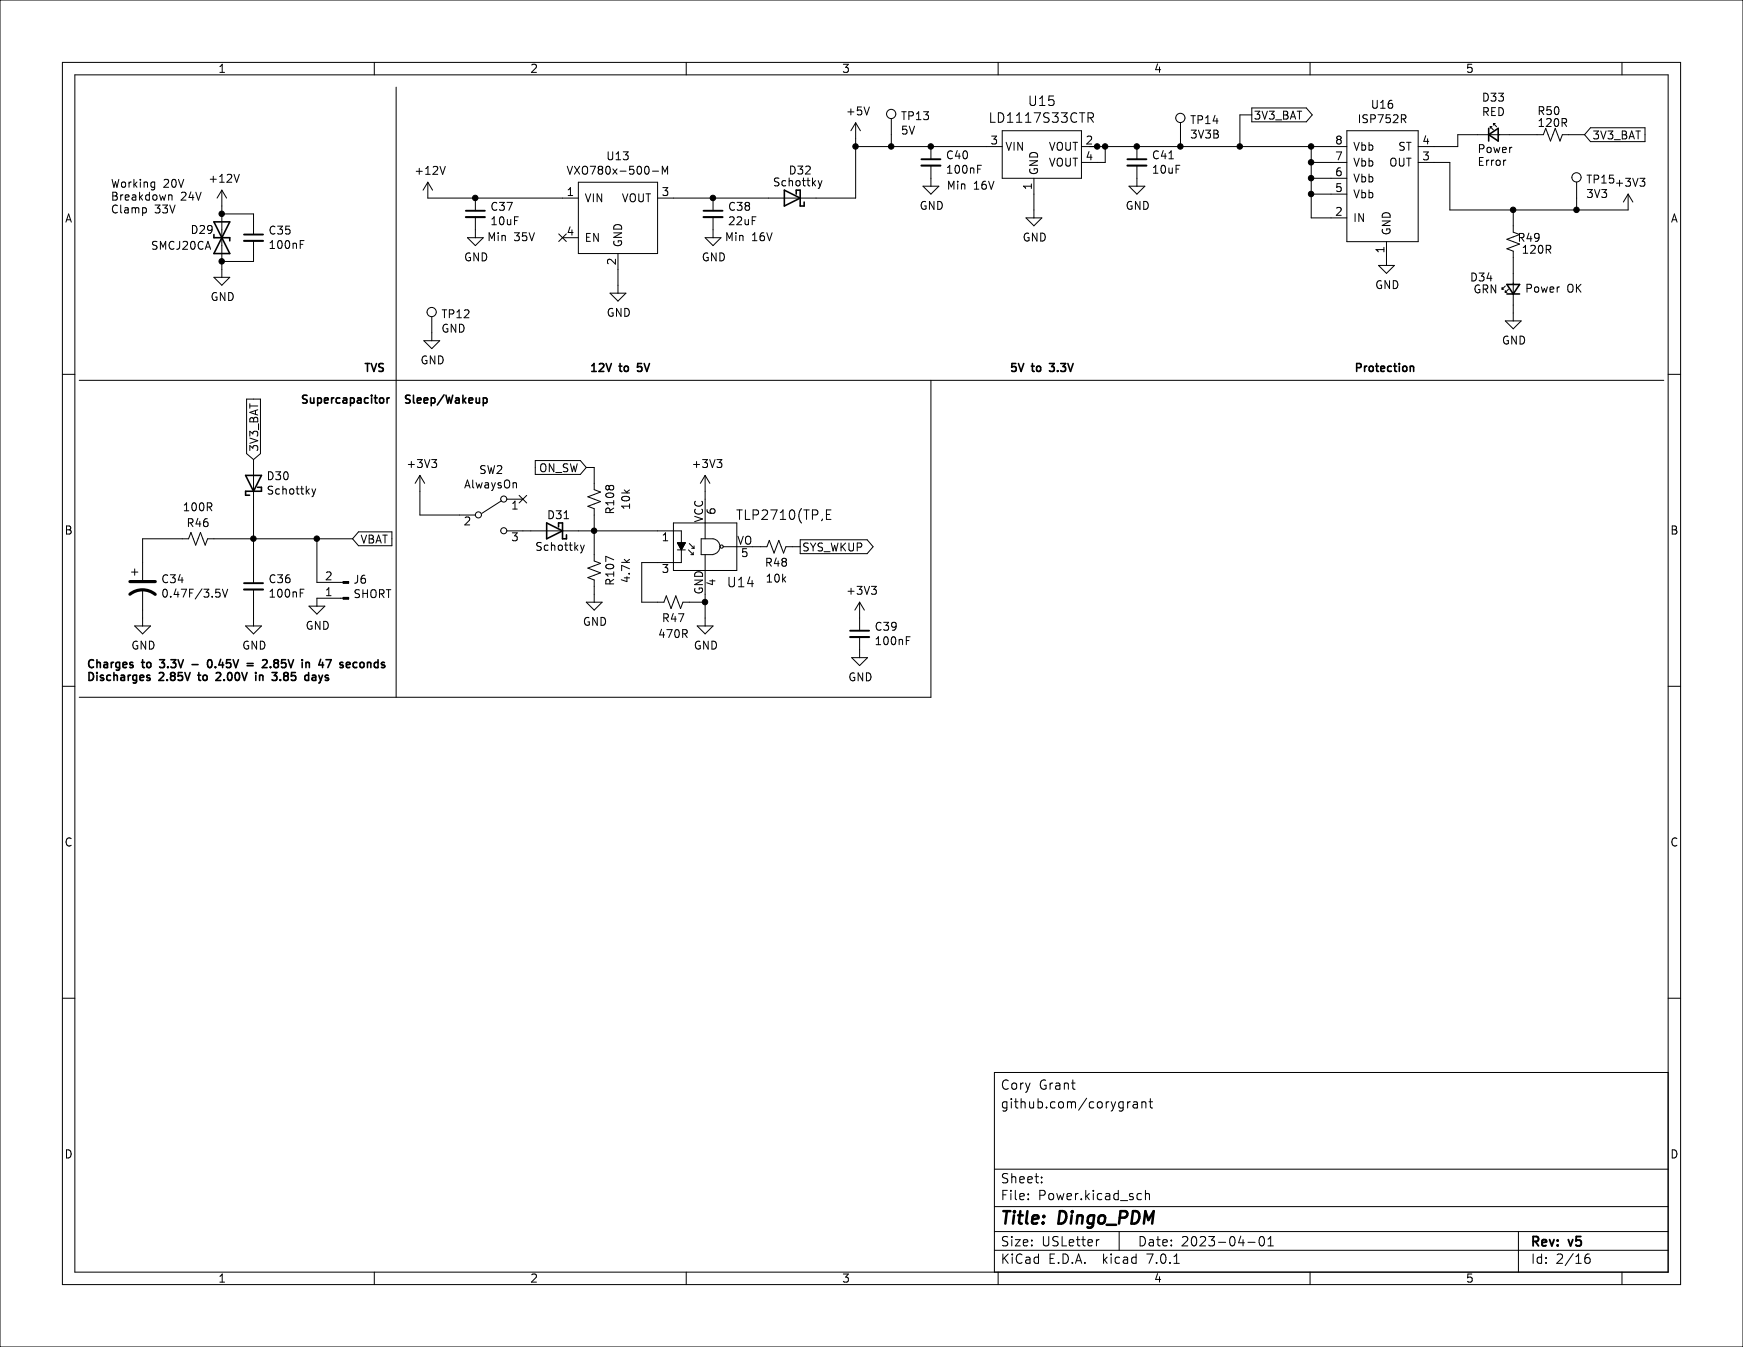
[picture p219: page 2]

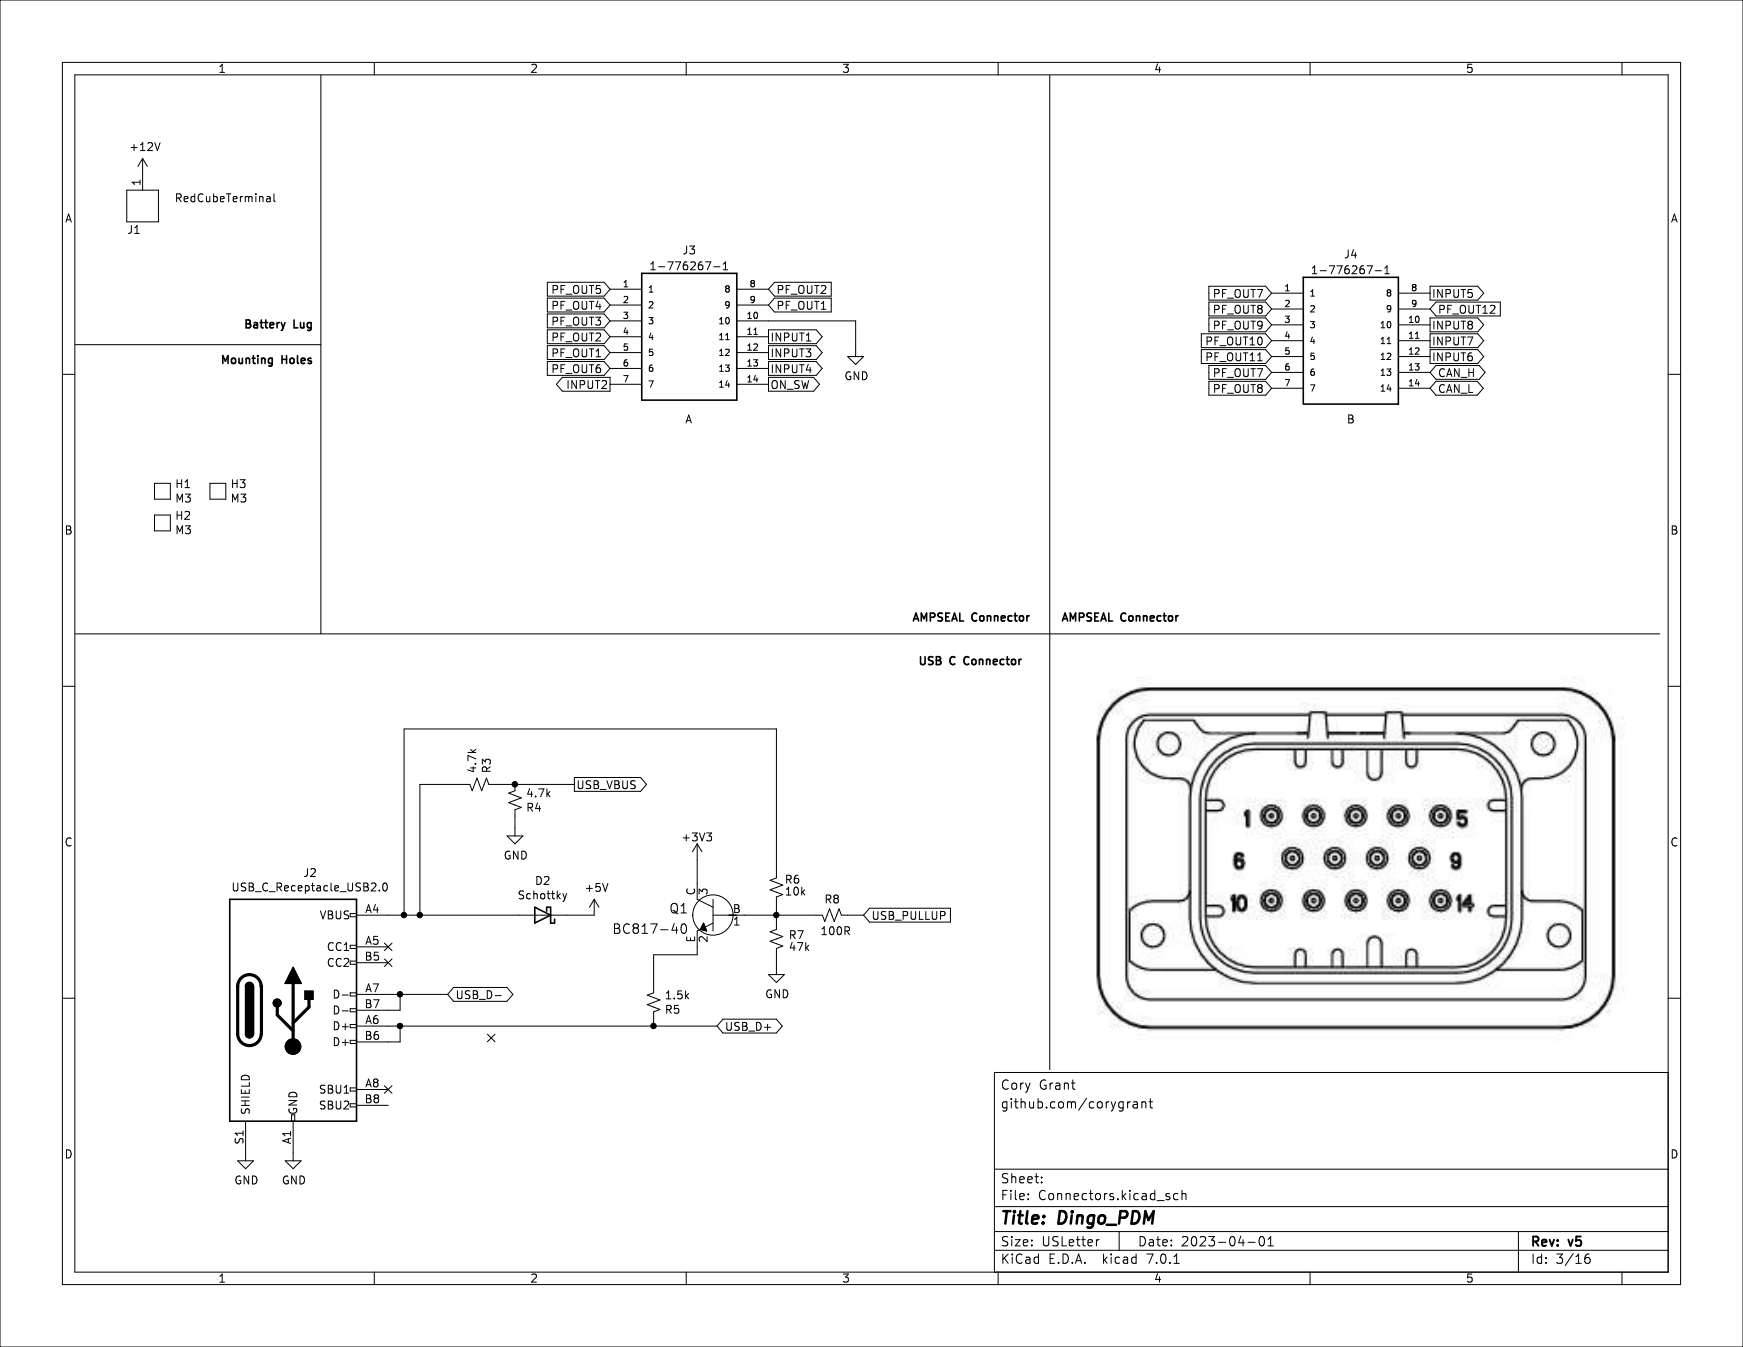
[picture p220: page 3]

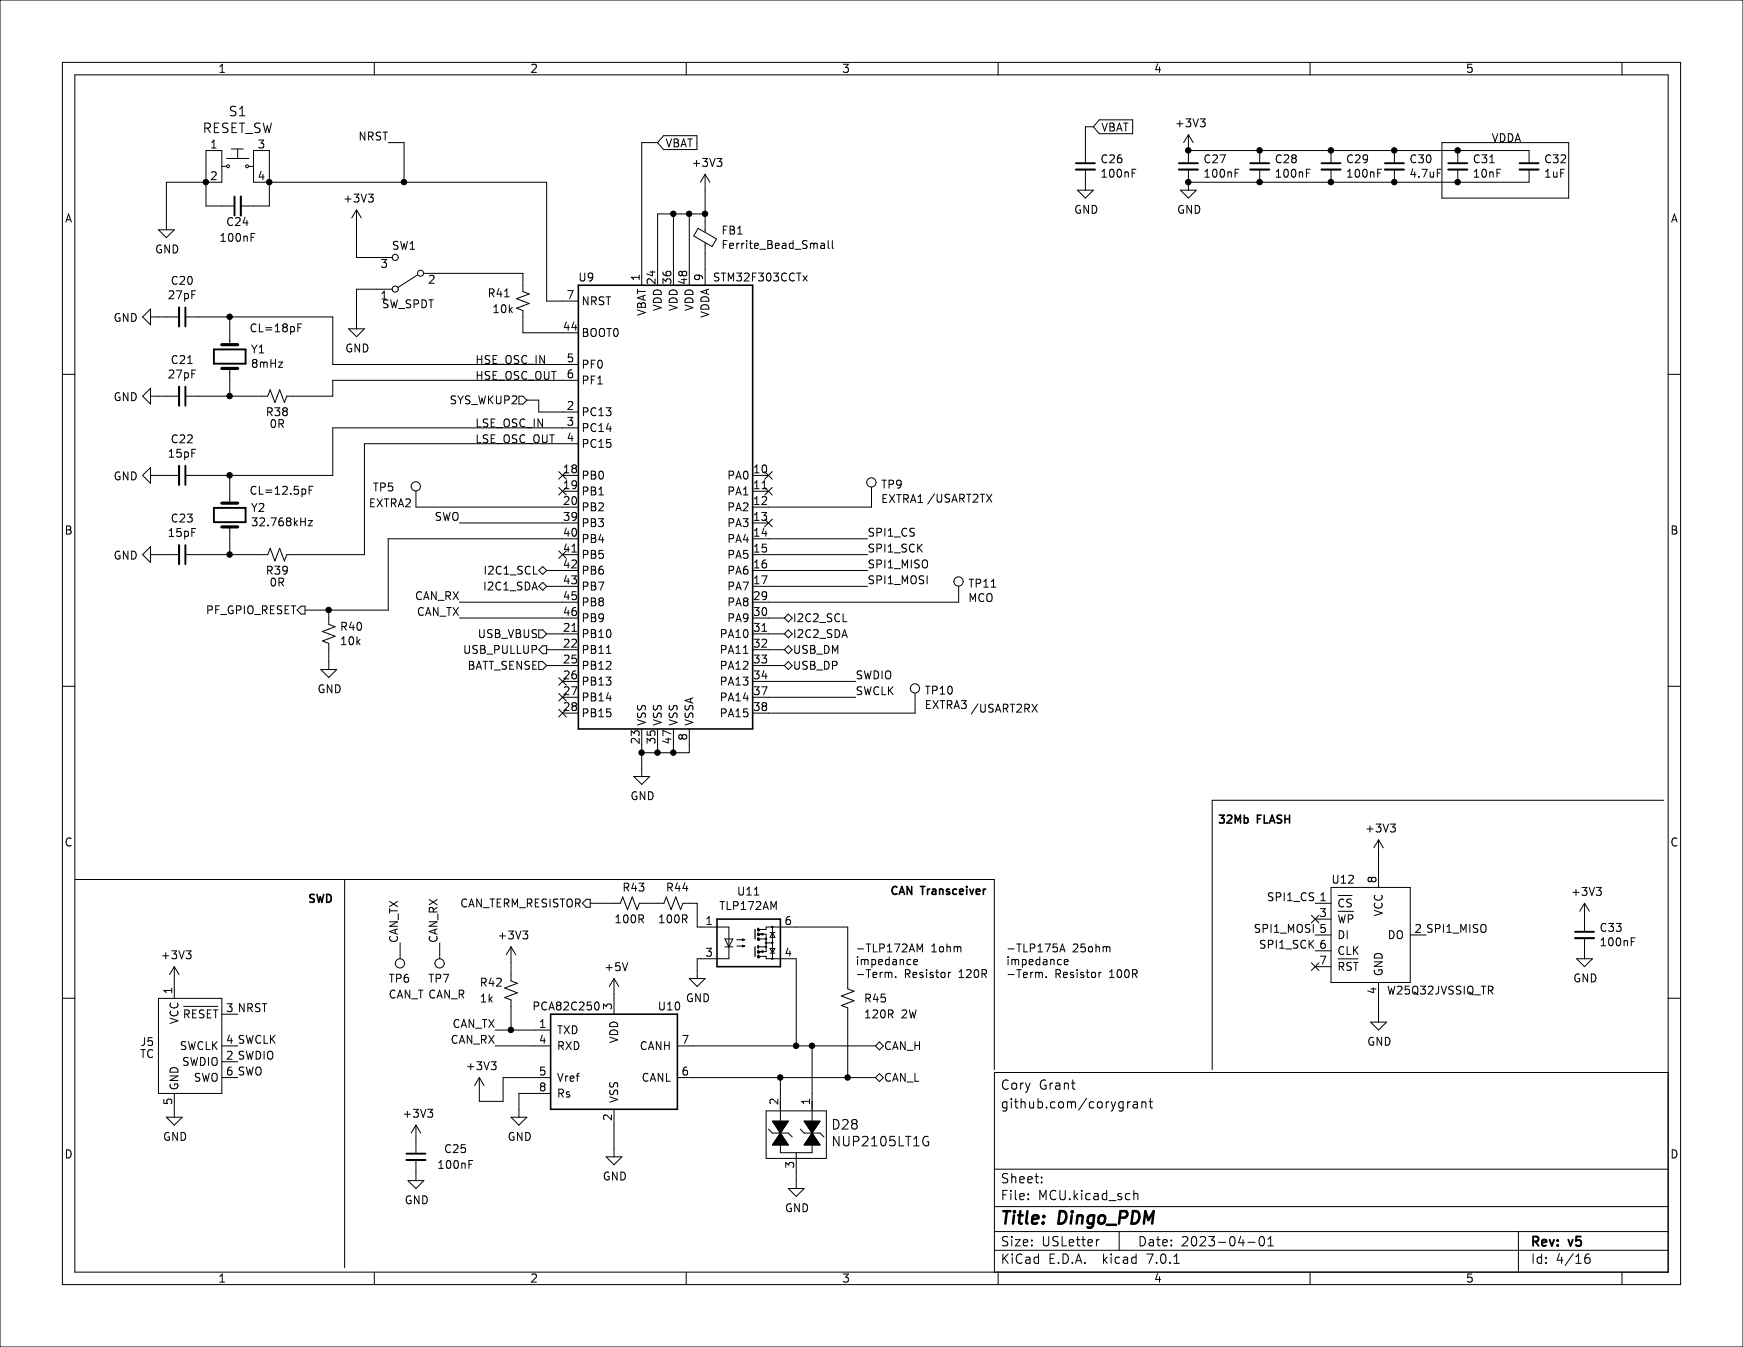
[picture p221: page 4]

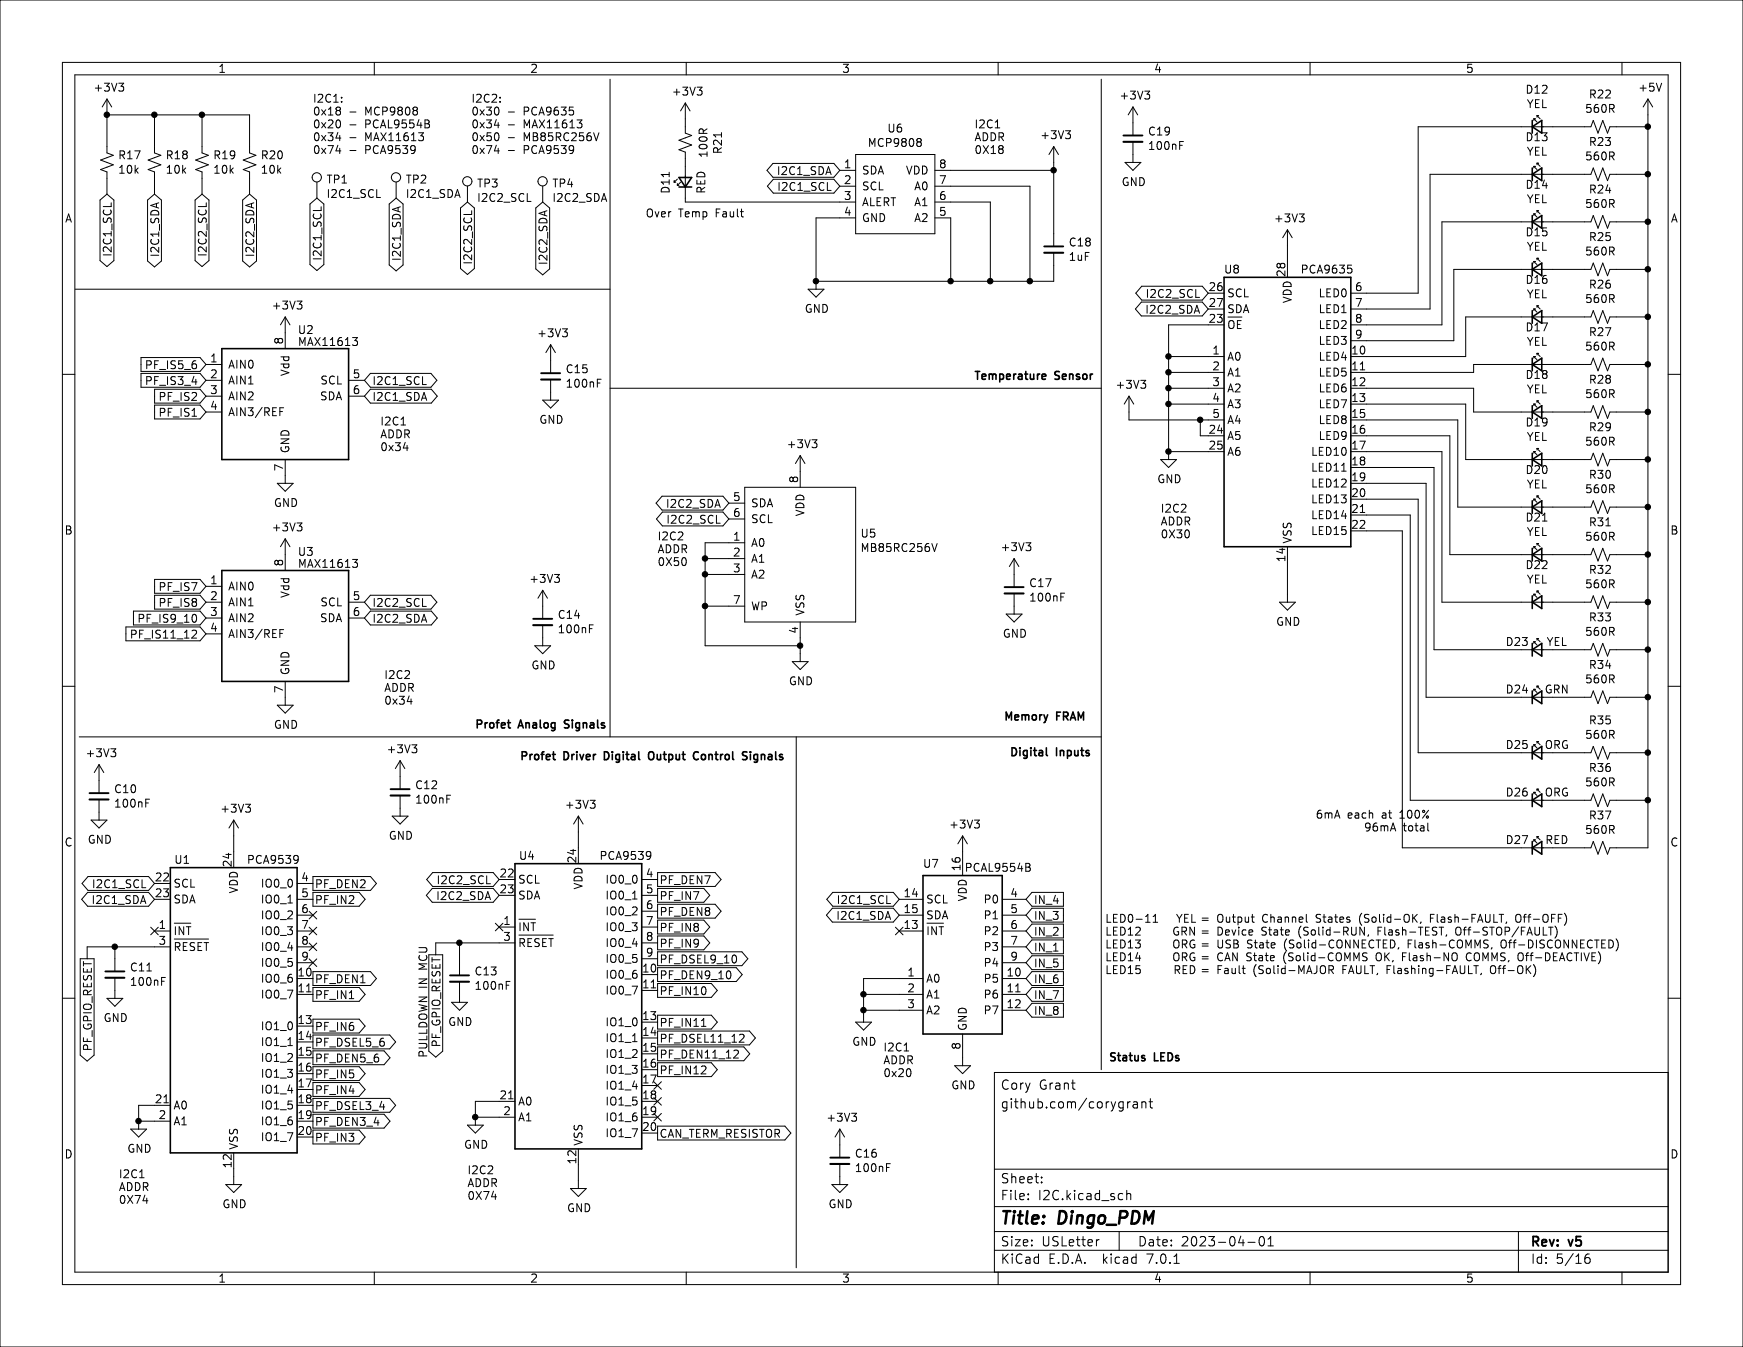
[picture p222: page 5]

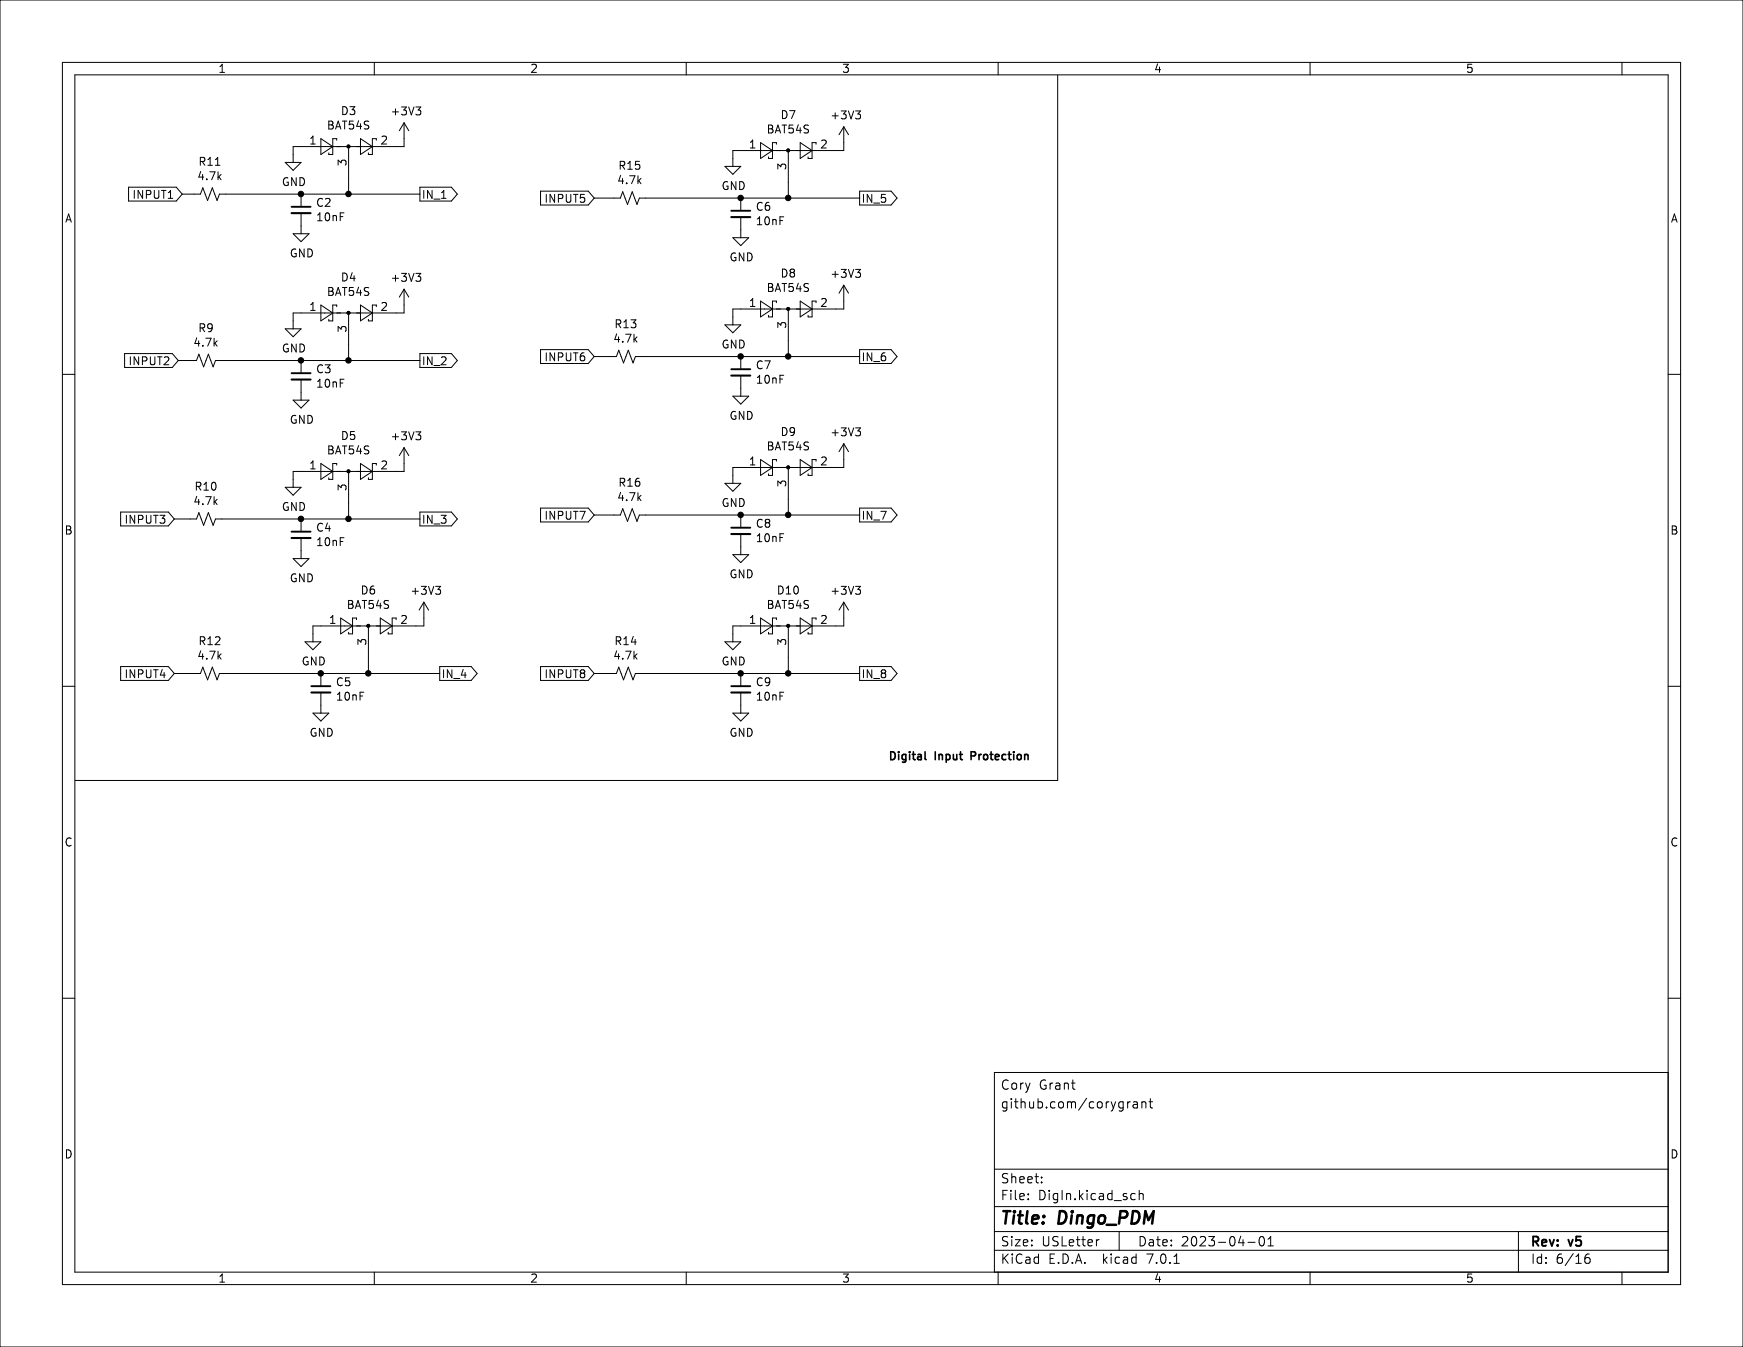
[picture p223: page 6]

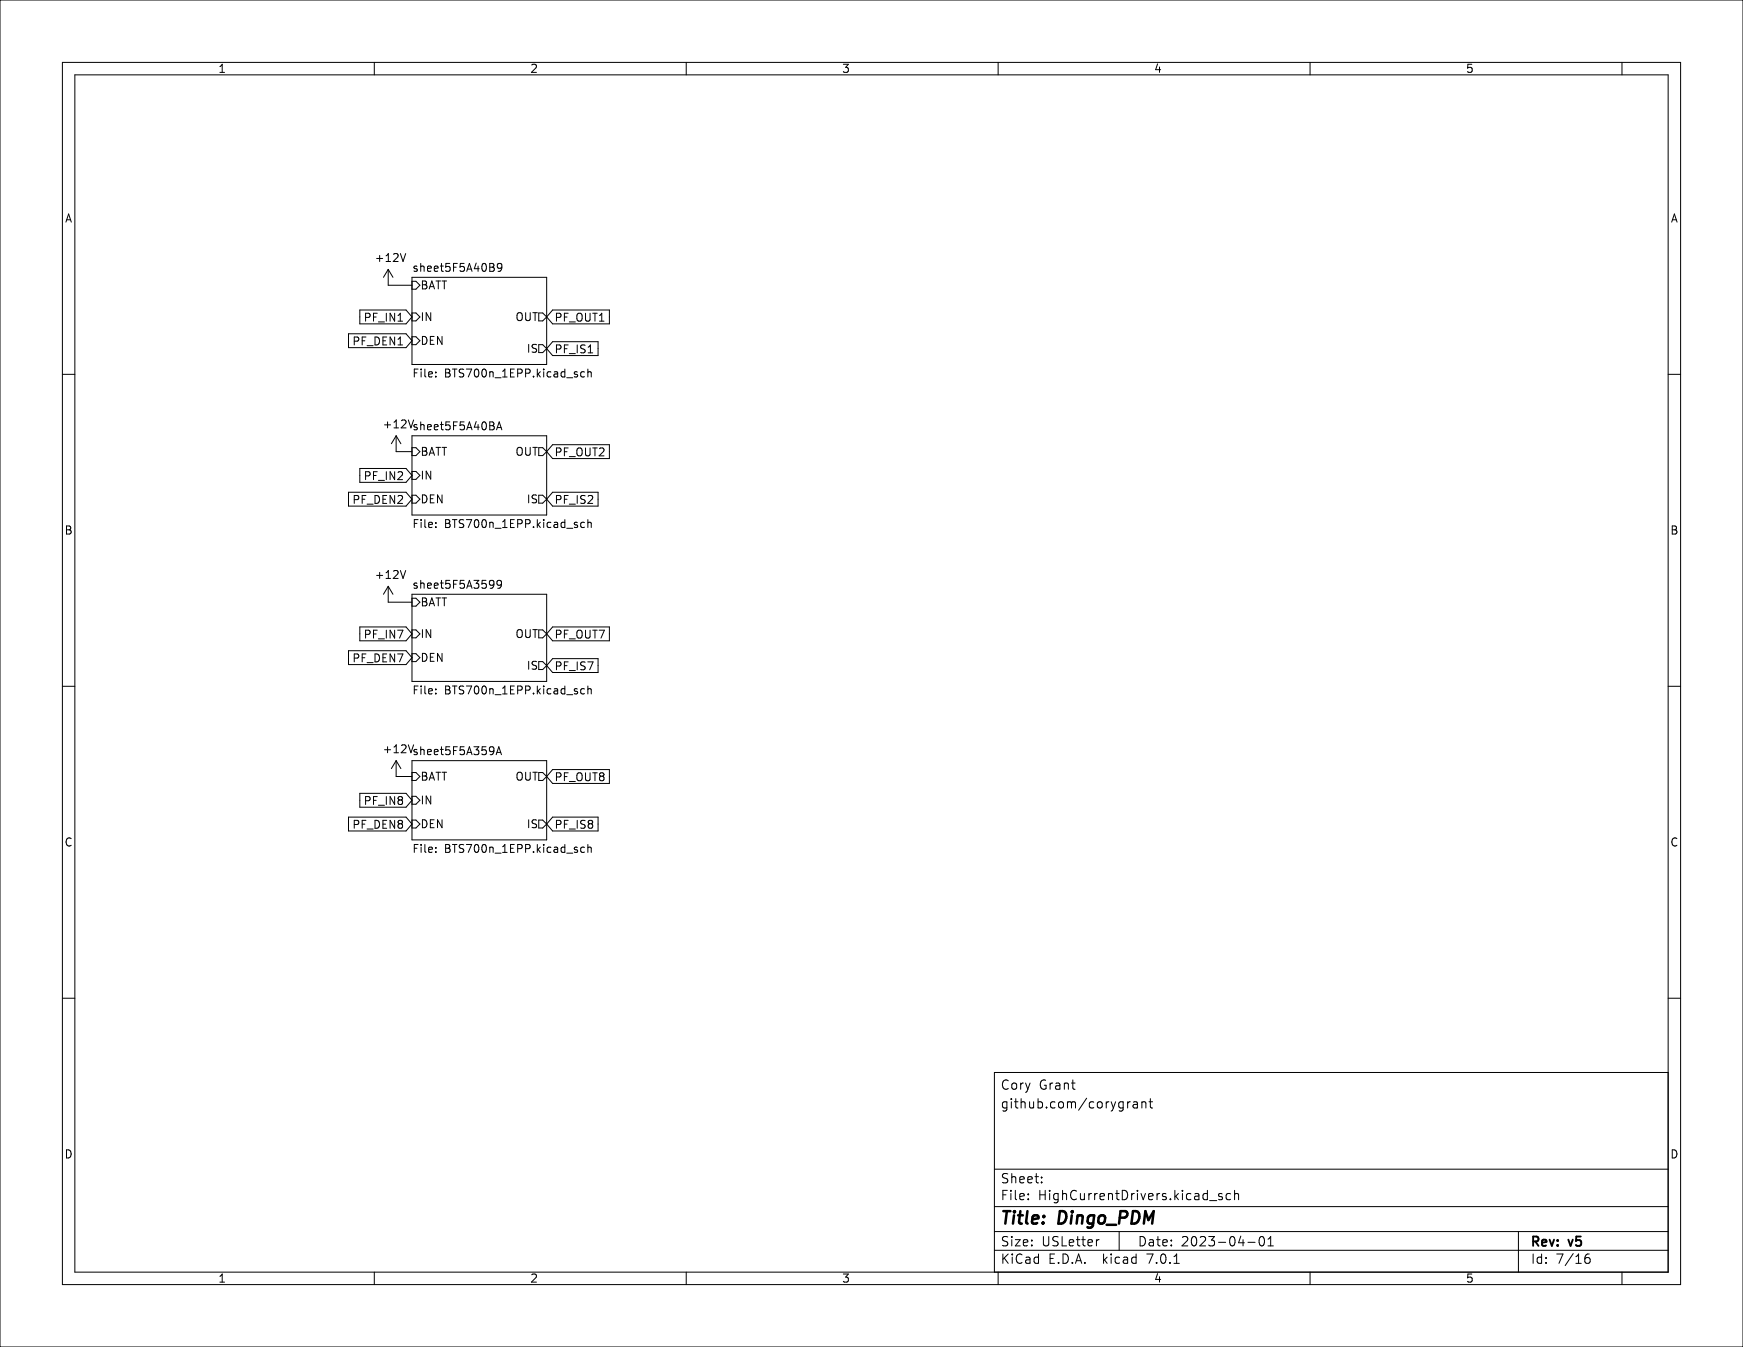
[picture p224: page 7]

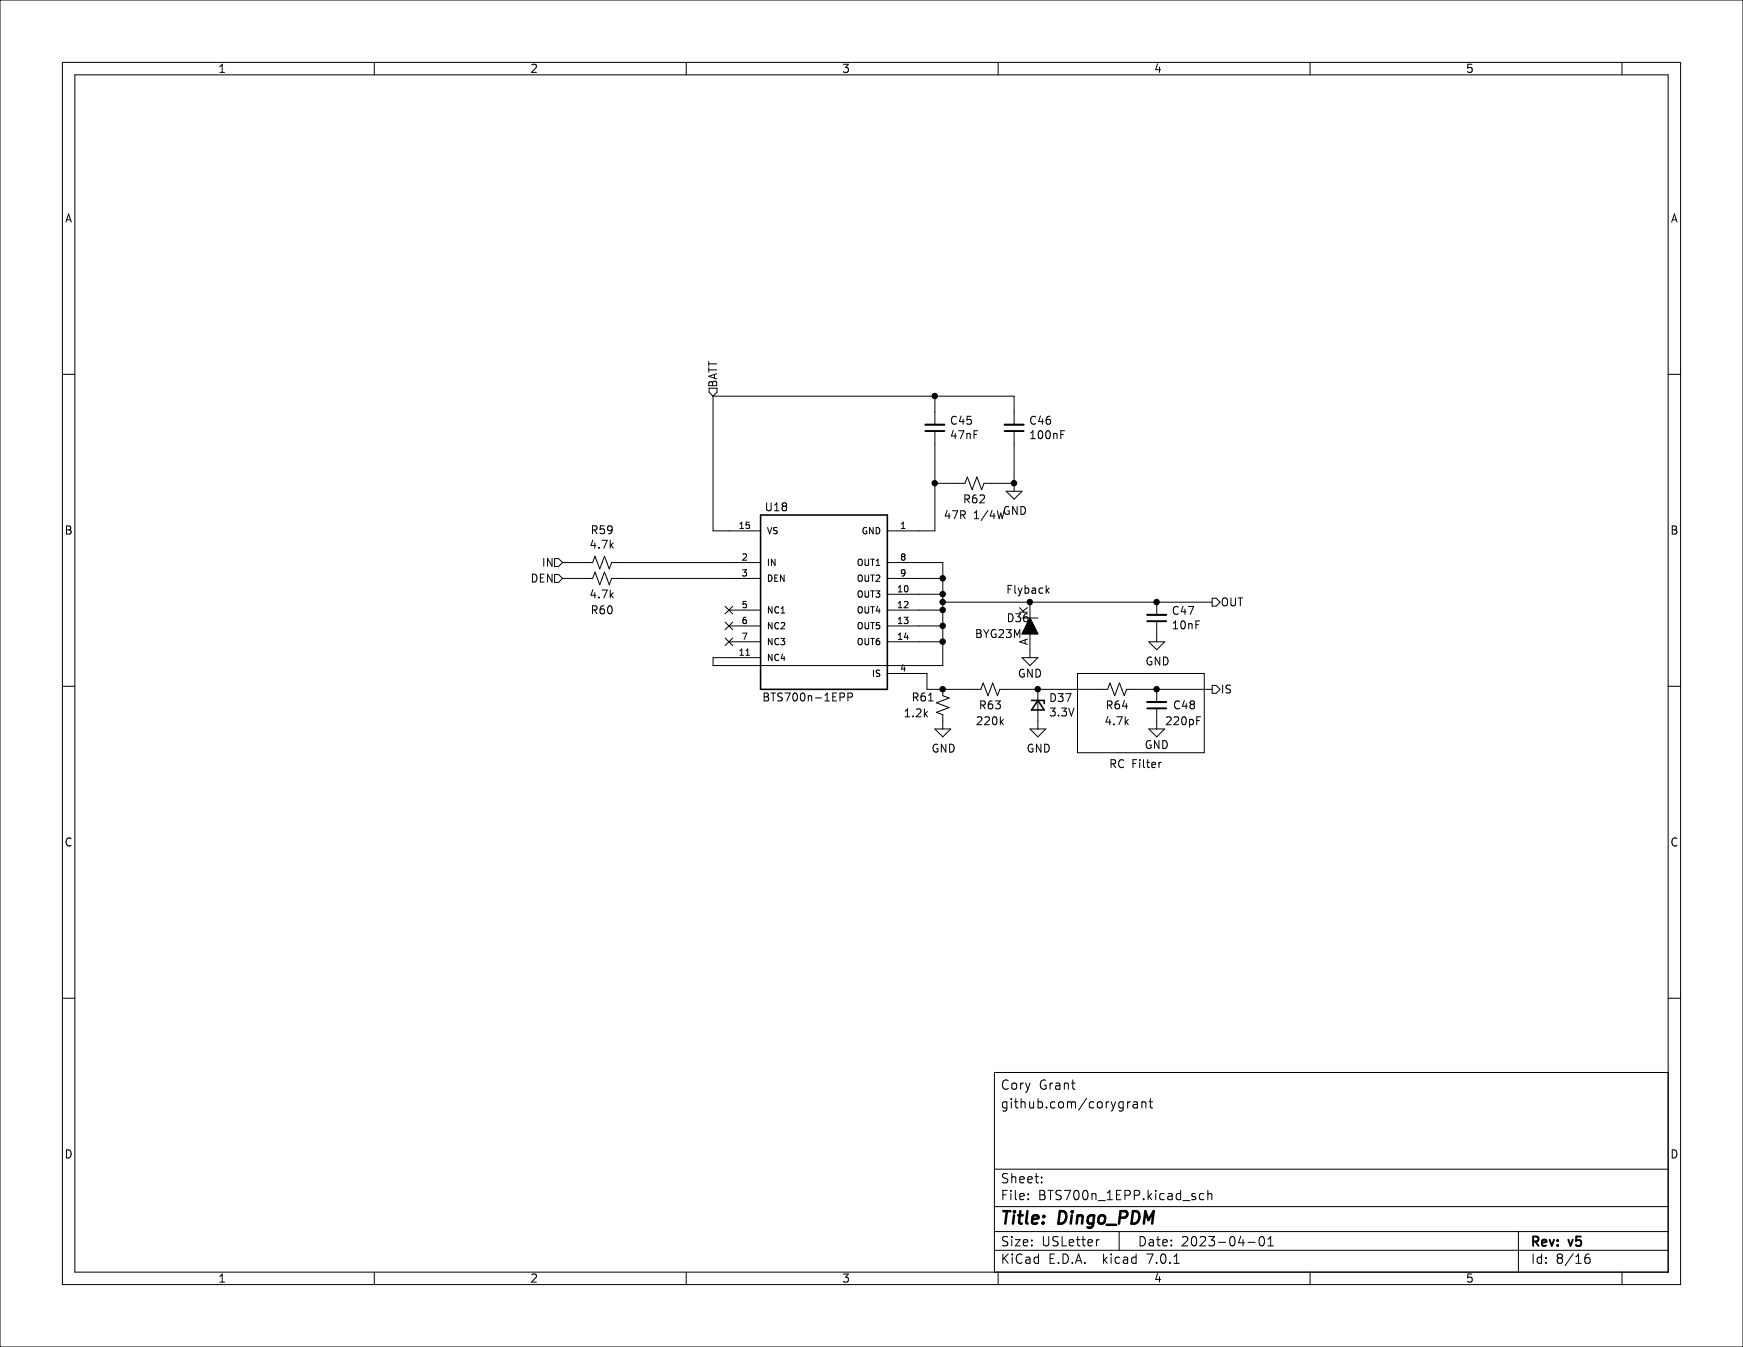
[picture p225: page 8]

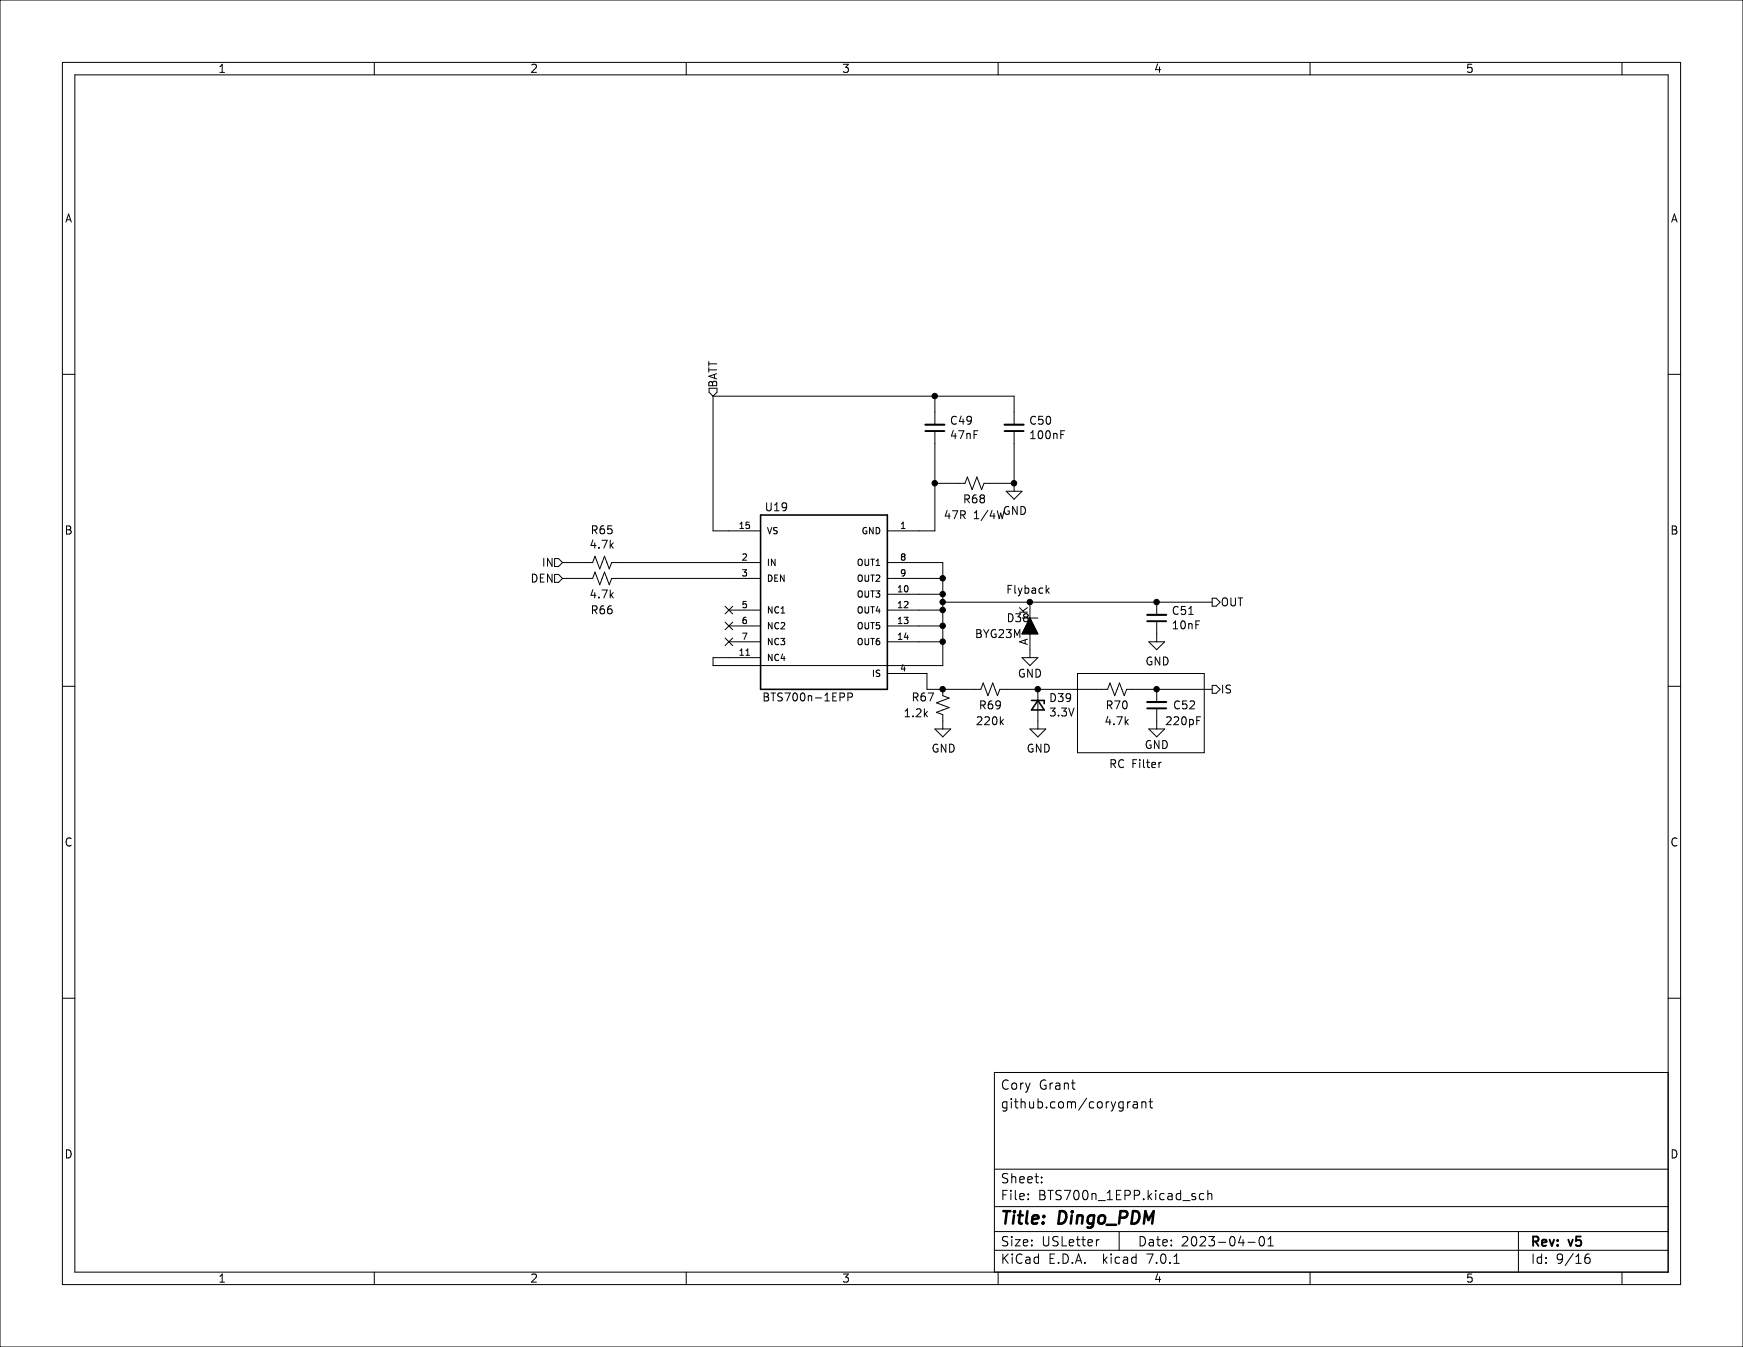
[picture p226: page 9]

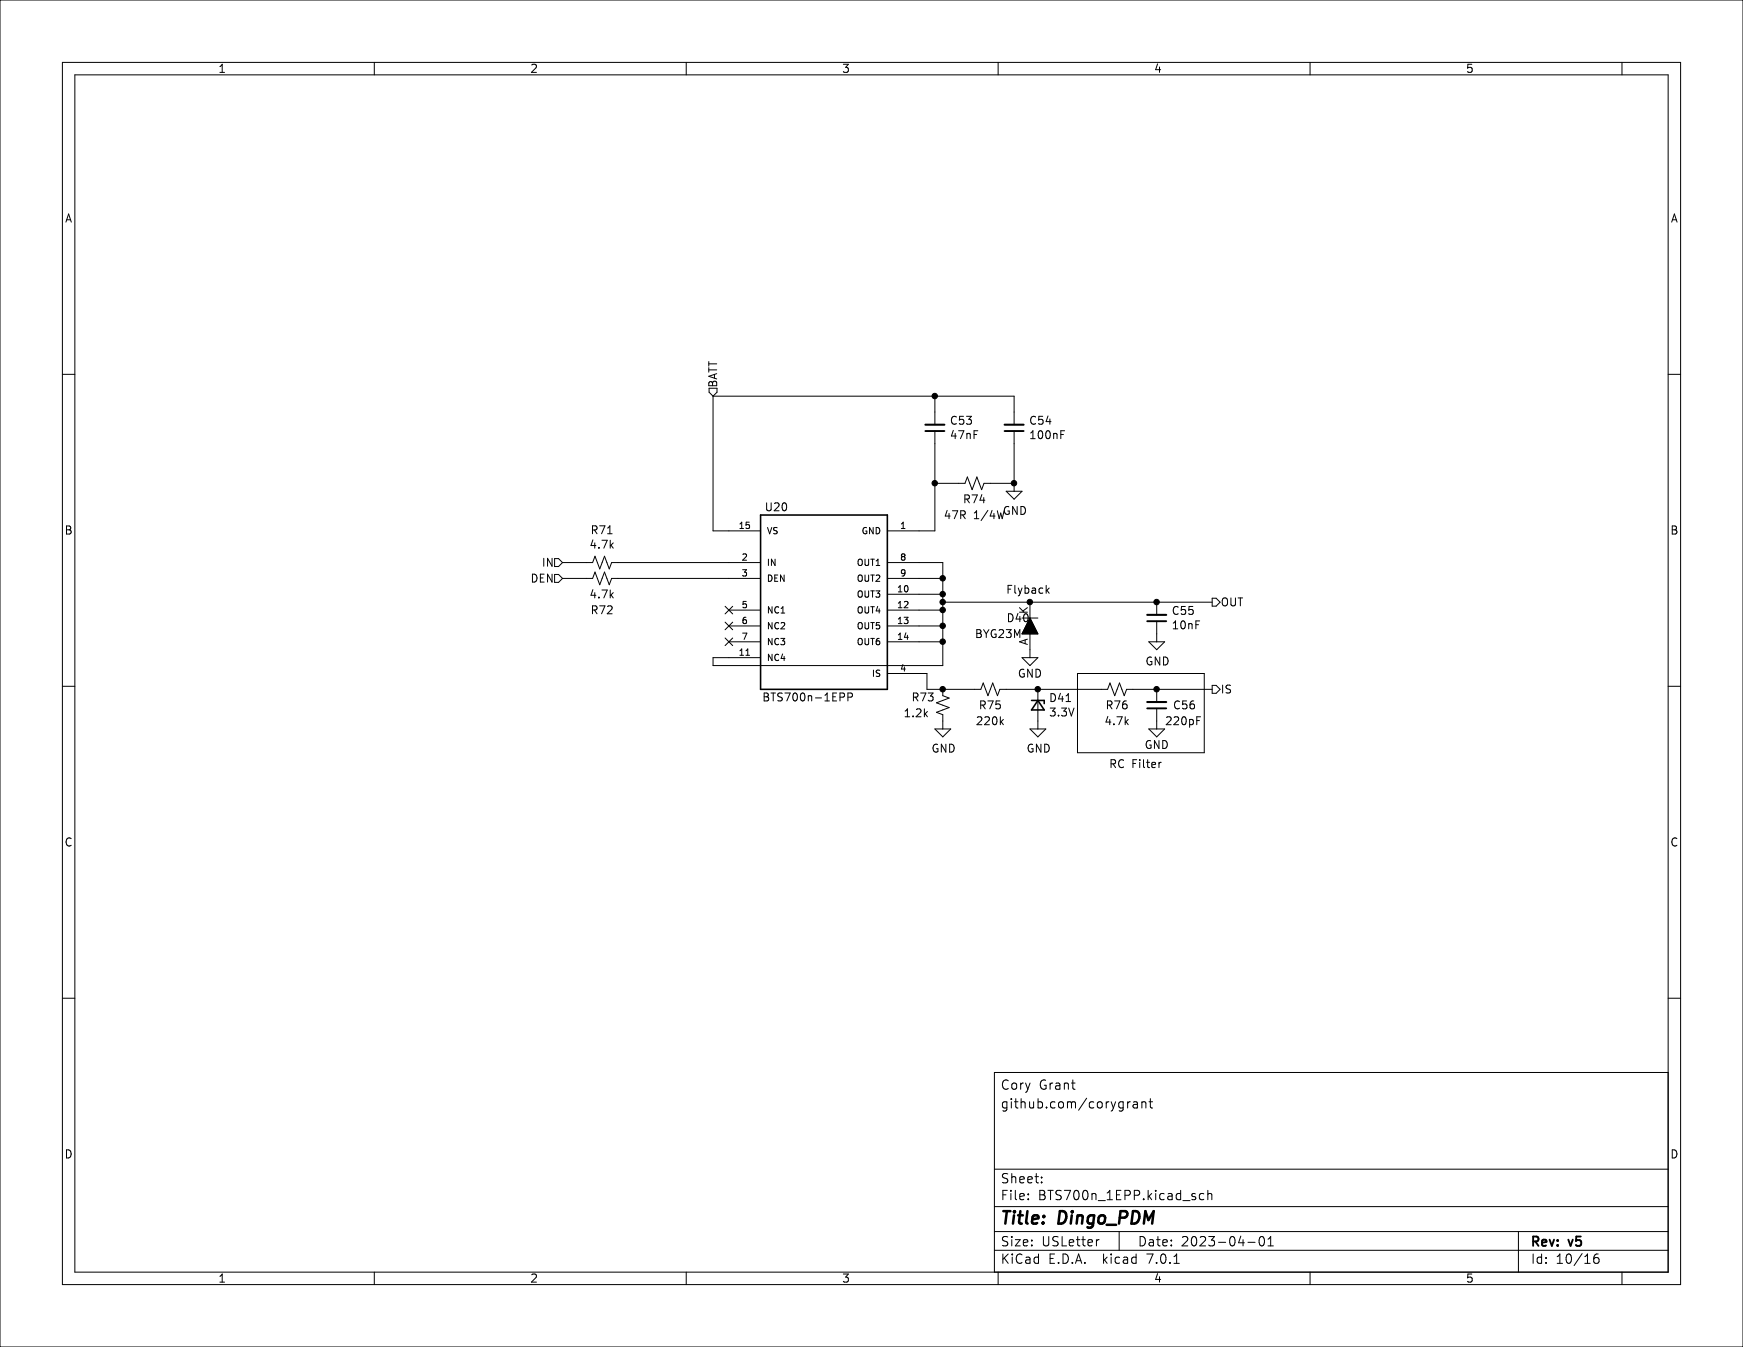
[picture p227: page 10]

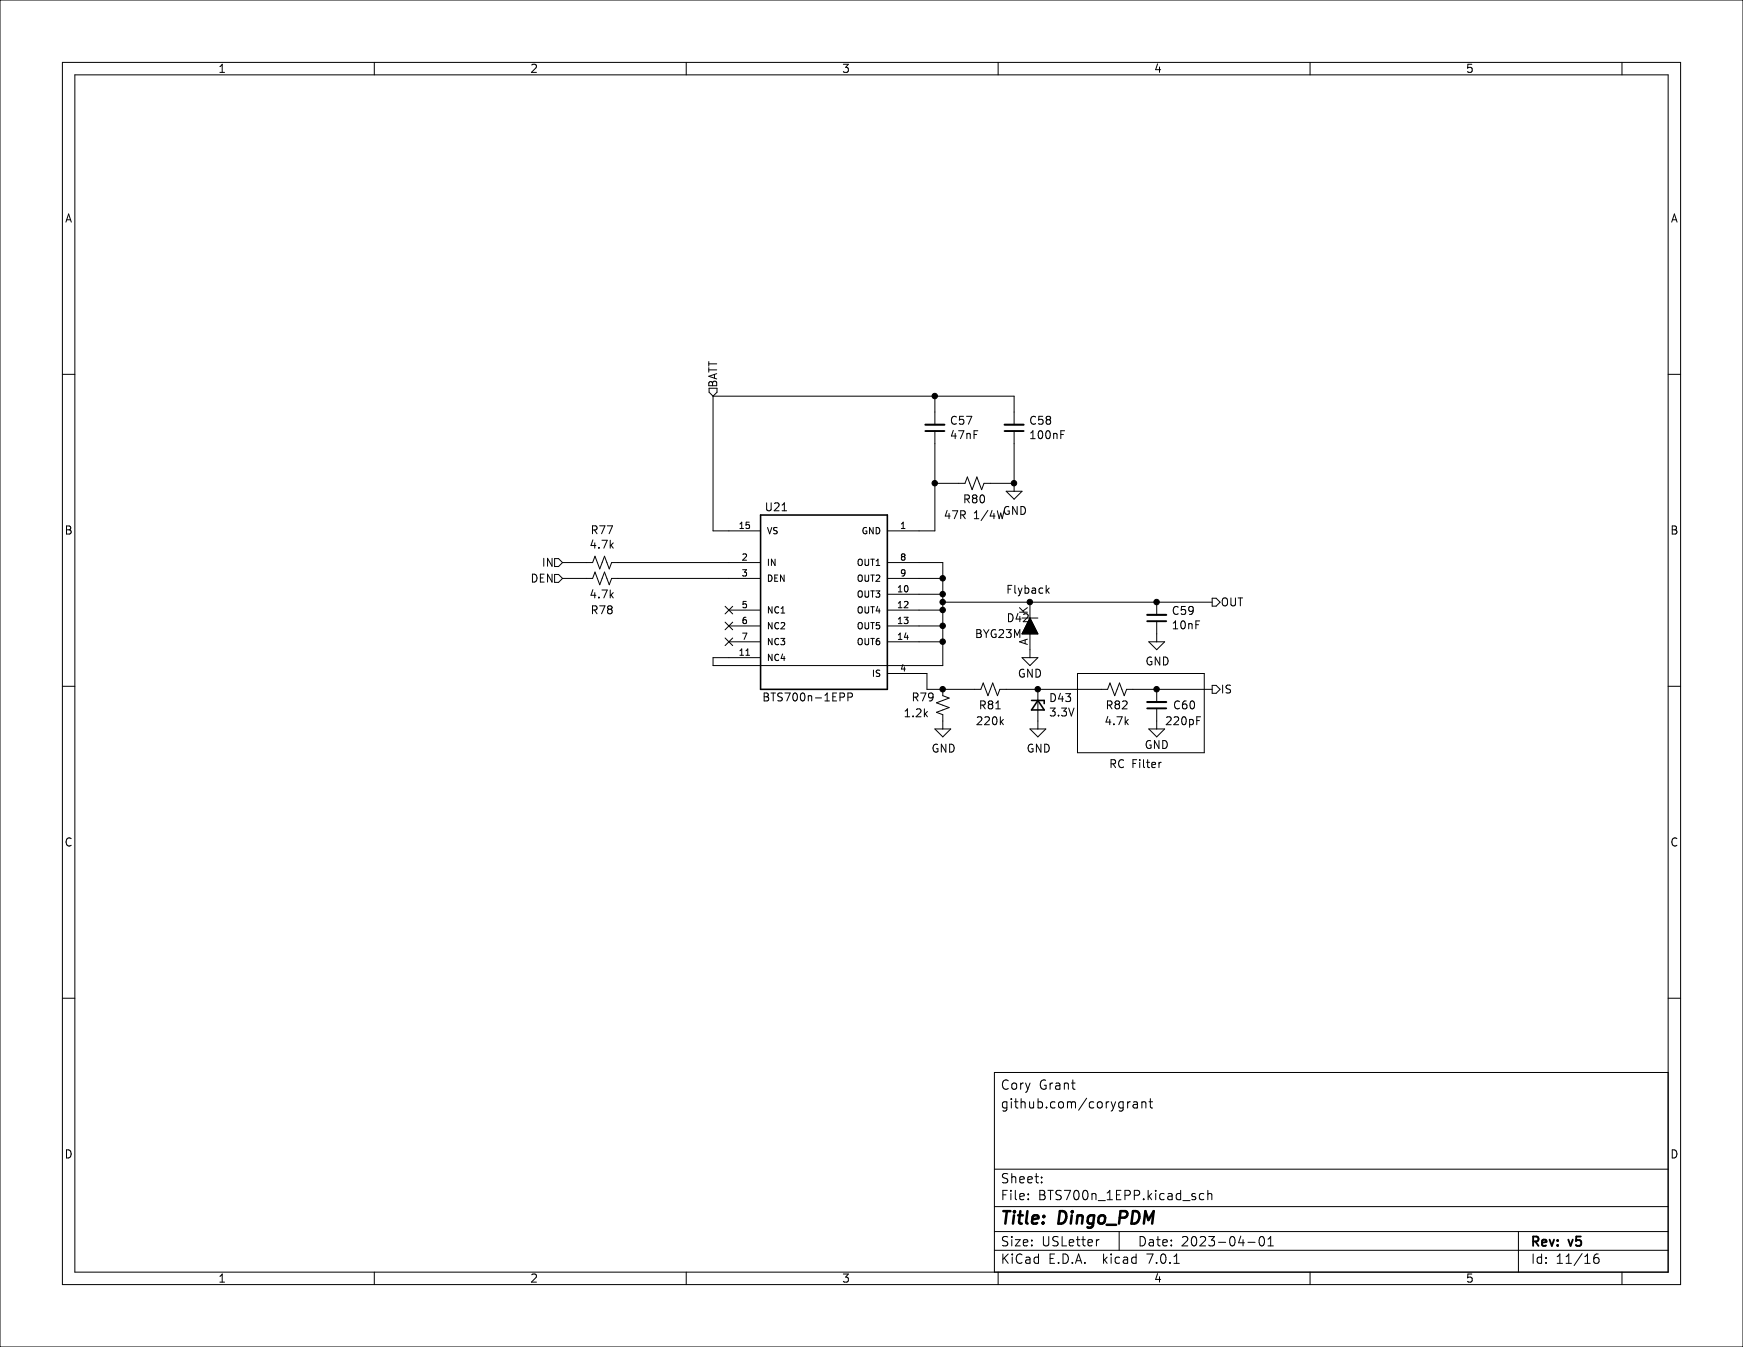
[picture p228: page 11]

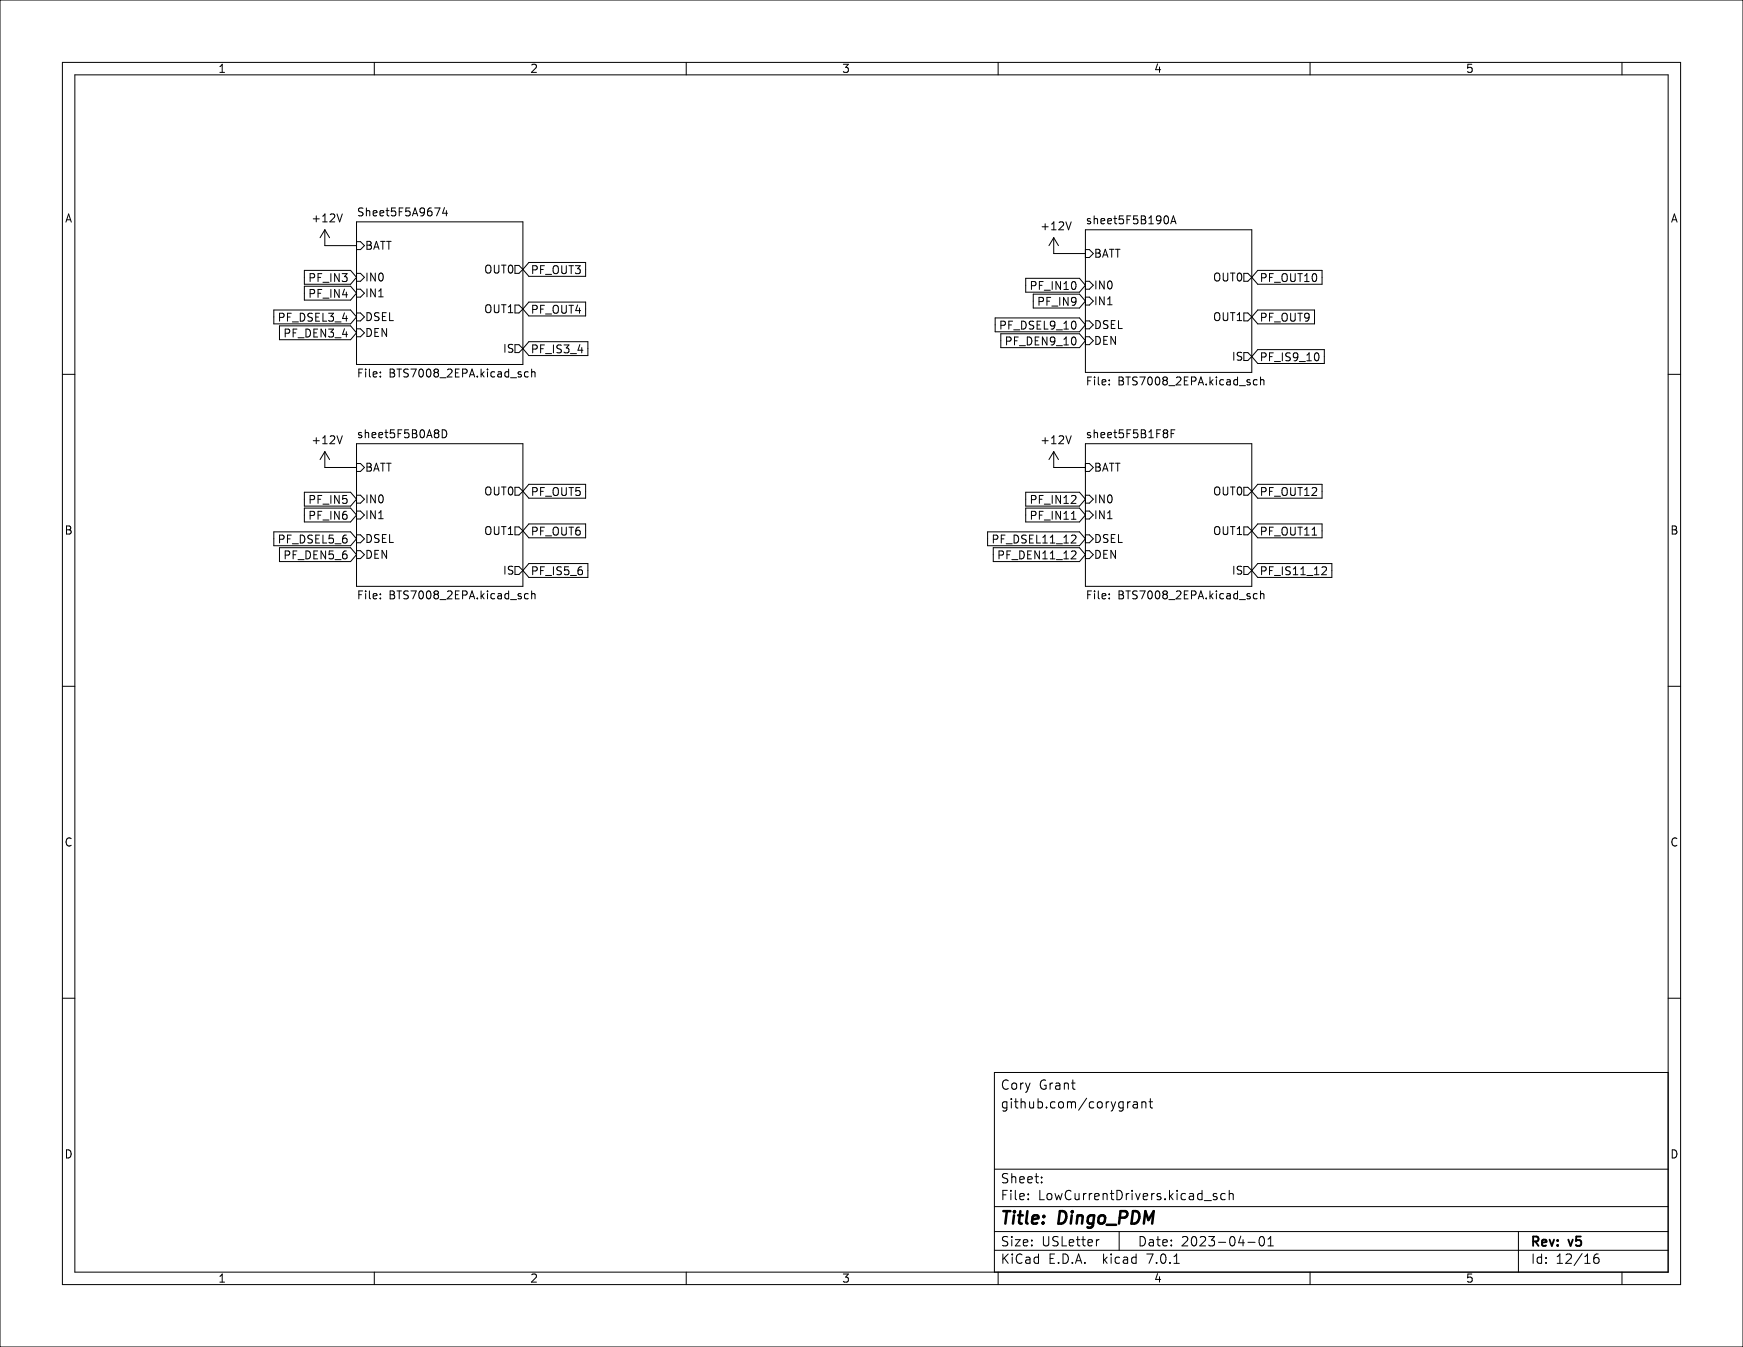
[picture p229: page 12]

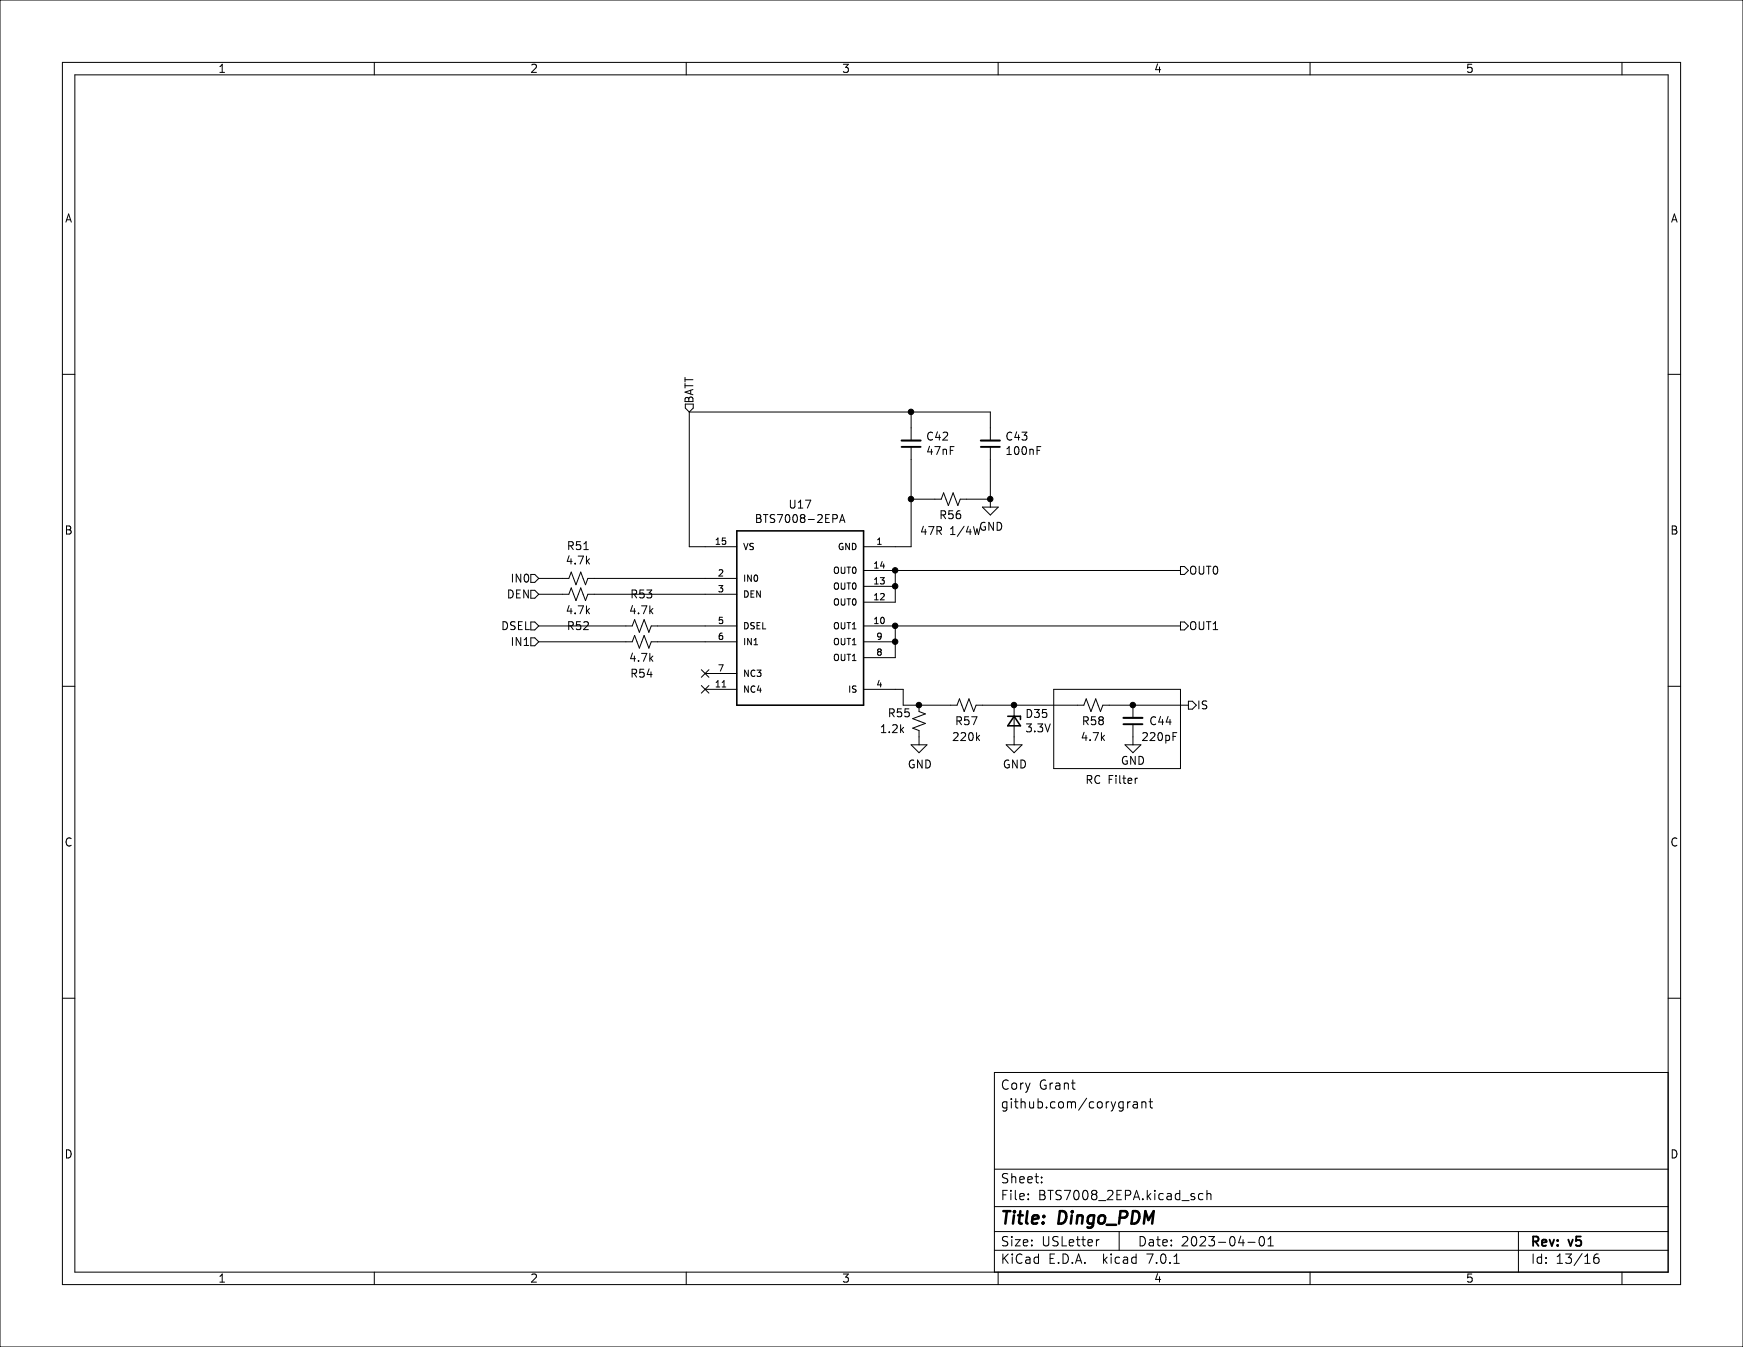
[picture p230: page 13]

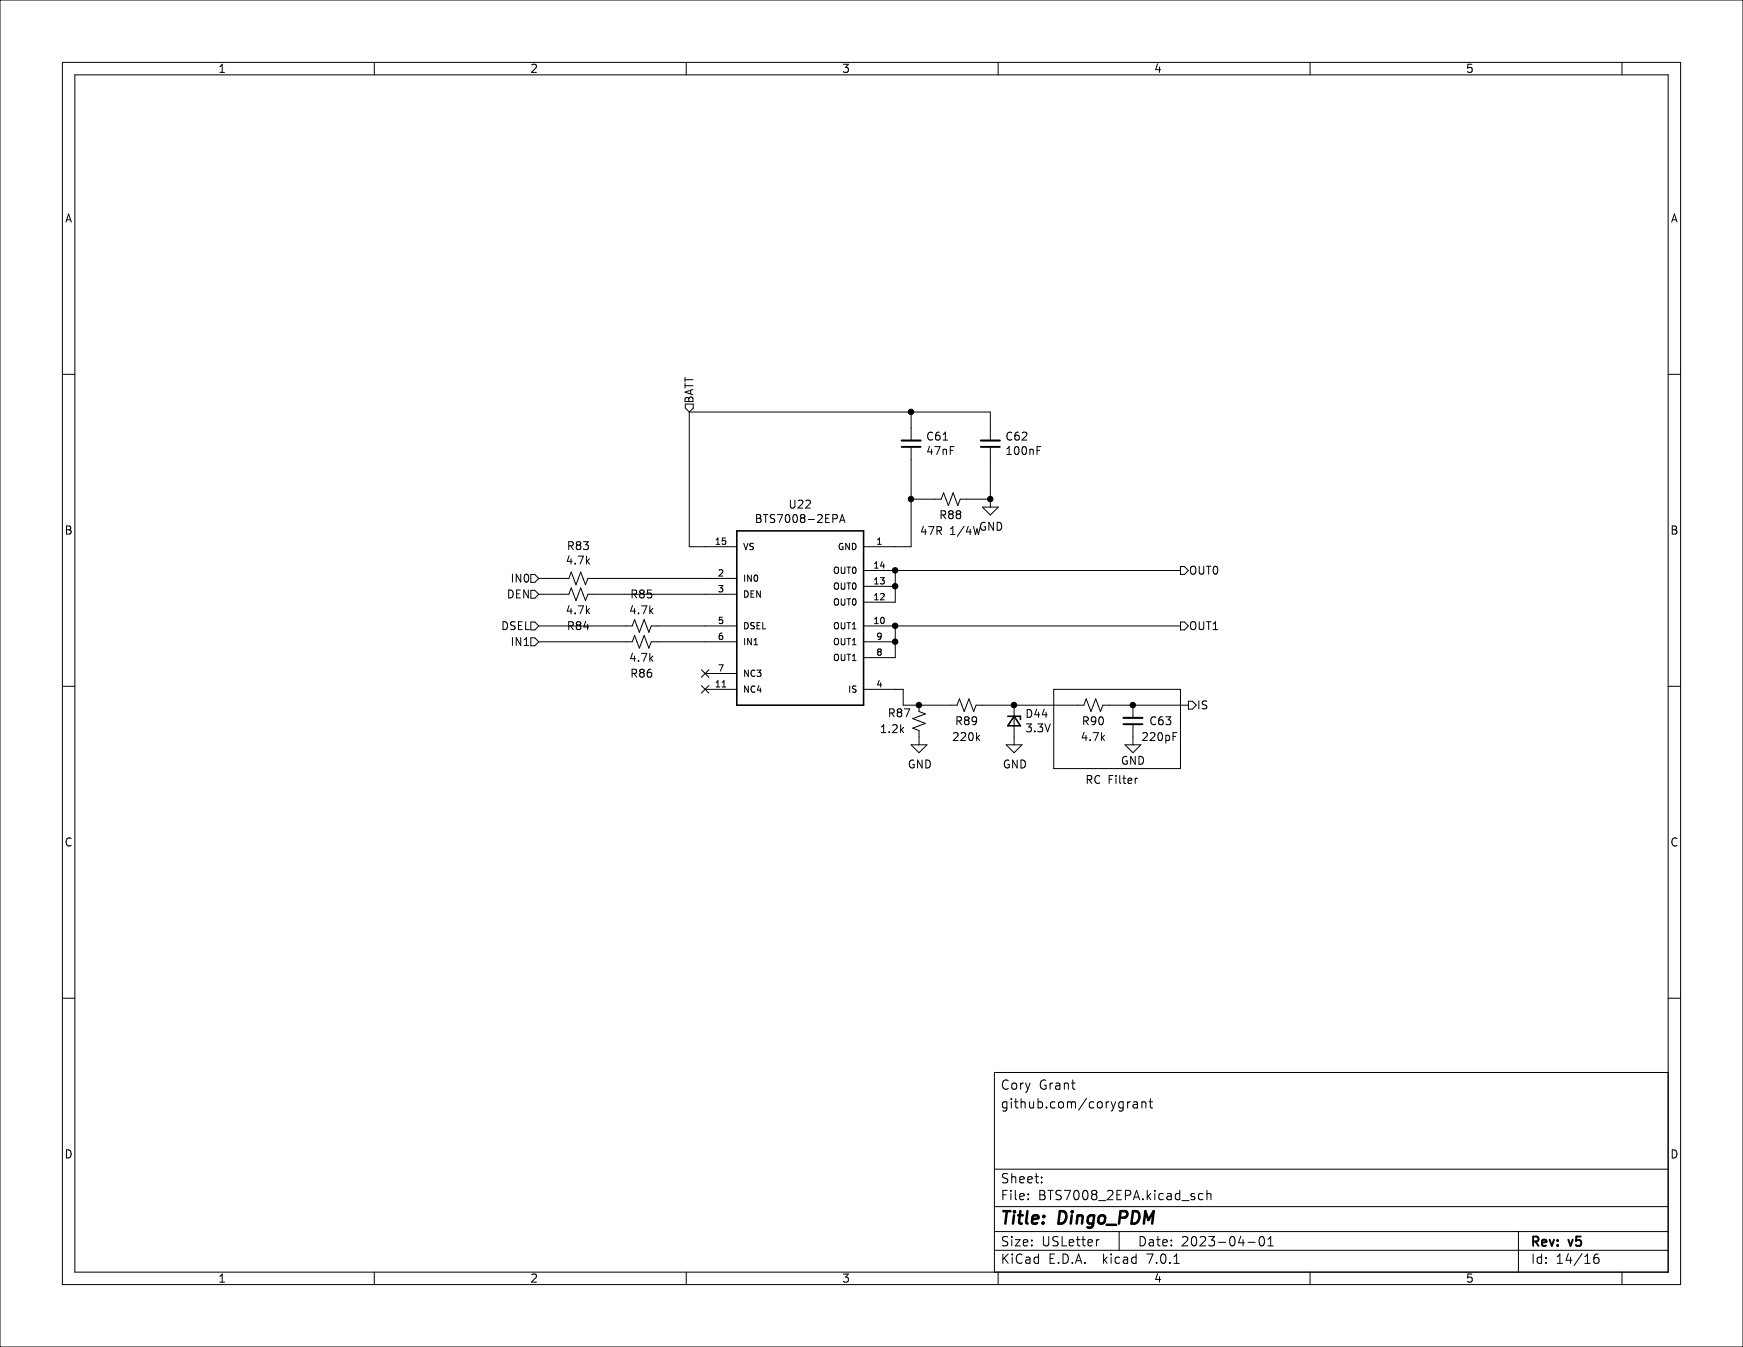
[picture p231: page 14]

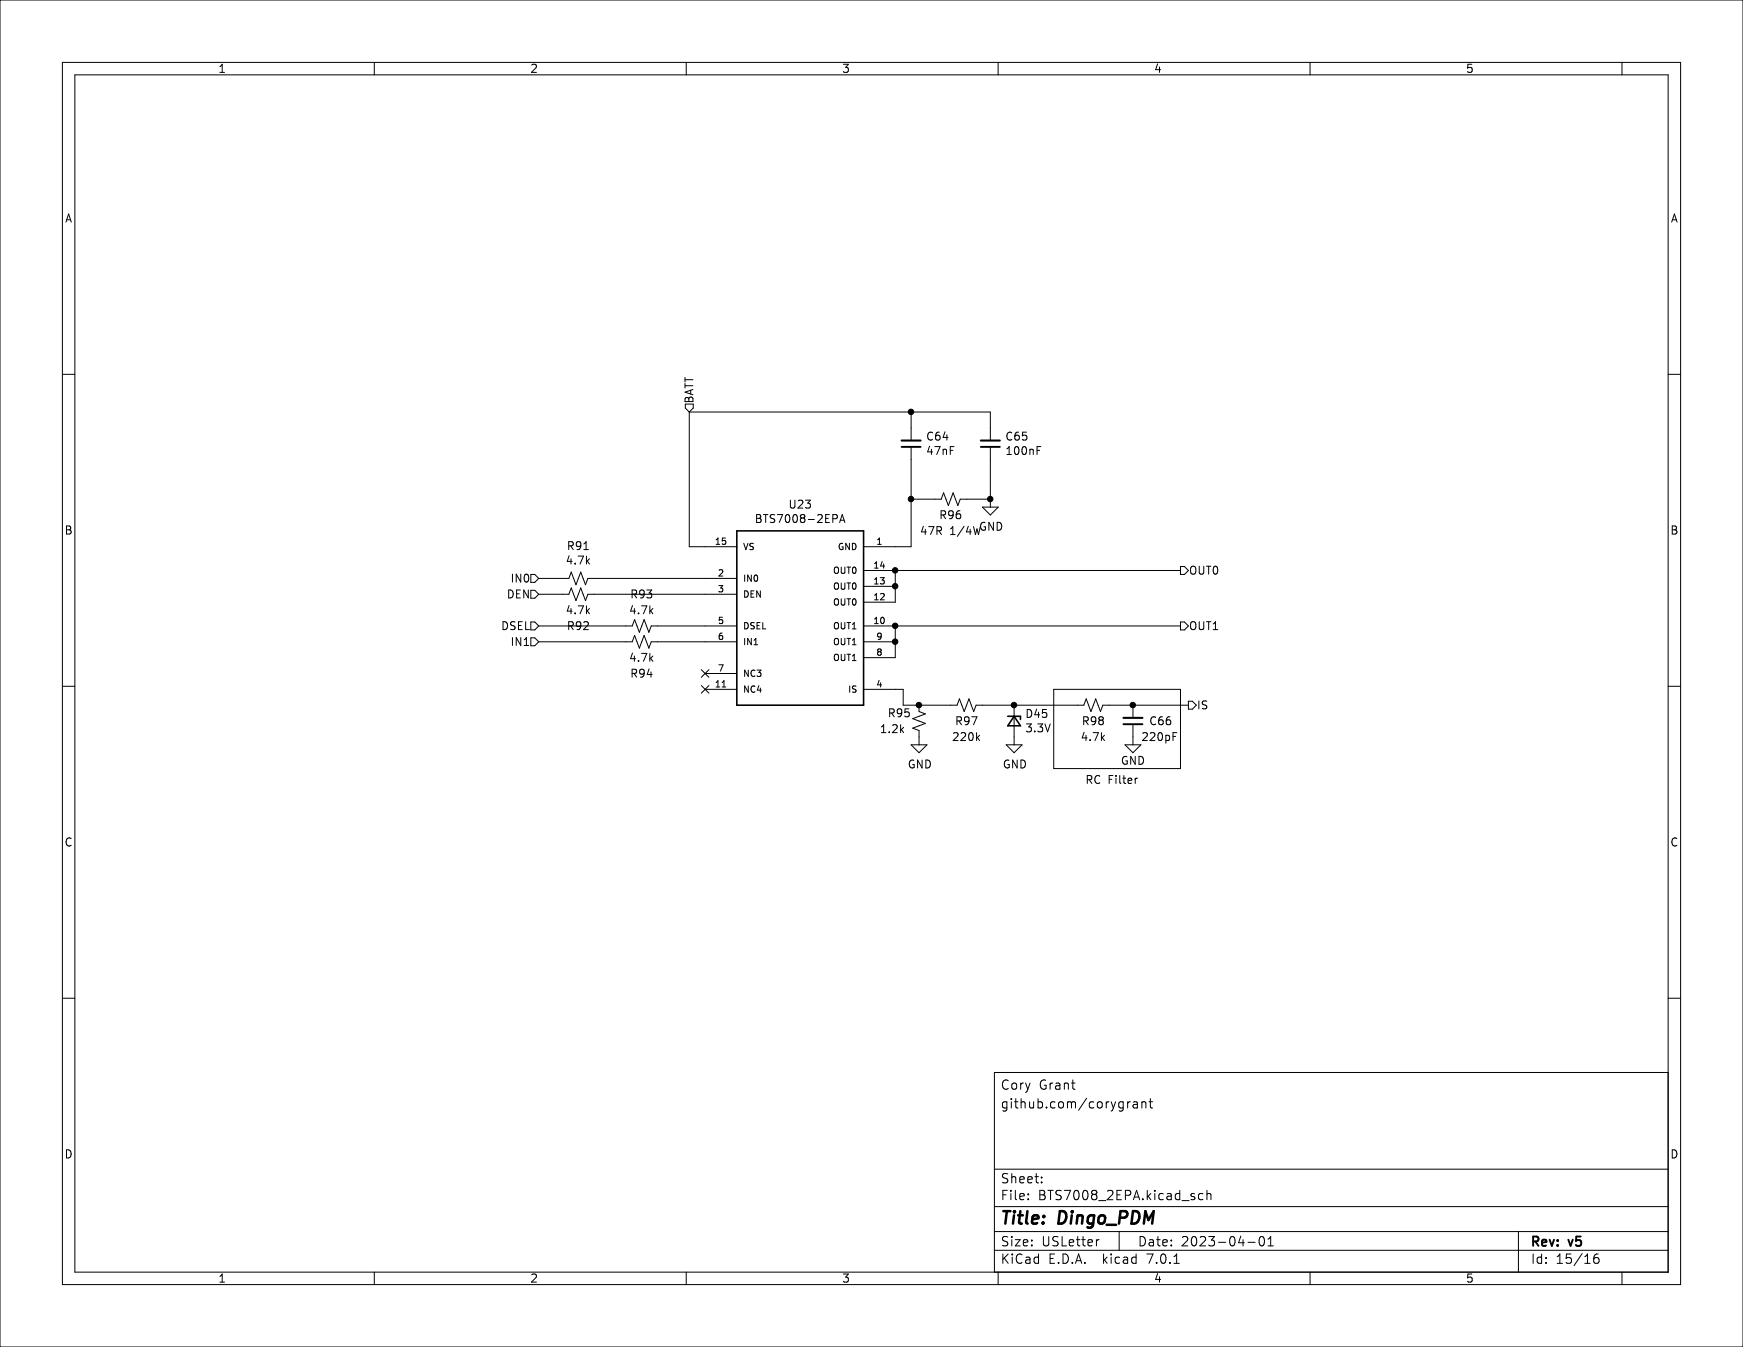
[picture p232: page 15]

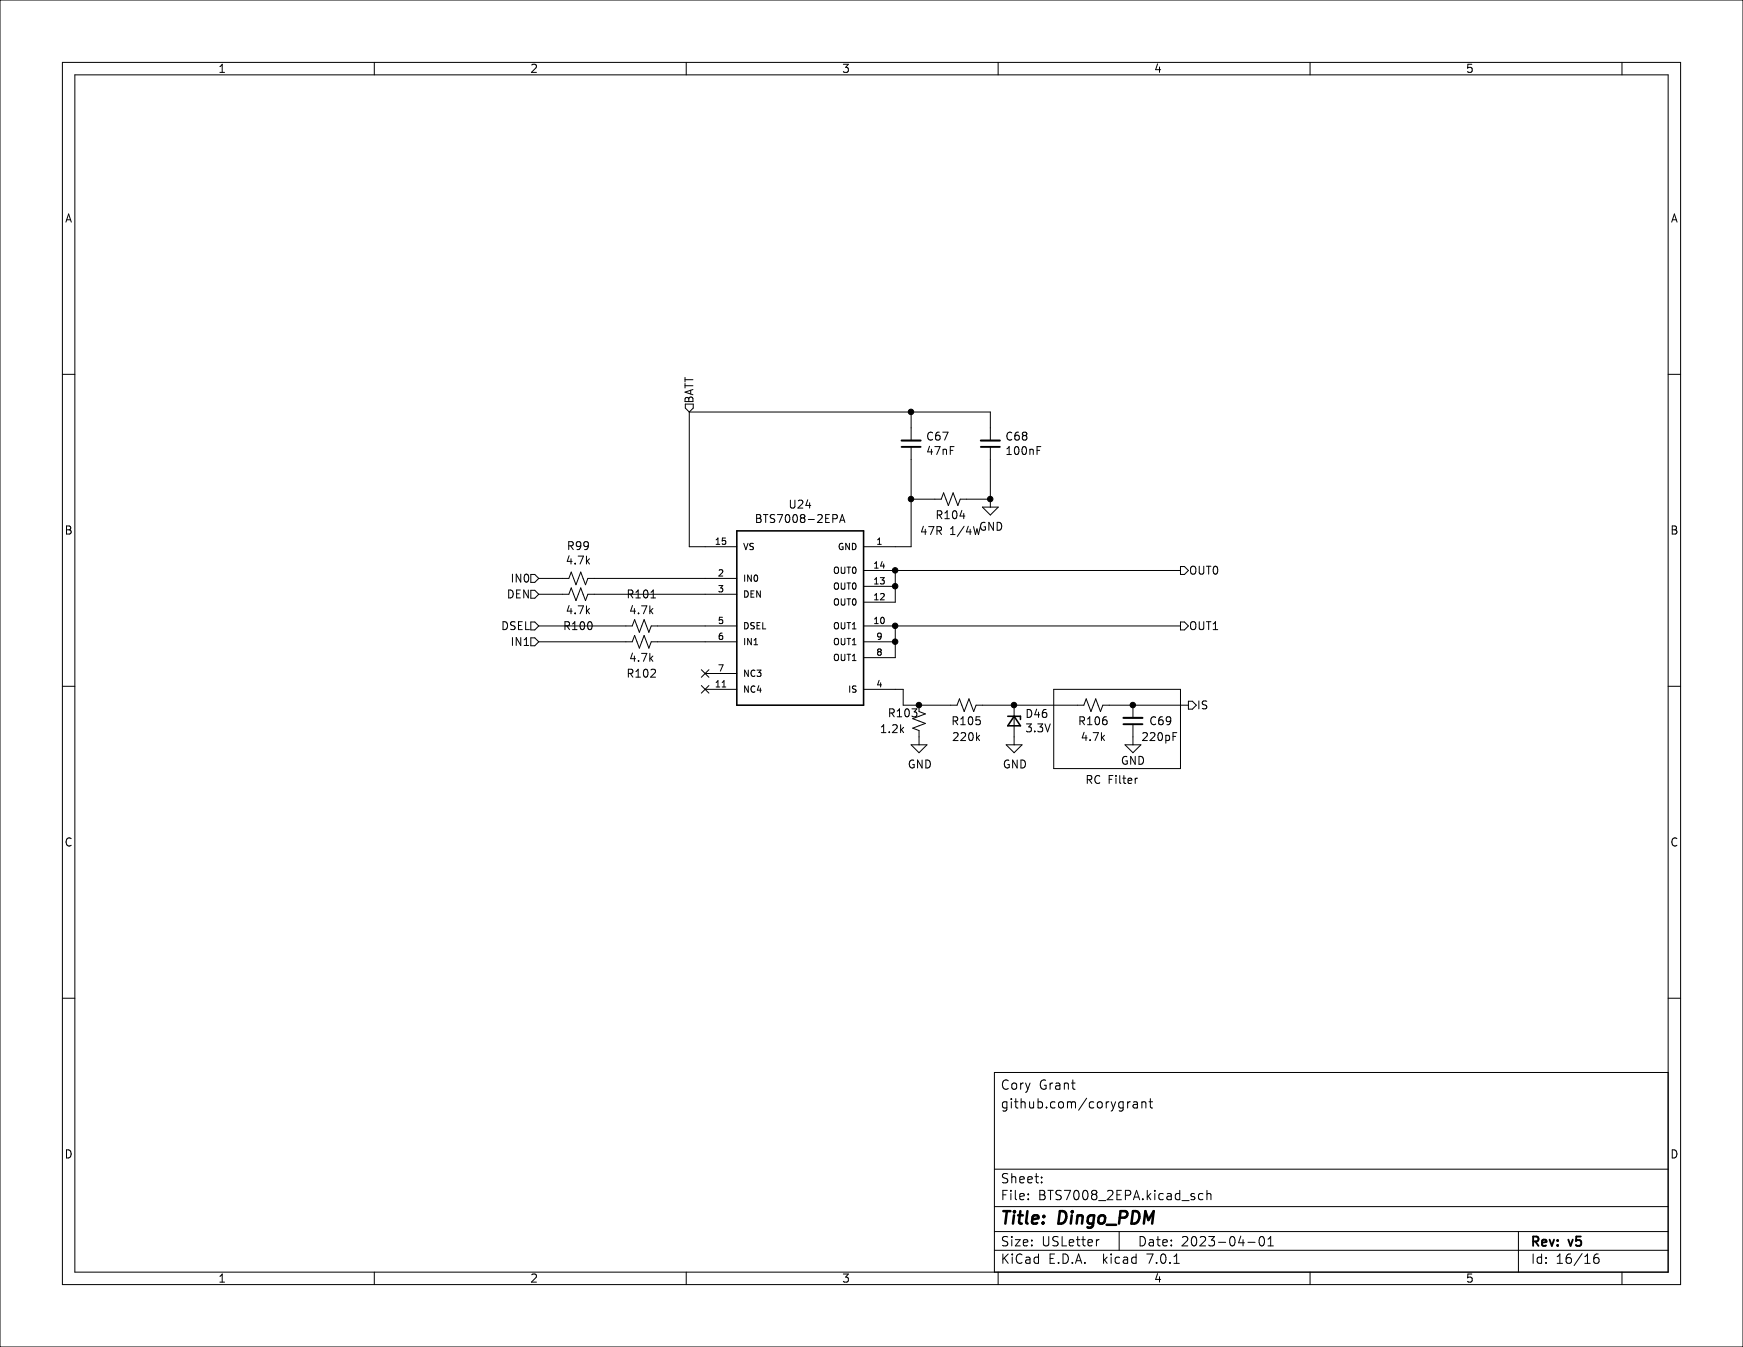
[picture p233: page 16]
