corygrant/dingoPDM/Export/V5/DingoPDM_HW_V5_Dark.pdf

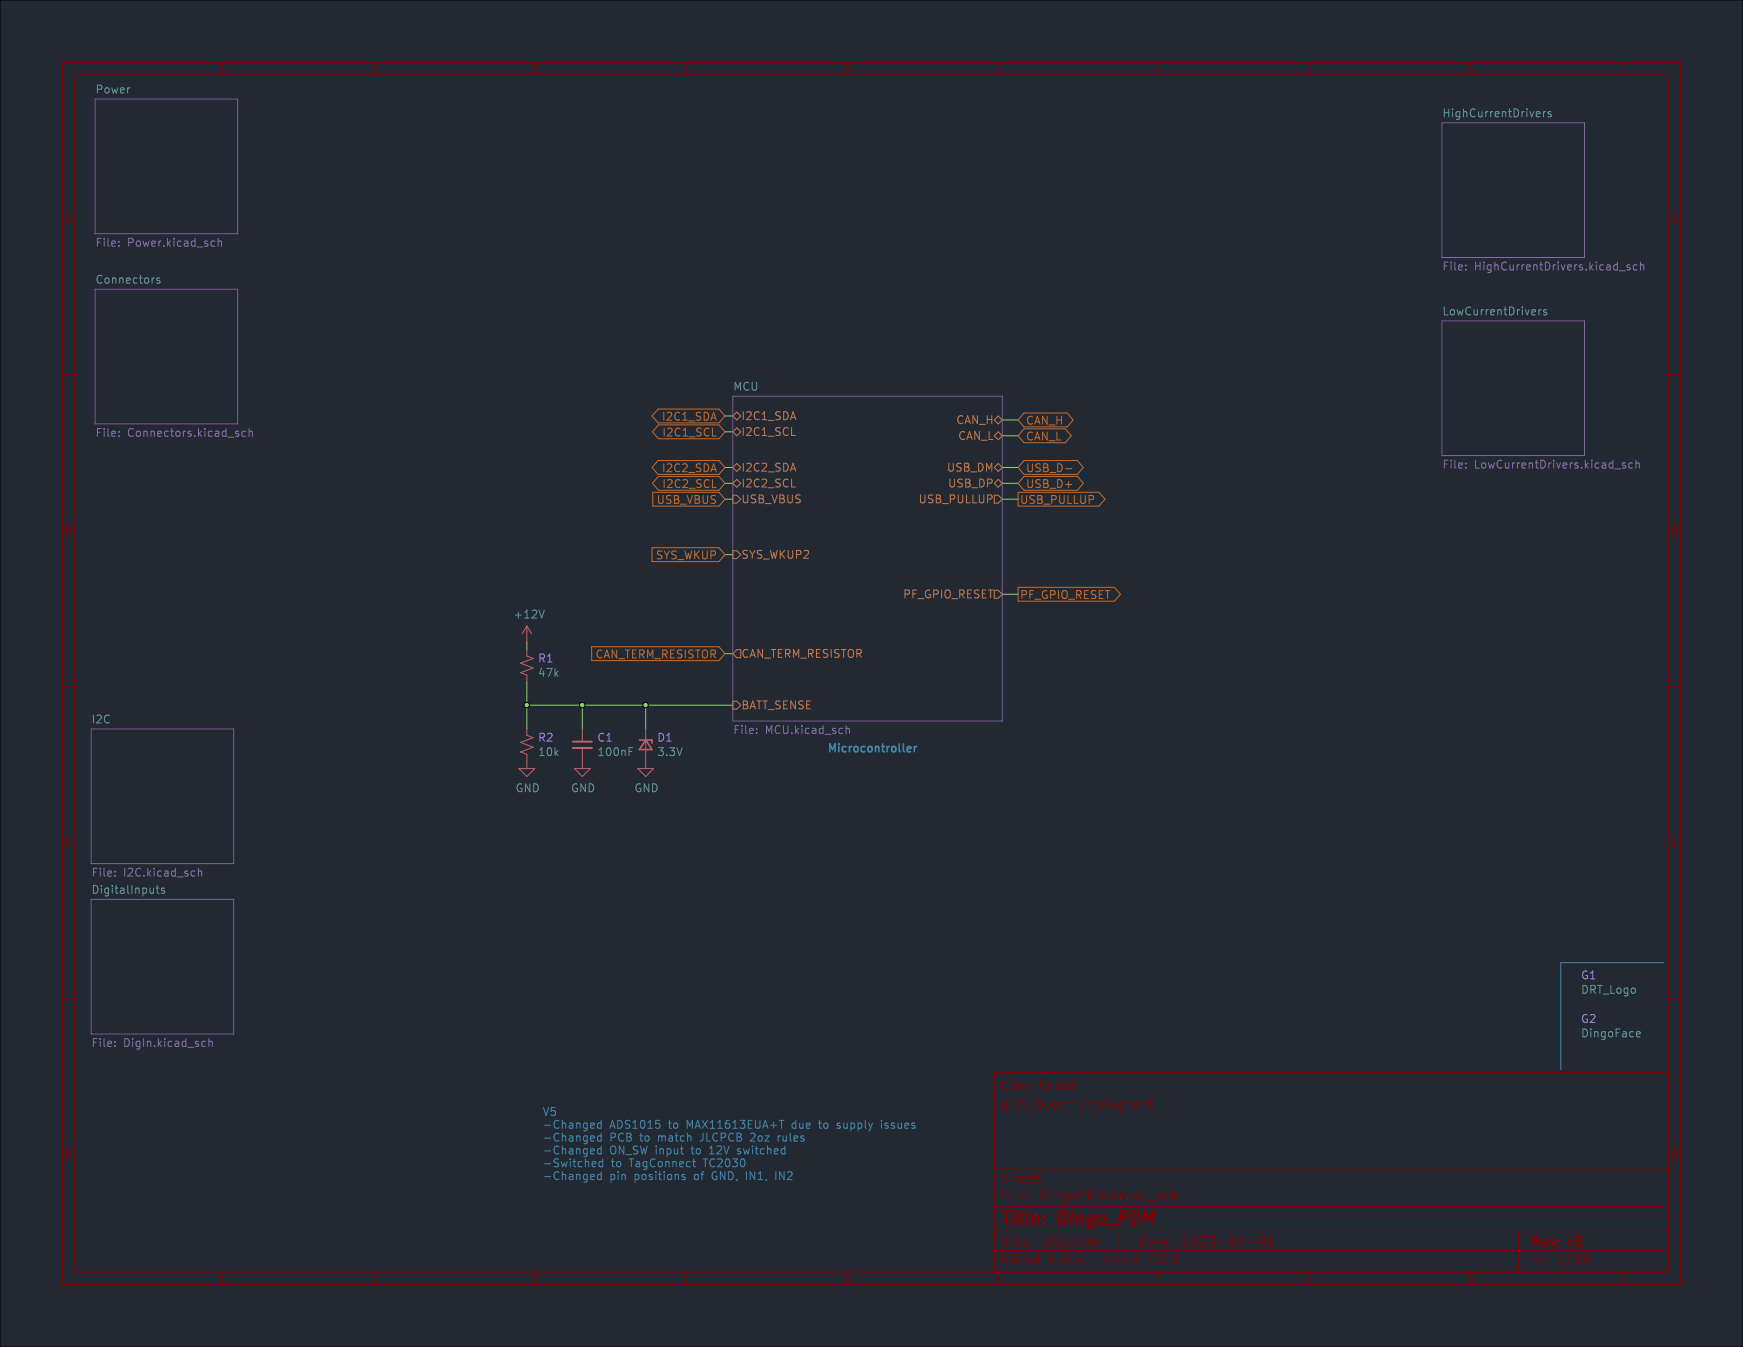
[picture p234: page 1]

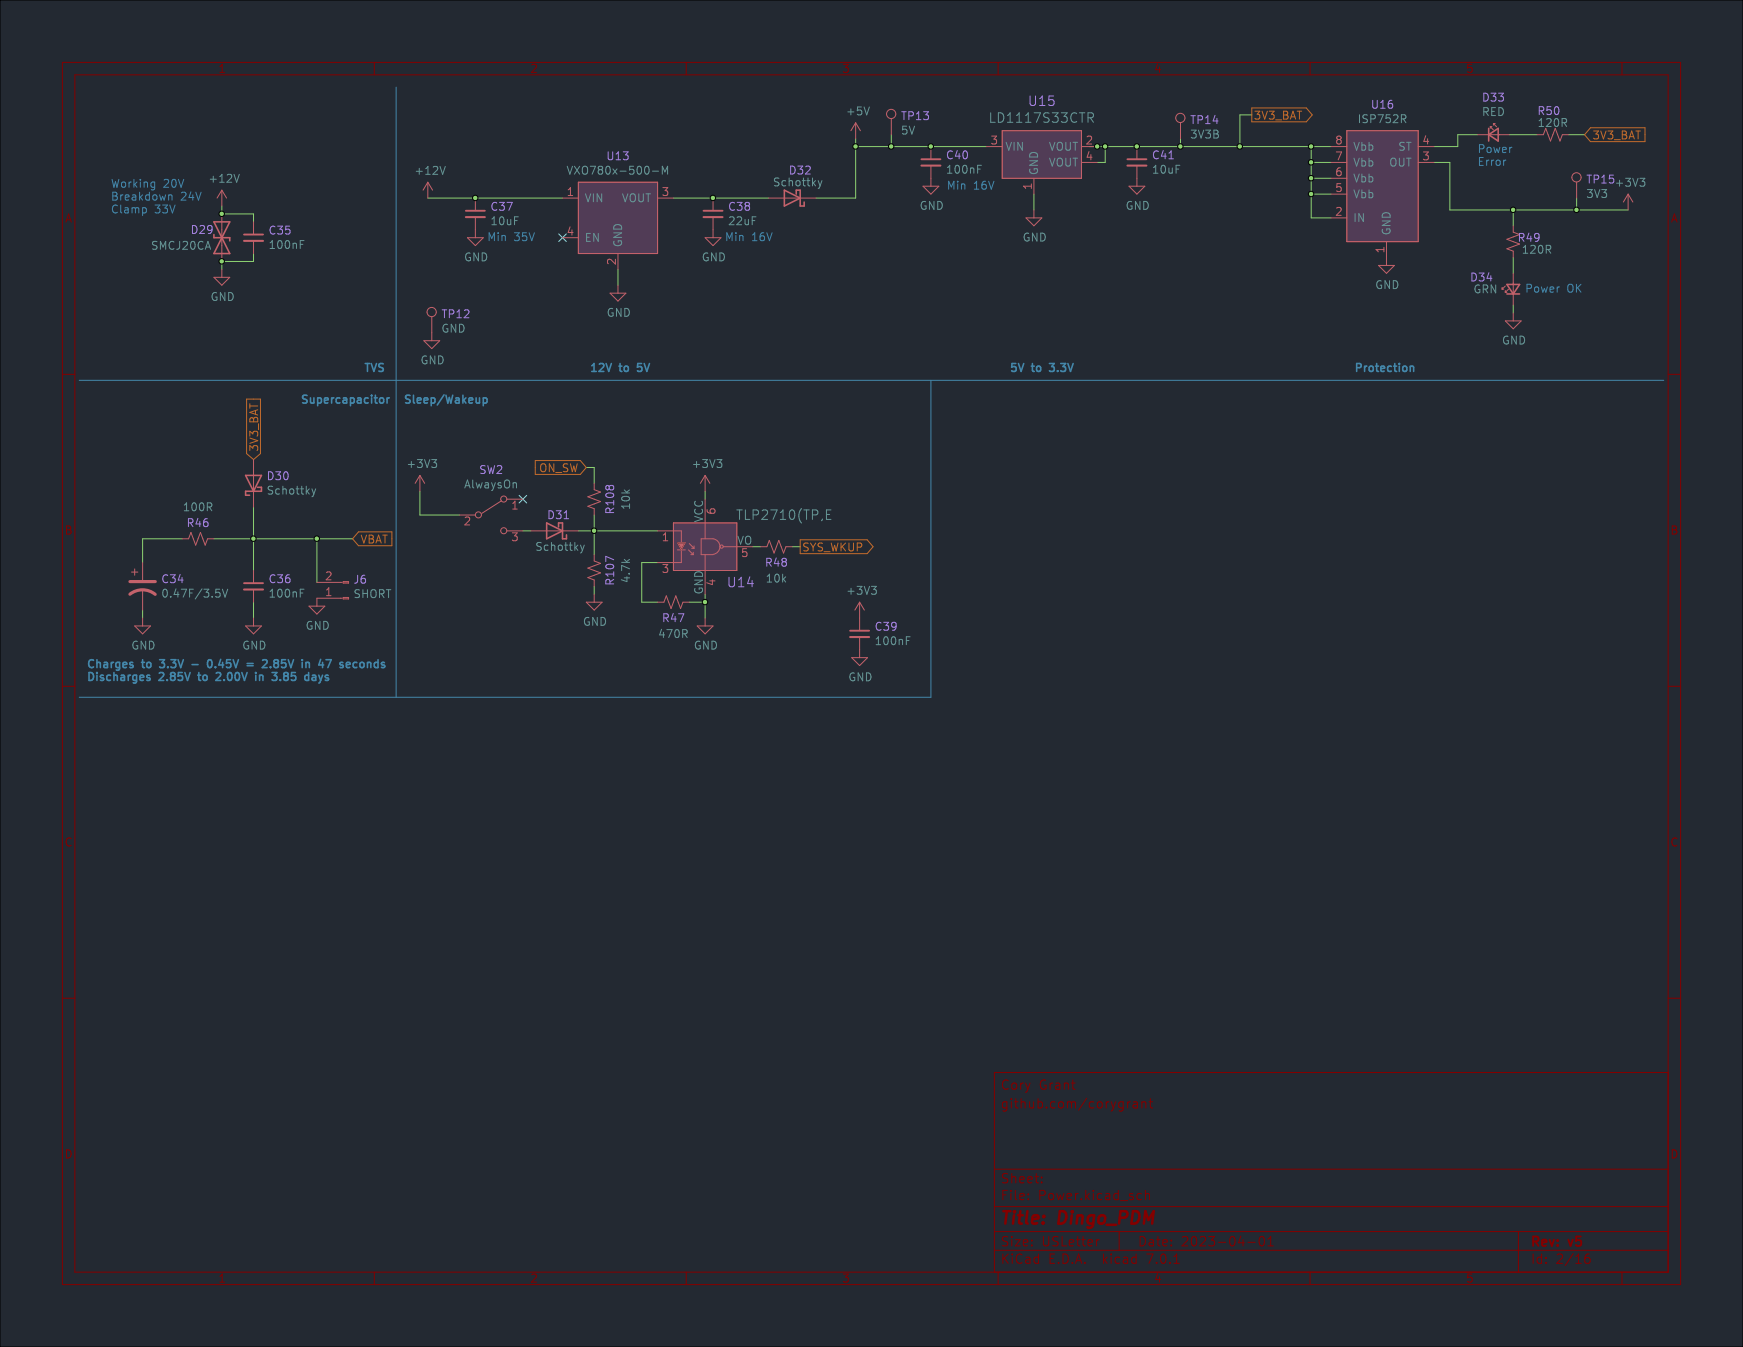
[picture p235: page 2]

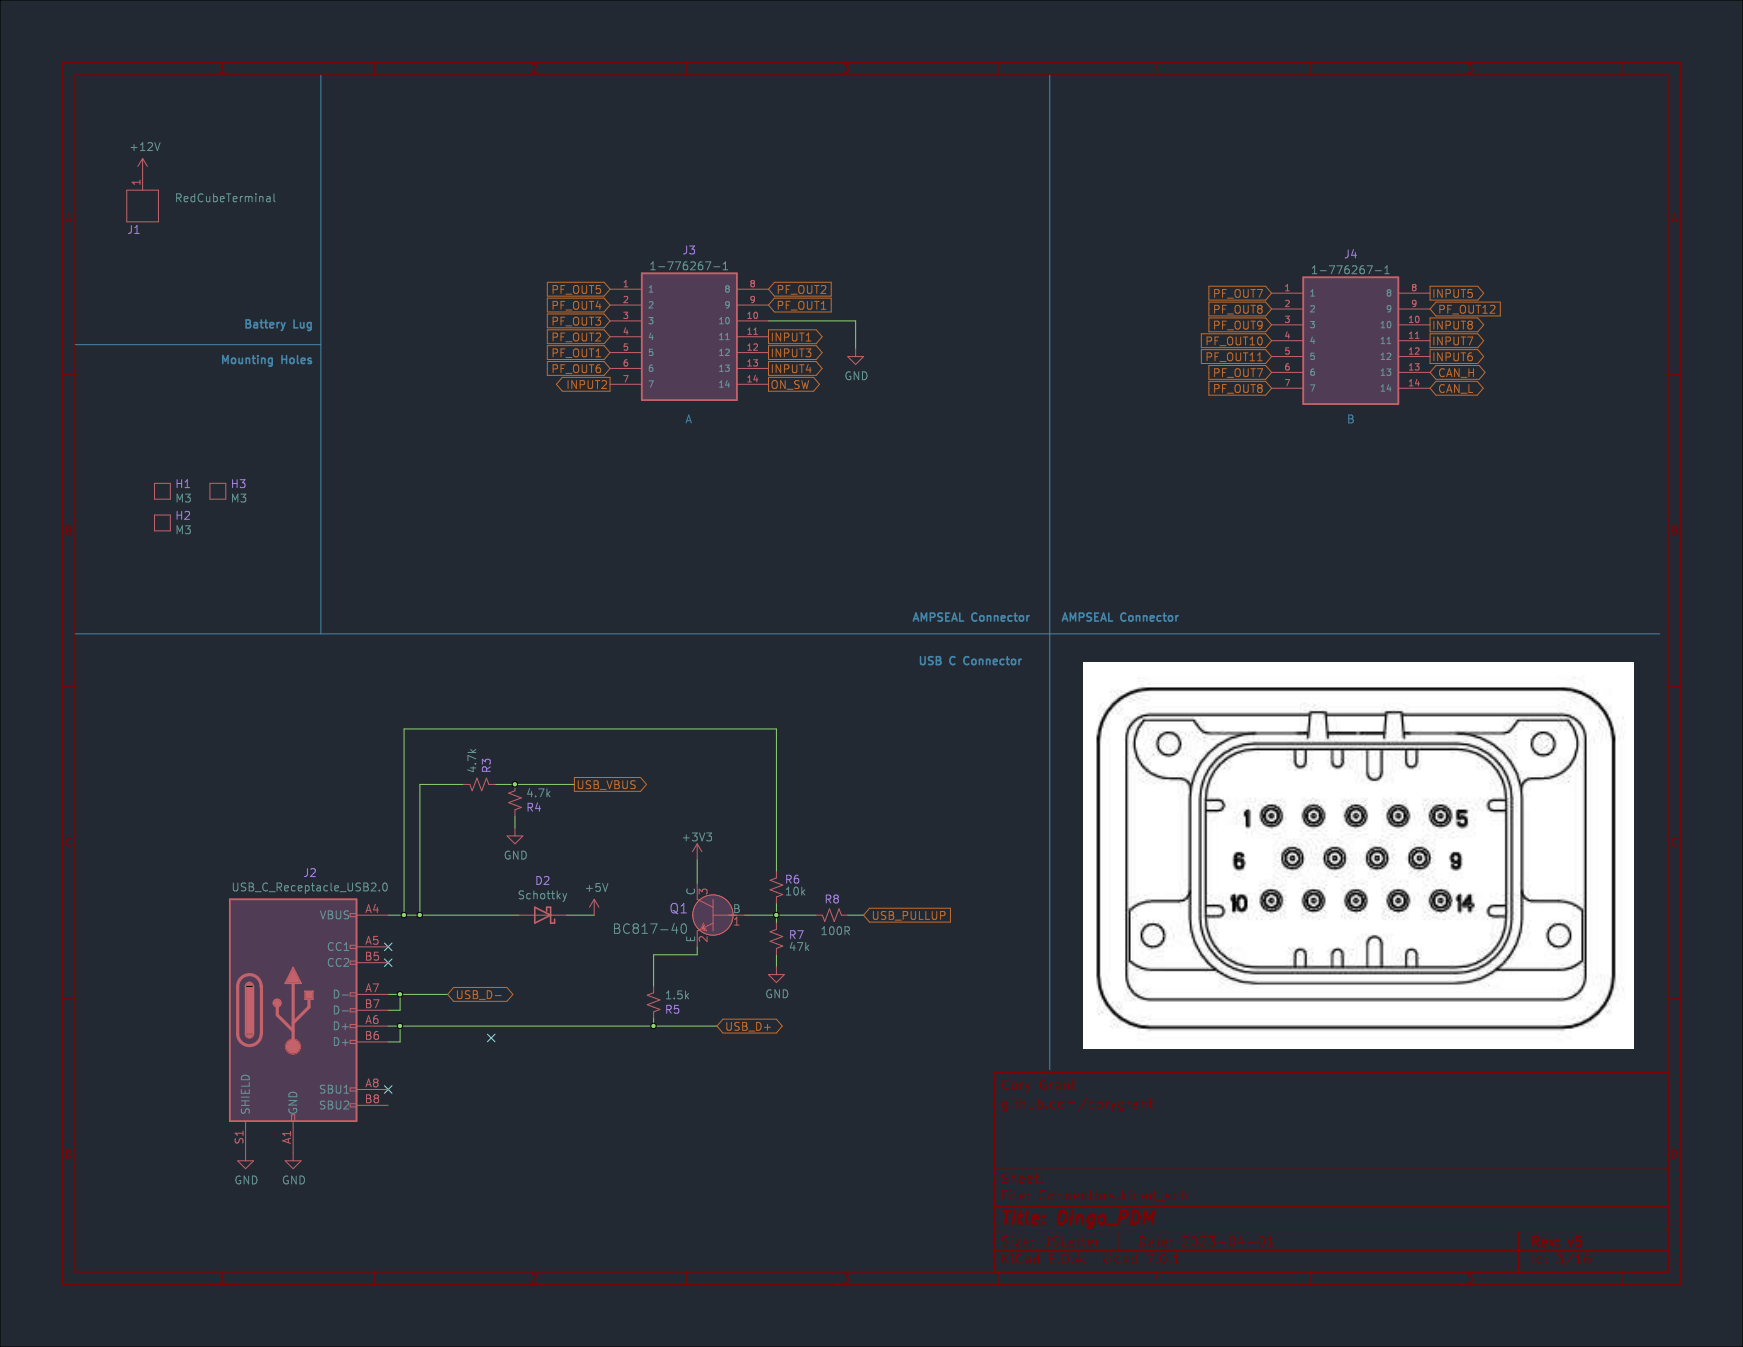
[picture p236: page 3]

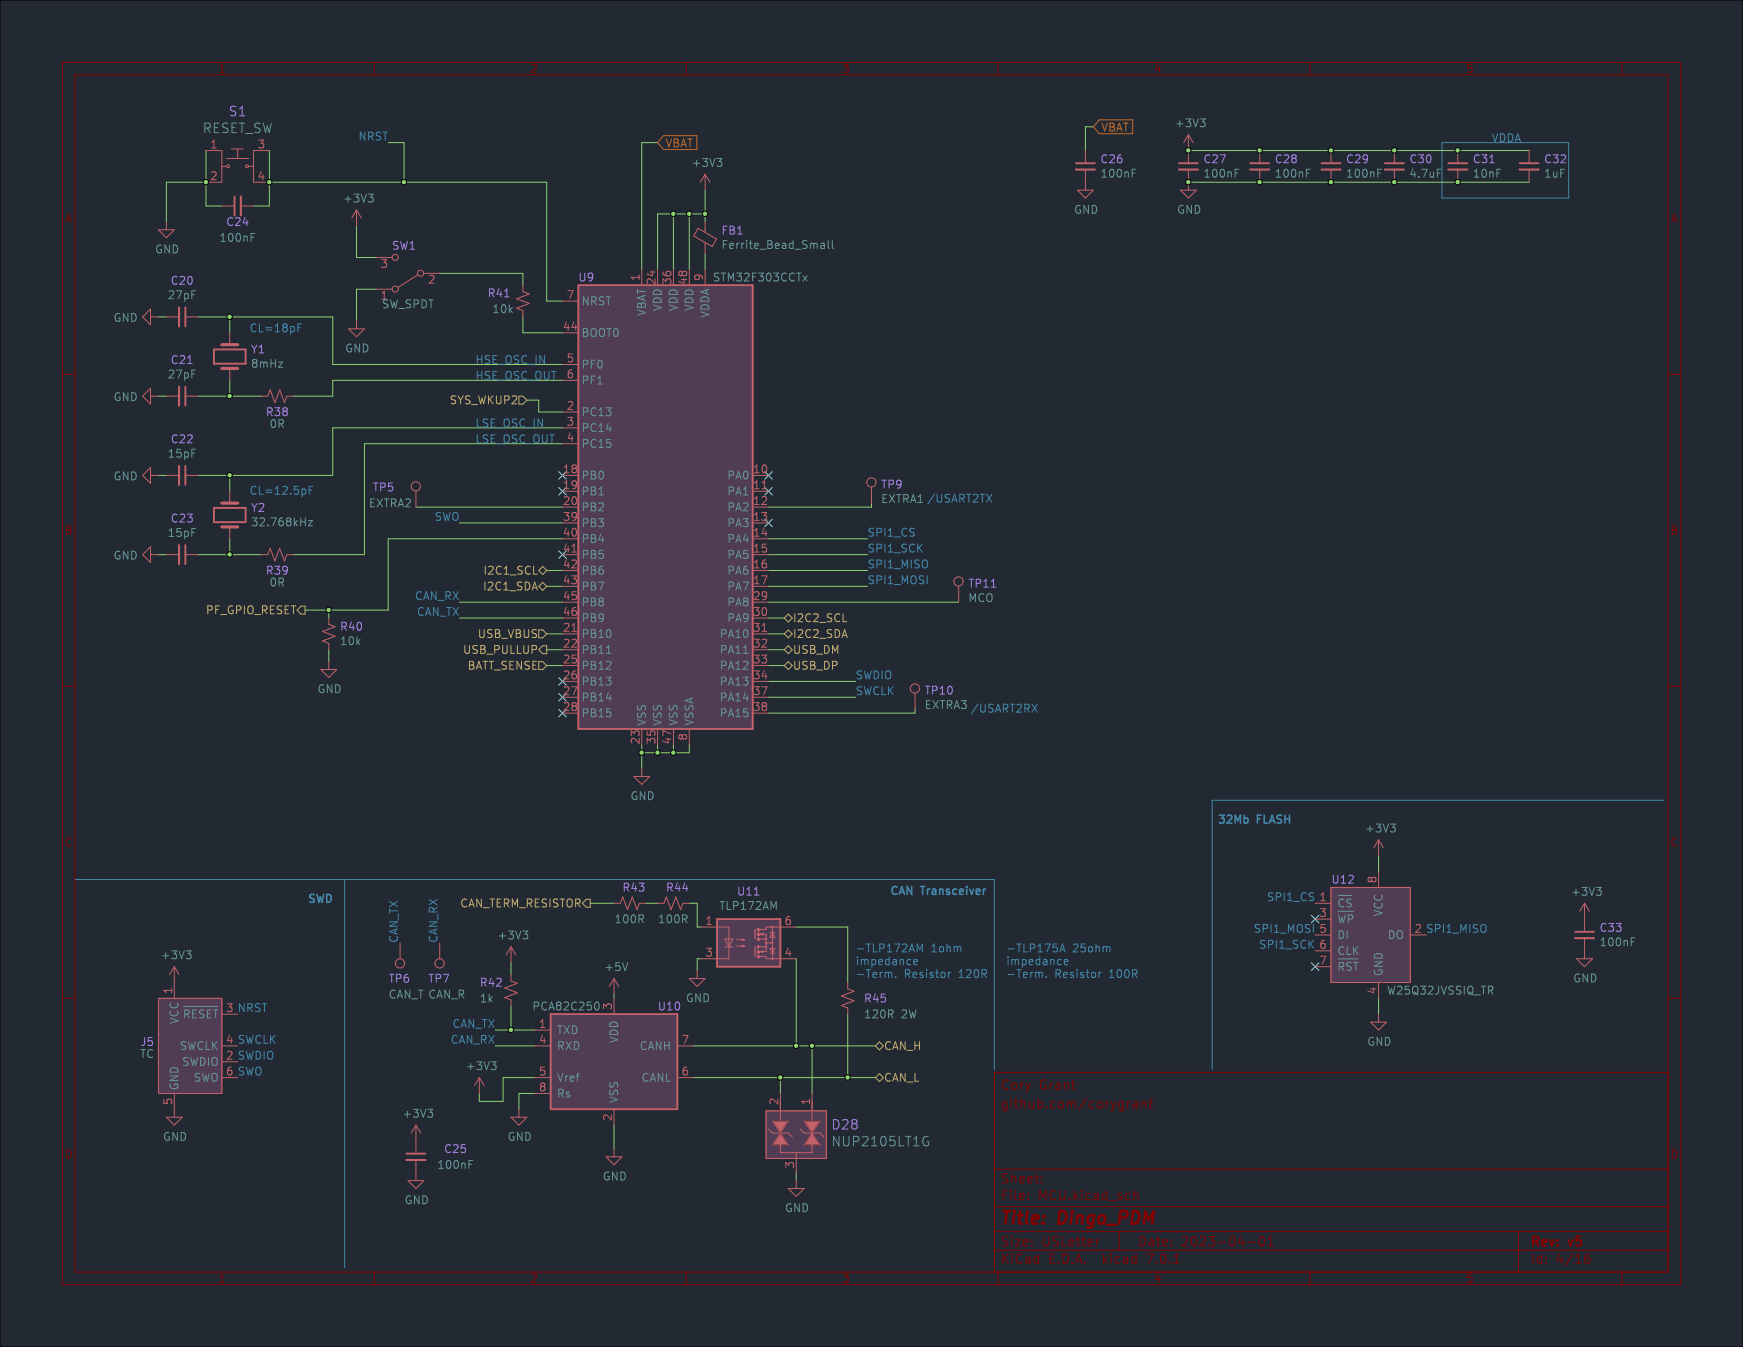
[picture p237: page 4]

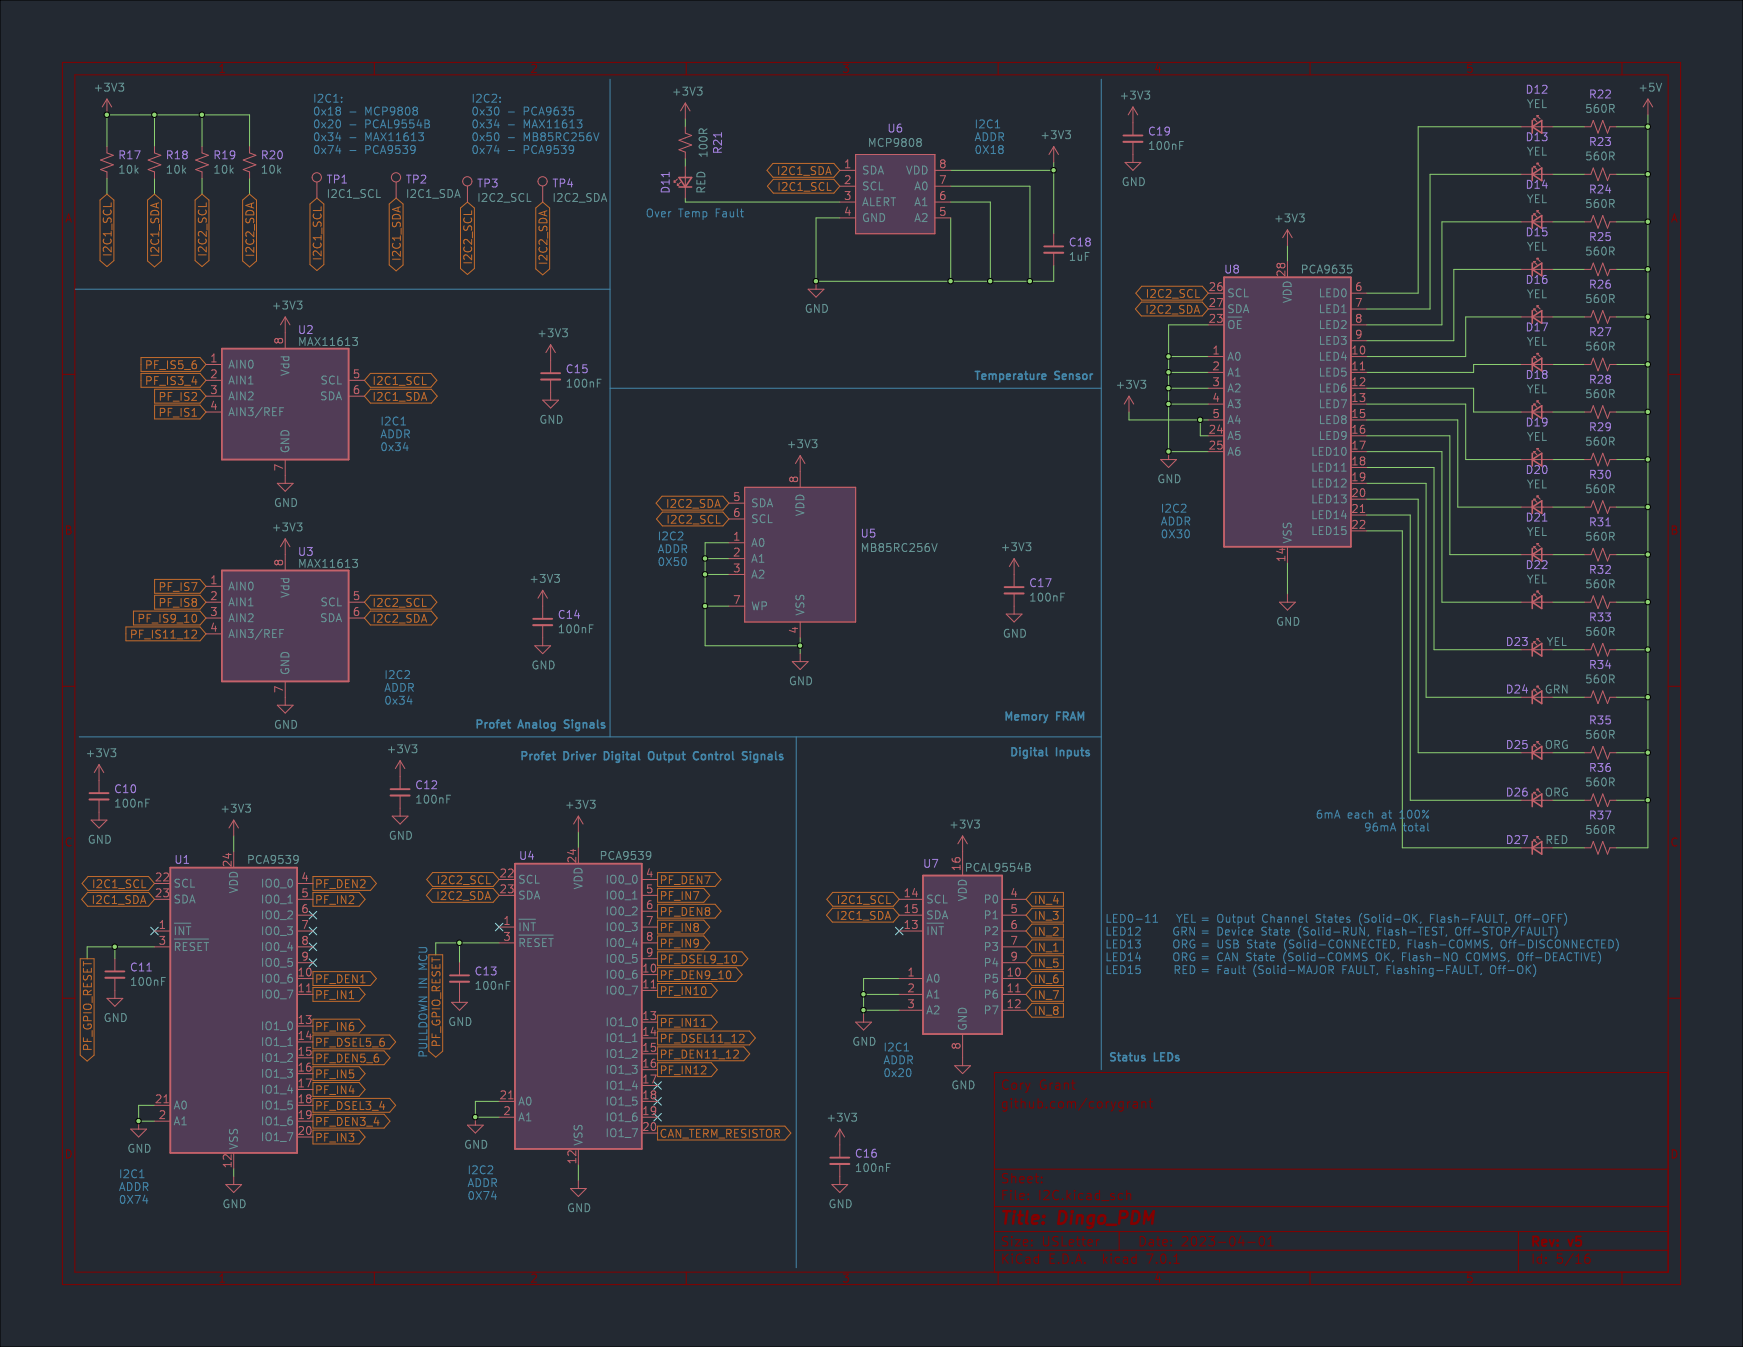
[picture p238: page 5]

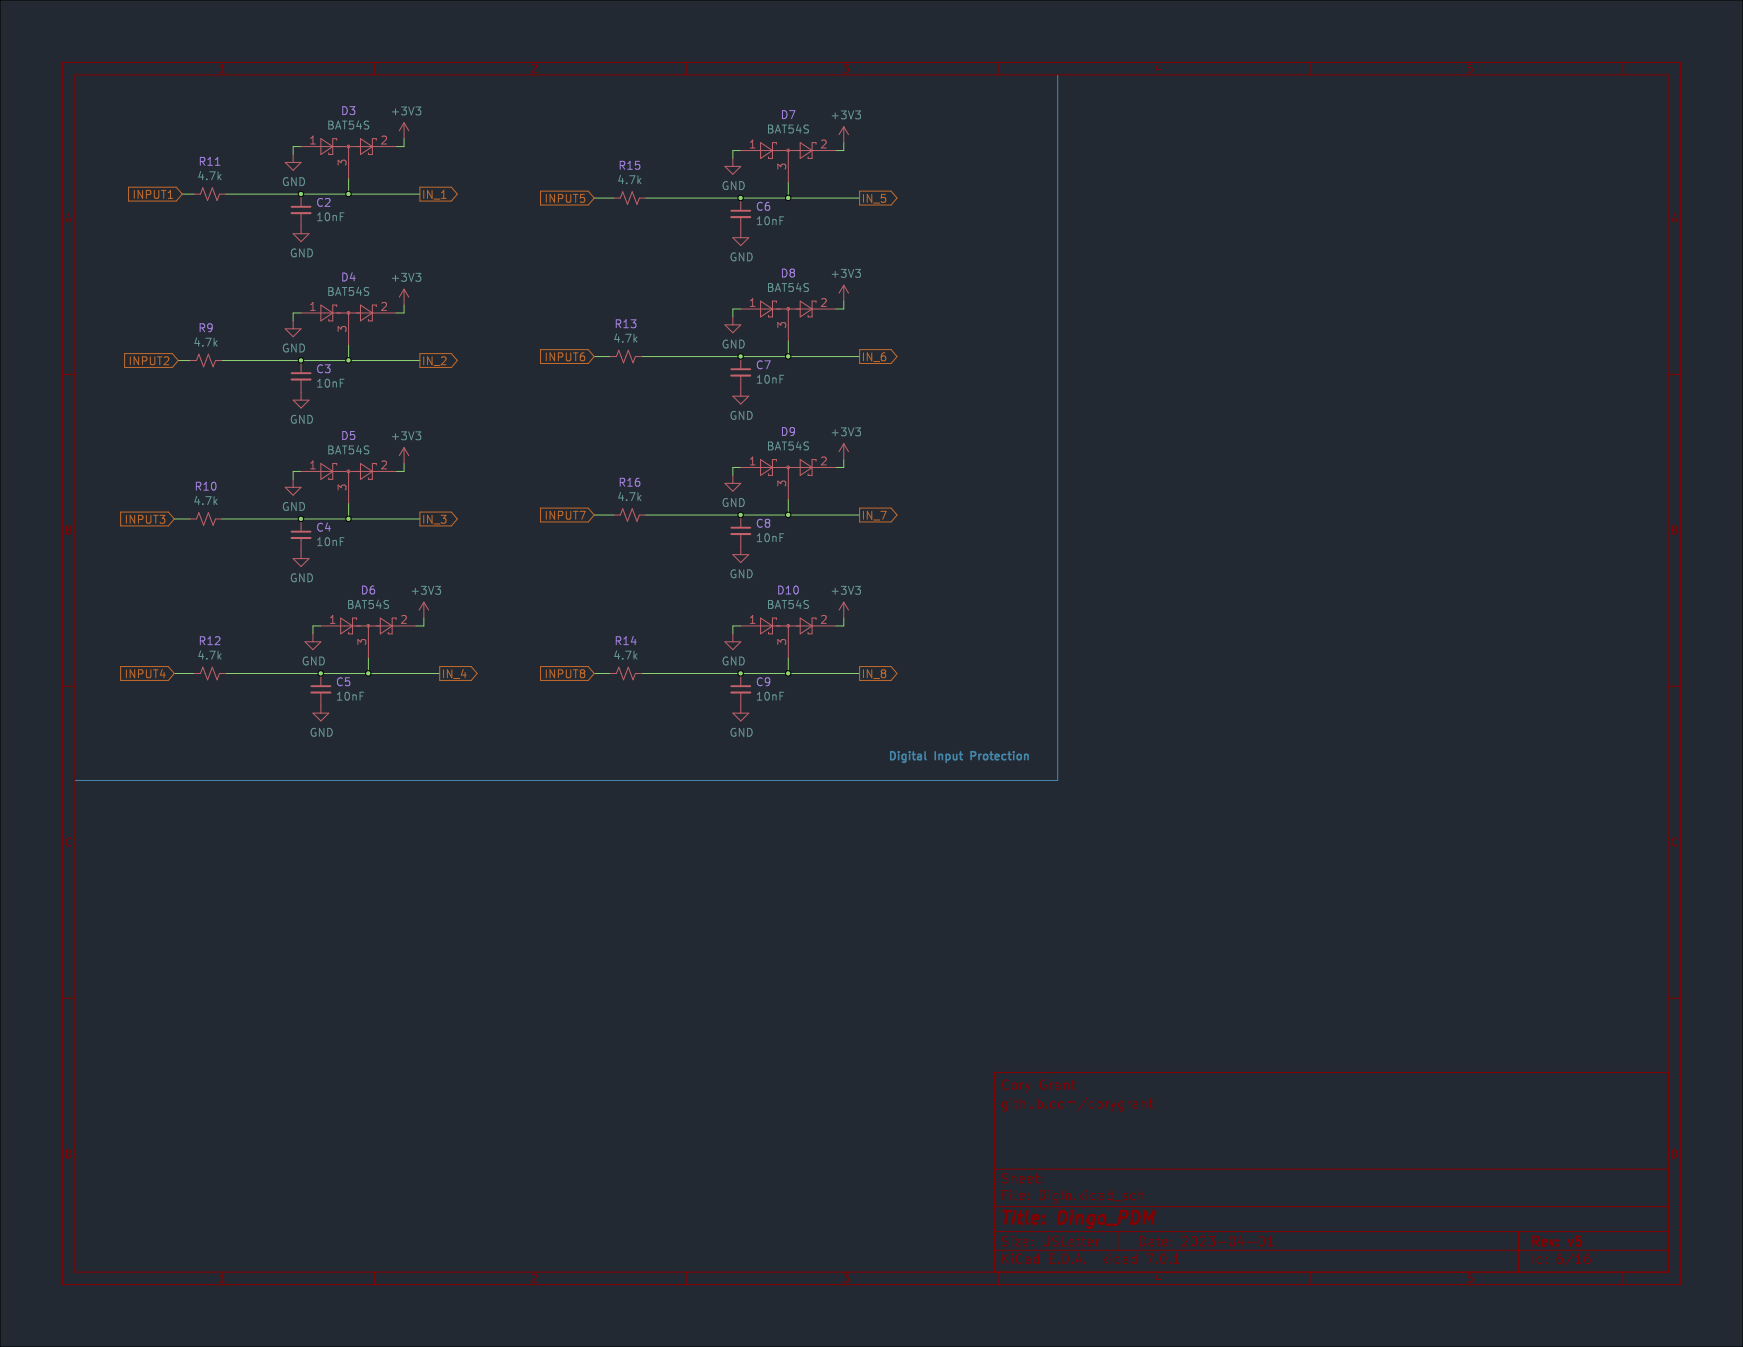
[picture p239: page 6]

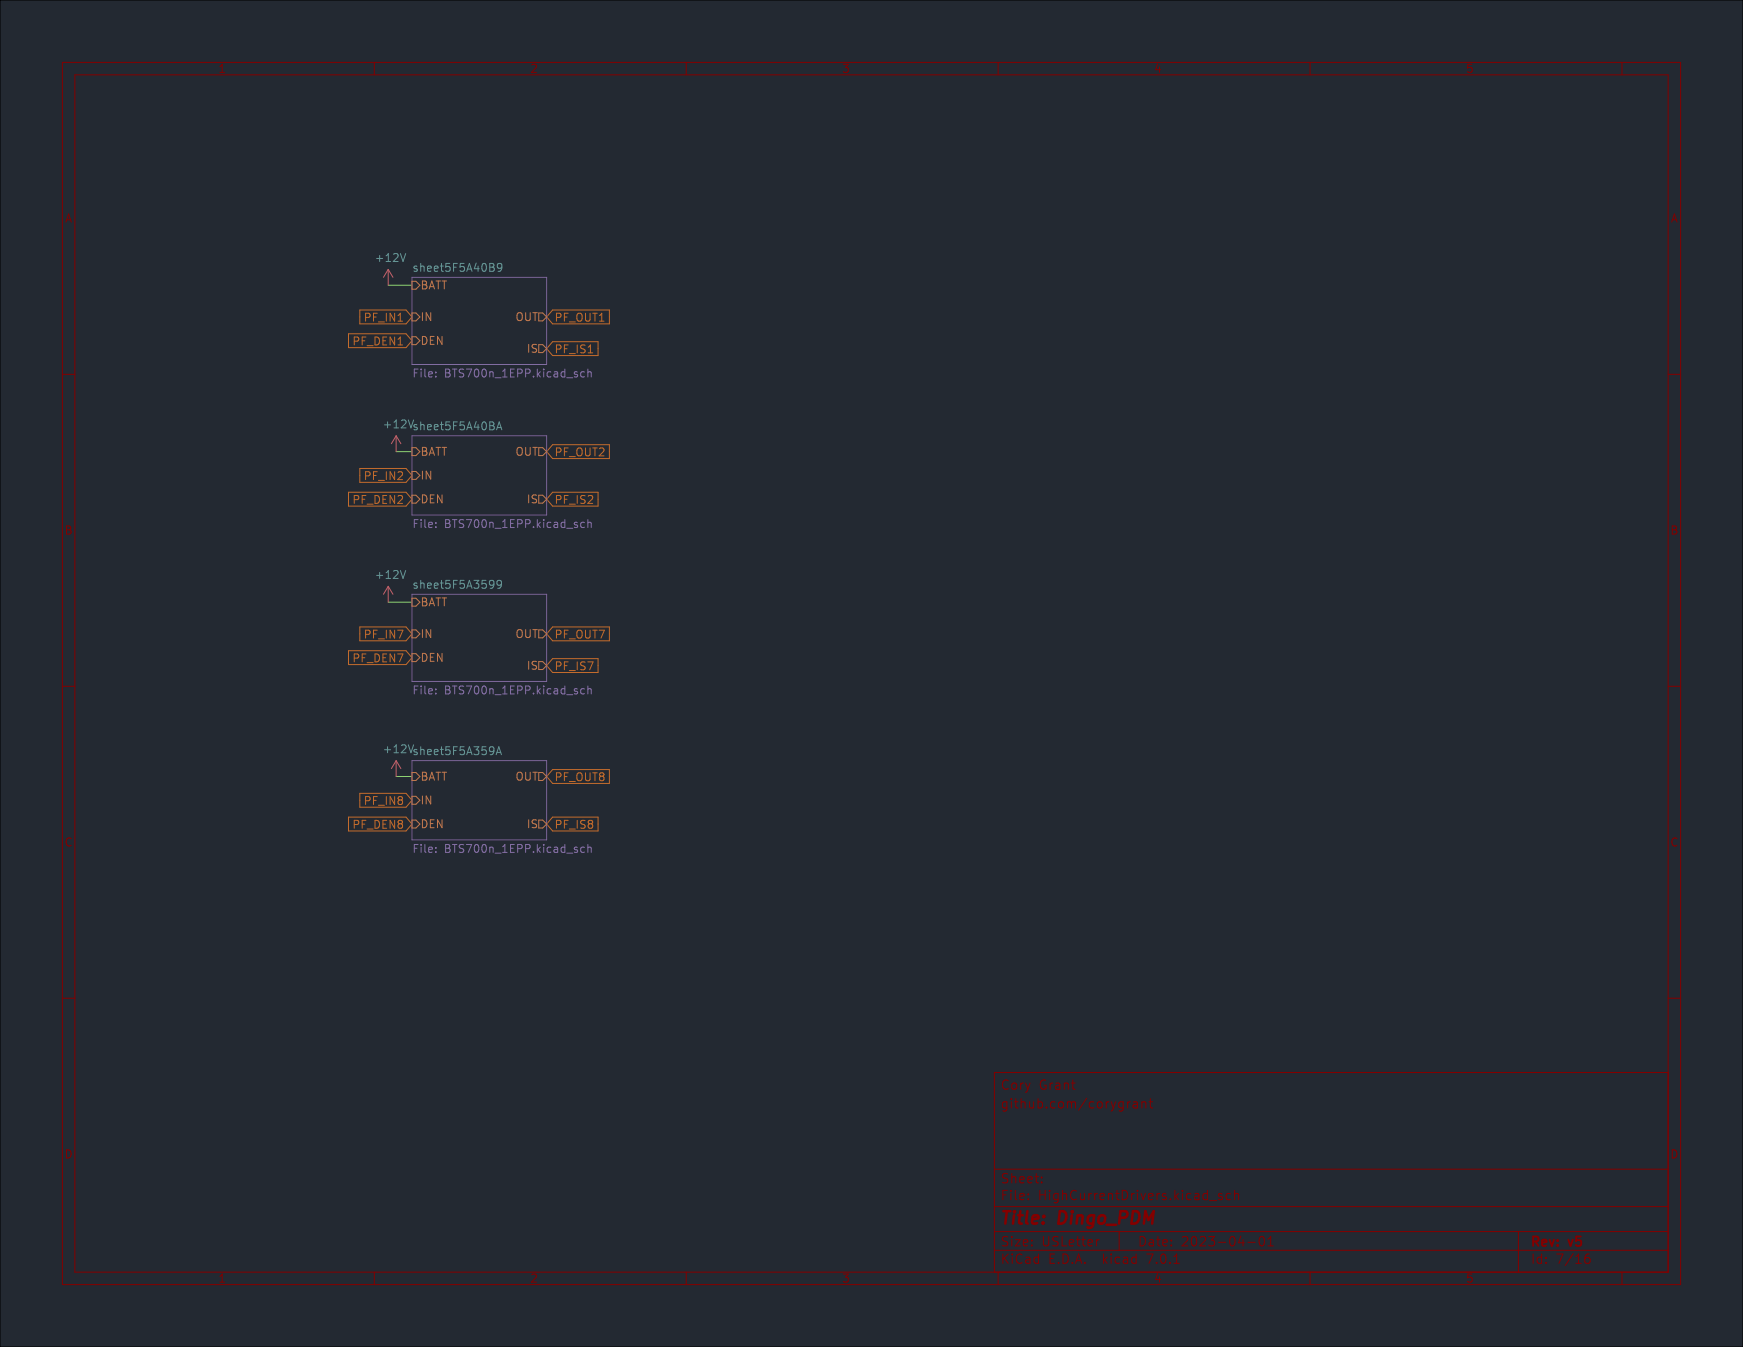
[picture p240: page 7]

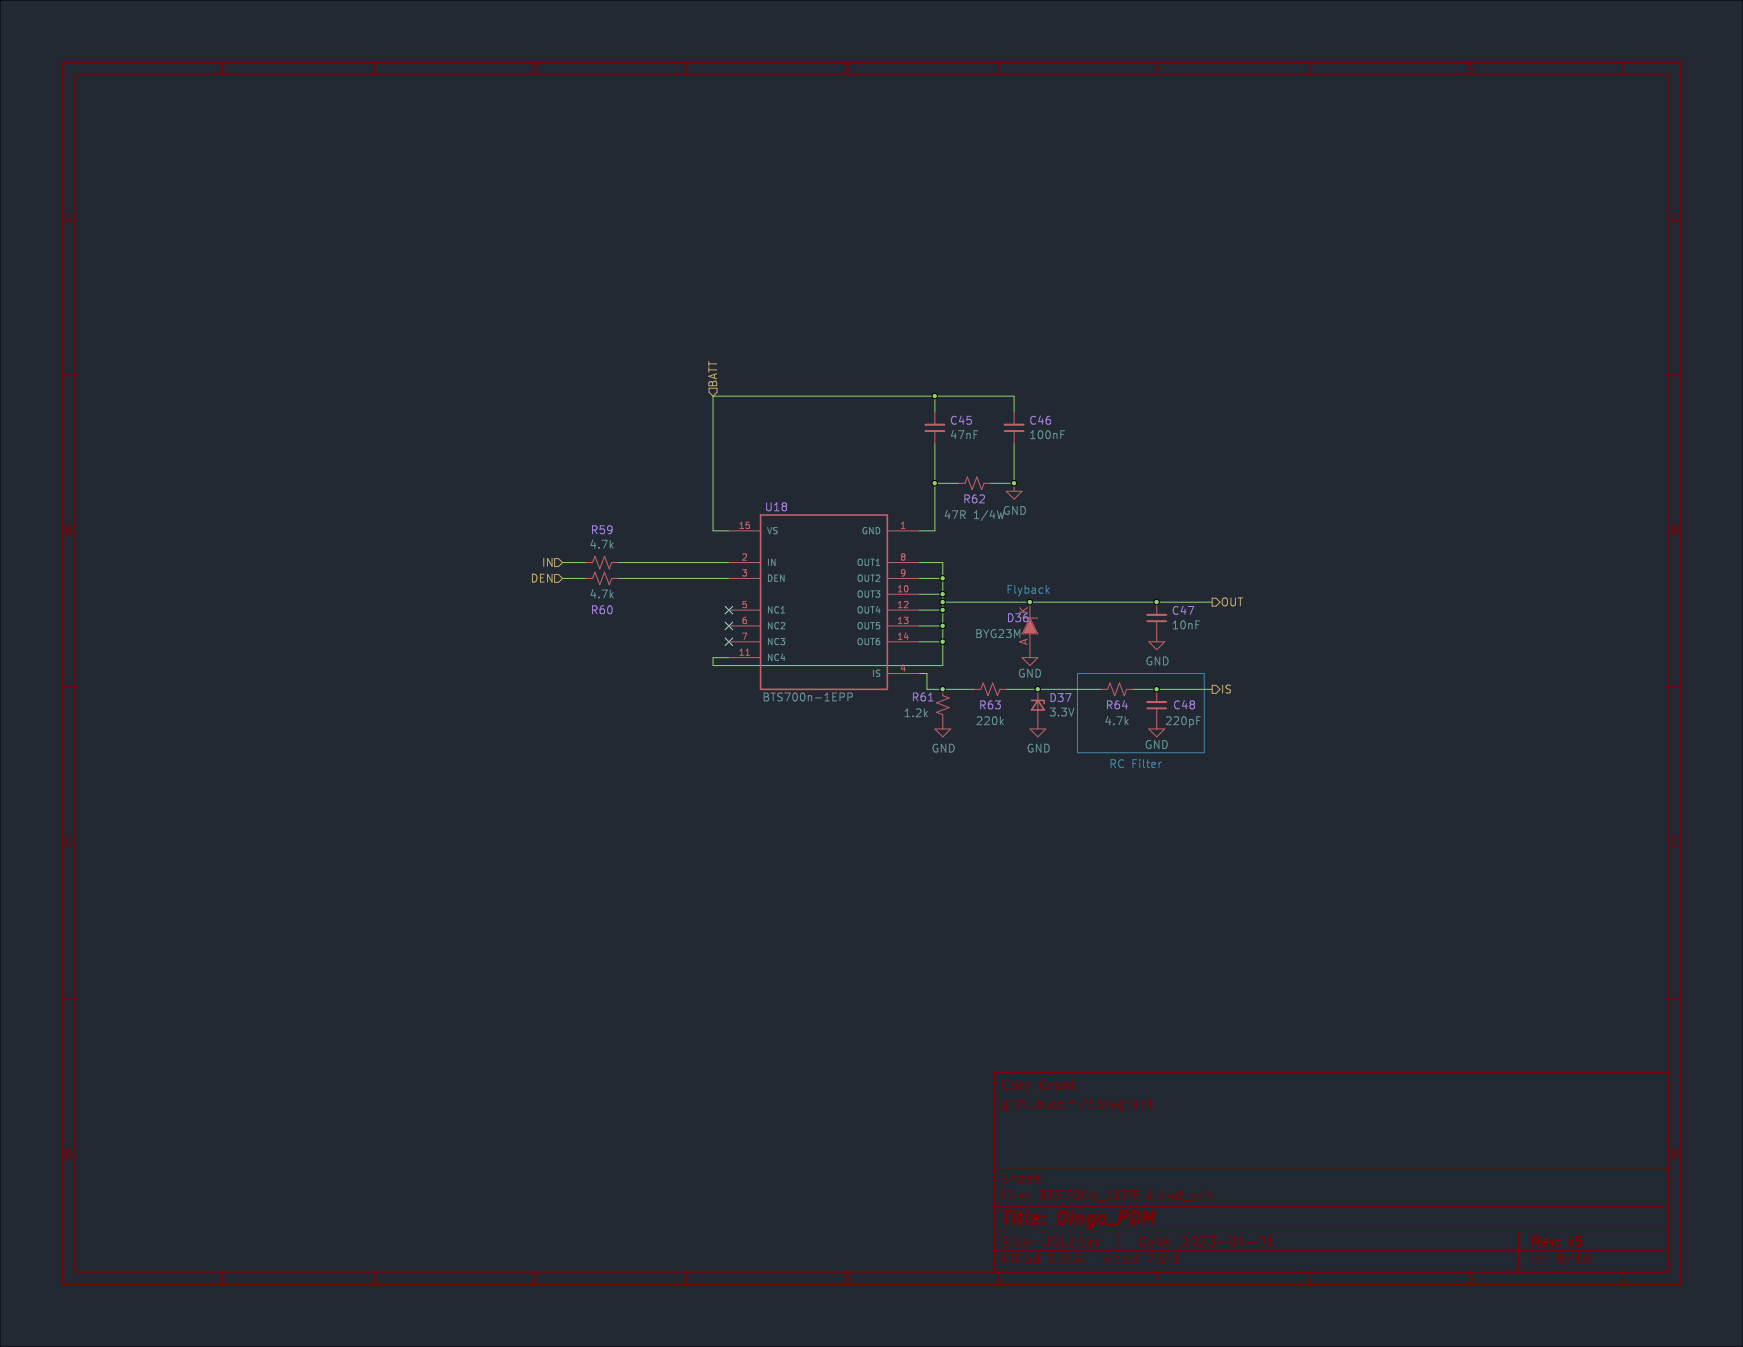
[picture p241: page 8]

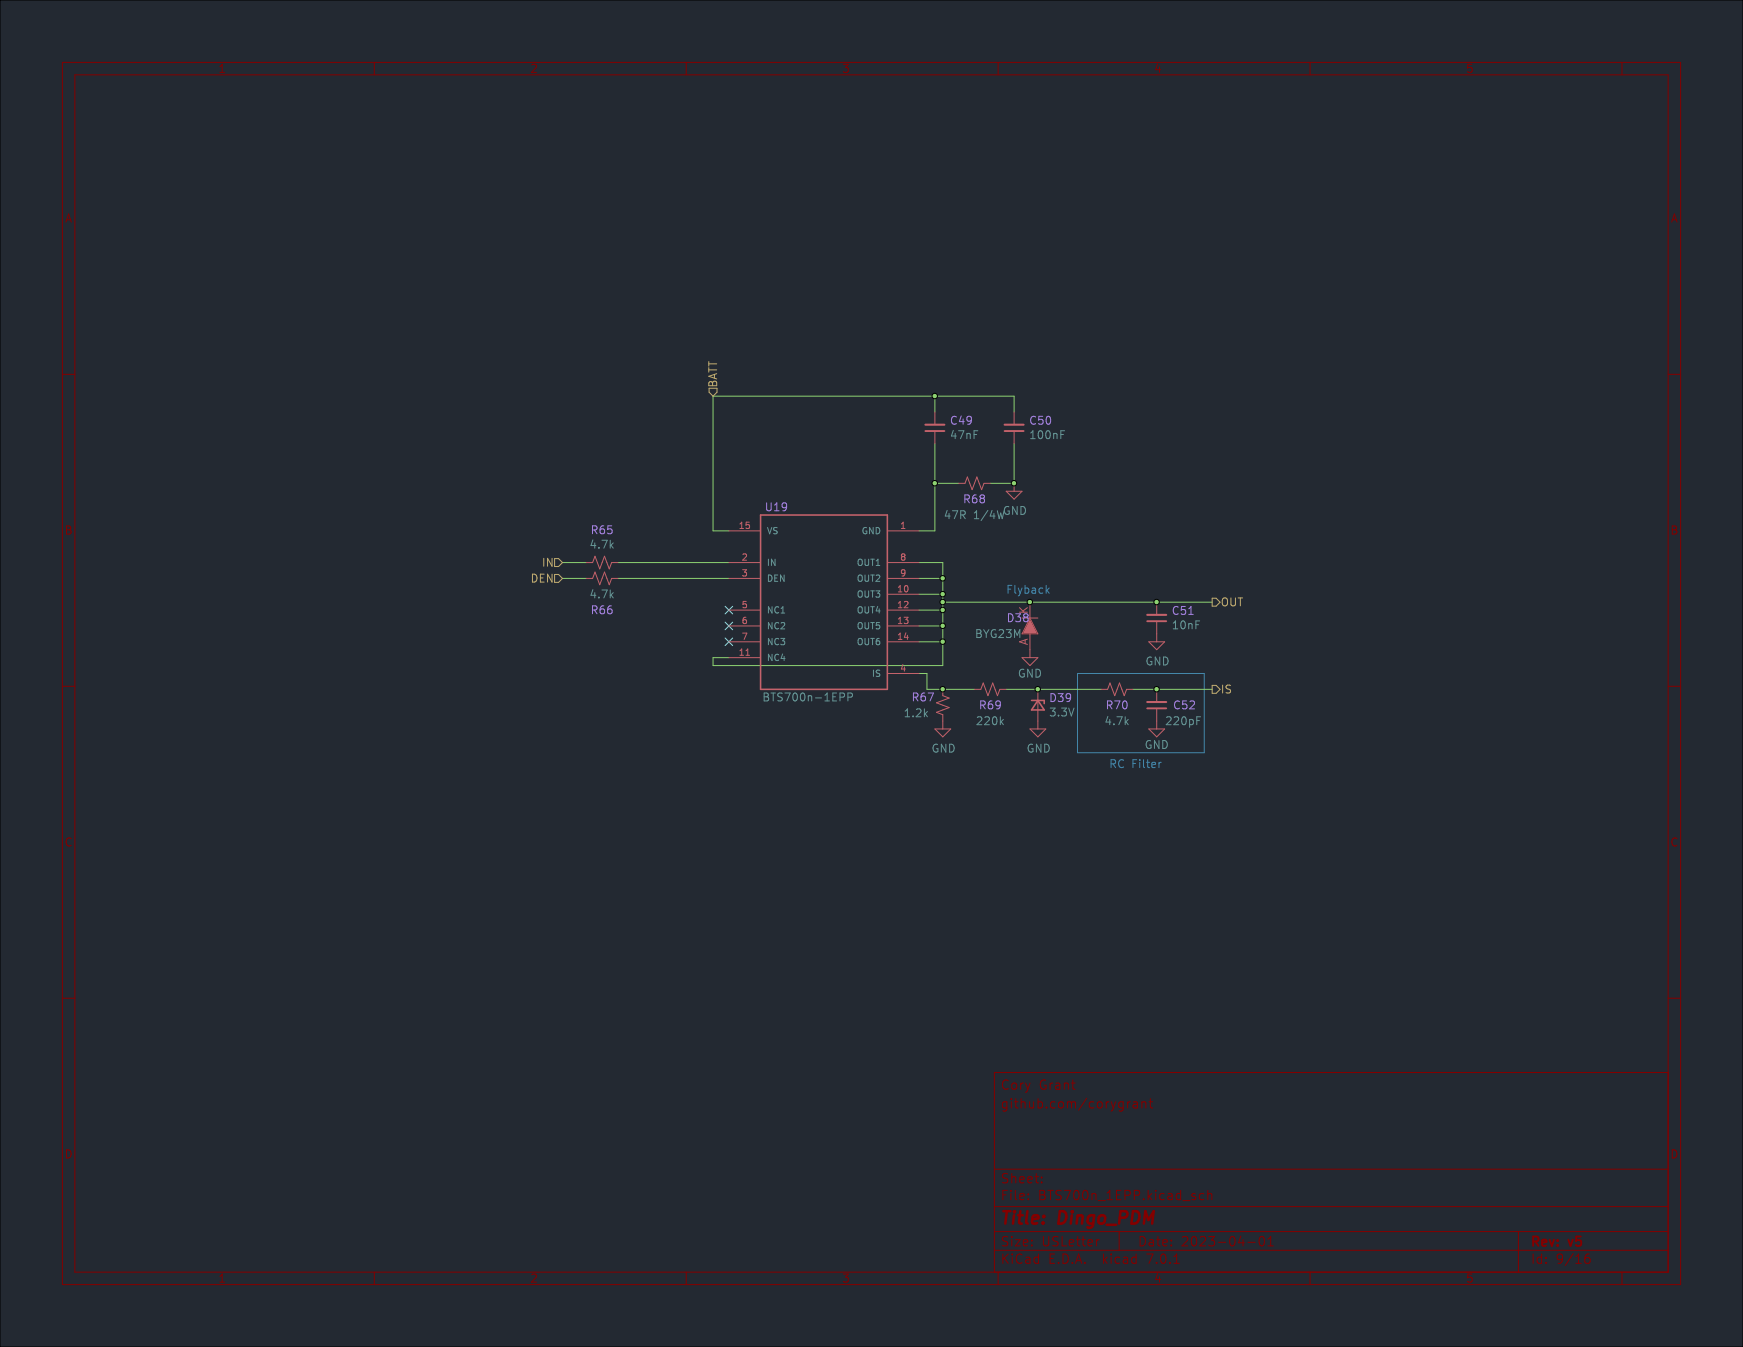
[picture p242: page 9]

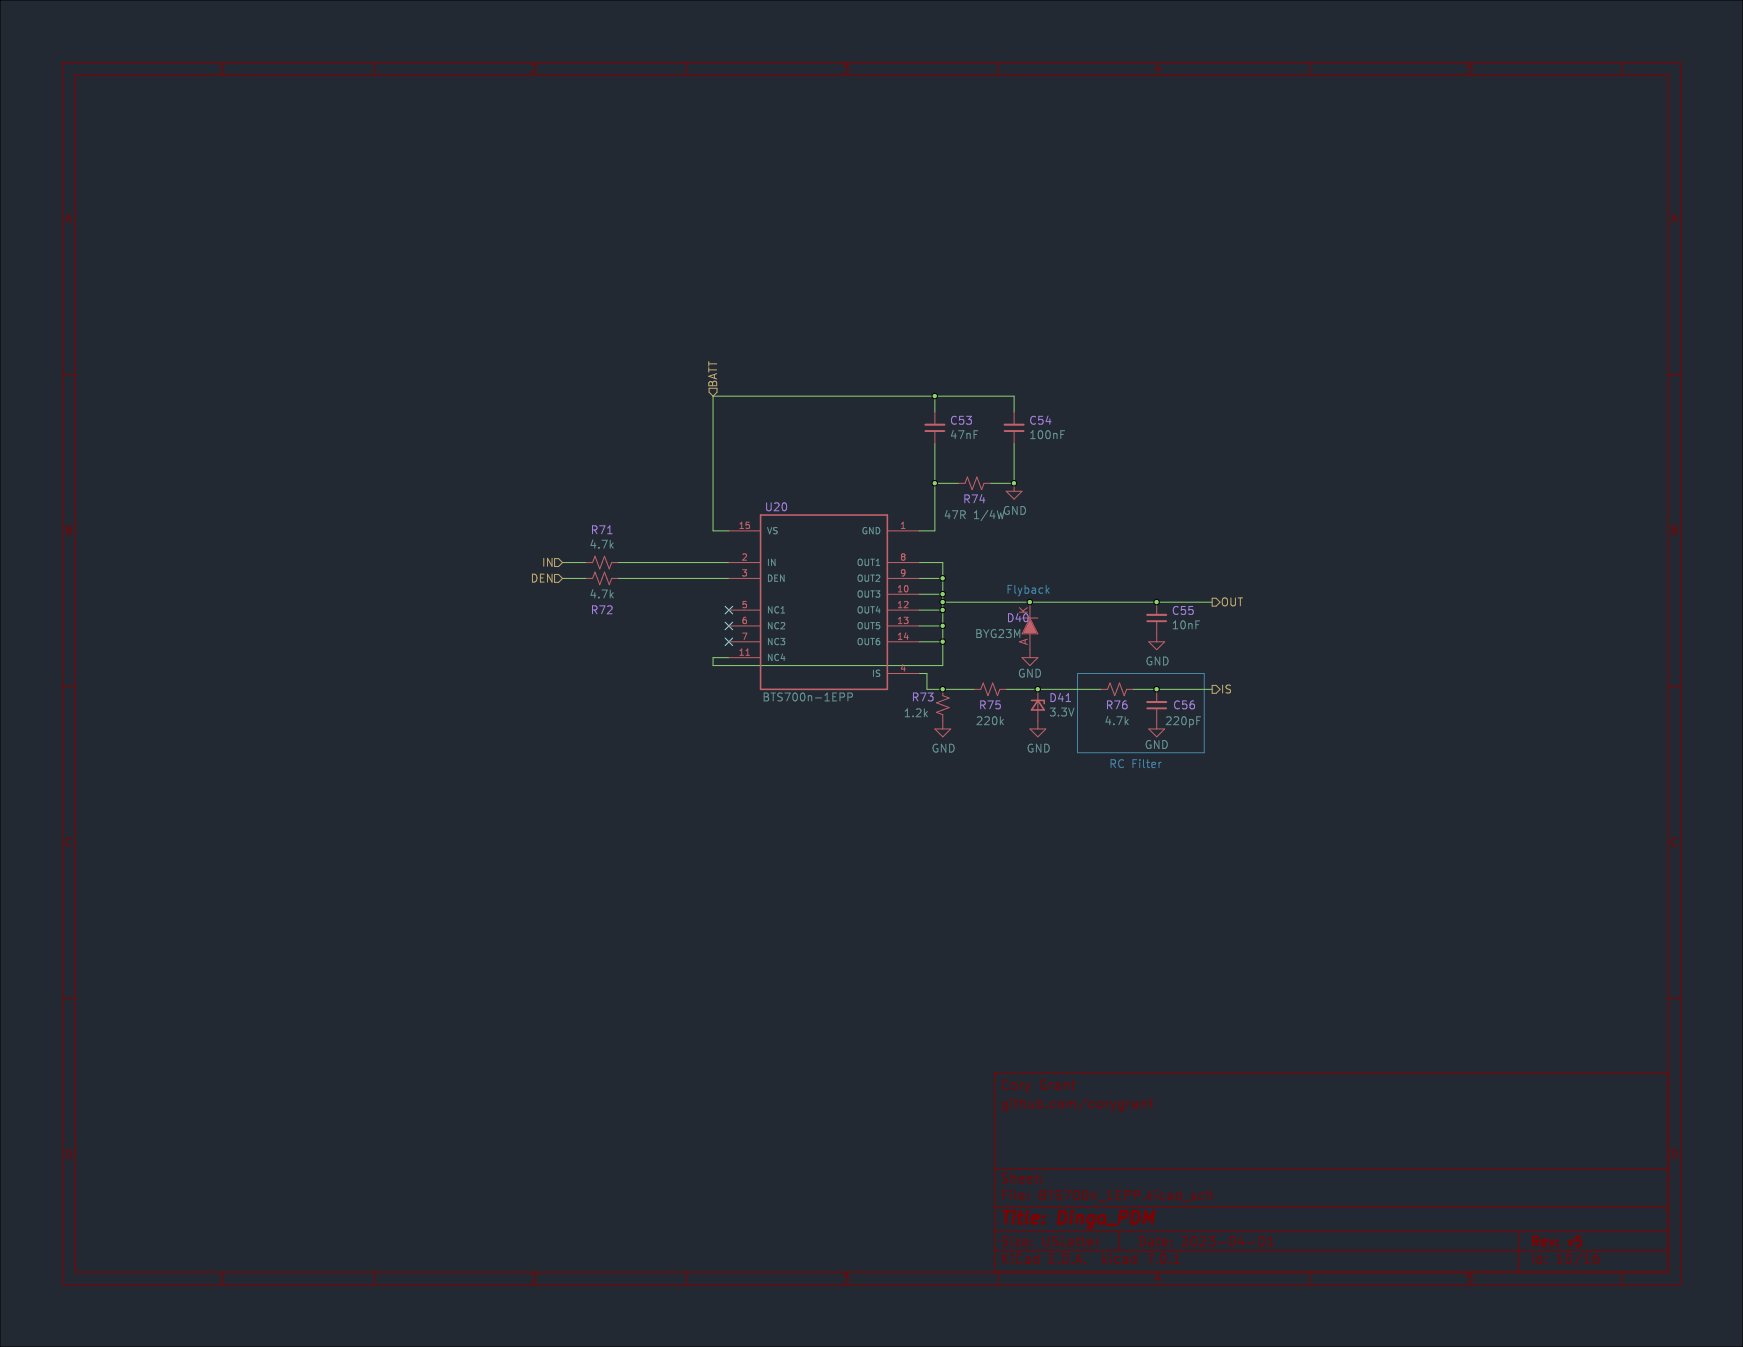
[picture p243: page 10]

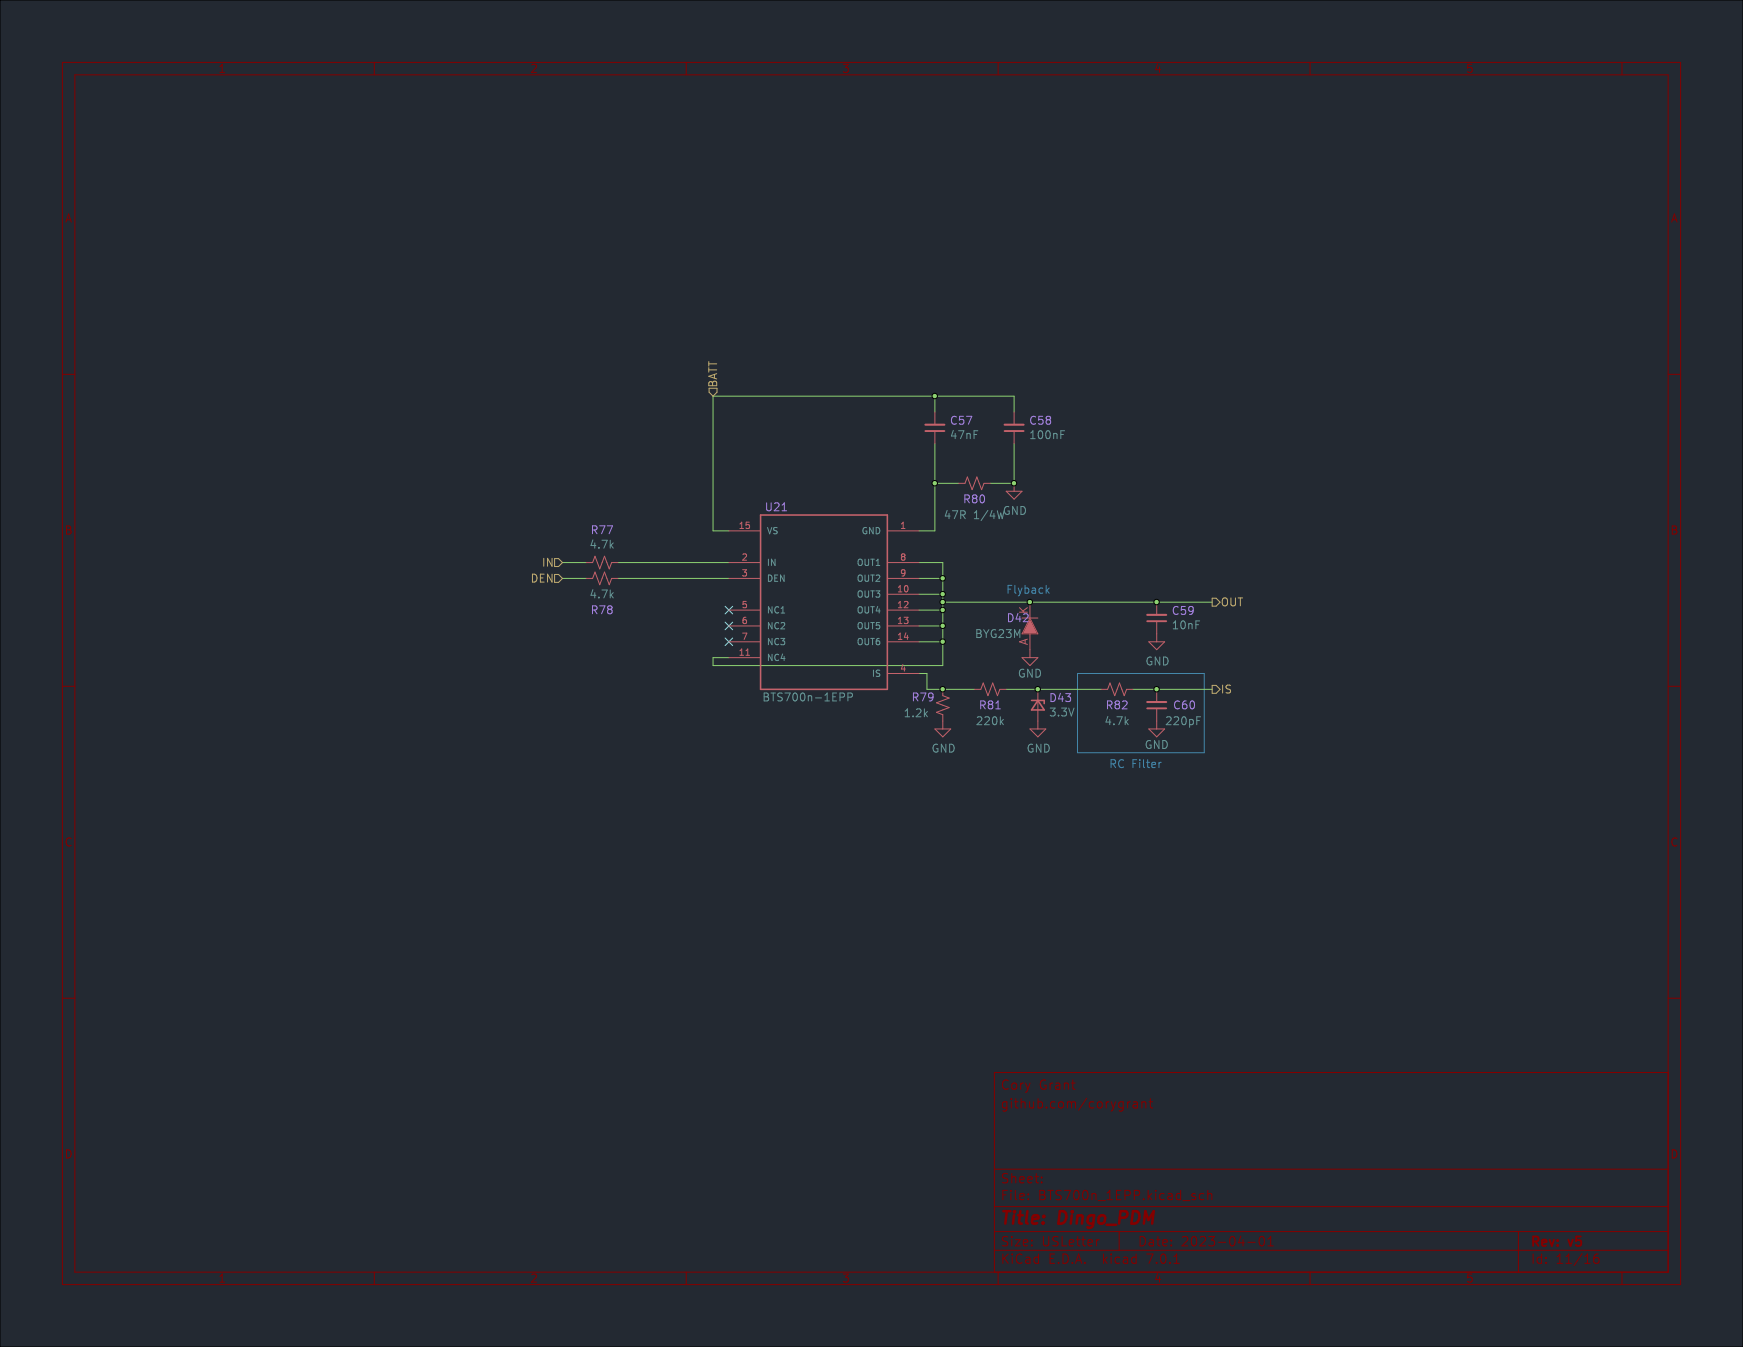
[picture p244: page 11]

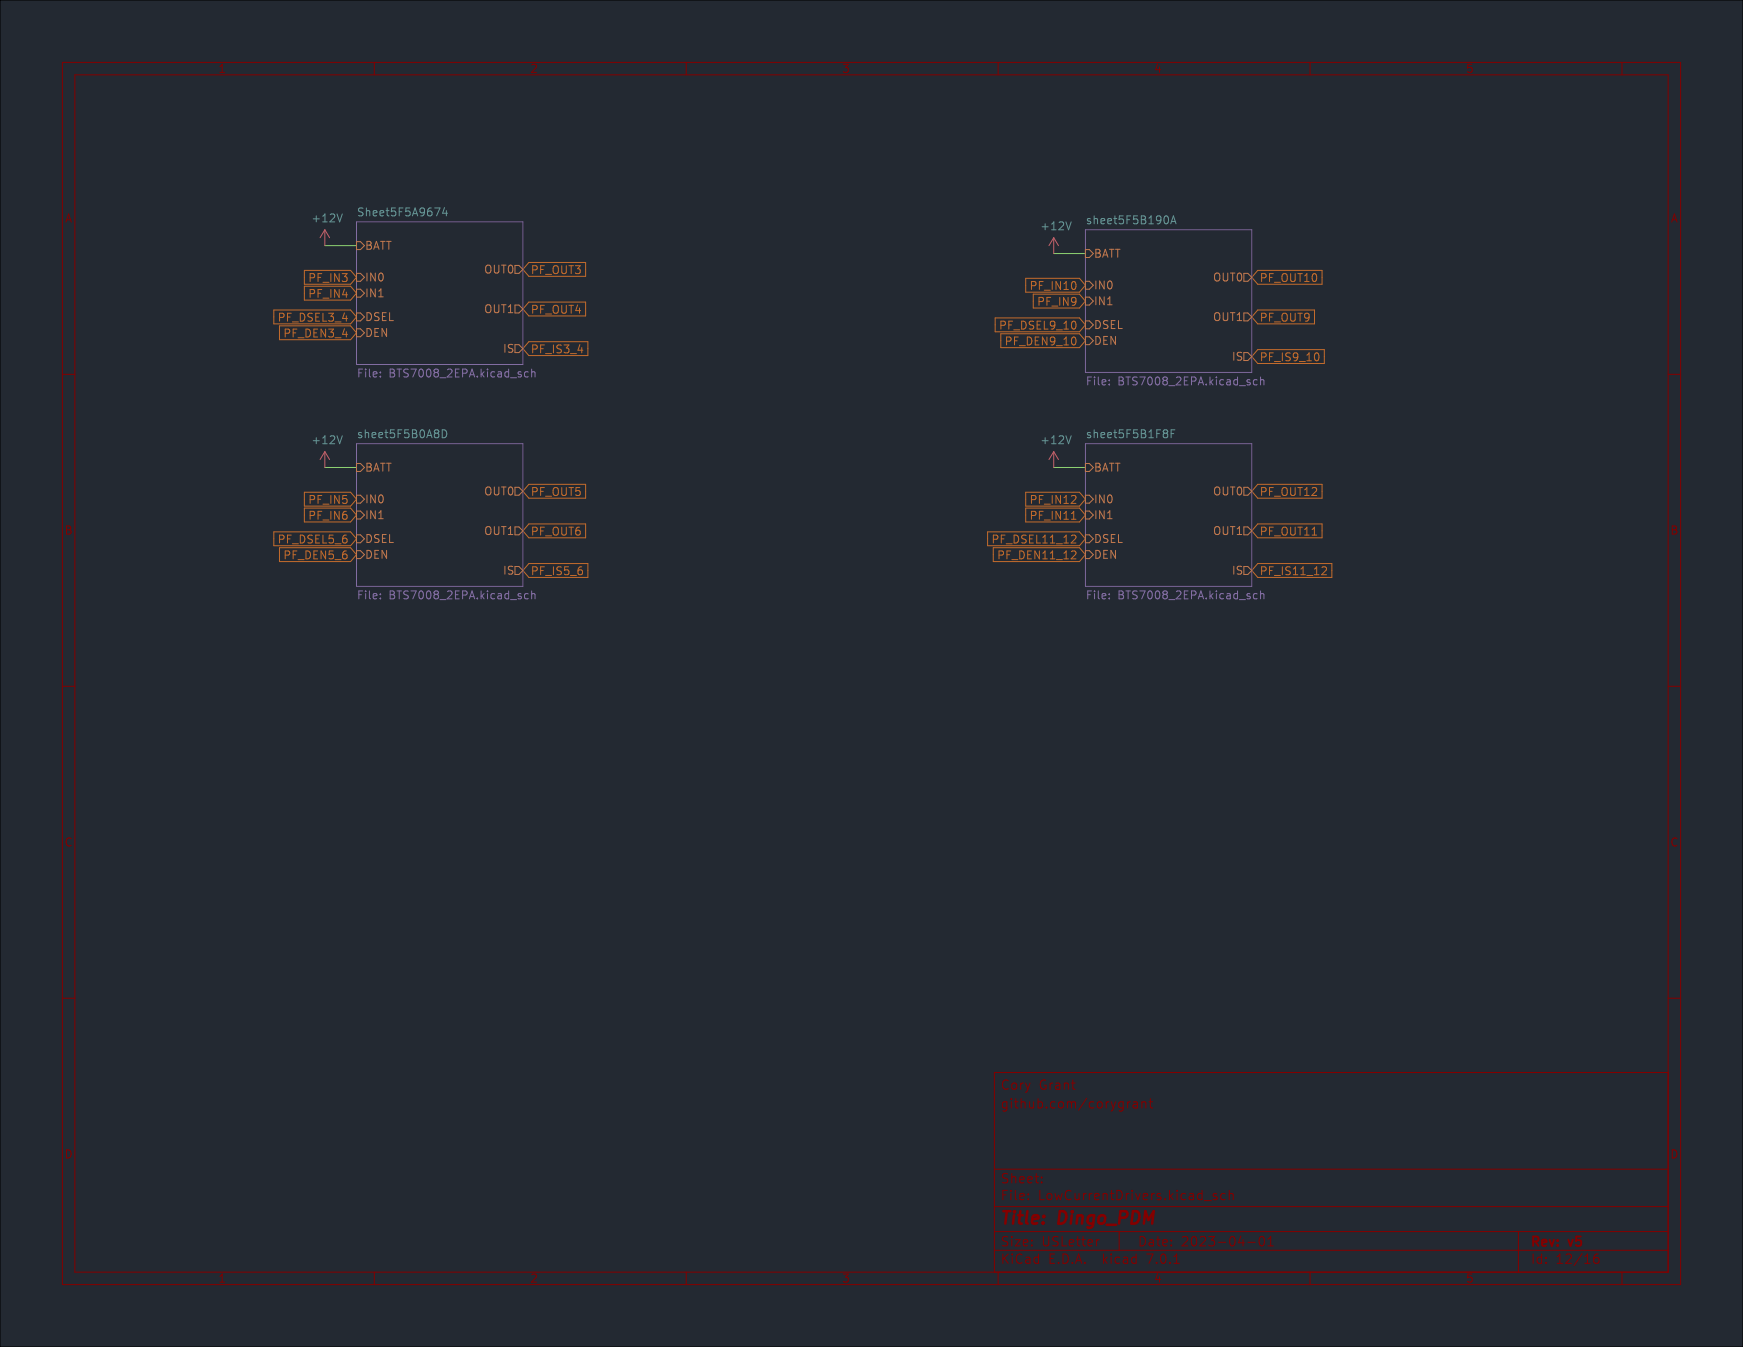
[picture p245: page 12]

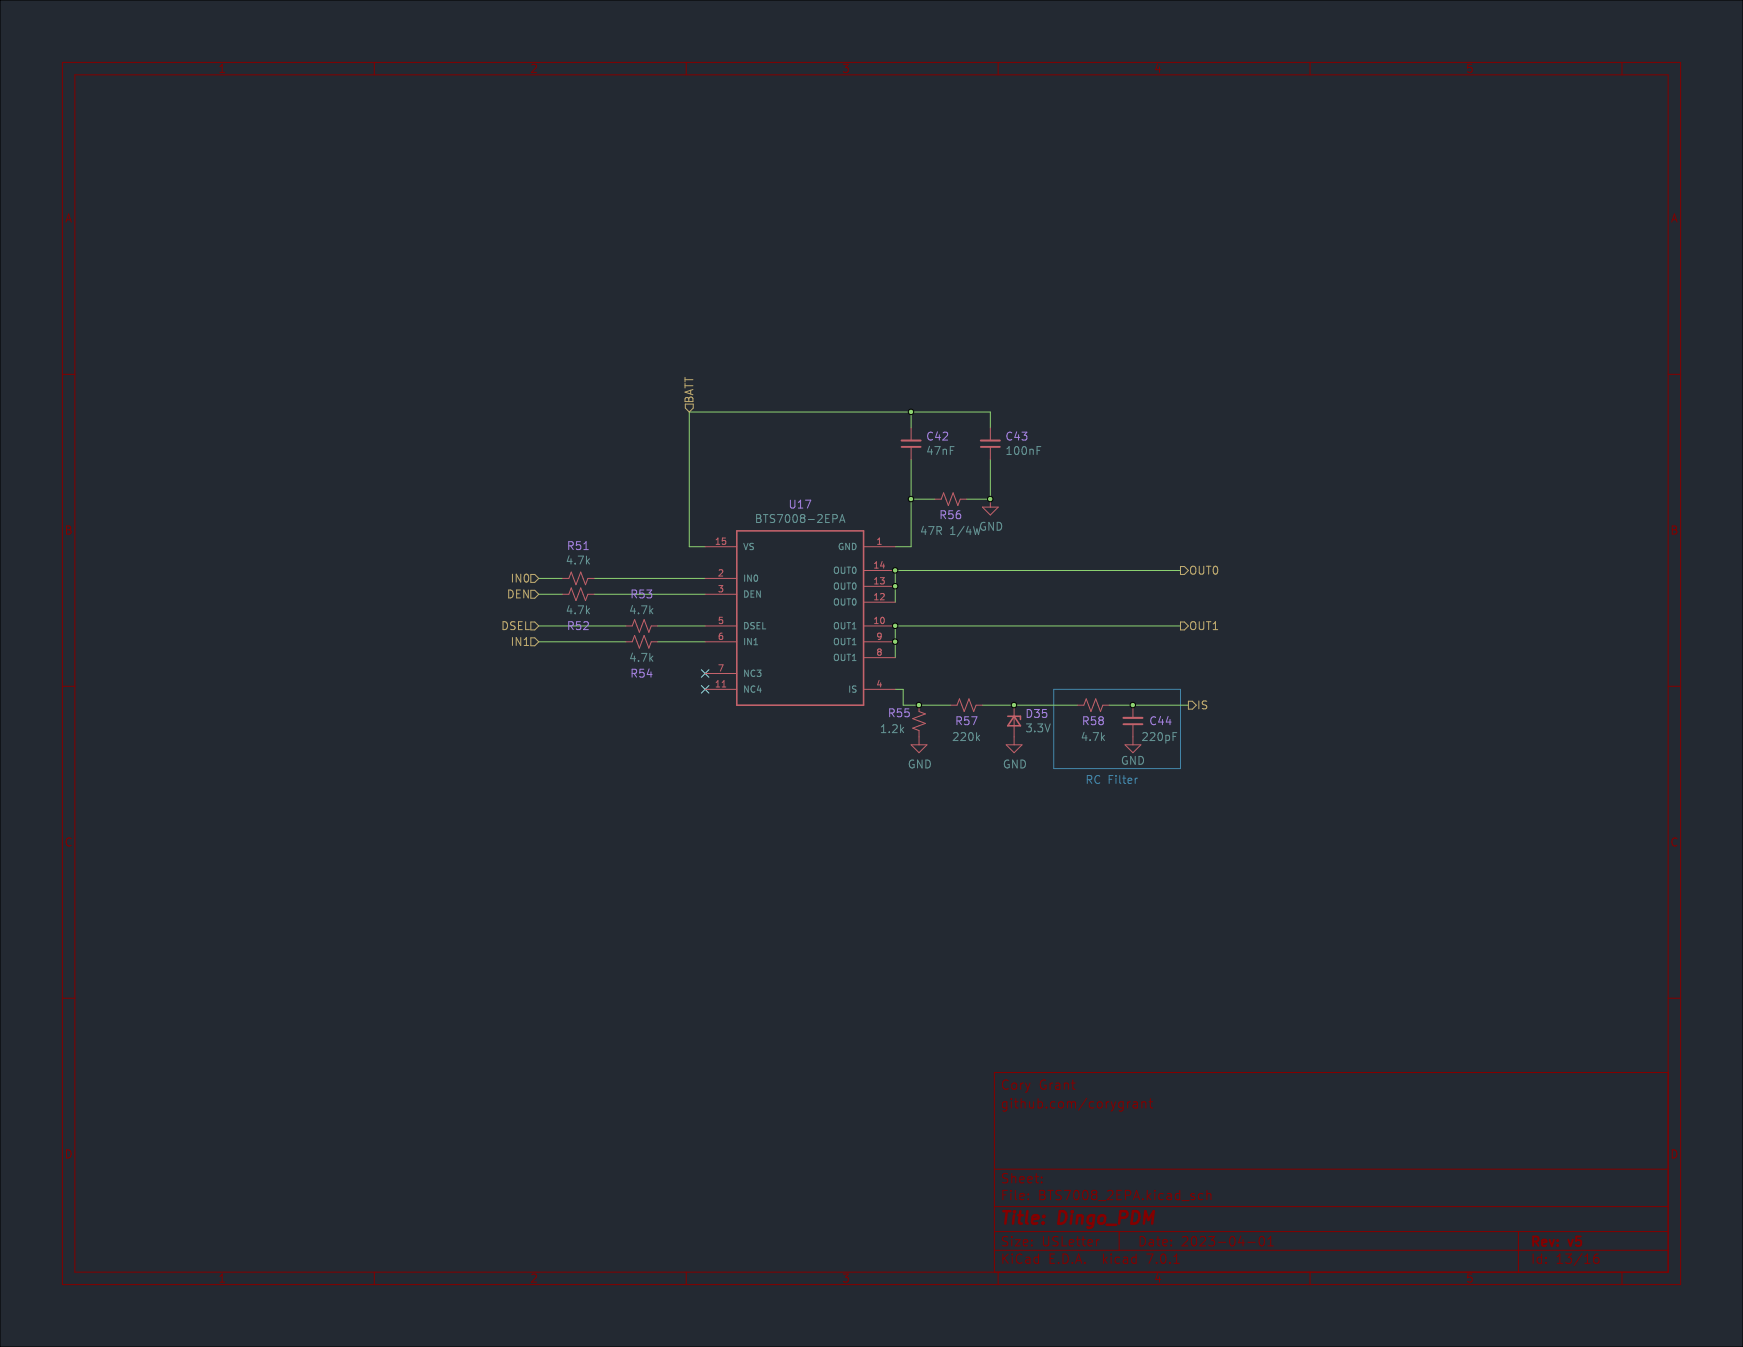
[picture p246: page 13]

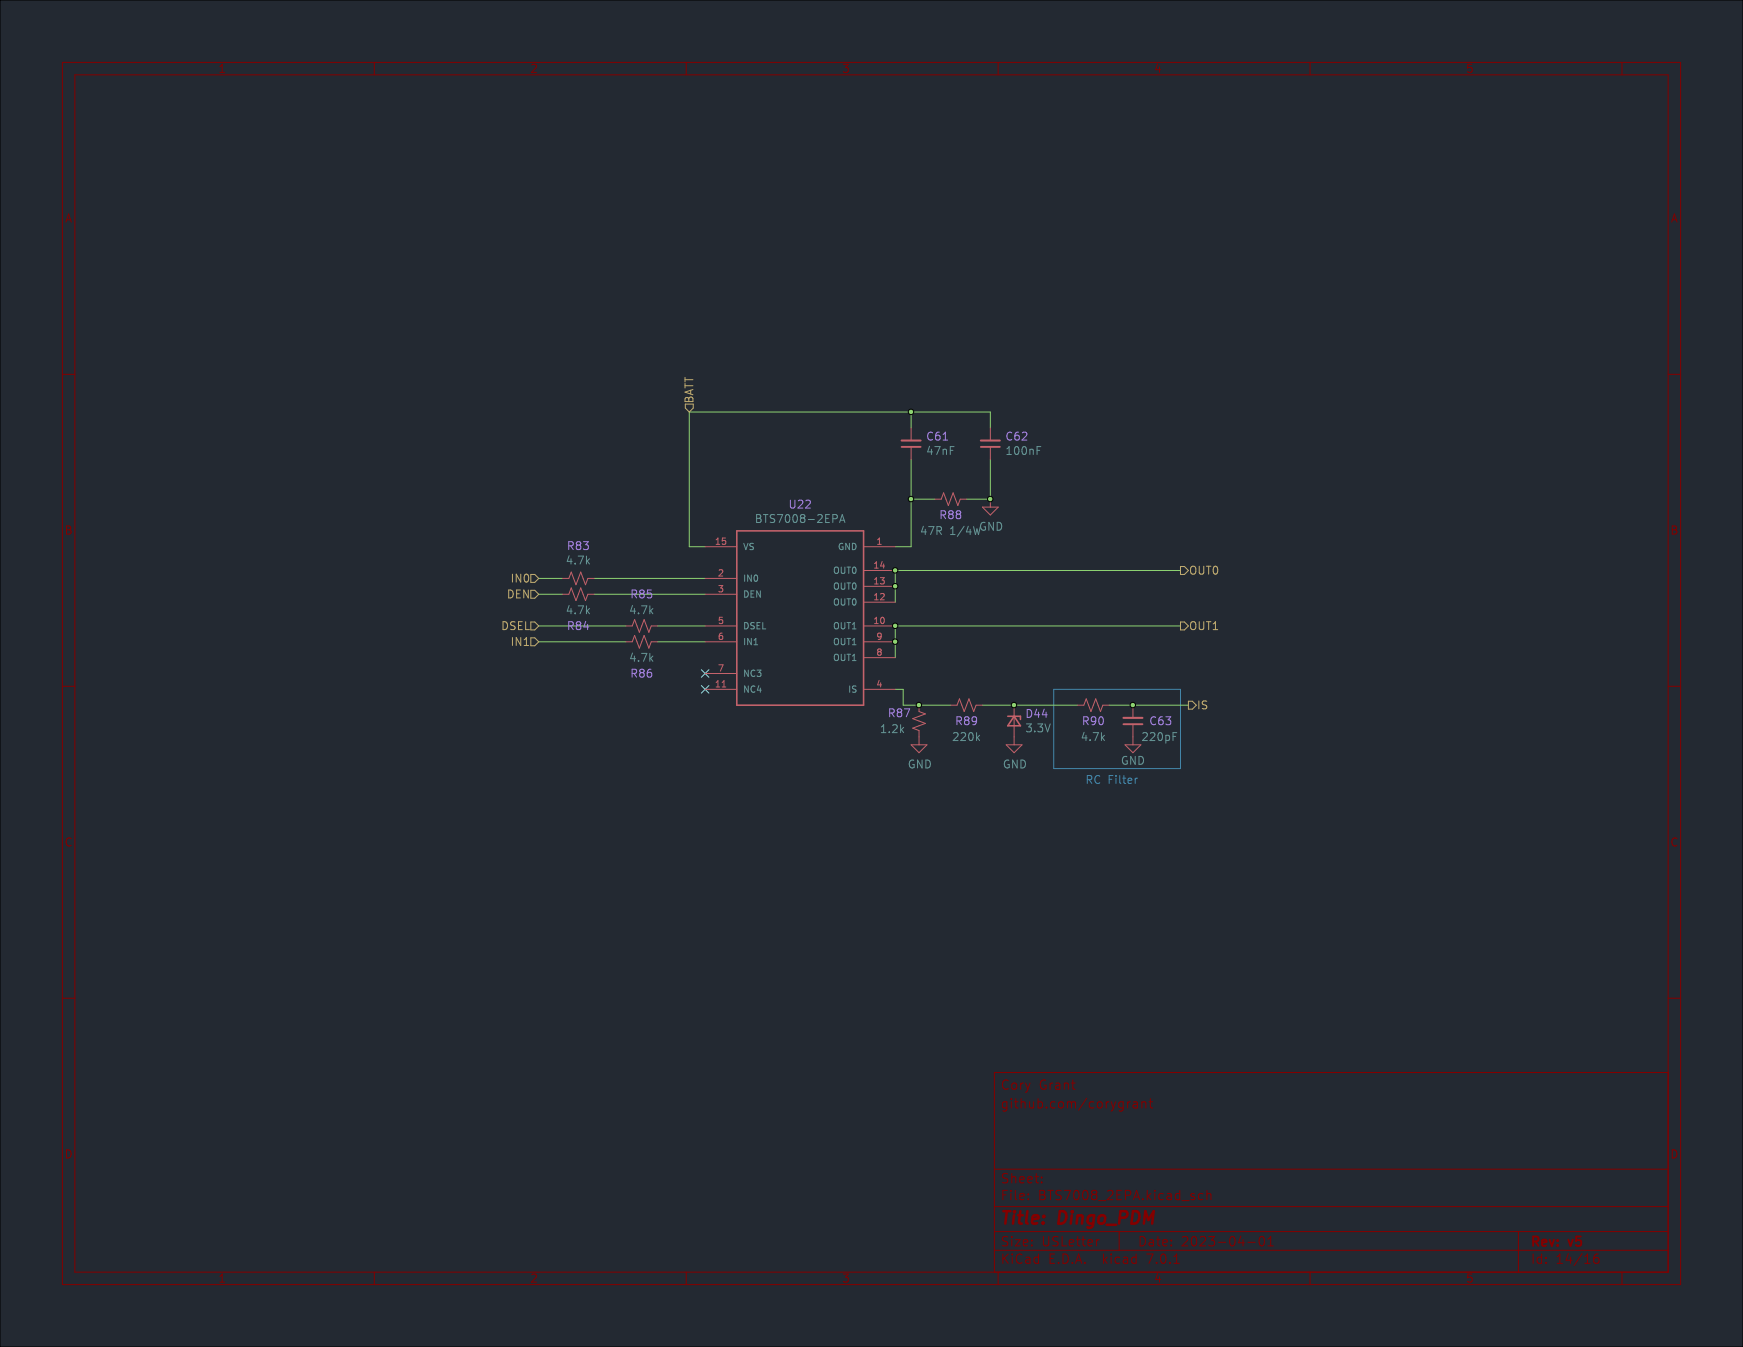
[picture p247: page 14]

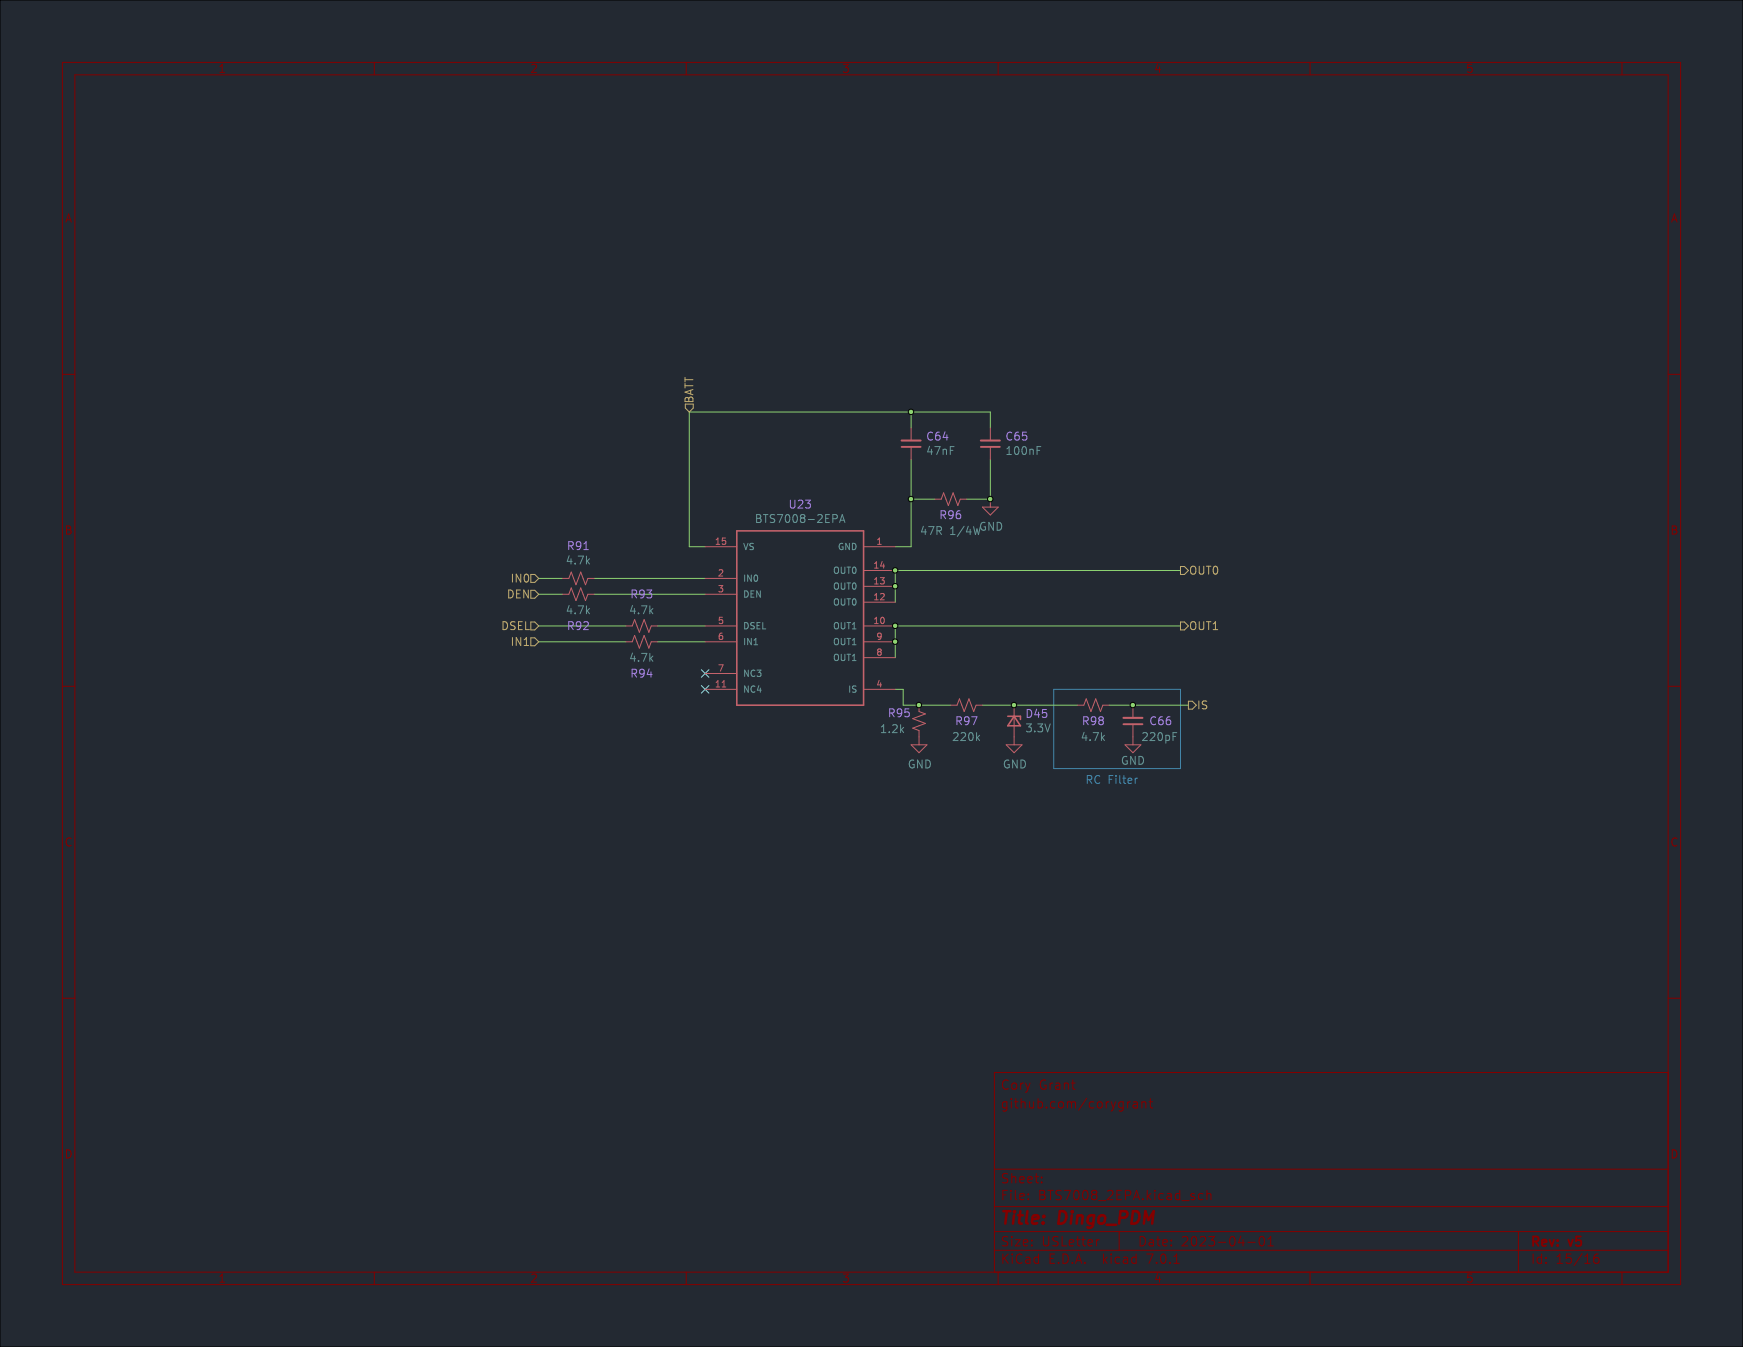
[picture p248: page 15]

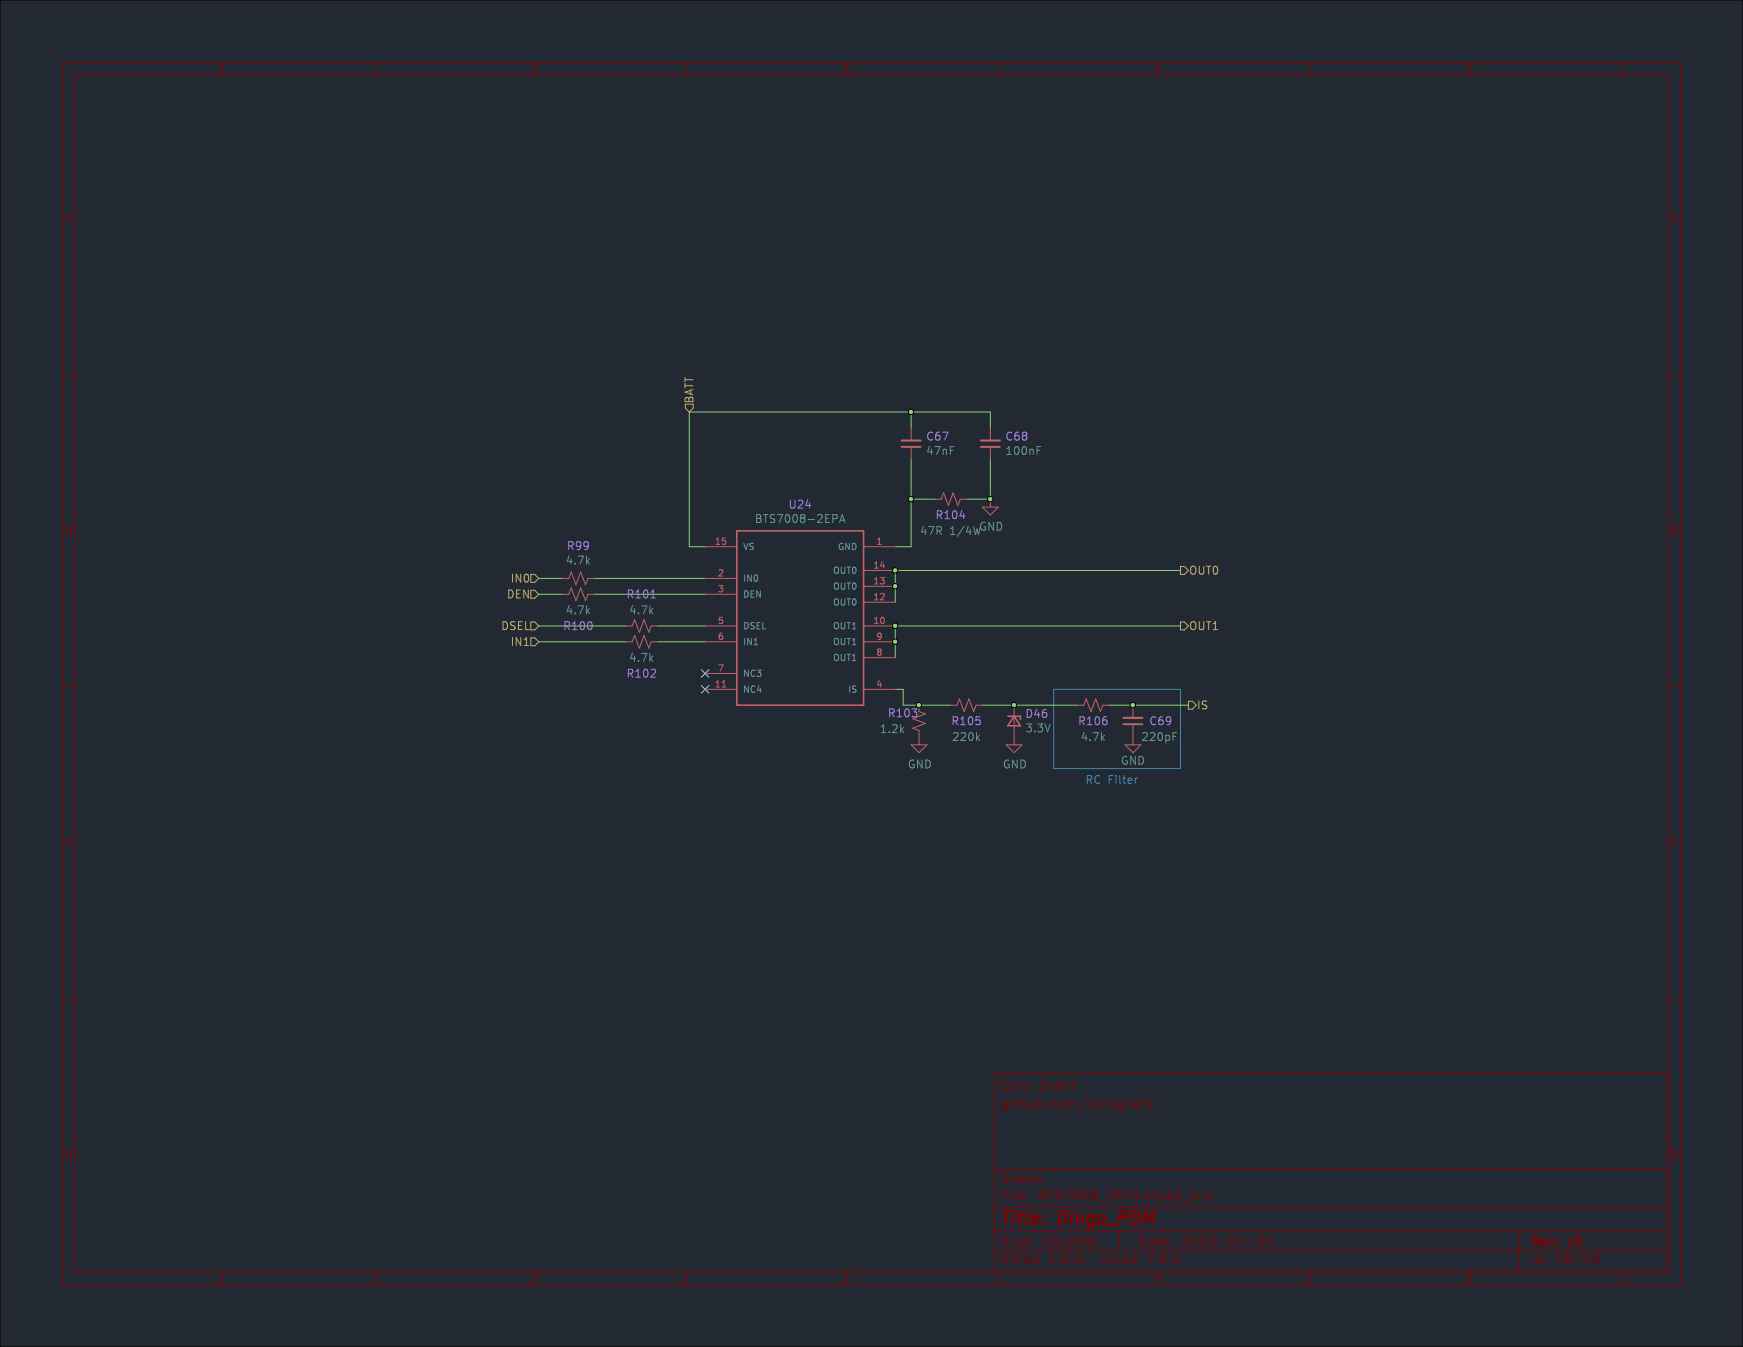
[picture p249: page 16]
