corygrant/dingoPDM/Export/V4/DingoPDM_HW_V4.pdf

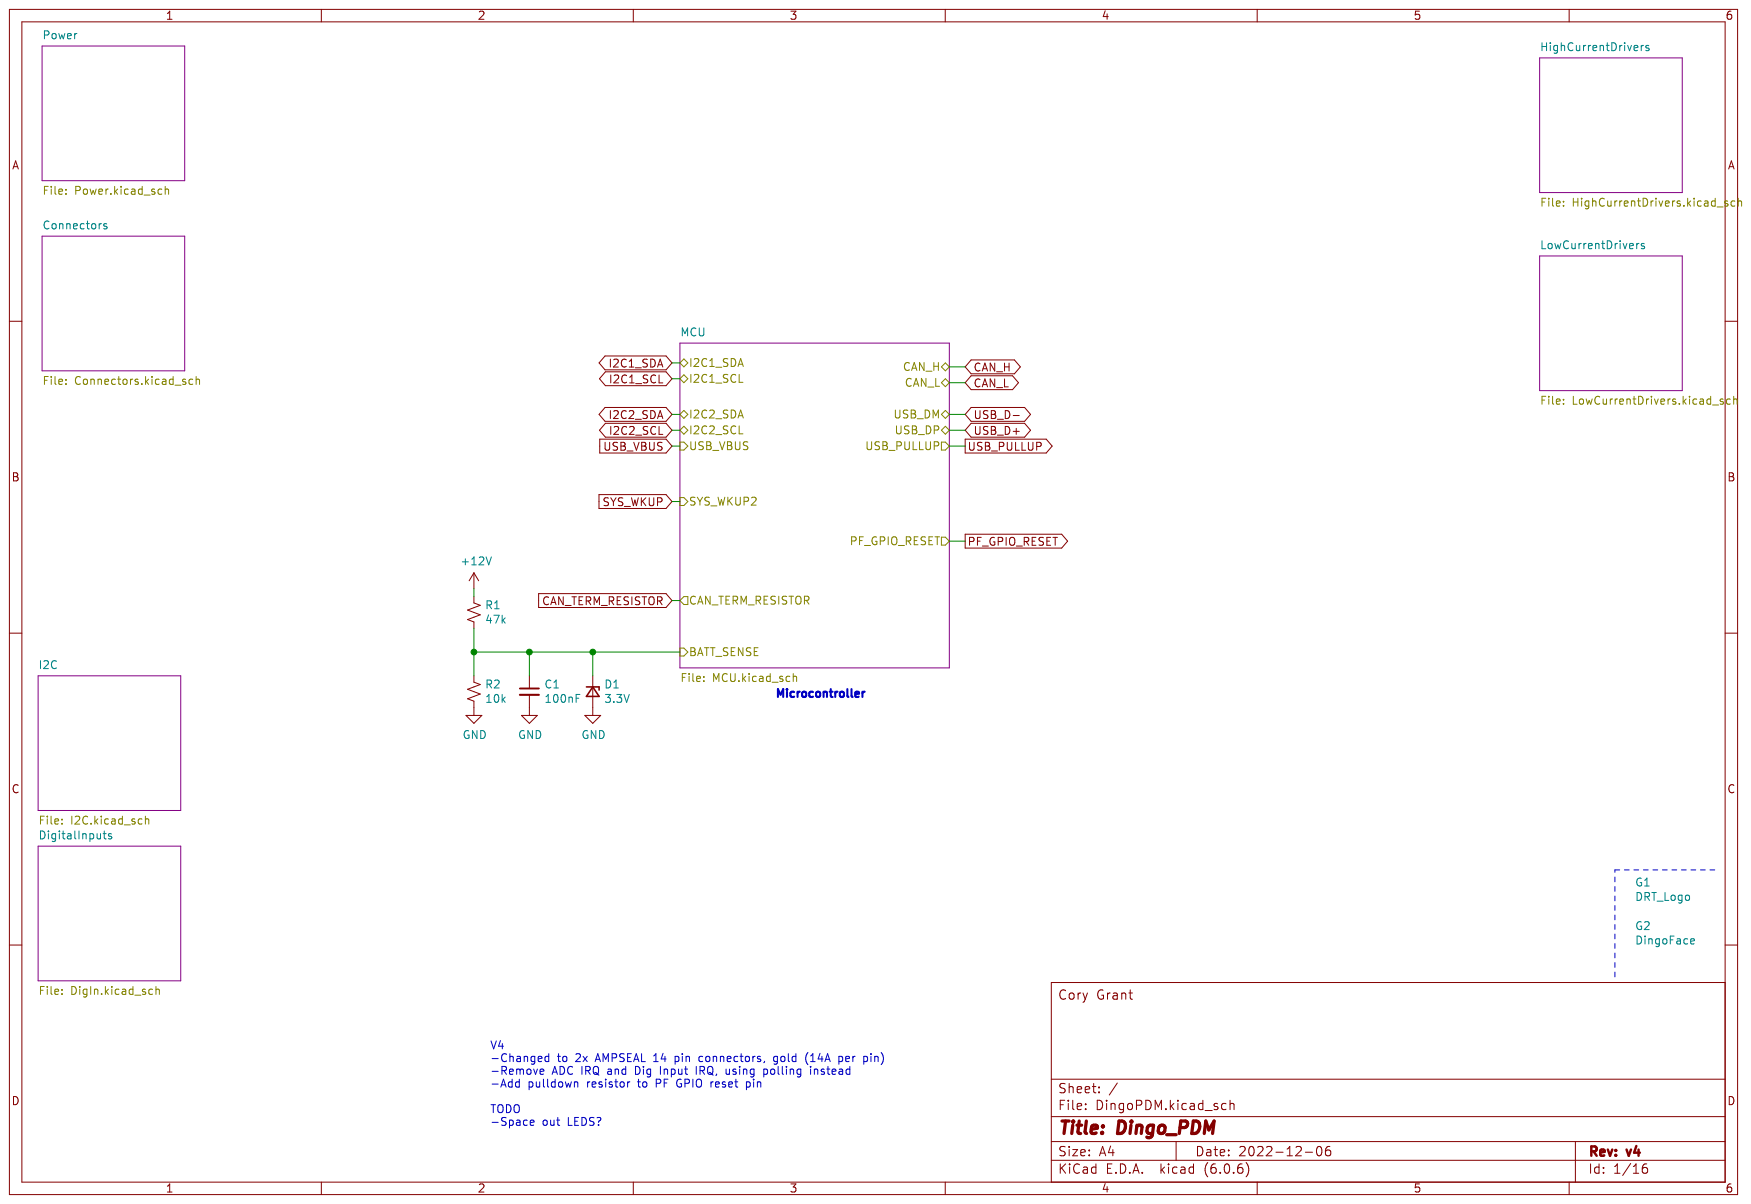
[picture p250: page 1]
